tourajghaffari/tigerfid/protel-files/transceiver/trx-rev19/Feb102009 ECO.pdf

### Change Order Report For Project TRX-101R17.PrjPcb And TRX-101R17.PrjPcb

Action | Object | Change Document | Status

Remove Pins From Nets
Remove C54-1 from GND_SIGNAL | In | TestCase1.PcbDoc
Remove C55-1 from GND_SIGNAL | In | TestCase1.PcbDoc
Remove R5-2 from +5V | In | TestCase1.PcbDoc
Remove R28-2 from +5V | In | TestCase1.PcbDoc
Remove R32-1 from GND_SIGNAL | In | TestCase1.PcbDoc
Remove R44-2 from +5V | In | TestCase1.PcbDoc
Remove R45-2 from +5V | In | TestCase1.PcbDoc
Remove U10-1 from GND_SIGNAL | In | TestCase1.PcbDoc
Remove U10-4 from +5V | In | TestCase1.PcbDoc
Remove U10-8 from +5V | In | TestCase1.PcbDoc
Remove U11-2 from GND_SIGNAL | In | TestCase1.PcbDoc
Remove U11-5 from +5V | In | TestCase1.PcbDoc

Remove Nets
Remove NetR5_1 | From TestCase1.PcbDoc
Remove NetU3_4 | From TestCase1.PcbDoc
Remove NetU10_6 | From TestCase1.PcbDoc
Remove NetU11_4 | From TestCase1.PcbDoc

Remove Components
Remove C54 | From TestCase1.PcbDoc
Remove C55 | From TestCase1.PcbDoc
Remove R5 | From TestCase1.PcbDoc
Remove R28 | From TestCase1.PcbDoc
Remove R32 | From TestCase1.PcbDoc
Remove R44 | From TestCase1.PcbDoc
Remove R45 | From TestCase1.PcbDoc
Remove U10 | From TestCase1.PcbDoc
Remove U11 | From TestCase1.PcbDoc

Add Nets
Add | 916_RX_DATA | To TestCase1.PcbDoc

Add Component Classes
Add | PG03_Schematic Sheet1 | To TestCase1.PcbDoc

Add Rooms
Add | Room PG03_Schematic Sheet1 (Scope=I To TestCase1.PcbDoc
| nComponentClass('PG03_Schematic Sheet1')) TopLayer
Tuesday 10-Feb-10/2009 11:07:39 PM | Page 1 of 1
