tourajghaffari/tigerfid/protel-files/master-library/RFID GRAPHICS.jpg

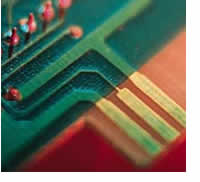
protel-files/master-library/RFID GRAPHICS.jpg
