tourajghaffari/tigerfid/protel-files/master-library/RFID Reader.jpg

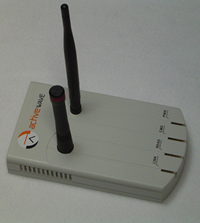
protel-files/master-library/RFID Reader.jpg
