tourajghaffari/tigerfid/software/smart-tracker/Source/Server/bin/Release/Distribute/Layout/Gray Manatee1 North, South, and West Elevation-Model.jpg

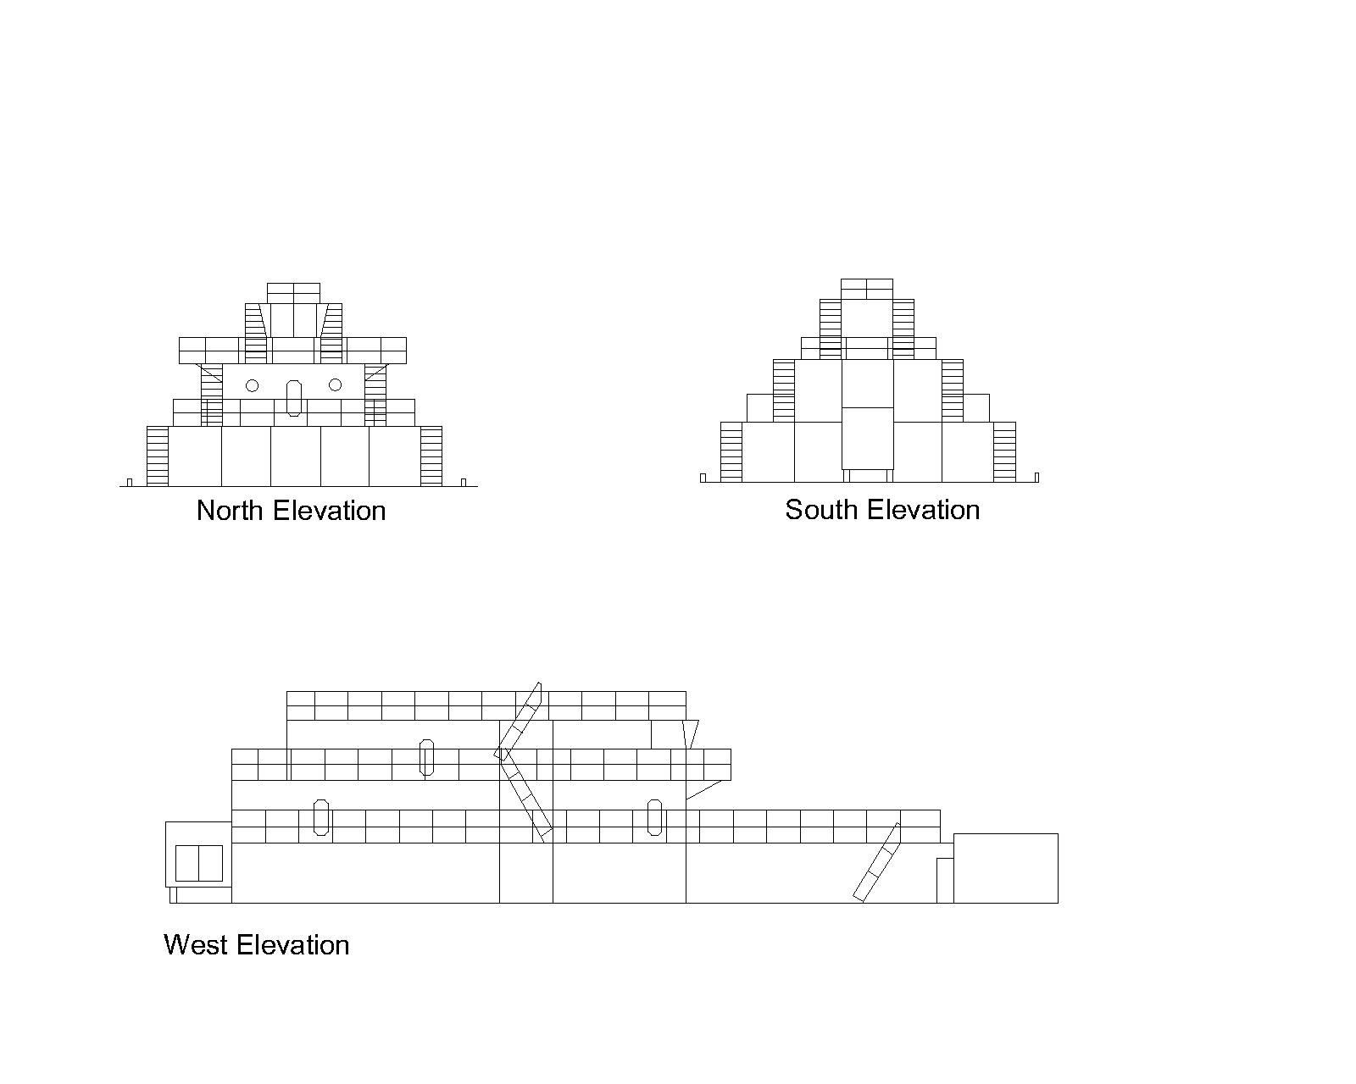
software/smart-tracker/Source/Server/bin/Release/Distribute/Layout/Gray Manatee1 North, South, and West Elevation-Model.jpg
