tourajghaffari/tigerfid/software/smart-tracker/Source/Server/bin/Release/Distribute/Layout/Gray Manatee east elevation-Model.jpg

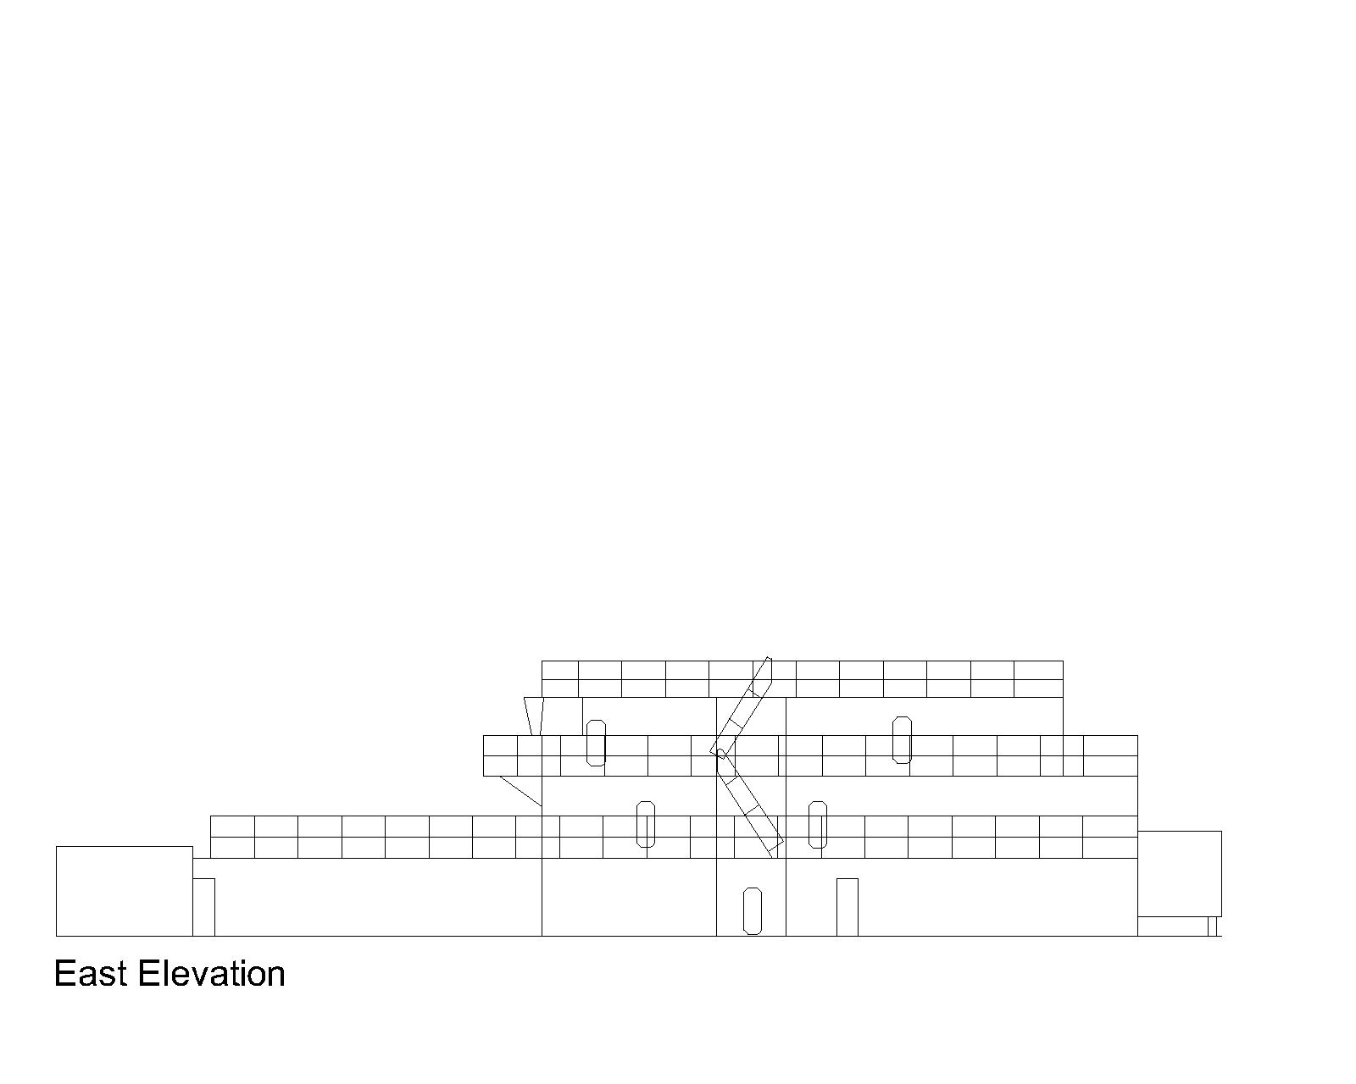
software/smart-tracker/Source/Server/bin/Release/Distribute/Layout/Gray Manatee east elevation-Model.jpg
