tourajghaffari/tigerfid/software/smart-tracker/Source/Server/bin/Release/Distribute/Layout/Gray Manatee ground floor and second-Model.jpg

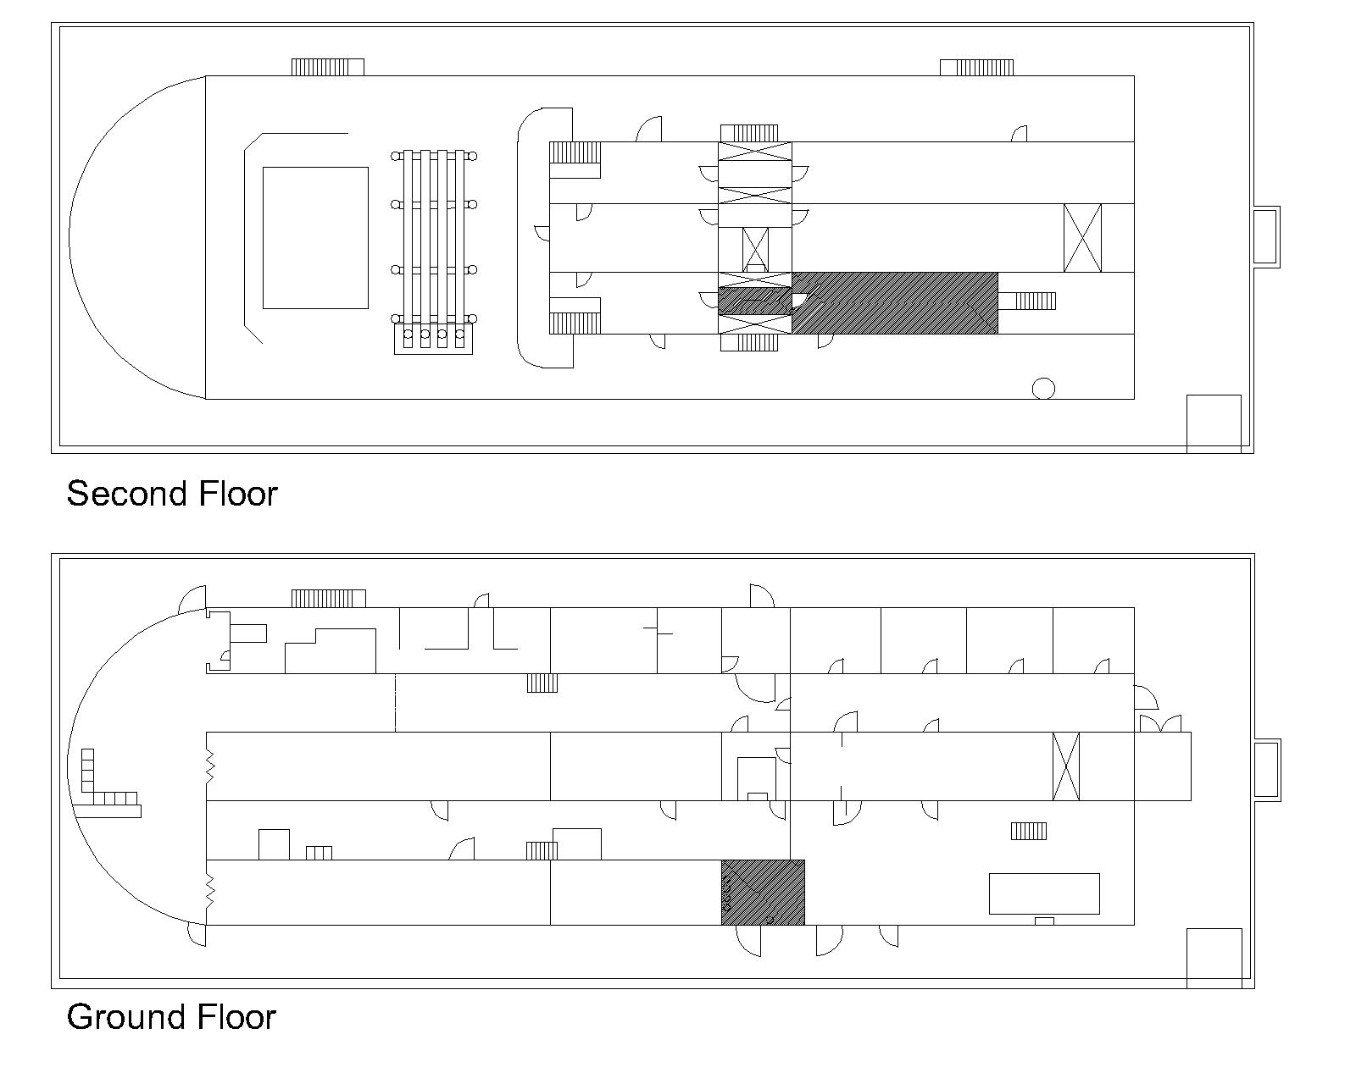
software/smart-tracker/Source/Server/bin/Release/Distribute/Layout/Gray Manatee ground floor and second-Model.jpg
