tourajghaffari/tigerfid/software/smart-tracker/Source/Server/bin/Release/Distribute/Layout/Gray Manatee third floor and roof-Model.jpg

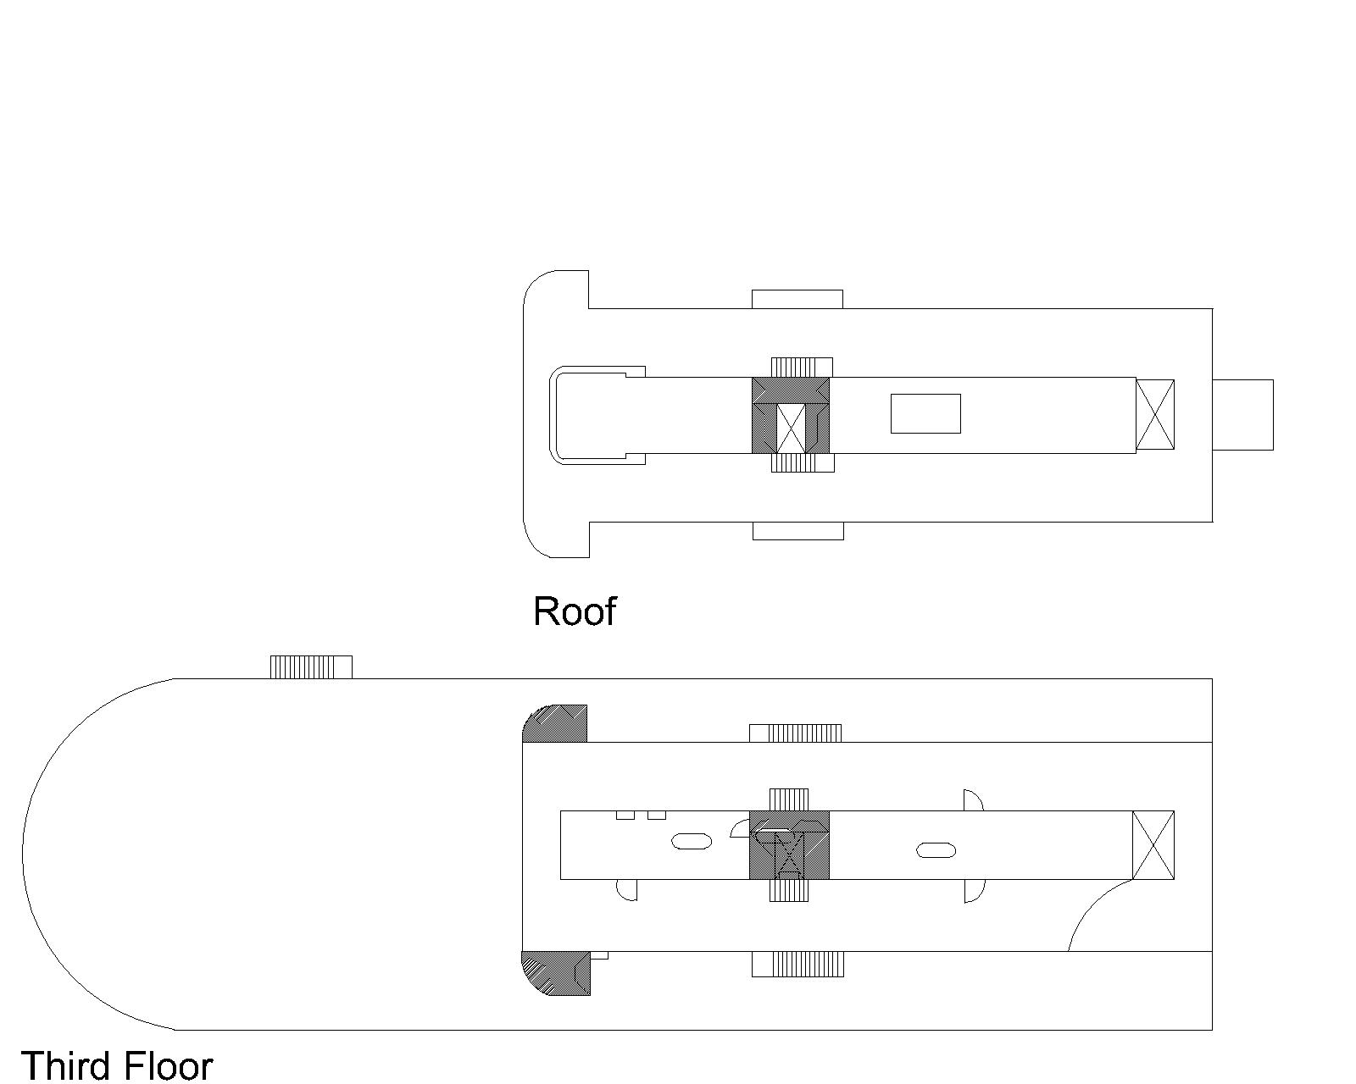
software/smart-tracker/Source/Server/bin/Release/Distribute/Layout/Gray Manatee third floor and roof-Model.jpg
