tourajghaffari/tigerfid/bom-files/bom-cost/TAG104 111705 REV 06A cost.xls

TAG-104
11/17/05 |  | LAST UPDATED |  |  |  |  |  |  |  |  | Mini Tag
 |  |  |  |  |  |  |  |  |  |  | REV 06
Item # | Part Stat | Option No. | Part Reference | Qty. | Unit Price | Extended Cost | Labor Cost | Total Price | Value | Part Size | Description | Manufacturer | Manufacturer P/N | Dist. | Distributor P/N
1 | BASIC |  | C6,C7 | 2 |  |  |  |  | 100 pF | 0603 | CAP 100PF 50V CERAMIC | Panasonic - ECG | ECJ-1VC1H101J | Digi-Key | PCC101ACVTR-ND
2 | BASIC |  | C12,C13 | 2 |  |  |  |  | 33pF +/- 1% | 0603 | CAP 33pF +/- 1% | MURATA | GRM1885C1H330FA01D | TTI/Mouser | GRM1885C1H330FA01D
 |  |  |  |  |  |  |  |  | or |  | CAP 33pF +/- 1% | Kemet | C0603C330F5GACTU | TTI/Mouser | C0603C330F5GACTU
3 | BASIC |  | C8,C9,C10,C11 | 4 |  |  |  |  | 1000 pF | 0603 | CAP 1000PF 50V CERAMIC NP0 | Panasonic - ECG | ECJ-1VC1H102J | Digi-Key | PCC2151TR-ND
4 | BASIC |  | C15,C17,C18,C24 | 4 |  |  |  |  | 0.1 uF | 0603 | CAP .10UF 16V CERAMIC X7R | Phycomp USA Inc (VA) | 06032R104K7B20D | Digi-Key | 311-1088-1-ND
 |  |  |  |  |  |  |  |  |  |  | CAP .10UF 16V CERAMIC X7R | AVX CORP / KYOCERA | 0603YC104KAT2A
 |  |  |  |  |  |  |  |  |  |  | CAP .10UF 16V CERAMIC X7R | TDK CORP | CC0603CX7R104K
 |  |  |  |  |  |  |  |  |  |  | CAP .10UF 16V CERAMIC X7R | MURATA | GRM39X7R104K016AD | Digi-Key | 490-1532-2-ND
 |  |  |  |  |  |  |  |  |  |  | CAP .10UF 16V CERAMIC X7R | NIC COMPONENTS | NMC0603X7R104K16TRM
 |  |  |  |  |  |  |  |  |  |  | CAP .10UF 16V CERAMIC X7R | NIC COMPONENTS | NMC0603X7R104K16TRP
5 | BASIC |  | C22,C23 | 0 |  |  |  |  | DNS
6 | BASIC |  | C20 | 1 |  |  |  |  | 4.7uF | A (EIA) 3216-18 | CAPACITOR TANT 4.7UF 16V 10% | Kemet | T491A475K016AS | Digi-Key | 399-1587-2-ND
7 | BASIC |  | C21 | 1 |  |  |  |  | 2.2pF +/- 0.1pF | 0603 | CAP 2.2pF +/- 0.1pF | MURATA | GRM1885C1H2R2CZ01D | Digi-Key | 490-1380-2-ND
8 | BASIC |  | C3,C25 | 2 |  |  |  |  | 1.8pF +/- 0.1pF | 0603 | CAP 1.8pF +/- 0.1pF | MURATA | GRM1885C1H1R8CZ01D | Digi-Key | 490-1378-2-ND
9 | BASIC |  | L3 | 1 |  |  |  |  | 0.18uH | 0603 | INDUCTOR MULTILAYER 0.18 UH | TDK Corporation | MLF1608DR18K | Digi-Key | 445-1006-1-ND
10 | BASIC |  | L6 | 1 |  |  |  |  | 0.33uH | 0603 | INDUCTOR MULTILAYER 0.33UH 1608 | TDK Corporation | MLF1608DR33K | Digi-Key | 445-1009-2-ND
11 | BASIC |  | L2 | 1 |  |  |  |  | 3.3nH | 0603 | INDUCTOR 3.3NH +/-0.2NH | TDK Corporation | TFL0816-3N3 | Digi-Key | 408-1031-1-ND
12 | BASIC |  | Q1,Q2 | 2 |  |  |  |  | NE85619 | Ultra Super Mini Mold | TRANS NPN 1GHZ SMD | NEC | NE85619TR-ND | Digi-Key | NE85619TR-ND
13 | BASIC |  | Q3 | 1 |  |  |  |  | 2N7002 | SOT-23 | IC TRANS N-CH 60V 7.5OHM | Fairchild | 2N7002NTR-ND | Digi-Key | 2N7002NTR-ND
 |  |  |  |  |  |  |  |  |  |  | IC TRANS N-CH 60V 7.5OHM | ON SEMI (MOTOROLA) | 2N7002LT1
 |  |  |  |  |  |  |  |  |  |  | IC TRANS N-CH 60V 7.5OHM | PHYCOMP/YAGEO/PHILIPS COMPONENTS | 2N7002
 |  |  |  |  |  |  |  |  |  |  | IC TRANS N-CH 60V 7.5OHM | SIEMENS (INFINEON) | 2N7002
 |  |  |  |  |  |  |  |  |  |  | IC TRANS N-CH 60V 7.5OHM | SILICONIX-VISHAY-TEMIC | 2N7002 T&R
14 | BASIC |  | R12,R13 | 2 |  |  |  |  | 10 | 0603 | Carbon Film Resistor 10 OHM 1/16W 5% | Panasonic - SCD | ERJ-3GEYJ100V | Digi-Key | P10GTR-ND
15 | BASIC |  | R6 | 1 |  |  |  |  | 22 ohm | 0603 | RES 22 OHM 1/10W 5% | Rohm | MCR03EZPJ220 | Digi-Key | RHM22GCT-ND
16 | BASIC |  | R7 | 1 |  |  |  |  | 6.8K | 0603 | Carbon Film Resistor 6.8K OHM 1/16W 5% | Panasonic - SCD | ERJ-3GEYJ682V | Digi-Key | 311-6.8KGCT-ND
17 | BASIC |  | R8,R19 | 2 |  |  |  |  | 4.7K | 0603 | Carbon Film Resistor 4.7K OHM 1/16W 5% | Panasonic - SCD | ERJ-3GEYJ472V | Digi-Key | P47KGTR-ND
18 | BASIC |  | R3,R5,R9,R10 | 4 |  |  |  |  | 39K | 0603 | RES 39K OHM 1/10W 5% | Panasonic - SCD | ERJ-3GEYJ393V | Digi-Key | P39KGTR-ND
 |  |  |  |  |  |  |  |  | or |  | RES 39K OHM 1/10W 5% | Yageo America | 9C06031A3902JLHFT | Digi-Key | 311-39KGCT-ND
19 | BASIC |  | R11 | 1 |  |  |  |  | 68 | 0603 | Carbon Film Resistor 68 OHM 1/16W 5% | Panasonic - SCD | ERJ-3GEYJ680V | Digi-Key | P68GTR-ND
20 | BASIC |  | R1,R2, R4 | 3 |  |  |  |  | 1M | 0603 | Carbon Film Resistor 1M OHM 1/16W 5% | Panasonic - SCD | ERJ-3GEYJ105V | Digi-Key | P1MGTR-ND
21 | BASIC |  | R14 | 1 |  |  |  |  | 470 | 0603 | Carbon Film Resistor 470 OHM 1/16W 5% | Panasonic - SCD | ERJ-3GEYJ471V | Digi-Key | P470GTR-ND
 |  |  |  |  |  |  |  |  |  |  | Carbon Film Resistor 470 OHM 1/16W 5% | BOURNS INC | CR0603-JW-471E
 |  |  |  |  |  |  |  |  |  |  | Carbon Film Resistor 470 OHM 1/16W 5% | KOA SPEER | RM73B1JT471J
 |  |  |  |  |  |  |  |  |  |  | Carbon Film Resistor 470 OHM 1/16W 5% | PANASONIC | ERJ-3GSYJ471V | Digi-Key | P470GTR-ND
 |  |  |  |  |  |  |  |  |  |  | Carbon Film Resistor 470 OHM 1/16W 5% | BOURNS INC | CR0603-JX-471-E
22 | BASIC |  | R18 | 1 |  |  |  |  | 2.7K | 0603 | RES 2.7K OHM 1/10W 5% | Rohm | MCR03EZPJ272 | Digi-Key | RHM2.7KGCT-ND
23 | BASIC |  | R17 | 1 |  |  |  |  | 1.8K | 0603 | RES 1.8K OHM 1/10W 5% | Rohm | MCR03EZPJ182 | Digi-Key | RHM1.8KGCT-ND
24 | BASIC |  | R16 | 1 |  |  |  |  | 470K | 0603 | Carbon Film Resistor 470K OHM 1/16W 5% | Panasonic - SCD | ERJ-3GEYJ474V | Digi-Key | P470KGTR-ND
25 | BASIC |  | R20 | 1 |  |  |  |  | 1.0K | 0603 | Carbon Film Resistor 1.0K OHM 1/16W 5% | Panasonic - SCD | ERJ-3GEYJ102V | Digi-Key | P1.0KGTR-ND
26 | BASIC |  | R15 | 1 |  |  |  |  | 330 | 0603 | Carbon Film Resistor 330 OHM 1/16W 5% | Panasonic - SCD | ERJ-3GEYJ331V | Digi-Key | P330GTR-ND
27 | BASIC |  | U1 | 1 | 0.99 |  |  |  | PIC16LF648A | 20SSOP | IC MCU FLASH 4KX14 EEPROM | Microchip | PIC16LF648A-I/SS | Digi-Key | PIC16LF648A-I/SS-ND
28 | BASIC |  | U2 | 1 |  |  |  |  | TC54 | SOT23A | IC VOLT DETECTOR 2.4 V | Microchip | TC54VC2402ECB713
29 | BASIC |  | U5 | 1 | 0.21 |  |  |  | TC1070UCT713 | SOT23A-5 | IC REG LDO ADJ 50MA | Microchip | TC1070VCT713
30 | BASIC |  | U6 | 1 |  |  |  |  | MIC862 | SOT23A-8 | 3MHz Dual Ultra Low Power Op Amp | Micrel | MIC862BM8TR
31 | BASIC |  | B1A | 1 | 0.26 |  |  |  | Battery Holder |  | Battery Retainer | Keystone | C-5510-ACT | Keystone | C-5510-ACT
32 | BASIC |  | B1B | 1 | 0.18 |  |  |  | Battery Contact |  | Battery Contact | Laird Technology | 0097-0488-02
33 | BASIC |  | PCB | 1 | 1 |  |  |  | PCB 104 |  | Mini Tag board | Active Sales
34 | OPT1 |  | Y1 | 1 |  |  |  |  | 916.5 Resonator | 3.8x3.8mm | 916.5 MHz Saw Resonator | RF Monolithics | RO2144D | Richardson | RO2144D
35 | OPT1 |  | C2 | 1 |  |  |  |  | 2 pF | 0603 | CAP 2.0PF 50V CERAMIC | Panasonic - ECG | ECJ-1VC1H020C | Digi-Key | PCC020CVCT-ND
36 | OPT1 |  | C19 | 1 |  |  |  |  | 4.7 pF | 0603 | CAP CERAMIC 4.7PF 50V C0G | Rohm | MCH185A4R7CK | Digi-Key | 511-1102-2-ND
37 | OPT2 |  | Y1 | 1 |  |  |  |  | 868.95 Resonator | 3.8x3.8mm | 868.95 MHz Saw Resonator | RF Monolithics | RO2156D | Richardson | RO2156D
38 | OPT2 |  | C2 | 1 |  |  |  |  | 3.3pF | 0603 | CAP CERAMIC 3.3PF 50V C0G | Rohm | MCH185A3R3CK | Digi-Key | 511-1098-1-ND
39 | OPT2 |  | C19 | 1 |  |  |  |  | 5.6pF | 0603 | CAP CERAMIC 5.6PF 50V C0G | Rohm | MCH185A5R6DK | Digi-Key | 511-1105-1-ND
40 | OPT3 |  | Y1 | 1 |  |  |  |  | 927.2 Resonator | 3.8x3.8mm | 927.2 MHz Saw Resonator | RF Monolithics
41 | OPT3 |  | C2 | 1 |  |  |  |  | 2 pF | 0603 | CAP 2.0PF 50V CERAMIC | Panasonic - ECG | ECJ-1VC1H020C | Digi-Key | PCC020CVCT-ND
42 | OPT3 |  | C19 | 1 |  |  |  |  | 4.7 pF | 0603 | CAP CERAMIC 4.7PF 50V C0G | Rohm | MCH185A4R7CK | Digi-Key | 511-1102-2-ND
43 | OPT D-0 | TAM-0-1 | U7 | 0 |  |  |  |  | No stuff
44 | OPT D-0 | TAM-0-3 | C4 | 0 |  |  |  |  | No stuff
45 | OPT D-0 | TAM-0-4 | C1 | 0 |  |  |  |  | No stuff
46 | OPT E-0 | MEM-0 | U4 | 0 |  |  |  |  | No Memory
47 | OPT E-1 | MEM-1 | U4 | 1 |  |  |  |  | 1K Bit | 8-SOIC
48 | OPT E-2 | MEM-2 | U4 | 1 |  |  |  |  | 2K Bits | 8-SOIC | 256 x 8 1.8V Serial EE | Microchip | 24AA02-I/SN
49 | OPT E-3 | MEM-3 | U4 | 1 |  |  |  |  | 4K Bits | 8-SOIC | 512 x 8 1.8V Serial EE | Microchip | 24AA04-I/SN
50 | OPT E-4 | MEM-4 | U4 | 1 |  |  |  |  | 8K Bits | 8-SOIC
51 | OPT E-5 | MEM-5 | U4 | 1 |  |  |  |  | 16K Bits | 8-SOIC
52 | OPT E-6 | MEM-6 | U4 | 1 |  |  |  |  | 32K Bits | 8-SOIC
53 | OPT E-7 | MEM-7 | U4 | 1 |  |  |  |  | 64K Bits | 8-SOIC
54 | OPT E-8 | MEM-8 | U4 | 1 |  |  |  |  | 128K Bits | 8-SOIC
55 | OPT E-9 | MEM-9 | U4 | 1 |  |  |  |  | 256K Bits | 8-SOIC
56 | OPT F-0 | LED-0 | N/A
57 | OPT F-1 | LED-1 | N/A
58 | OPT G-0 | BUZ-0 | N/A
59 | OPT G-1 | BUZ-1 | N/A
60 | OPT H-0 | TMP-0 | U3 | 0 |  |  |  |  | No IC
61 | OPT H-1 | TMP-1 | U3 | 1 |  |  |  |  | DS1631U | 8MSOP | Temperature Detector IC | Dallas Semiconductor | DS1631U/T&R | Maxim | 90-1631U-TRL
62 | OPT I-0 | BAT-0 | B1 | 0 |  |  |  |  | No Battery
63 | OPT I-1 | BAT-1 | B1 | 1 | 0.13 |  |  |  | Battery |  | BATTERY LITH. | Renata | CR2032FV
64 | OPT J-0 | COL-0 | Enclosure | 0 |  |  |  |  | No enclosure
65 | OPT J-1 | COL-1 | Enclosure | 1 |  |  |  |  | White w/AWI logo
66 | OPT J-2 | COL-2 | Enclosure | 1 |  |  |  |  | Black w/ AWI logo
67 | OPT J-3 | COL-3 | Enclosure | 1 |  |  |  |  | Custom (logo, etc.)
9/9/05 changes:
 | Moved R9 from OPT D to BASIC
11/17/05 changes:
 | Moved C2 and C19 from Basic section to OPT 1/2/3 sections and changed values for 868MHz as follows:
 |  | C19 from 4.7pF to 5.6pF
 |  | C2 from 2pF to 3.3pF
