tourajghaffari/tigerfid/bom-files/bom-cost/TRX-101-101207Rev15 cost.xls

TRX-141-Rev15
10/10/2007 |  |  |  |  |  |  |  | TRX Transceiver
Item # | Part Status | Qty. | AWI price | BF price | Extended cost | BF Labor | Total cost | Part Ref. | Value | Part Size | Description | Supplier | Supplier P/N | Manuf. | Manuf. P/N | Notes
1 | Basic | 1 | 0.011 | 0.005 | 0.006 | 0.080 | 0.086 | C20 | 0.5pF+/-0.1 | 0603 | CAP CER .5PF 50V C0G 0603 | Digi-Key | 490-1370-2-ND | Murata | GRM1885C1HR50CZ01D
2 | Basic | 1 | 0.011 | 0.005 | 0.006 | 0.080 | 0.086 | C33 | 2.0pF +/- 0.25pF | 0603 | CAP CER 2.0PF 50V C0G 0603 | Digi-Key | 490-1379-2-ND | Murata | GRM1885C1H2R0CZ01D
3 | Basic | 2 | 0.011 | 0.005 | 0.011 | 0.160 | 0.171 | C43,C45 | 3.0pF +/- 0.25pF | 0603 | CAP CER 3.0PF 50V C0G 0603 | Digi-Key | 490-1383-2-ND | Murata | GRM1885C1H3R0CZ01D
4 | Basic | 1 | 0.011 | 0.011 | 0.014 | 0.080 | 0.094 | C28 | 4.0pF +/- 0.25pF | 0603 | CAP CER 4.0PF 50V C0G 0603 | Digi-Key | 490-1387-2-ND | Murata | GRM1885C1H4R0CZ01D
5 | Basic | 3 | 0.011 | 0.005 | 0.017 | 0.240 | 0.257 | C3,C9,C31 | 5.0pF +/- 0.25pF | 0603 | CAP CER 5.0PF 50V C0G 0603 | Digi-Key | 490-1390-2-ND | Murata | GRM1885C1H5R0CZ01D
6 | Basic | 1 | 0.011 | 0.005 | 0.006 | 0.080 | 0.086 | C46 | 6.0pF +/- 0.25pF | 0603 | CAP CER 6.0PF 50V C0G 0603 | Digi-Key | 490-1393-2-ND | Murata | GRM1885C1H6R0DZ01D
7 | Basic | 1 | 0.011 | 0.011 | 0.014 | 0.080 | 0.094 | C60 | 6.2pF +/- 0.25pF | 0603 | CAP CER 6.2PF 50V C0G 0603 | Digi-Key | 490-1394-2-ND | Murata | GRM1885C1H6R2DZ01D
8 | Basic | 1 | 0.011 | 0.011 | 0.014 | 0.080 | 0.094 | C35 | 7.0pF +/- 0.50pF | 0603 | CAP CER 7.0PF 50V C0G 0603 | Digi-Key | 490-1397-2-ND | Murata | GRM1885C1H7R0DZ01D
9 | Basic | 1 | 0.011 | 0.003 | 0.004 | 0.080 | 0.084 | C30 | 10.0pF +/- 0.50pF | 0603 | CAP CER 10PF 50V 5% C0G 0603 | Digi-Key | 490-1403-2-ND | Murata | GRM1885C1H100JA01D
10 | Basic | 1 | 0.008 | 0.008 | 0.010 | 0.080 | 0.090 | C1 | 27pF | 0603 | CAP CER 27PF 50V C0G 5% 0603 | Digi-Key | 445-1274-2-ND | TDK Corp | C1608C0G1H270J
11 | Basic | 3 | 0.008 | 0.008 | 0.030 | 0.240 | 0.270 | C11,C19,C42 | 33pF | 0603 | CAP CER 33PF 50V C0G 5% 0603 | Digi-Key | 445-1275-2-ND | TDK Corp | C1608C0G1H330J
12 | Basic | 3 | 0.008 | 0.008 | 0.028 | 0.240 | 0.268 | C29.C37,C40 | 47pF | 0603 | CAP CER 47PF 50V C0G 5% 0603 | Digi-Key | 445-1277-2-ND | TDK Corp | C1608C0G1H470J
13 | Basic | 10 | 0.006 | 0.008 | 0.094 | 0.800 | 0.894 | C6,C21,C27,C32, C34,C36,C38,C39, C44,C47 | 100 pF | 0603 | CAP 100PF 50V CERAMIC | Digi-Key | 445-1281-2-ND | TDK Corp | C1608C0G1H101J
14 | Basic | 3 | 0.008 | 0.004 | 0.014 | 0.240 | 0.254 | C16,C41,C58 | 1000pF | 0603 | CAP 1000PF 50V CERAMIC NP0 | Digi-Key | 399-1083-2-ND | Kemet | C0603C102J5RACTU
15 | Basic | 14 | 0.004 | 0.005 | 0.080 | 1.120 | 1.200 | C2,C4,C5,C7,C8, C13,C14,C17,C18,C22,C26,C48,C50,C51 | 0.1 uF | 0603 | CAP .10UF 16V CERAMIC X7R | Digi-Key | 399-1100-2-ND | Kemet | C0603C104Z3VACTU
16 | Basic | 1 | 0.010 | 0.005 | 0.006 | 0.080 | 0.086 | C15 | .22uF | 0603 | CAP .22UF 16V CERAMIC Y5V 0603 | Digi-Key | 399-1102-2-ND | Kemet | C0603C224Z4VACTU
17 | Basic | 5 | 0.060 | 0.068 | 0.407 | 0.400 | 0.807 | C10,C12,C25,C52,C53 | 10uF TANT | A (EIA) 3216-18 | CAPACITOR TANT 10UF 6.3V 10% SMD | Digi-Key | 399-1551-1-ND | Kemet | T491A106K006AS
18 | Basic | 1 |  |  | 0.000 | 0.080 | 0.080 | TRX-RAW-REV15 | PCB |  |  |  |  | Active PCB | TRX-RAW-REV15
19 | Basic | 1 | 0.009 | 0.001 | 0.001 | 0.080 | 0.081 | R52 | 0 Ohm | 0603 | RES 0.0 OHM 1/20W 5% 0201 SMD | Digikey | RHM0.0AGTR-ND | Rohm | MCR006YZPJ000
20 | Basic | 1 | 0.001 | 0.001 | 0.001 | 0.080 | 0.081 | R16 | 10 | 0603 | Carbon Film Resistor 10 OHM 1/16W 5% | Digi-Key | RHM10GTR-ND | Rohm | MCR03EZPJ100
21 | Basic | 4 | 0.001 | 0.003 | 0.015 | 0.320 | 0.335 | R3,R20,R33,R43 | 22 | 0603 | RES 22 OHM 1/10W 5% 0603 SMD | Digi-Key | RHM22GTR-ND | Rohm | MCR03EZPJ220
22 | Basic | 1 | 0.001 | 0.001 | 0.001 | 0.080 | 0.081 | R1 | 56 | 0603 | RES 56 OHM 1/10W 5% 0603 SMD | Digi-Key | RHM56GTR-ND | Rohm | MCR03EZPJ560
23 | Basic | 2 | 0.001 | 0.001 | 0.003 | 0.160 | 0.163 | R30,R39 | 68 | 0603 | Carbon Film Resistor 68 OHM 1/16W 5% | Digi-Key | RHM68GTR-ND | Rohm | MCR03EZPJ680
24 | Basic | 1 | 0.001 | 0.001 | 0.001 | 0.080 | 0.081 | R29 | 180 | 0603 | RES 180 OHM 1/10W 5% 0603 SMD | Digikey | RHM180GTR-ND | Rohm | MCR03EZPJ181
25 | Basic | 1 | 0.001 | 0.001 | 0.001 | 0.080 | 0.081 | R2 | 330 | 0603 | RES 330 OHM 1/10W 5% 0603 SMD | Digikey | RHM330GTR-ND | Rohm | MCR03EZPJ331
26 | Basic | 2 | 0.001 | 0.001 | 0.003 | 0.160 | 0.163 | R4,R24 | 470 | 0603 | RES 470 OHM 1/10W 5% 0603 SMD | Digikey | RHM470GTR-ND | Rohm | MCR03EZPJ471
27 | Basic | 1 | 0.001 | 0.001 | 0.001 | 0.080 | 0.081 | R27 | 560 | 0603 | RES 560 OHM 1/10W 5% 0603 SMD | Digikey | RHM560GTR-ND | Rohm | MCR03EZPJ561
 | Basic | 1 | 0.001 | 0.001 | 0.001 | 0.080 | 0.081 | R7 | 820 | 0603 | RES 820 OHM 1/10W 5% 0603 SMD | Digikey | RHM1.1KGTR-ND | Rohm
28 | Basic | 5 | 0.001 | 0.001 | 0.007 | 0.400 | 0.407 | R8,R18,R26,R37, R48 | 1K | 0603 | RES 1.0K OHM 1/10W 5% 0603 SMD | Digikey | RHM1.0KGTR-ND | Rohm | MCR03EZPJ102
29 | Basic | 2 | 0.001 | 0.001 | 0.003 | 0.160 | 0.163 | R21,R46 | 2.2K | 0603 | RES 2.2K OHM 1/10W 5% 0603 SMD | Digi-Key | RHM2.2KGTR-ND | Rohm | MCR03EZPJ222
30 | Basic | 1 | 0.001 | 0.001 | 0.001 | 0.080 | 0.081 | R25 | 3.3K | 0603 | RES 3.3K OHM 1/10W 5% 0603 SMD | Digi-Key | RHM3.3KGTR-ND | Rohm | MCR03EZPJ332
31 | Basic | 7 | 0.001 | 0.001 | 0.009 | 0.560 | 0.569 | R14,R19,R22,R35,R40,R42,R51 | 4.7K | 0603 | RES 4.7K OHM 1/10W 5% 0603 SMD | Digi-Key | RHM4.7KGTR-ND | Rohm | MCR03EZPJ472
32 | Basic | 1 | 0.108 | 0.108 | 0.129 | 0.080 | 0.209 | R11 | 5K POT | 3mm | POT 5K OHM 3MM CARBON TRIM SMD | Digi-Key | P5E502CT-ND | Panasonic-ECG | EVN-5ESX50B53
33 | Basic | 3 | 0.001 | 0.001 | 0.004 | 0.240 | 0.244 | R13,R23,R34 | 6.8K | 0603 | RES 6.8K OHM 1/10W 5% 0603 SMD | Digi-Key | RHM6.8KGTR-ND | Rohm | MCR03EZPJ682
34 | Basic | 5 | 0.001 | 0.001 | 0.007 | 0.400 | 0.407 | R6,R12,R38,R41,R49 | 10K | 0603 | RES 10K OHM 1/10W 5% 0603 SMD | Digikey | RHM10KGTR-ND | Rohm | MCR03EZPJ103
35 | Basic | 1 | 0.001 | 0.001 | 0.001 | 0.080 | 0.081 | R47 | 15K | 0603 | RES 15K OHM 1/10W 5% 0603 SMD | Digikey | RHM15KGTR-ND | Rohm | MCR03EZPJ153
36 | Basic | 2 | 0.001 | 0.001 | 0.003 | 0.160 | 0.163 | R15,R36 | 39K | 0603 | RES 39K OHM 1/10W 5% 0603 SMD | Digikey | RHM39KGTR-ND | Rohm | MCR03EZPJ393
37 | Basic | 1 | 0.001 | 0.001 | 0.001 | 0.080 | 0.081 | R50 | 56K | 0603 | RES 56K OHM 1/10W 5% 0603 SMD | Digikey | RHM56KGTR-ND | Rohm | MCR03EZPJ563
38 | Basic | 2 | 0.001 | 0.001 | 0.003 | 0.160 | 0.163 | R10,R31 | 100K | 0603 | RES 100K OHM 1/10W 5% 0603 SMD | Digikey | RHM100KGTR-ND | Rohm | MCR03EZPJ104
39 | Basic | 1 | 0.001 | 0.001 | 0.001 | 0.080 | 0.081 | R9 | 150K | 0603 | RES 150K OHM 1/10W 5% 0603 SMD | Digikey | RHM150KGTR-ND | Rohm | MCR03EZPJ154
40 | Basic | 1 | 0.001 | 0.001 | 0.001 | 0.080 | 0.081 | R17 | 220K | 0603 | RES 220K OHM 1/10W 5% 0603 SMD | Digikey | RHM220KGTR-ND | Rohm | MCR03EZPJ224
41 | Basic | 1 | 0.001 | 0.001 | 0.001 | 0.080 | 0.081 | R53 | 270K | 0603 | RES 270K OHM 1/10W 5% 0603 SMD | Digi-Key | RHM270KGCT-ND | Rohm | MCR03EZPJ274
42 | Basic | 4 | 0.087 | 0.087 | 0.417 | 0.320 | 0.737 | FB1,FB2,FB3,FB4 | Ferrite Beads | 0603 | BEAD CORE 27 OHM 4A 0603 SMD | Digi-Key | P10436CT-ND | Panasonic-ECG | EXC-ML16A270U
43 | Basic | 2 | 0.034 | 0.040 | 0.096 | 0.160 | 0.256 | L1,L17 | 4.7nH | 0603 | INDUCTOR 4.7NH 5% FIXED SMD | Digi-Key | PCD1969TR-ND | Panasonic-ECG | ELJ-RE4N7JFA
44 | Basic | 2 | 0.034 | 0.034 | 0.081 | 0.160 | 0.241 | L9,L15 | 6.8nH | 0603 | INDUCTOR 6.8NH 5% 0603 SMD | Digi-Key | PCD1971TR-ND | Panasonic-ECG | ELJ-RE6N8JFA
45 | Basic | 1 | 0.034 | 0.034 | 0.041 | 0.080 | 0.121 | L2 | 18nH | 0603 | INDUCTOR 18NH 5% 0603 SMD | Digi-Key | PCD1976TR-ND | Panasonic-ECG | ELJ-RE18NJFA
46 | Basic | 1 | 0.034 | 0.034 | 0.041 | 0.080 | 0.121 | L12 | 22nH | 0603 | INDUCTOR 22NH 5% 0603 SMD | Digi-Key | PCD1977TR-ND | Panasonic-ECG | ELJ-RE22NJFA
47 | Basic |  |  |  | 0.000 | 0.000 | 0.000
48 | Basic | 1 | 0.034 | 0.034 | 0.041 | 0.080 | 0.121 | L10 | 47nH | 0603 | INDUCTOR 47NH 5% 0603 SMD | Digi-Key | PCD1981TR-ND | Panasonic-ECG | ELJ-RE47NJFA | TBD
49 | Basic | 2 | 0.034 | 0.034 | 0.081 | 0.160 | 0.241 | L8,L11 | 100nH | 0603 | INDUCTOR 100NH 5% 0603 SMD | Digi-Key | PCD1985TR-ND | Panasonic-ECG | ELJ-RER10JFA | TBD
50 | Basic | 1 | 0.034 | 0.034 | 0.041 | 0.080 | 0.121 | L7 | 330nH | 0805 | INDUCTOR MULTILAYER 0.33UH 2012 | Digi-Key | 445-1041-2-ND | TDK | MLF2012DR33K
51 | Basic | 1 | 0.102 | 0.119 | 0.143 | 0.080 | 0.223 | L14 | 0.18uH | 0603 | INDUCTOR MULTILAYER 0.18 UH | Digi-Key | 445-1006-1-ND | TDK Corporation | MLF1608DR18K | TBD
52 | Basic | 1 | 0.102 | 0.102 | 0.122 | 0.080 | 0.202 | L3 | 6.8uH | 0805 | INDUCTOR MULTILAYER 6.8UH 1608 | Digi-Key | 445-1023-2-ND | TDK | MLF1608E6R8K
53 | Basic | 1 | 0.519 | 0.119 | 0.143 | 0.080 | 0.223 | L4 | 2.2mH | 3.5mm x 3.5mm x 2.2mm | INDUCTOR FIXED 2.2mH TYPE D32FU | Digi-Key | #887FU-222M=P3-ND | Toko America | #887FU-222M=P3
54 | Basic | 2 | 0.045 | 0.009 | 0.021 | 0.160 | 0.181 | D1,D2 | SWITCHING DIODE 75V 350MW | SOT-23 | DIODE SWITCH 75V 350MW SOT-23 | Digi-Key | MMBD914DITR-ND | Diodes, Inc. | MMBD914-7
55 | Basic | 1 | 0.077 | 0.150 | 0.180 | 0.080 | 0.260 | D3 | Bar65-02V | SC79 | DIODE RF SGL 30V 100MA SC-79 |  | BAR 65-02V E6327-ND | Infineon | BAR 65-02V E6327
56 | Basic | 2 | 0.270 | 0.270 | 0.647 | 0.160 | 0.807 | Q1,Q6 | TRANS NPN 1GHZ | Ultra Super Mini Mold | TRANSISTOR NPN 1GHZ SMD | Digi-Key | NE85619-ATR-ND | NEC | NE85619-T1-A
57 | Basic | 2 | 0.045 | 0.045 | 0.108 | 0.160 | 0.268 | Q2,Q11 | TRANS GP PNP -40V -200MA | SOT-23 | TRANS GP PNP -40V -200MA SOT-23 | Digi-Key | FMMT3906TR-ND | Zetex, Inc. | FMMT3906TA
58 | Basic | 4 | 0.045 | 0.009 | 0.041 | 0.320 | 0.361 | Q3,Q7,Q8,Q10 | TRANS GP NPN 40V 200MA | SOT-23 | TRANS GP NPN 40V 200MA SOT-23 | Digi-Key | FMMT3904TR-ND | Zetex, Inc. | FMMT3904TA
59 | Basic | 2 | 0.126 | 0.126 | 0.301 | 0.160 | 0.461 | Q4,Q5 | HF TRANS | SOT23 | TRANSISTOR RF NPN 12V SOT-23 | Digi-Key | BFR 193 E6327-ND | Infineon | BFR 193 E6327
60 | Basic | 1 | 0.287 | 0.287 | 0.344 | 0.080 | 0.424 | U1 | AMPLIFIER | SOT343R | MMIC AMPLIFIER SOT-343R | Arrow | 568-2062-2-ND | NXP | BGA2001 T/R
61 | Basic | 1 | 2.688 | 2.130 | 2.551 | 0.080 | 2.631 | U2 | RF RECEIVER | SSOP20 | IC MIXER FM IF SYSTM RSSI 20SSOP | Arrow | 568-1105-2-ND | NXP | SA636DK-T
62 | Basic | 1 | 0.325 | 0.325 | 0.389 | 0.080 | 0.469 | U3 | COMPARATOR | SOT23-5 | IC DIFF COMPARATOR SOT-23-5 | Digi-Key | 296-10492-2-ND | TI | TLV1391CDBVR
63 |  |  | 0.325 |  | 0.000 | 0.000 | 0.000 |  | or | SOT23-5 | IC DIFF COMPARATOR SOT-23-5 | Arrow | TLV1391CDBVR | TI | TLV1391CDBVR
64 | Basic | 2 | 0.468 | 0.468 | 1.121 | 0.160 | 1.281 | U4,U8 | OPAMP | SOT23-5 | IC OPAMP R-R LOW V LP SOT23-5 | Digi-Key | LMV821M5TR-ND | National Semi. | LMV821M5
65 | Basic | 1 | 1.596 | 1.765 | 2.114 | 0.080 | 2.194 | U5 | DIGITAL POT | 8-µSOP | IC POT TRIMMER NV 10K 8-USOP | Digi-Key | DS1804U-010+T&R-ND | Dallas Semi. | DS1804U-010+T&R
66 | Basic | 1 |  | 0.940 | 1.126 | 0.080 | 1.206 | U6 | AT-113 | SO8 |  | FAI Elec. | 6219539 | MCM | AT-113TR
67 | Basic | 1 |  |  | 0.000 | 0.080 | 0.080 | U7 | MMIC Switch SPDT | SOT-26 | MMIC SWITCH SPDT 2.5GHZ SOT-26 | Digi-Key | UPG152TACT-ND | NEC | UPG152TA-E3
68 | Basic | 1 | 0.346 | 0.346 | 0.414 | 0.080 | 0.494 | U9 | 555 TIMER | 8-MSOP | IC TIMER 8-MSOP | Digi-Key | LM555CMMTR-ND | National Semi. | LM555CMM/NOPB
69 | Basic | 2 | 0.442 | 0.442 | 1.059 | 0.160 | 1.219 | Y1,Y2 | 10.7MHz | Filter | FILTER 10.7MHZ 330KHZ BANDWIDTH | Digi-Key | 490-1228-2-ND | Murata | SFECS10M7EA00-R0
70 | Basic | 1 | 0.736 | 0.736 | 0.881 | 0.080 | 0.961 | Y4 | 433.92MHz | Resonator |  | Avnet | R02101D-T/R or RO2101E-T/R | RF Monolithics | Ro2101D or RO2101E
71 | Basic | 1 | 0.755 | 0.755 | 0.904 | 0.080 | 0.984 | J2 | 10-PIN HEADER | .100 SINGL STR | CONN HEADER .100 SINGL STR 36POS | Digi-Key | S1011-36-ND | Sullins Elec. | PZC36SAAN | One of these parts will make 3+ headers
72 | Basic | 1 | 2.087 | 2.087 | 2.500 | 0.080 | 2.580 | PCB1 | PCB |  |  |  | TRX-141 Rev. 15 | Active PCB | TRX-141 Rev. 14
 | TOTAL |  |  |  | 16.906 | 11.600 | 28.506
73
74 | OPT1 | 1 | 0.680 | 0.680 | 0.814 | 0.080 | 0.894 | Y5 | 916.5MHz | Filter |  | Avnet | RF1181D-ENG | RF Monolithics | RF1181D
75 | OPT1 | 1 | 0.680 | 0.690 | 0.826 | 0.080 | 0.906 | Y6 | 916.5MHz | Resonator |  | Avnet | RO2144D-T/R | RF Monolithics | RO2144D
76 | OPT1 | 1 | 0.680 | 0.680 | 0.814 | 0.080 | 0.894 | Y3 | 905.8MHz | Resonator |  | Avnet |  | RF Monolithics
77 | OPT1 | 0 | 0.011 | 0.011 | 0.000 | 0.000 | 0.000 | C23 | 4.0pF +/- 0.25pF | 0603 | CAP CER 4.0PF 50V C0G 0603 | Digi-Key | 490-1387-2-ND | Murata | GRM1885C1H4R0CZ01D
78 | OPT1 | 1 | 0.011 | 0.004 | 0.005 | 0.080 | 0.085 | C59 | 15pF | 0603 | CAP CER 15PF 50V 5% C0G 0603 | Digi-Key | 490-1403-2-ND | Murata
79 | OPT1 | 1 | 0.040 | 0.040 | 0.048 | 0.080 | 0.128 | L16 | 3.3nH | 0603 | INDUCTOR 3.3NH 5% FIXED SMD | Digi-Key | PCD1969TR-ND | Panasonic-ECG |  | TBD
80 | TOTAL |  |  |  | 19.414 | 12.000 | 31.414
81 | OPT2 | 1 | 0.680 | 0.680 | 0.814 | 0.080 | 0.894 | Y5 | 868.95MHz | Filter |  | Avnet | RF1319D | RF Monolithics | RF1319D
82 | OPT2 | 1 | 0.630 | 0.630 | 0.754 | 0.080 | 0.834 | Y6 | 868.95MHz | Resonator |  | Avnet | RO2156D | RF Monolithics | RO2156D
83 | OPT2 | 1 | 0.680 | 0.680 | 0.814 | 0.080 | 0.894 | Y3 | 858.25MHz | Resonator |  | Avnet | RO2165D | RF Monolithics | RO2165D
84 | OPT2 | 1 | 0.011 | 0.011 | 0.014 | 0.080 | 0.094 | C23 | 4.0pF +/- 0.25pF | 0603 | CAP CER 4.0PF 50V C0G 0603 | Digi-Key | 490-1387-2-ND | Murata | GRM1885C1H4R0CZ01D
85 | OPT2 | 1 | 0.011 | 0.004 | 0.005 | 0.080 | 0.085 | C59 | 10pF | 0603 | CAP 100PF 50V CERAMIC | Digi-Key | 445-1281-2-ND | TDK Corp | C1608C0G1H101J
86 | OPT2 | 1 | 0.040 | 0.040 | 0.048 | 0.080 | 0.128 | L16 | 4.7nH | 0603 | INDUCTOR 3.9NH 5% 0603 SMD | Digi-Key | PCD1968TR-ND | Panasonic-ECG | ELJ-RE3N9JFA | TBD
87 | TOTAL |  |  |  | 19.355 | 12.080 | 31.435
88 | OPT3 | 1 | 0.680 | 0.680 | 0.680 | 0.080 | 0.760 | Y5 | 927.2MHz | Filter |  | Yoketan | SM3838F092721R2NJ | Yoketan | SM3838F092721R2NJ
89 | OPT3 | 1 | 0.680 | 0.680 | 0.680 | 0.080 | 0.760 | Y6 | 927.2MHz | Resonator
90 | OPT3 | 1 | 0.680 | 0.690 | 0.690 | 0.080 | 0.770 | Y3 | 916.5MHz | Resonator |  | Avnet | RO2144D-T/R | RF Monolithics | RO2144D
91 | OPT3 | 1 | 0.011 | 0.011 | 0.011 | 0.080 | 0.091 | C23 | 2.2 pf | 0603 | CAP CER 2.2PF 50V C0G 0603 | Digi-Key | 490-1380-2-ND | Murata | CAP CER 2.2PF 50V C0G 0603
92 | OPT3 | 1 | 0.011 | 0.004 | 0.004 | 0.080 | 0.084 | C59 | 100 pF | 0603 | CAP 100PF 50V CERAMIC | Digi-Key | 445-1281-2-ND | TDK Corp | C1608C0G1H101J
93 | OPT3 | 1 | 0.040 | 0.040 | 0.040 | 0.080 | 0.120 | L16 | 39nH | 0603 | INDUCTOR 39NH 5% 0603 SMD | Digi-Key | PCD1968TR-ND | Panasonic-ECG | ELJ-RE3N9JFA | TBD
 | TOTAL |  |  |  | 19.011 | 12.080 | 31.091
94 | OPT4-0 | 0 | 2.087 |  | 0.000 | 0.000 | 0.000 | J3,J4 | CONNECTOR ??? | PCB Mount | CONNECTOR RPSMA PCB MOUNT | Digi-Key | CONREVSMA001-ND | Linx Tech. | CONREVSMA001 | Install onto component side of PCB
95 | OPT4-1 | 2 | 2.087 | 2.087 | 4.175 | 0.160 | 4.335 | J3,J4 | CONNECTOR ??? | PCB Mount | CONNECTOR RPSMA PCB MOUNT | Digi-Key | CONREVSMA001-ND | Linx Tech. | CONREVSMA001 | Install onto component side of PCB
 | TOTAL |  |  |  | 21.081 | 11.760 | 32.841
96 | Basic | 0 |  |  | 0.000 | 0.000 |  | C54,C55,,C56,C57,R5,R28, R32,R44,R45,L6,U10,U11 | DMP
