tourajghaffari/tigerfid/bom-files/compact-flash/Compact Flash- Ver2 6 12042010.xls

CFCARD
11/24/2010
 |  |  | Compact Flash Ver. 2.6
Item # | Part Stat. | Qty. | Part Ref. | Value | Part Size | Description | Dist. | Distributor P/N | Manufacturer | Manufacturer P/N | Notes | Revision
1 | Basic | 1 | C20 | 0.5pF+/-0.1 | 0603 | CAP CER .5PF 50V C0G 0603 | Digi-Key | 490-1370-2-ND | Murata | GRM1885C1HR50CZ01D | BF | 2.0
2 | Basic | 2 | C33,C45 | 2.0pF +/- 0.25pF | 0603 | CAP CER 2.0PF 50V C0G 0603 | Digi-Key | 490-1379-2-ND | Murata | GRM1885C1H2R0CZ01D | BF | 2.6
3 | Basic | 1 | C43 | 3.0pF +/- 0.25pF | 0603 | CAP CER 3.0PF 50V C0G 0603 | Digi-Key | 490-1383-2-ND | Murata | GRM1885C1H3R0CZ01D | BF | 2.0
4 | Basic | 2 | C30,C56 | 4.0pF +/- 0.25pF | 0603 | CAP CER 4.0PF 50V C0G 0603 | Digi-Key | 490-1387-2-ND | Murata | GRM1885C1H4R0CZ01D | BF | 2.6
5 | Basic | 3 | C3,C9,C31 | 5.0pF +/- 0.25pF | 0603 | CAP CER 5.0PF 50V C0G 0603 | Digi-Key | 490-1390-2-ND | Murata | GRM1885C1H5R0CZ01D | BF | 2.0
6 | Basic | 1 | C28 | 6.0pF +/- 0.25pF | 0603 | CAP CER 6.0PF 50V C0G 0603 | Digi-Key | 490-1393-2-ND | Murata | GRM1885C1H6R0DZ01D | BF | 2.6
7 | Basic | 1 | C60 | 6.2pF +/- 0.25pF | 0603 | CAP CER 6.2PF 50V C0G 0603 | Digi-Key | 490-1394-2-ND | Murata | GRM1885C1H6R2DZ01D | BF | 2.0
8 | Basic | 1 | C35 | 7.0pF +/- 0.50pF | 0603 | CAP CER 7.0PF 50V C0G 0603 | Digi-Key | 490-1397-2-ND | Murata | GRM1885C1H7R0DZ01D | BF | 2.0
9 | Basic | 1 | C46 | 8.0pF +/- 0.05pF | 0603 | CAP CER 7.0PF 50V C0G 0603 | Digi-Key | 490-1399-2-ND | Murata | GRM1885C1H7R0DZ01D |  | 2.6
9 | Basic | 1 | C1 | 27pF | 0603 | CAP CER 27PF 50V C0G 5% 0603 | Digi-Key | 445-1274-2-ND | TDK Corp | C1608C0G1H270J | BF | 2.0
10 | Basic | 5 | C11,C19,C42,CL301,Cl302 | 33pF | 0603 | CAP CER 33PF 50V C0G 5% 0603 | Digi-Key | 445-1275-2-ND | TDK Corp | C1608C0G1H330J | BF | 2.0
11 | Basic | 10 | C29,C37,C40, C110-C116 | 47pF | 0603 | CAP CER 47PF 50V C0G 5% 0603 | Digi-Key | 445-1277-2-ND | TDK Corp | C1608C0G1H470J | BF | 2.0
12 | Basic | 11 | C6,C21,C27,C32, C34,C36,C38,C39,C44,C47,C121 | 100 pF | 0603 | CAP 100PF 50V CERAMIC | Digi-Key | 445-1281-2-ND | TDK Corp | C1608C0G1H101J | BF | 2.0
13 | Basic | 3 | C16,C41,C58 | 1000pF | 0603 | CAP 1000PF 50V CERAMIC NP0 | Digi-Key | 399-1083-2-ND | Kemet | C0603C102J5RACTU | BF | 2.0
14 | Basic | 23 | C2,C4,C5,C7,C8, C13,C14,C17,C18,C22,C26,C48,C50,C51,C101,C102, C107,C109,C301-C305 | 0.1 uF | 0603 | CAP .10UF 16V CERAMIC X7R | Digi-Key | 399-1100-2-ND | Kemet | C0603C104Z3VACTU | BF | 2.0
15 | Basic | 1 | C15 | .22uF | 0603 | CAP .22UF 16V CERAMIC Y5V 0603 | Digi-Key | 399-1102-2-ND | Kemet | C0603C224Z4VACTU | BF | 2.0
16 | Basic | 1 | C124 | 4.7uF | Cap A case | CAPACITOR TANT 4.7UF 16V 10% SMD | Digi-Key | 399-3697-2-ND | Kemet | T491A475K016AT | BF | 2.0
17 | Basic | 6 | C10,C12,C52,C53,C125,C25 | 10uF TANT | A (EIA) 3216-18 | CAPACITOR TANT 10UF 6.3V 10% SMD | Digi-Key | 399-1551-1-ND | Kemet | T491A106K006AS | BF | 2.0
18 | Basic | 1 | R52 | 0 Ohm | 0603 | RES 0.0 OHM 1/20W 5% 0201 SMD | Digikey | RHM0.0AGTR-ND | Rohm | MCR006YZPJ000 | BF | 2.0
19 | Basic | 3 | R16,R30,R122,R123 | 10 | 0603 | Carbon Film Resistor 10 OHM 1/16W 5% | Digi-Key | RHM10GTR-ND | Rohm | MCR03EZPJ100 | BF | 2.6
20 | Basic | 4 | R3,R20,R33,R43 | 22 | 0603 | RES 22 OHM 1/10W 5% | Digi-Key | RHM22GTR-ND | Rohm | MCR03EZPJ220 | BF | 2.0
21 | Basic | 1 | R1 | 56 | 0603 | RES 56 OHM 1/10W 5% 0603 SMD | Digi-Key | RHM56GTR-ND | Rohm | MCR03EZPJ560 | BF | 2.0
22 | Basic | 1 | R39 | 68 | 0603 | Carbon Film Resistor 68 OHM 1/16W 5% | Digi-Key | RHM68GTR-ND | Rohm | MCR03EZPJ680 | BF | 2.0
23 | Basic | 5 | R113-R117 | 100 | 0603 | RES 100 OHM 1/10W 5% 0603 SMD | Digi-Key | RHM100GTR-ND | Rohm | MCR03EZPJ101 | BF | 2.0
24 | Basic | 1 | R118 | 120 | 0603 | RES 120 OHM 1/10W 5% 0603 SMD | Digikey | RHM120GTR-ND | Rohm | MCR03EZPJ121 | BF | 2.0
25 | Basic | 1 | R126 | 150 | 0603 | RES 150 OHM 1/10W 5% 0603 SMD | Digikey | RHM150GTR-ND | Rohm | MCR03EZPJ151 | BF | 2.0
26 | Basic | 2 | R29,R119 | 180 | 0603 | RES 180 OHM 1/10W 5% 0603 SMD | Digikey | RHM180GTR-ND | Rohm | MCR03EZPJ181 | BF | 2.0
27 | Basic | 1 | R301 | 220 | 0603 | RES 220 OHM 1/10W 5% 0603 SMD | Digikey | RHM220GTR-ND | Rohm | MCR03EZPJ221 | BF | 2.4 | Change the quantity
28 | Basic | 2 | R2,R111 | 330 | 0603 | RES 330 OHM 1/10W 5% 0603 SMD | Digikey | RHM330GTR-ND | Rohm | MCR03EZPJ331 | BF | 2.0
29 | Basic | 1 | R4 | 470 | 0603 | RES 470 OHM 1/10W 5% 0603 SMD | Digikey | RHM470GTR-ND | Rohm | MCR03EZPJ471 | BF | 2.0
30 | Basic | 1 | R27 | 51 | 0603 | RES 51 OHM 1/10W 5% 0603 SMD | Digikey | RHM51GTR-ND | Rohm | MCR03EZPJ510 | BF | 2.6
31 | Basic | 5 | R8,R18,R26,R37, R48 | 1K | 0603 | RES 1.0K OHM 1/10W 5% 0603 SMD | Digikey | RHM1.0KGTR-ND | Rohm | MCR03EZPJ102 | BF | 2.0
32 | Basic | 2 | R21,R46 | 2.2K | 0603 | RES 2.2K OHM 1/10W 5% 0603 SMD | Digi-Key | RHM2.2KGTR-ND | Rohm | MCR03EZPJ222 | BF | 2.0
 | Basic | 1 | R24 | 2.7K | 0603 | RES 2.7K OHM 1/10W 5% 0603 SMD | Digi-Key | RHM2.7KGTR-ND | Rohm | MCR03EZPJ272 | BF | 2.6
33 | Basic | 1 | R25 | 3.3K | 0603 | RES 3.3K OHM 1/10W 5% 0603 SMD | Digi-Key | RHM3.3KGTR-ND | Rohm | MCR03EZPJ332 | BF | 2.0
34 | Basic | 5 | R13,R23,R34,R120R121 | 6.8K | 0603 | RES 6.8K OHM 1/10W 5% 0603 SMD | Digikey | RHM6.8KGTR-ND | Rohm | MCR03EZPJ682 | BF | 2.0
35 | Basic | 7 | R14,R19,R22,R35,R40,R42,R51 | 4.7K | 0603 | RES 4.7K OHM 1/10W 5% 0603 SMD | Digi-Key | RHM4.7KGTR-ND | Rohm | MCR03EZPJ472 | BF | 2.0
36 | Basic | 1 | R11 | 5K POT | 3mm Sq. SMD |  | Digi-Key | P5E502CT-ND | Panasonic | EVN-5ESX50B53 | BF | 2.0
37 | Basic | 16 | R6,R12,R38,R41,R49,R101-R110 ,R132 | 10K | 0603 | RES 10K OHM 1/10W 5% 0603 SMD | Digikey | RHM10KGTR-ND | Rohm | MCR03EZPJ103 | BF | 2.0
38 | Basic | 1 | R131 | 13.3K 1% | 0603 | RES 13.3K OHM 1/10W 1% 0603 SMD | Digi-Key | RHM13.3KHTR-ND | Rohm | MCR03EZPFX1332 | BF | 2.0
39 | Basic | 1 | R47 | 15K | 0603 | RES 15K OHM 1/10W 5% 0603 SMD | Digikey | RHM15KGTR-ND | Rohm | MCR03EZPJ153 | BF | 2.0
40 | Basic | 2 | R15,R36 | 39K | 0603 | RES 39K OHM 1/10W 5% 0603 SMD | Digikey | RHM39KGTR-ND | Rohm | MCR03EZPJ393 | BF | 2.0
41 | Basic | 1 | R130 | 40.2K | 0603 | RES 40.2K OHM 1/10W 1% 0603 SMD | Digi-Key | RHM40.2KHTR-ND | Rohm | MCR03EZPFX4022 | BF | 2.0
42 | Basic | 1 | R50 | 56K | 0603 | RES 56K OHM 1/10W 5% 0603 SMD | Digikey | RHM56KGTR-ND | Rohm | MCR03EZPJ563 | BF | 2.0
43 | Basic | 6 | R10,R31,R303-R306 | 100K | 0603 | RES 100K OHM 1/10W 5% 0603 SMD | Digikey | RHM100KGTR-ND | Rohm | MCR03EZPJ104 | BF | 2.0
44 | Basic | 1 | R9 | 150K | 0603 | RES 150K OHM 1/10W 5% 0603 SMD | Digikey | RHM150KGTR-ND | Rohm | MCR03EZPJ154 | BF | 2.0
45 | Basic | 1 | R17 | 220K | 0603 | RES 220K OHM 1/10W 5% 0603 SMD | Digikey | RHM220KGTR-ND | Rohm | MCR03EZPJ224 | BF | 2.0
46 | Basic | 1 | R53 | 270K | 0603 | RES 270K OHM 1/10W 5% 0603 SMD | Digi-Key | RHM270KGCT-ND | Rohm | MCR03EZPJ274 | BF | 2.0
47 | Basic | 1 | R302 | 1.0M | 0603 | RES 1.0M OHM 1/10W 5% 0603 SMD | Digi-Key | RHM1.0MGTR-ND | Rohm | MCR03EZPJ105 | BF | 2.0
48 | Basic | 6 | FB1-FB5,FB101 | Ferrite Beads | 0603 | BEAD CORE 27 OHM 4A 0603 SMD | Digi-Key | P10436CT-ND | Panasonic-ECG | EXC-ML16A270U | BF | 2.0
49 | Basic | 2 | L1,L17 | 4.7nH | 0603 | INDUCTOR 4.7NH 5% FIXED SMD | Digi-Key | PCD1969TR-ND | Panasonic-ECG | ELJ-RE4N7JFA | BF | 2.0
 | Basic | 3 | L9,L15,L19 | 6.8nH | 0603 | INDUCTOR 6.8NH 5% 0603 SMD | Digi-Key | PCD1971TR-ND | Panasonic-ECG | ELJ-RE6N8JFA | BF | 2.6 | L9 = 6.2 Nh is better
50 | Basic | 2 | L9,L15 | 6.8nH | 0603 | INDUCTOR 6.8NH 5% 0603 SMD | Digi-Key | PCD1971TR-ND | Panasonic-ECG | ELJ-RE6N8JFA | BF | 2.0
51 | Basic | 1 | L2 | 18nH | 0603 | INDUCTOR 18NH 5% 0603 SMD | Digi-Key | PCD1976TR-ND | Panasonic-ECG | ELJ-RE18NJFA | BF | 2.0
52 | Basic | 1 | L12 | 22nH | 0603 | INDUCTOR 22NH 5% 0603 SMD | Digi-Key | PCD1977TR-ND | Panasonic-ECG | ELJ-RE22NJFA | BF | 2.0
53 | Basic | 1 | L10 | 47nH | 0603 | INDUCTOR 47NH 5% 0603 SMD | Digi-Key | PCD1981TR-ND | Panasonic-ECG | ELJ-RE47NJFA | BF | 2.3
54 | Basic | 2 | L8,L11 | 100nH | 0603 | INDUCTOR 100NH 5% 0603 SMD | Digi-Key | PCD1985TR-ND | Panasonic-ECG | ELJ-RER10JFA | BF | 2.4
55 | Basic | 1 | L7 | 330nH | 0805 | INDUCTOR MULTILAYER 0.33UH 2012 | Digi-Key | 445-1041-2-ND | TDK | MLF2012DR33K | BF | 2.0
56 | Basic | 1 | L14 | 0.18uH | 0603 | INDUCTOR MULTILAYER 0.18 UH | Digi-Key | 445-1006-1-ND | TDK Corporation | MLF1608DR18K | BF | 2.0
57 | Basic | 1 | L3 | 6.8uH | 0805 | INDUCTOR MULTILAYER 6.8UH 1608 | Digi-Key | 445-1023-2-ND | TDK | MLF1608E6R8K | BF | 2.0
58 | Basic | 1 | L102 | 2.2uH |  |  | CoilCraft | DO1606T-222 | CoilCraft | DO1606T-222 | BF | 2.0
58 | Basic | 1 | L4 | 2.2mH | 3.5mm x 3.5mm x 2.2mm | INDUCTOR FIXED 2.2mH TYPE D32FU | Digi-Key | #887FU-222M=P3-ND | Toko America | #887FU-222M=P3 | BF | 2.0
59 | Basic | 2 | D1,D2 | SWITCHING DIODE 75V 350MW | SOT-23 | DIODE SWITCH 75V 350MW SOT-23 | Digi-Key | MMBD914DITR-ND | Diodes, Inc. | MMBD914-7 | BF | 2.3
60 | Basic | 1 | D3 | Bar65-02V | SC79 | DIODE RF SGL 30V 100MA SC-79 |  | BAR 65-02V E6327-ND | Infineon | BAR 65-02V E6327 | BF | 2.0
61 | Basic | 1 | D101 | RLED | LED-0603 |  | Digikey | P11511CT-ND | Panasonic-SSG | LNJ216C8ARA | BF | 2.0
62 | Basic | 1 | D102 | YLED | LED-0603 |  | Digikey | P11514CT-ND | Panasonic-SSG | LNJ416Q8YRA | BF | 2.0
63 | Basic | 1 | D103 | GLED | LED-0603 |  | Digikey | P11515CT-ND | Panasonic-SSG | LNJ316C8TRA | BF | 2.0
64 | Basic | 1 | D105 | MBR0520 | SOD123 |  | Digi-Key | MBR0520LCT-ND | Fairchild Semi | MBR0520L | BF | 2.0
65 | Basic | 2 | Q1,Q6 | TRANS NPN 1GHZ | Ultra Super Mini Mold | TRANSISTOR NPN 1GHZ SMD | Digi-Key | NE85619-ATR-ND | NEC | NE85619-T1-A | BF | 2.0
66 | Basic | 2 | Q2,Q11 | TRANS GP PNP -40V -200MA | SOT-23 | TRANS GP PNP -40V -200MA SOT-23 | Digi-Key | FMMT3906TR-ND | Zetex, Inc. | FMMT3906TA | BF | 2.0
67 | Basic | 6 | Q3,Q7,Q8,Q10, Q101,Q102 | TRANS GP NPN 40V 200MA | SOT-23 | TRANS GP NPN 40V 200MA SOT-23 | Digi-Key | FMMT3904TR-ND | Zetex, Inc. | FMMT3904TA | BF | 2.0
68 | Basic | 2 | Q4,Q5 | HF TRANS | SOT23 | TRANSISTOR RF NPN 12V SOT-23 | Digi-Key | BFR 193 E6327-ND | Infineon | BFR 193 E6327 | BF | 2.0
69 | Basic | 1 | U1 | AMPLIFIER | SOT343R | MMIC AMPLIFIER SOT-343R | Arrow | 568-2062-2-ND | NXP | BGA2001 T/R | BF | 2.0
70 | Basic | 1 | U2 | RF RECEIVER | SSOP20 | IC MIXER FM IF SYSTM RSSI 20SSOP | Arrow | 568-1105-2-ND | NXP | SA636DK-T | BF | 2.0
71 | Basic | 1 | U3 | COMPARATOR | SOT23-5 | IC DIFF COMPARATOR SOT-23-5 | Digi-Key | 296-10492-2-ND | TI | TLV1391CDBVR | BF | 2.0
72 |  |  |  | or | SOT23-5 | IC DIFF COMPARATOR SOT-23-5 | Arrow | TLV1391CDBVR | TI | TLV1391CDBVR | BF | 2.0
73 | Basic | 2 | U4,U8 | OPAMP | SOT23-5 | IC OPAMP R-R LOW V LP SOT23-5 | Digi-Key | LMV821M5TR-ND | National Semi. | LMV821M5 | BF | 2.0
74 | Basic | 1 | U5 | DIGITAL POT | 8-µSOP | IC POT TRIMMER NV 10K 8-USOP | Digi-Key | DS1804U-010+T&R-ND | Dallas Semi. | DS1804U-010+T&R | BF | 2.0
75 | Basic | 1 | U6 | AT-113 | SO8 |  | FAI Elec. | 6219539 | MCM | AT-113TR | BF | 2.0
76 | Basic | 1 | U7 | MMIC Switch SPDT | SOT-26 | MMIC SWITCH SPDT 2.5GHZ SOT-26 | Digi-Key | UPG152TACT-ND | NEC | UPG152TA-E3 | BF | 2.0
77 | Basic | 1 | U9 | 555 TIMER | 8-MSOP | IC TIMER 8-MSOP | Digi-Key | LM555CMMTR-ND | National Semi. | LM555CMM/NOPB | BF | 2.0
78 |  |  |  | or | 8-MSOP |  | Arrow | LMC555CM | National Semi. | LM555CMM | BF | 2.0
79 | Basic | 2 | U101,U103 | PIC16F870 | SSOP-28 | IC MCU FLASH 2KX14 EE 28SSOP | Digikey | PIC16F870-I/SS | Microchip | PIC16F870-I/SS | BF | 2.0
80 | Basic | 1 | U102 | PIC16F876A | SSOP-28 | IC MCU FLASH 8KX14 EE 28SSOP | Digikey | PIC16F876A-I/SS | Microchip | PIC16F876A-I/SS | BF | 2.0
81 | Basic | 1 | U106 | 16.0 MHz | CRY-SMD-5-7 | OSCILLATOR 16MHZ HCMOS SMD | Digi-key | CW304-ND | Connor-Winfield | HSM93-16.0000 | BF | 2.0
82 | Basic | 1 | U107 | LT1930 | SOT23-5A | IC DC/DC CONV STEP-UP SOT23-5 | Digikey | LT1930AES5#TRMPBFCT-ND | Linear Tech. | LT1930AES5#TRMPBF | BF | 2.0
83 | Basic | 1 | U301 | VPU16551 | CBGA64 |  |  |  | Elan Digital Systems, Ltd |  | AWI | 2.2 | Ron Mazza
84 | Basic | 2 | Y1,Y2 | 10.7MHz | Filter | FILTER 10.7MHZ 330KHZ BANDWIDTH | Digi-Key | 490-1228-2-ND | Murata | SFECS10M7EA00-R0 | BF | 2.0 | VP North America
85 | Basic | 1 | Y301 | 14.7456MHz | Crystals | CRYSTAL 14.7456 MHZ 18PF SMD | Digi-Key | 300-8094-1-ND | Citizen America Co | CS10 14.7456MABJ-UT | BF | 2.0 | Elan Digital Systems, Ltd.
86 | Basic | 1 | Y4 | 433.92MHz | Resonator |  | Avnet | R02101D-T/R or RO2101E-T/R | RF Monolithics | Ro2101D or RO2101E | AWI | 2.0 | 2033 Bruceala Court
87 | Basic | 2 | J3,J4 | MMCX MINI COAX |  |  |  |  | Nearson | NC-K01-2 | AWI | 2.2 | Cardiff by the Sea, CA 92007 USA
88 | Basic | 1 | J111 | 25 pin Edge Connector |  |  |  |  | Samtec | CFS-125-01-l-d | http://www.samtec.com/documents/webfiles/pdf/CFS.PDF | 2.0 | Tel: 760-633-1811
89 |  |  |  |  |  |  |  |  |  |  |  | 2.0 | Fax: 760-406-4068
90 | OPT1 | 1 | Y5 | 916.5MHz | Filter |  | Avnet | RF1181D-ENG | RF Monolithics | RF1181D | AWI | 2.0
91 | OPT1 | 1 | Y6 | 916.5MHz | Resonator |  | Avnet | RO2144D-T/R | RF Monolithics | RO2144D | AWI | 2.0
92 | OPT1 | 1 | Y3 | 905.8MHz | Resonator |  | Avnet | RO2216D-6 | RF Monolithics | RO2216D-6 | AWI | 2.1
93 | OPT1 | 0 | C23 | DMP |  |  |  |  |  |  |  | 2.0
94 | OPT1 | 1 | C59 | 15pF | 0603 | CAP CER 15PF 50V 5% C0G 0603 | Digi-Key | 490-1403-2-ND | Murata |  | BF | 2.0
95 | OPT1 | 1 | R7 | 1.1K | 0603 | RES 1.1K OHM 1/10W 5% 0603 SMD | Digi-Key | RHM1.1KGTR-ND | Rohm | MCR03EZPJ111 | BF | 2.0
96 | OPT1 | 1 | L16 | 3.3nH | 0603 | INDUCTOR 3.3NH +-.2NH FIXED SMD | Digi-Key | PCD1288TR-ND | Panasonic-ECG | ELJ-RE3N3ZF2 | BF | 2.6
 |  |  |  |  |  |  |  |  |  |  | BF | 2.0
97 | OPT2 | 1 | Y5 | 868.95MHz | Filter |  | Avnet | RF1319D | RF Monolithics | RF1319D | AWI | 2.0
98 | OPT2 | 1 | Y6 | 868.95MHz | Resonator |  | Avnet | RO2156D | RF Monolithics | RO2156D | AWI | 2.0
99 | OPT2 | 1 | Y3 | 858.25MHz | Resonator |  | Avnet | RO2165D | RF Monolithics | RO2165D | AWI | 2.0
100 | OPT2 | 1 | C23 | 4.0pF +/- 0.25pF | 0603 | CAP CER 4.0PF 50V C0G 0603 | Digi-Key | 490-1387-2-ND | Murata | GRM1885C1H4R0CZ01D | BF | 2.0
101 | OPT2 | 1 | C59 | 10pF | 0603 | CAP CER 10PF 50V C0G 0603 | Digi-Key | 445-1269-2-ND | TDK Corp | C1608C0G1H100D | BF | 2.3
102 | OPT2 | 1 | R7 | 560 | 0603 | RES 560 OHM 1/10W 5% 0603 SMD | Digikey | RHM560GTR-ND | Rohm | MCR03EZPJ561 | BF | 2.0
103 | OPT2 | 1 | L16 | 3.3nH | 0603 | INDUCTOR 3.3NH +-.2NH FIXED SMD | Digi-Key | PCD1288TR-ND | Panasonic-ECG | ELJ-RE3N3ZF2 | BF | 2.1
104 |  |  |  |  |  |  |  |  |  |  | BF | 2.0
105 | OPT3 | 1 | Y5 | 927.2MHz | Filter |  | Yoketan | SM3838F092721R2NJ | Yoketan | SM3838F092721R2NJ | BF | 2.0
106 | OPT3 | 1 | Y6 | 927.2 Resonator | 3.8x3.8mm | 927.2 MHz Saw Resonator |  |  | SUNNY ELECTRONICS | SR-00927 | BF | 2.1
107 | OPT3 | 1 | Y3 | 916.5MHz | Resonator |  | Avnet | RO2144D-T/R | RF Monolithics | RO2144D | AWI | 2.0
108 | OPT3 | 1 | R7 | 820 | 0603 | RES 820 OHM 1/10W 5% 0603 SMD | Digikey | RHM820GTR-ND | Rohm | MCR03EZPJ821 | BF | 2.0
109 | OPT3 | 1 | C23 | 2.2 pf | 0603 | CAP CER 2.2PF 50V C0G 0603 | Digi-Key | 490-1380-2-ND | Murata | CAP CER 2.2PF 50V C0G 0603 | BF | 2.0
110 | OPT3 | 1 | C59 | 100 pF | 0603 | CAP 100PF 50V CERAMIC | Digi-Key | 445-1281-2-ND | TDK Corp | C1608C0G1H101J | BF | 2.0
111 | OPT3 | 1 | L16 | 39nH | 0603 | INDUCTOR 39NH 5% 0603 SMD | Digi-Key | PCD1980TR-ND | Panasonic-ECG | ELJ-RE39NJFA | BF | 2.0
112 | Basic | 0 | C54,C55,C56,C57,C103-C106,C108,R5,R28,R32,R45,R44,R204,L6,L18,U10,U11,U104, J101,J102,J103,J105,J107.TP101-TP125 | DMP |  |  |  |  |  |  | BF | 2.2
114 | Basic | 2 |  | Amphenol SMA Reverse Polarity Connectors |  |  | Mouswer | 523-132220RP | Amphenol | 132220RP |  | 2.5
