tourajghaffari/tigerfid/bom-files/handheld/handheld Rev01-NAV-TV-10202012.xlsx

Sheet: Sheet1
SmallHandheldRev1
10/20/2012 |  |  | Small Handheld Rev 1
Item # | Part Status | Qty. | Part Ref. | Value | Part Size | 0.05 | Description | Supplier | Supplier P/N | Manuf. | Manuf. P/N | Notes | revision
1 | Basic | 1 | C9 | 0.5pF+/-0.1 | 0603 | 0.05 | CAP CER .5PF 50V C0G 0603 | Digi-Key | 490-1370-2-ND | Murata | GRM1885C1HR50CZ01D |  | 18.3
2 | Basic | 1 | C43 | 3.0pF +/- 0.25pF | 0603 | 0.05 | CAP CER 3.0PF 50V C0G 0603 | Digi-Key | 490-1383-2-ND | Murata | GRM1885C1H3R0CZ01D |  | 18.6
3 | Basic | 1 | C56 | 4.7pF +/- 0.25pF | 0603 | 0.05 | CAP CER 4.7PF 50V C0G 0603 | Digi-Key | 490-1389-2-ND | Murata | GRM1885C1H4R7CZ01D |  | 18.6
4 | Basic | 3 | C3,C20,C31 | 5.0pF +/- 0.25pF | 0603 | 0.15 | CAP CER 5.0PF 50V C0G 0603 | Digi-Key | 490-1390-2-ND | Murata | GRM1885C1H5R0CZ01D |  | 18.3
5 | Basic | 1 | C60 | 6.2pF +/- 0.25pF | 0603 | 0.05 | CAP CER 6.2PF 50V C0G 0603 | Digi-Key | 490-1394-2-ND | Murata | GRM1885C1H6R2DZ01D |  | 18.3
6 | Basic | 1 | C46 | 8.0pF +/- 0.05pF | 0603 | 0.05 | CAP CER 7.0PF 50V C0G 0603 | Digi-Key | 490-1399-2-ND | Murata | GRM1885C1H7R0DZ01D |  | 18.6
7 | Basic | 1 | C1 | 27pF | 0603 | 0.05 | CAP CER 27PF 50V C0G 5% 0603 | Digi-Key | 445-1274-2-ND | TDK Corp | C1608C0G1H270J |  | 18.3
8 | Basic | 2 | C11,C42 | 33pF | 0603 | 0.1 | CAP CER 33PF 50V C0G 5% 0603 | Digi-Key | 445-1275-2-ND | TDK Corp | C1608C0G1H330J |  | 18.3
9 | Basic | 1 | C19 | 22pF | 0603 | 0.05 | CAP CER 33PF 50V C0G 5% 0603 | Digi-Key | 445-1273-2-ND | TDK Corp | C1608C0G1H220J
10 | Basic | 3 | C29.C37,C40 | 47pF | 0603 | 0.15 | CAP CER 47PF 50V C0G 5% 0603 | Digi-Key | 445-1277-2-ND | TDK Corp | C1608C0G1H470J |  | 18.3
11 | Basic | 10 | C6,C21,C27,C32, C34,C36,C38,C39, C44,C47 | 100 pF | 0603 | 0.5 | CAP 100PF 50V CERAMIC | Digi-Key | 445-1281-2-ND | TDK Corp | C1608C0G1H101J |  | 18.3
12 | Basic | 3 | C16,C41,C58 | 1000pF | 0603 | 0.15 | CAP 1000PF 50V CERAMIC NP0 | Digi-Key | 399-1083-2-ND | Kemet | C0603C102J5RACTU |  | 18.3
13 | Basic | 15 | C2,C4,C5,C7,C8, C13,C14,C17,C18,C22,C26,C48,C50,C51,C54 | 0.1 uF | 0603 | 0.75 | CAP .10UF 16V CERAMIC X7R | Digi-Key | 399-1100-2-ND | Kemet | C0603C104Z3VACTU |  | 18.3
14 | Basic | 1 | C15 | .22uF | 0603 | 0.05 | CAP .22UF 16V CERAMIC Y5V 0603 | Digi-Key | 399-1102-2-ND | Kemet | C0603C224Z4VACTU |  | 18.3
15 | Basic | 5 | C10,C12,C25,C52,C53 | 10uF TANT | A (EIA) 3216-18 | 0.25 | CAPACITOR TANT 10UF 6.3V 10% SMD | Digi-Key | 399-1551-1-ND | Kemet | T491A106K006AS |  | 18.3
16 | Basic | 2 | R16,R30 | 10 | 0603 | 0.1 | Carbon Film Resistor 10 OHM 1/16W 5% | Digi-Key | RHM10GTR-ND | Rohm | MCR03EZPJ100 |  | 18.3
17 | Basic | 4 | R3,R20,R33,R43 | 22 | 0603 | 0.2 | RES 22 OHM 1/10W 5% 0603 SMD | Digi-Key | RHM22GTR-ND | Rohm | MCR03EZPJ220 |  | 18.3
18 | Basic | 1 | R56 | 51 | 0603 | 0.05 | RES 51 OHM 1/10W 5% 0603 SMD | Digi-Key | RHM51GTR-ND | Rohm | MCR03EZPJ500 |  | 18.6
19 | Basic | 1 | R1 | 56 | 0603 | 0.05 | RES 56 OHM 1/10W 5% 0603 SMD | Digi-Key | RHM56GTR-ND | Rohm | MCR03EZPJ560 |  | 18.3
20 | Basic | 1 | R39 | 68 | 0603 | 0.05 | Carbon Film Resistor 68 OHM 1/16W 5% | Digi-Key | RHM68GTR-ND | Rohm | MCR03EZPJ680 |  | 18.3
21 | Basic | 1 | R29 | 180 | 0603 | 0.05 | RES 180 OHM 1/10W 5% 0603 SMD | Digikey | RHM180GTR-ND | Rohm | MCR03EZPJ181 |  | 18.3
22 | Basic | 2 | R2,R32 | 330 | 0603 | 0.1 | RES 330 OHM 1/10W 5% 0603 SMD | Digikey | RHM330GTR-ND | Rohm | MCR03EZPJ331 |  | 18.3
23 | Basic | 1 | R27 | 560 | 0603 | 0.05 | RES560 OHM 1/10W 5% 0603 SMD | Digikey | RHM560GTR-ND | Rohm | MCR03EZPJ561
24 | Basic | 1 | R4 | 470 | 0603 | 0.05 | RES 470 OHM 1/10W 5% 0603 SMD | Digikey | RHM470GTR-ND | Rohm | MCR03EZPJ471 |  | 18.3
25 | Basic | 6 | R8,R18,R26,R37,R48,R55 | 1K | 0603 | 0.3 | RES 1.0K OHM 1/10W 5% 0603 SMD | Digikey | RHM1.0KGTR-ND | Rohm | MCR03EZPJ102 |  | 18.3
26 | Basic | 2 | R21,R46 | 2.2K | 0603 | 0.1 | RES 2.2K OHM 1/10W 5% 0603 SMD | Digi-Key | RHM2.2KGTR-ND | Rohm | MCR03EZPJ222 |  | 18.3
27 | Basic | 1 | R24 | 2.7K | 0603 | 0.05 | RES 2.7K OHM 1/10W 5% 0603 SMD | Digi-Key | RHM2.7KGTR-ND | Rohm | MCR03EZPJ272 |  | 18.6
28 | Basic | 2 | R5,R25 | 3.3K | 0603 | 0.1 | RES 3.3K OHM 1/10W 5% 0603 SMD | Digi-Key | RHM3.3KGTR-ND | Rohm | MCR03EZPJ332 |  | 18.3
29 | Basic | 7 | R14,R19,R22,R35,R40,R42,R51 | 4.7K | 0603 | 0.35 | RES 4.7K OHM 1/10W 5% 0603 SMD | Digi-Key | RHM4.7KGTR-ND | Rohm | MCR03EZPJ472 |  | 18.3
30 | Basic | 2 | R11,R52 | 5K POT | 3mm | 0.1 | POT 5K OHM 3MM CARBON TRIM SMD | Digi-Key | P5E502CT-ND | Panasonic-ECG | EVN-5ESX50B53 |  | 18.3
31 | Basic | 1 | R28 | 5.6K | 0603 | 0.05 | RES 5.6K OHM 1/10W 5% 0603 SMD | Digi-Key | RHM5.67KGTR-ND | Rohm | MCR03EZPJ562 |  | 18.3
32 | Basic | 3 | R13,R23,R34 | 6.8K | 0603 | 0.15 | RES 6.8K OHM 1/10W 5% 0603 SMD | Digi-Key | RHM6.8KGTR-ND | Rohm | MCR03EZPJ682 |  | 18.3
33 | Basic | 6 | R6,R12,R38,R41,R49,R53 | 10K | 0603 | 0.3 | RES 10K OHM 1/10W 5% 0603 SMD | Digikey | RHM10KGTR-ND | Rohm | MCR03EZPJ103 |  | 18.3
34 | Basic | 1 | R47 | 15K | 0603 | 0.05 | RES 15K OHM 1/10W 5% 0603 SMD | Digikey | RHM15KGTR-ND | Rohm | MCR03EZPJ153 |  | 18.3
35 | Basic | 2 | R15,R36 | 39K | 0603 | 0.1 | RES 39K OHM 1/10W 5% 0603 SMD | Digikey | RHM39KGTR-ND | Rohm | MCR03EZPJ393 |  | 18.3
36 | Basic | 1 | R50 | 56K | 0603 | 0.05 | RES 56K OHM 1/10W 5% 0603 SMD | Digikey | RHM56KGTR-ND | Rohm | MCR03EZPJ563 |  | 18.3
37 | Basic | 2 | R10,R31 | 100K | 0603 | 0.1 | RES 100K OHM 1/10W 5% 0603 SMD | Digikey | RHM100KGTR-ND | Rohm | MCR03EZPJ104 |  | 18.3
38 | Basic | 1 | R9 | 150K | 0603 | 0.05 | RES 150K OHM 1/10W 5% 0603 SMD | Digikey | RHM150KGTR-ND | Rohm | MCR03EZPJ154 |  | 18.3
39 | Basic | 1 | R17 | 220K | 0603 | 0.05 | RES 220K OHM 1/10W 5% 0603 SMD | Digikey | RHM220KGTR-ND | Rohm | MCR03EZPJ224 |  | 18.3
40 | Basic | 3 | FB1,FB2,FB3 | Ferrite Beads | 0603 | 0.15 | BEAD CORE 27 OHM 4A 0603 SMD | Digi-Key | P10436CT-ND | Panasonic-ECG | EXC-ML16A270U |  | 18.3
41 | Basic | 2 | L1,L17 | 4.7nH | 0603 | 0.1 | INDUCTOR 4.7NH 5% FIXED SMD | Digi-Key | PCD1969TR-ND | Panasonic-ECG | ELJ-RE4N7JFA |  | 18.3
42 | Basic | 1 | L19 | 5.6 nH | 0603 | 0.05 | INDUCTOR 5.68NH 5% 0603 SMD | Digi-Key | PCD1970TR-ND | Panasonic-ECG | ELJ-RE5N6JFA |  | 18.6
43 | Basic | 2 | L5, L15 | 6.8nH | 0603 | 0.1 | INDUCTOR 6.8NH 5% 0603 SMD | Digi-Key | PCD1971TR-ND | Panasonic-ECG | ELJ-RE6N8JFA |  | 18.3
44 | Basic | 1 | L2 | 8.2nH | 0603 | 0.05 | INDUCTOR MULTILAYER 8.2NH 0603 | Digi-Key | 445-1491-2-ND | TDK Corporation | MLG1608B8N2D |  | 18.3
45 | Basic | 0 | L13 | 18nH | 0603 | 0 | INDUCTOR 18NH 5% 0603 SMD | Digi-Key | PCD1976TR-ND | Panasonic-ECG | ELJ-RE18NJFA |  | 18.3
46 | Basic | 1 | L10 | 47nH | 0603 | 0.05 | INDUCTOR 47NH 5% 0603 SMD | Digi-Key | PCD1981TR-ND | Panasonic-ECG | ELJ-RE47NJFA |  | 18.3
47 | Basic | 2 | L8,L11 | 100nH | 0603 | 0.1 | INDUCTOR 100NH 5% 0603 SMD | Digi-Key | PCD1985TR-ND | Panasonic-ECG | ELJ-RER10JFA |  | 18.3
48 | Basic | 1 | L14 | 0.18uH | 0603 | 0.05 | INDUCTOR MULTILAYER 0.18 UH | Digi-Key | 445-1006-1-ND | TDK Corporation | MLF1608DR18K |  | 18.3
49 | Basic | 1 | L3 | 6.8uH | 0805 | 0.05 | INDUCTOR MULTILAYER 6.8UH 1608 | Digi-Key | 445-1023-2-ND | TDK | MLF1608E6R8K |  | 18.3
50 | Basic | 1 | L4 | 2.2mH | 3.5mm x 3.5mm x 2.2mm | 0.05 | INDUCTOR FIXED 2.2mH TYPE D32FU | Digi-Key | #887FU-222M=P3-ND | Toko America | #887FU-222M=P3 |  | 18.3
51 | Basic | 2 | D1,D2 | SWITCHING DIODE 75V 350MW | SOT-23 | 0.1 | DIODE SWITCH 75V 350MW SOT-23 | Digi-Key | MMBD914DITR-ND | Diodes, Inc. | MMBD914-7 |  | 18.3
52 | Basic | 1 | D3 | Bar65-02V | SC79 | 0.05 | DIODE RF SGL 30V 100MA SC-79 |  | BAR 65-02V E6327-ND | Infineon | BAR 65-02V E6327 |  | 18.3
53 | Basic | 1 | D4 | RLED | LED-0603 | 0.05 |  | Digikey | P11511CT-ND | Panasonic-SSG | LNJ216C8ARA | BF | 2.0
54 | Basic | 2 | Q1,Q6 | TRANS NPN 1GHZ | Ultra Super Mini Mold | 0.1 | TRANSISTOR NPN 1GHZ SMD | Digi-Key | NE85619-ATR-ND | NEC | NE85619-T1-A |  | 18.3
55 | Basic | 2 | Q2,Q11 | TRANS GP PNP -40V -200MA | SOT-23 | 0.1 | TRANS GP PNP -40V -200MA SOT-23 | Digi-Key | FMMT3906TR-ND | Zetex, Inc. | FMMT3906TA |  | 18.3
56 | Basic | 4 | Q3,Q7,Q8,Q10 | TRANS GP NPN 40V 200MA | SOT-23 | 0.2 | TRANS GP NPN 40V 200MA SOT-23 | Digi-Key | FMMT3904TR-ND | Zetex, Inc. | FMMT3904TA |  | 18.3
57 | Basic | 2 | Q4,Q5 | HF TRANS | SOT23 | 0.1 | TRANSISTOR RF NPN 12V SOT-23 | Digi-Key | BFR 193 E6327-ND | Infineon | BFR 193 E6327 |  | 18.3
58 | Basic | 1 | U1 | AMPLIFIER | SOT343R | 0.05 | MMIC AMPLIFIER SOT-343R | Arrow | 568-2062-2-ND | NXP | BGA2001 T/R |  | 18.3
59 | Basic | 1 | U2 | RF RECEIVER | SSOP20 | 0.05 | IC MIXER FM IF SYSTM RSSI 20SSOP | Arrow | 568-1105-2-ND | NXP | SA636DK-T |  | 18.3
60 | Basic | 1 | U3 | COMPARATOR | SOT23-5 | 0.05 | IC DIFF COMPARATOR SOT-23-5 | Digi-Key | 296-10492-2-ND | TI | TLV1391CDBVR |  | 18.3
61 |  |  |  | or | SOT23-5 | 0 | IC DIFF COMPARATOR SOT-23-5 | Arrow | TLV1391CDBVR | TI | TLV1391CDBVR |  | 18.3
62 | Basic | 2 | U4,U8 | OPAMP | SOT23-5 | 0.1 | IC OPAMP R-R LOW V LP SOT23-5 | Digi-Key | LMV821M5TR-ND | National Semi. | LMV821M5 |  | 18.3
63 | Basic | 1 | U5 | DIGITAL POT | 8-µSOP | 0.05 | IC POT TRIMMER NV 10K 8-USOP | Digi-Key | DS1804U-010+T&R-ND | Dallas Semi. | DS1804U-010+T&R |  | 18.3
64 | Basic | 1 | U6 | AT-113 | SO8 | 0.05 |  | FAI Elec. | 6219539 | MCM | AT-113TR |  | 18.3
65 | Basic | 1 | U7 | MMIC Switch SPDT | SOT-26 | 0.05 | MMIC SWITCH SPDT 2.5GHZ SOT-26 | Digi-Key | UPG152TACT-ND | NEC | UPG152TA-E3 |  | 18.3
66 | Basic | 1 | U9 | 555 TIMER | 8-MSOP | 0.05 | IC TIMER 8-MSOP | Digi-Key | LM555CMMTR-ND | National Semi. | LM555CMM/NOPB |  | 18.3
67 | Basic | 2 | Y1,Y2 | 10.7MHz | Filter | 0.1 | FILTER 10.7MHZ 330KHZ BANDWIDTH | Digi-Key | 490-1228-2-ND | Murata | SFECS10M7EA00-R0 |  | 18.3
68 | OPT11 | 1 | Y5 | 916.5MHz | Filter | 0.05 |  | Avnet | RF1181D-ENG | RF Monolithics | RF1181D |  | 18.3
69 | OPT11 | 1 | Y6 | 916.5MHz | Resonator | 0.05 |  | Avnet | RO2144D-T/R | RF Monolithics | RO2144D |  | 18.3
70 | OPT11 | 1 | Y3 | 905.8MHz | Resonator | 0.05 |  | Avnet | RO2216D-6 | RF Monolithics | RO2216D-6 |  | 18.3
71 | OPT11 | 1 | C23 | 4.0pF +/- 0.25pF | 0603 | 0.05 | CAP CER 4.0PF 50V C0G 0603 | Digi-Key | 490-1387-2-ND | Murata | GRM1885C1H4R0CZ01D |  | 18.3
72 | OPT11 | 1 | C59 | 15pF | 0603 | 0.05 | CAP CER 15PF 50V 5% C0G 0603 | Digi-Key | 490-1403-2-ND | Murata |  |  | 18.3
73 | OPT11 | 1 | L16 | 3.3nH | 0603 | 0.05 | INDUCTOR 3.3NH +-.2NH FIXED SMD | Digi-Key | PCD1288TR-ND | Panasonic-ECG | ELJ-RE3N3ZF2 |  | 18.3
74 |  |  |  |  |  | 0 |  |  |  |  |  |  | 18.3
75 | OPT21 | 1 | C33 | 3.0pF +/- 0.25pF | 0603 | 0.05 | CAP CER 3.0PF 50V C0G 0603 | Digi-Key | 490-1383-2-ND | Murata | GRM1885C1H3R0CZ01D
76 | OPT21 | 1 | C35 | 10.0pF +/- 0.50pF | 0603 | 0.05 | CAP CER 10PF 50V 5% C0G 0603 | Digi-Key | 490-1403-2-ND | Murata | GRM1885C1H100JA01D |  | 18.6
77 | OPT21 | 1 | Y4 | 433.92MHz | Resonator | 0.05 |  | Avnet | R02101D-T/R or RO2101E-T/R | RF Monolithics | Ro2101D or RO2101E |  | 18.3
78 | OPT22 | 1 | C33 | 2.0pF +/- 0.25pF | 0603 | 0.05 | CAP CER 2.0PF 50V C0G 0603 | Digi-Key | 490-1379-2-ND | Murata | GRM1885C1H2R0CZ01D |  | 18.6
79 | OPT22 | 1 | C35 | 18.0pF +/- 0.50pF | 0603 | 0.05 | CAP CER 18PF 50V 5% C0G 0603 | Digi-Key | 490-1409-2-ND | Murata | GRM1885C1H180JA01D |  | 18.6
80
81 | OPTD-11 | 1 | C45 | 3.0 pF | 0603 | 0.05 | CAP CER 3.0PF,+/-0.25PF, 50V C0G 0603 | Digi-Key | 490-1383-2-ND | Murata | GRM1885C1H3R0CZ01D |  | 7
82 | OPTD-11 | 1 | C30 | 10pF | 0603 | 0.05 | CAP CER 10PF 50V 5% C0G 0603 | Digi-Key | 490-1403-2-ND | Murata | GRM1885C1H100JA01D |  | 7
83 | OPTD-11 | 1 | C28 | 4.0pF +/- 0.25pF | 0603 | 0.05 | CAP CER 4.0PF 50V C0G 0603 | Digi-Key | 490-1387-2-ND | Murata | GRM1885C1H4R0CZ01D |  | 18.3
84 | OPTD-11 | 1 | L9 | 6.8nH | 0603 | 0.05 | INDUCTOR 6.8NH 5% 0603 SMD | Digi-Key | PCD1971TR-ND | Panasonic | ELJ-RE6N8JFA |  | 7
85 | OPTD-11 | 1 | L12 | 22nH | 0603 | 0.05 | INDUCTOR 22NH 5% 0603 SMD | Digi-Key | PCD1977TR-ND | Panasonic | ELJ-RE22NJFA |  | 7
86 | OPTD-11 | 1 | L7 | 330nH | 0603 | 0.05 | INDUCTOR MULTILAYER 0.33UH 1608 | Digi-Key | 445-1009-2-ND | TDK Corporation | MLF1608DR33K |  | 7
87 | OPTD-11 | 1 | Y4 | 433.92MHz | 3.8 X 3.8 MM | 0.05 | 40 dB, 0.5-2.0 GHz | RF Monolithics | RO2101D | RF Monolithics | RO2101D |  | 7
88 | Basic | 0 | C57,R7,R28,,R45,L6,U10 | DMP |  | 0 |  |  |  |  |  |  | 18.3
 |  |  |  |  |  | 8

Sheet: Sheet2
Handheld Reader Side
10/20/2012
 |  |  | Handheld Reader Side Ver 1.0
Item # | Part Stat. | Qty. | Part Ref. | Value | 0.05 | Part Size | Description | Dist. | Distributor P/N | Manufacturer | Manufacturer P/N | Notes | Revision
1 | Basic | 7 | C110,C111,C112,C113,C114,C115,C116 | 47pF | 0.35 | 0603 | CAP CER 47PF 50V C0G 5% 0603 | Digi-Key | 445-1277-2-ND | TDK Corp | C1608C0G1H470J | BF | 1.0
2 | Basic | 1 | C121 | 100 pF | 0.05 | 0603 | CAP 100PF 50V CERAMIC | Digi-Key | 445-1281-2-ND | TDK Corp | C1608C0G1H101J | BF | 1.0
3 | Basic | 9 | C101,C102,C107,C109,C301,C302,C303,C304,C305 | 0.1 uF | 0.45 | 0603 | CAP .10UF 16V CERAMIC X7R | Digi-Key | 399-1100-2-ND | Kemet | C0603C104Z3VACTU | BF | 1.0
4 | Basic | 1 | C124 | 4.7uF | 0.05 | Cap A case | CAPACITOR TANT 4.7UF 16V 10% SMD | Digi-Key | 399-3697-2-ND | Kemet | T491A475K016AT | BF | 2.0
5 | Basic | 1 | C125 | 10uF TANT | 0.05 | A (EIA) 3216-18 | CAPACITOR TANT 10UF 6.3V 10% SMD | Digi-Key | 399-1551-1-ND | Kemet | T491A106K006AS | BF | 1.0
6 | Basic | 1 | R112 | 0 | 0.05 | 0603 | RES 0.0 OHM 1/10W 0603 SMD | Digi-Key | RHM0.0GTR-ND | Rohm | MCR03EZPJ000 | BF | 1.0
7 | Basic | 2 | R122,R123 | 10 | 0.1 | 0603 | Carbon Film Resistor 10 OHM 1/16W 5% | Digi-Key | RHM10GTR-ND | Rohm | MCR03EZPJ100 | BF | 1.0
8 | Basic | 5 | R113,R114,R115,R116,R117 | 100 | 0.25 | 0603 | RES 100 OHM 1/10W 5% 0603 SMD | Digi-Key | RHM100GTR-ND | Rohm | MCR03EZPJ101 | BF | 1.0
9 | Basic | 1 | R118 | 120 | 0.05 | 0603 | RES 120 OHM 1/10W 5% 0603 SMD | Digikey | RHM120GTR-ND | Rohm | MCR03EZPJ121 | BF | 1.0
10 | Basic | 1 | R126 | 150 | 0.05 | 0603 | RES 150 OHM 1/10W 5% 0603 SMD | Digikey | RHM150GTR-ND | Rohm | MCR03EZPJ151 | BF | 1.0
11 | Basic | 1 | R119 | 180 | 0.05 | 0603 | RES 180 OHM 1/10W 5% 0603 SMD | Digikey | RHM180GTR-ND | Rohm | MCR03EZPJ181 | BF | 1.0
12 | Basic | 1 | R111 | 330 | 0.05 | 0603 | RES 330 OHM 1/10W 5% 0603 SMD | Digikey | RHM330GTR-ND | Rohm | MCR03EZPJ331 | BF | 1.0
13 | Basic | 2 | R120,R121 | 6.8K | 0.1 | 0603 | RES 6.8K OHM 1/10W 5% 0603 SMD | Digikey | RHM6.8KGTR-ND | Rohm | MCR03EZPJ682 | BF | 1.0
14 | Basic | 11 | R101,R102,R103,R104,R105,R106,R107,R108,R109,R110 ,R132 | 10K | 0.55 | 0603 | RES 10K OHM 1/10W 5% 0603 SMD | Digikey | RHM10KGTR-ND | Rohm | MCR03EZPJ103 | BF | 1.0
15 | Basic | 1 | R131 | 13.3K 1% | 0.05 | 0603 | RES 13.3K OHM 1/10W 1% 0603 SMD | Digi-Key | RHM13.3KHTR-ND | Rohm | MCR03EZPFX1332 | BF | 1.0
16 | Basic | 1 | R130 | 40.2K | 0.05 | 0603 | RES 40.2K OHM 1/10W 1% 0603 SMD | Digi-Key | RHM40.2KHTR-ND | Rohm | MCR03EZPFX4022 | BF | 1.0
17 | Basic | 6 | FB101,FB102,FB103,FB104,FB105,FB106 | Ferrite Beads | 0.3 | 0603 | BEAD CORE 27 OHM 4A 0603 SMD | Digi-Key | P10436CT-ND | Panasonic-ECG | EXC-ML16A270U | BF | 1.0
18 | Basic | 1 | L102 | 2.2uH | 0.05 |  |  | CoilCraft | DO1606T-222 | CoilCraft | DO1606T-222 | BF | 1.0
19 | Basic | 1 | D101 | RLED | 0.05 | LED-0603 |  | Digikey | P11511CT-ND | Panasonic-SSG | LNJ216C8ARA | BF | 1.0
20 | Basic | 1 | D102 | YLED | 0.05 | LED-0603 |  | Digikey | P11514CT-ND | Panasonic-SSG | LNJ416Q8YRA | BF | 1.0
21 | Basic | 1 | D103 | GLED | 0.05 | LED-0603 |  | Digikey | P11515CT-ND | Panasonic-SSG | LNJ316C8TRA | BF | 1.0
22 | Basic | 1 | D105 | MBR0520 | 0.05 | SOD123 |  | Digi-Key | MBR0520LCT-ND | Fairchild Semi | MBR0520L | BF | 1.0
23 | Basic | 2 | Q101,Q102 | 2N3904 | 0.1 | SOT-23 | TRANS NPN SW 200MA 40V SOT23 | Digikey | 568-1741-2-ND | Zetex, Inc. | PMBT3904 T/R | BF | 1.0
24 | Basic | 2 | U101,U103 | PIC16F870 | 0.1 | SSOP-28 | IC MCU FLASH 2KX14 EE 28SSOP | Digikey | PIC16F870-I/SS | Microchip | PIC16F870-I/SS | BF | 1.0
25 | Basic | 1 | U102 | PIC16F876A | 0.05 | SSOP-28 | IC MCU FLASH 8KX14 EE 28SSOP | Digikey | PIC16F876A-I/SS | Microchip | PIC16F876A-I/SS | BF | 1.0
26 | Basic | 1 | U106 | 16.0 MHz | 0.05 | CRY-SMD-5-7 | OSCILLATOR 16MHZ HCMOS SMD | Digi-key | CW304-ND | Connor-Winfield | HSM93-16.0000 | BF | 1.0
27 | Basic | 1 | U107 | LT1930 | 0.05 | SOT23-5A | IC DC/DC CONV STEP-UP SOT23-5 | Digikey | LT1930AES5#TRMPBFCT-ND | Linear Tech. | LT1930AES5#TRMPBF | BF | 1.0
28 | Basic | 2 | U108,U109 | And Gate | 0.1 | 6-TSSOP | IC GATE AND 2-INPUT UHS SC70-5 | Digikey | NC7SZ08P5XTR-ND | Fairchild Semiconductor (http://digikey.com/Suppliers/us/Fairchild-Semiconductor.page?lang=en) | NC7SZ08P5X |  | 1.0 | Fax: 760-406-4068
29 | Basic | 0 | J101,J102,J103,TP119,TP120,TP121 | DMP | 0 |  |  |  |  |  |  | BF | 1.0
 |  |  |  |  | 3.3
 | Basic | 2 |  | Amphenol SMA Reverse Polarity Connectors |  |  |  | Mouswer | 523-132220RP | Amphenol | 132220RP
