tourajghaffari/tigerfid/bom-files/tag/Tag-101 5-10-2011 REV 17.4.xls

TAG-101Rev17.3
05/10/2011 |  |  |  |  |  |  |  |  | Card Tag REV17.2Board
Item # | Part Stat. | Option # | Qty-Sur | Part Ref. | Value | Part Size | Description | Dist. | Distributor P/N | Manufacturer | Manufacturer P/N | Note | Revision
1 | BASIC |  | 1 | C3 | 2.0pF +/- 0.25pF | 0603 | CAP CER 2.0PF 50V C0G 0603 | Digi-Key | 490-1379-2-ND | Murata | GRM1885C1H2R0CZ01D |  | 17.0
2 | BASIC |  | 1 | C20 | 15pF | 0603 | CAP CER 15PF 50V 5% C0G 0603 | Digi-Key | 490-1407-2-ND | Murata | GRM1885C1H150JA01D |  | 17.0
3 | BASIC |  | 2 | C12,C13 | 33pF | 0603 | CAP CER 33PF 50V 5% C0G 0603 | Digi-Key | 490-1415-2-ND | Murata | GRM1885C1H330JA01D |  | 17.0
4 | BASIC |  | 2 | C6,C14 | 100 pF | 0603 | CAP 100PF 50V CERAMIC | Digi-Key | 445-1281-2-ND | TDK Corp | C1608C0G1H101J |  | 17.0
5 | BASIC |  | 1 | C7 | 220 pF | 0603 | CAP CER 220PF 50V C0G 5% 0603 | Digi-Key | 445-1285-2-ND | TDK Corp | C1608C0G1H221J |  | 17.7
6 | BASIC |  | 2 | C8,C9 | 1000 pF | 0603 | CAP 1000PF 50V CERAMIC NP0 | Digi-Key | 399-1083-2-ND | Kemet | C0603C102J5RACTU |  | 17.0
7 | BASIC |  | 1 | C17 | 10000 pF | 0603 | CAP 10000PF 50V CERAMIC NP0 | Digi-Key | 399-1091-2-ND | Kemet | C0603C103K5RACTU |  | 17.0
8 | BASIC |  | 4 | C11,C15,C18, C24 | 0.1 uF | 0603 | CAP .10UF 16V CERAMIC X7R | Digi-Key | 399-1100-2-ND | Kemet | C0603C104Z3VACTU |  | 17.0
9 | BASIC |  | 0 | C22,C23 | DNP | 0603 |  |  |  |  |  |  | 17.0
10 | BASIC |  | 2 | R12,R13 | 10 | 0603 | Carbon Film Resistor 10 OHM 1/16W 5% | Digi-Key | RHM10GTR-ND | Rohm | MCR03EZPJ100 |  | 17.0
11 | BASIC |  | 1 | R6 | 22 ohm | 0603 | RES 22 OHM 1/10W 5% | Digi-Key | RHM22GTR-ND | Rohm | MCR03EZPJ220 |  | 17.0
12 | BASIC |  | 1 | R11 | 68 | 0603 | Carbon Film Resistor 68 OHM 1/16W 5% | Digi-Key | RHM68GTR-ND | Rohm | MCR03EZPJ680 |  | 17.0
13 | BASIC |  | 1 | R14 | 470 | 0603 | RES 470 OHM 1/10W 1% 0603 SMD | Digi-Key | RHM470HTR-ND | Rohm | MCR03EZPFX4700 | Change to 1% | 17.0
14 | BASIC |  | 1 | R18 | 1.0K | 0603 | RES 1.00K OHM 1/10W 1% 0603 SMD | Digi-Key | RHM1.00KHTR-ND | Rohm | MCR03EZPFX1001 |  | 17.0
15 | BASIC |  | 1 | R17 | 1.3K | 0603 | RES 1.30K OHM 1/10W 1% 0603 SMD | Digi-Key | RHM1.30KHTR-ND | Rohm | MCR03EZPFX1301 |  | 17.0
16 | BASIC |  | 1 | R19 | 2.0K | 0603 | RES 2.00K OHM 1/10W 1% 0603 SMD | Digi-Key | RHM2.00KHTR-ND | Rohm | MCR03EZPFX2001 | Change to 1% | 17.0
17 | BASIC |  | 1 | R20 | 2.7K | 0603 | Carbon Film Resistor 2.7K OHM 1/16W 5% | Digi-Key | RHM2.7KGTR-ND | Rohm | MCR03EZPJ272 |  | 17.0
18 | BASIC |  | 1 | R16 | 3.0K | 0603 | RES 3.00K OHM 1/10W 1% 0603 SMD | Digi-Key | RHM3.00KHTR-ND | Rohm | MCR03EZPFX3001 | Change to 1% | 17.0
19 | BASIC |  | 2 | R1,R8 | 4.7K | 0603 | Carbon Film Resistor 4.7K OHM 1/16W 5% | Digi-Key | RHM4.7KGTR-ND | Rohm | MCR03EZPJ472 |  | 17.0
20 | BASIC |  | 1 | R7 | 6.8K | 0603 | Carbon Film Resistor 6.8K OHM 1/16W 5% | Digi-Key | RHM6.8KGTR-ND | Rohm | MCR03EZPJ682 |  | 17.0
21 | BASIC |  | 1 | R15 | 36.5K | 0603 | RES 36.5K OHM 1/10W 1% 0603 SMD | Digi-Key | RHM36.5KHTR-ND | Rohm | MCR03EZPFX3652 |  | 17.0
22 | BASIC |  | 4 | R3,R5,R9,R10 | 39K | 0603 | Carbon Film Resistor 39k OHM 1/16W 5% | Digi-Key | RHM39KGTR-ND | Rohm | MCR03EZPJ393 |  | 17.0
23 | BASIC |  | 1 | R4 | 56.2K | 0603 | RES 56.2K OHM 1/10W 1% 0603 SMD | Digi-Key | RHM56.2KHTR-ND | Rohm | MCR03EZPFX5622 |  | 17.0
24 | BASIC |  | 1 | R24 | 150k | 0603 | RES 150K OHM 1/10W 1% 0603 SMD | Digi-Key | RHM100KHTR-ND | Rohm | MCR03EZPFX1503 | Change to 1% | 17.1
25 | BASIC |  | 1 | R21 | 220k | 0603 | RES 220K OHM 1/10W 1% 0603 SMD | Digi-Key | RHM220KHTR-ND | Rohm | MCR03EZPFX2203 | Change to 1% | 17.0
26 | BASIC |  | 1 | R2 | 1M | 0603 | Carbon Film Resistor 1M OHM 1/16W 5% | Digi-Key | RHM1.0MGTR-ND | Rohm | MCR03EZPJ105 |  | 17.0
27 | BASIC |  | 1 | L2 | 8.2nH | 0603 | INDUCTOR MULTILAYER 8.2NH 0603 | Digi-Key | 445-1491-2-ND | TDK Corporation | MLG1608B8N2D |  | 17.1 | Some times is 6.8
28 | BASIC |  | 1 | L3 | 0.18uH | 0603 | INDUCTOR MULTILAYER 0.18 UH | Digi-Key | 445-1006-1-ND | TDK Corporation | MLF1608DR18K |  | 17.0
29 | BASIC |  | 1 | L6 | 100nH | 0603 | INDUCTOR 100NH 5% 0603 SMD | Digi-Key | PCD1985TR-ND | Panasonic-ECG | ELJ-RER10JFA |  | 18.4
30 | BASIC |  | 2 | Q1,Q2 | NE85619 | Ultra Super Mini Mold | TRANS NPN 1GHZ SMD | Digi-Key | NE85619-ATR-ND | NEC | NE85619-T1-A |  | 17.0
31 | BASIC |  | 1 | Q3 | 2N7002 | SOT-23 | IC TRANS N-CH 60V 7.5 OHM | Digi-Key | 2N7002NTR-ND | Fairchild | 2N7002NTR-ND |  | 17.0
 |  |  |  | ALT |  |  | IC TRANS N-CH 60V 7.5 OHM |  |  | ON Semi (Motorola) | 2N7002LT1 |  | 17.0
 |  |  |  | ALT |  |  | IC TRANS N-CH 60V 7.5 OHM |  |  | Phycomp/Yageo/Phillips | 2N7002 |  | 17.0
 |  |  |  | ALT |  |  | IC TRANS N-CH 60V 7.5 OHM |  |  | Siemens (Infineon) | 2N7002 |  | 17.0
 |  |  |  | ALT |  |  | IC TRANS N-CH 60V 7.5 OHM |  |  | Siliconix-Vishay-Temic | 2N7002 T&R |  | 17.0
32 | BASIC |  | 1 | U1 | PIC16F690 | 20SSOP | IC MCU FLASH 4KX14 EEPROM | Digi-Key | PIC16F690-I/SS-ND | Microchip | PIC16F690-I/SS |  | 17.0
33 | BASIC |  | 1 | U2 | MIC861 | SC-70-5 | IC OPAMP 400KHZ 2.7V ULT LP SC70 | Digi-Key | MIC861YC5TR-ND | Micrel | MIC861YC5TR |  | 17.0
34 | BASIC |  | 1 | U5 | TC1070VCT713 | SOT23A-5 | IC REG LDO ADJ 50MA |  |  | Microchip | TC1070VCT713 |  | 17.0
35 | BASIC |  | 1 | U6 | MAX9119EXK+ | SC70 | IC COMPARATOR BTR SC70-5 | Digi-Key | MAX9119EXK+T-ND | Maxim | MAX9119EXK+T |  | 17.0
36 | BASIC |  | 1 | B1A | Battery Holder |  | Battery Retainer | Keystone | C-5510-ACT | Keystone | C-5510-ACT |  | 17.0
37 | BASIC |  | 1 | B1B | Battery Contact |  | Battery Contact |  |  | Laird Technology | 0097-0488-02 |  | 17.0
38 | BASIC |  |  | PCB | PCB 105 |  | Jumbo Tag board |  |  | Active Sales |  |  | 17.0
39 | BASIC |  | 0 | J1,J2 | DNP | Mask it | NO SOLDER IN HOLES |  |  |  |  | NO SOLDER IN HOLES | 17.0
 |  |  |  |  |  |  |  |  |  |  |  |  | 17.0
40 | OPT1 |  | 1 | Y1 | 916.5 Resonator | 3.8x3.8mm | 916.5 MHz Saw Resonator | Richardson | RO2144D | RF Monolithics | RO2144D |  | 17.0
41 | OPT1 |  | 1 | C21 | 1.8pF +/- 0.25pF | 0603 | CAP CER 1.8PF 50V C0G 0603 | Digi-Key | 490-1378-2-ND | Murata | GRM1885C1H1R8CZ01D
42 | OPT1 |  | 1 | C2 | 2.7pF +/- 0.25pF | 0603 | CAP CER 2.7PF 50V C0G 0603 | Digi-Key | 490-1382-2-ND | Murata | GRM1885C1H2R7CZ01D |  | 17.1
43 | OPT1 |  | 1 | C19 | 5.6pF ±0.5pF | 0603 | CAP CER 5.6PF 50V C0G 0603 | Digi-Key | 490-1392-2-ND | Murata | GRM1885C1H5R6DZ01D |  | 17.3
44 | OPT1 |  | 1 | C10 | 1000 pF | 0603 | CAP 1000PF 50V CERAMIC NP0 | Digi-Key | 399-1083-2-ND | Kemet | C0603C102J5RACTU |  | 17.0
 |  |  |  |  |  |  |  |  |  |  |  |  | 17.0
45 | OPT2 |  | 1 | Y1 | 868.95 Resonator | 3.8x3.8mm | 868.95 MHz Saw Resonator | Richardson | RO2156D | RF Monolithics | RO2156D |  | 17.0
46 | OPT2 |  | 1 | C21 | 1.8pF +/- 0.25pF | 0603 | CAP CER 1.8PF 50V C0G 0603 | Digi-Key | 490-1378-2-ND | Murata | GRM1885C1H1R8CZ01D
47 | OPT2 |  | 1 | C2 | 2.2pF +/- 0.25pF | 0603 | CAP CER 2.2PF 50V C0G 0603 | Digi-Key | 490-1380-2-ND | Murata | GRM1885C1H2R2CZ01D |  | 17.3
48 | OPT2 |  | 1 | C19 | 5.6pF +/-0.5pF | 0603 | CAP CER 5.6PF 50V C0G 0603 | Digi-Key | 490-1392-2-ND | Murata | GRM1885C1H5R6DZ01D |  | 17.3
49 | OPT2 |  | 1 | C10 | 1000 pF | 0603 | CAP 1000PF 50V CERAMIC NP0 | Digi-Key | 399-1083-2-ND | Kemet | C0603C102J5RACTU |  | 17.0
50 | OPT3 |  | 1 | Y1 | 927.2 Resonator | 3.8x3.8mm | 927.2 MHz Saw Resonator |  |  | SUNNY ELECTRONICS | SR-00927 |  | 17.0
51 | OPT3 |  | 1 | C21 | 1.8pF +/- 0.25pF | 0603 | CAP CER 1.8PF 50V C0G 0603 | Digi-Key | 490-1378-2-ND | Murata | GRM1885C1H1R8CZ01D
52 | OPT3 |  | 1 | C2 | 2.7pF +/- 0.25pF | 0603 | CAP CER 2.7PF 50V C0G 0603 | Digi-Key | 490-1382-2-ND | Murata | GRM1885C1H2R7CZ01D |  | 17.0
53 | OPT3 |  | 1 | C19 | 4.7pF +/-0.25pF | 0603 | CAP CER 4.7PF 50V C0G 0603 | Digi-Key | 490-1389-2-ND | Murata | GRM1885C1H4R7CZ01D |  | 18.4
54 | OPT3 |  | 1 | C10 | 1000 pF | 0603 | CAP 1000PF 50V CERAMIC NP0 | Digi-Key | 399-1083-2-ND | Kemet | C0603C102J5RACTU |  | 17.0
 |  |  |  |  |  |  |  |  |  |  |  |  | 17.0
55 | OPT4 |  | 1 | Y1 | 867 Resonator | 3.8x3.8mm | 867 MHz Saw Resonator |  |  | SUNNY ELECTRONICS | SR-00867 |  | 17.3
56 | OPT4 |  | 1 | C21 | 6.2pF +/-0.5pF | 0603 | CAP CER 6.2PF 50V C0G 0603 | Digi-Key | 490-1394-2-ND | Murata | GRM1885C1H4R0CZ01D |  | 17.3
57 | OPT4 |  | 1 | C2 | 2.2pF +/- 0.25pF | 0603 | CAP CER 2.2PF 50V C0G 0603 | Digi-Key | 490-1380-2-ND | Murata | GRM1885C1H2R2CZ01D |  | 17.3
58 | OPT4 |  | 1 | C19 | 5.6pF +/-0.5pF | 0603 | CAP CER 5.6PF 50V C0G 0603 | Digi-Key | 490-1392-2-ND | Murata | GRM1885C1H5R6DZ01D |  | 17.3
 |  |  |  |  |  |  |  |  |  |  |  |  | 17.0
59 | OPT E-1 | MEM-1 | N/A | U4 | 1K Bit | 8-SOIC |  |  |  |  |  |  | 17.0
60 | OPT E-2 | MEM-2 | N/A | U4 | 2K Bits | 8-SOIC |  |  |  |  |  |  | 17.0
61 | OPT E-3 | MEM-3 | 1 | U4 | 4K Bits | 8-SOIC | 512 x 8 1.8V Serial EE |  |  | Microchip | 24AA04-I/SN |  | 17.0
62 | OPT E-4 | MEM-4 | N/A | U4 | 8K Bits | 8-SOIC |  |  |  |  |  |  | 17.0
63 | OPT E-5 | MEM-5 | N/A | U4 | 16K Bits | 8-SOIC |  |  |  |  |  |  | 17.0
64 | OPT E-6 | MEM-6 | N/A | U4 | 32K Bits | 8-SOIC |  |  |  |  |  |  | 17.0
65 | OPT E-7 | MEM-7 | N/A | U4 | 64K Bits | 8-SOIC |  |  |  |  |  |  | 17.0
66 | OPT E-8 | MEM-8 | N/A | U4 | 128K Bits | 8-SOIC |  |  |  |  |  |  | 17.0
67 | OPT E-9 | MEM-9 | 1 | U4 | 256K Bits | 8-SOIC | 32K x 8 1.8V serial EE |  |  | Microchip | 24AA256-I/SN |  | 17.0
 |  |  |  |  |  |  |  |  |  |  |  |  | 17.0
68 |  |  | 25 | C1,C4,C5,C16,C22,C23,C25,C26,C27 | DNP
 |  |  |  | R22,R23,R25,R26,R27 | DNP
 |  |  |  | Q4,U3,U4,U7 | DNP
 |  |  |  | D1,D2,D3,DS2 | DNP
 |  |  |  | SP1,SW1,SW2 | DNP
 |  |  |  | Y2 |  |  |  |  |  |  |  |  | 17.0
 |  |  |  |  |  |  |  |  |  |  |  |  | 17.0
69 | OPT K-0 | BAT-0-1 | 0 |  | DNP |  | B1 | No Battery |  |  |  |  | 17.0
 |  |  |  |  |  |  |  |  |  |  |  |  | 17.0
70 | OPT K-1 | BAT-1-2 | 1 |  |  |  | B1 | Battery |  | Renata | CR2032FV |  | 17.0
 |  |  |  |  |  |  |  |  |  |  |  |  | 17.0
71 | OPT L-0 | COL-0 | 0 | Enclosure | DNP |  |  |  |  |  |  |  | 17.0
 |  |  |  |  |  |  |  |  |  |  |  |  | 17.0
72 | OPT L-1 | COL-1 | 1 | Enclosure | White w/AWI logo |  |  |  |  |  |  |  | 17.0
 |  |  |  |  |  |  |  |  |  |  |  |  | 17.0
73 | OPT L-2 | COL-2 | 1 | Enclosure | Black w/ AWI logo |  |  |  |  |  |  |  | 17.0
 |  |  |  |  |  |  |  |  |  |  |  |  | 17.0
74 | OPT L-3 | COL-3 | 1 | Enclosure | Custom (logo, etc.) |  |  |  |  |  |  |  | 17.0
