tourajghaffari/tigerfid/bom-files/tag/Tag-102 10-16-2012 REV 21.0.xls

Sheet: Sheet1
TAG-102-Rev21
06/02/2012 |  |  |  |  |  |  | Compact Tag REV21.0 Board
Item # | Part Stat. | Option # | Qty-Sur | Part Ref. | Value | Part Size | Description | Dist. | Distributor P/N | Manufacturer | Manufacturer P/N | Note | Revision
1 | BASIC |  | 1 | C3 | 2.0pF +/- 0.25pF | 0603 | CAP CER 2.0PF 50V C0G 0603 | Digi-Key | 490-1379-2-ND | Murata | GRM1885C1H2R0CZ01D |  | 17.0
2 | BASIC |  | 1 | C20 | 15pF | 0603 | CAP CER 15PF 50V 5% C0G 0603 | Digi-Key | 490-1407-2-ND | Murata | GRM1885C1H150JA01D |  | 17.0
3 | BASIC |  | 2 | C12,C13 | 33pF | 0603 | CAP CER 33PF 50V 5% C0G 0603 | Digi-Key | 490-1415-2-ND | Murata | GRM1885C1H330JA01D |  | 17.0
4 | BASIC |  | 2 | C6,C14 | 100 pF | 0603 | CAP 100PF 50V CERAMIC | Digi-Key | 445-1281-2-ND | TDK Corp | C1608C0G1H101J |  | 17.0
5 | BASIC |  | 1 | C7 | 220 pF | 0603 | CAP CER 220PF 50V C0G 5% 0603 | Digi-Key | 445-1285-2-ND | TDK Corp | C1608C0G1H221J |  | 17.7
6 | BASIC |  | 2 | C8,C9 | 1000 pF | 0603 | CAP 1000PF 50V CERAMIC NP0 | Digi-Key | 399-1083-2-ND | Kemet | C0603C102J5RACTU |  | 17.0
7 | BASIC |  | 5 | C11,C15,C17,C18, C24 | 0.1 uF | 0603 | CAP .10UF 16V CERAMIC X7R | Digi-Key | 399-1100-2-ND | Kemet | C0603C104Z3VACTU |  | 17.0
8 | BASIC |  | 2 | R12,R13 | 10 | 0603 | Carbon Film Resistor 10 OHM 1/16W 5% | Digi-Key | RHM10GTR-ND | Rohm | MCR03EZPJ100 |  | 17.0
9 | BASIC |  | 1 | R6 | 22 ohm | 0603 | RES 22 OHM 1/10W 5% | Digi-Key | RHM22GTR-ND | Rohm | MCR03EZPJ220 |  | 17.0
10 | BASIC |  | 1 | R11 | 68 | 0603 | Carbon Film Resistor 68 OHM 1/16W 5% | Digi-Key | RHM68GTR-ND | Rohm | MCR03EZPJ680 |  | 17.0
11 | BASIC |  | 1 | R14 | 470 | 0603 | RES 470 OHM 1/10W 1% 0603 SMD | Digi-Key | RHM470HTR-ND | Rohm | MCR03EZPFX4700 | Change to 1% | 17.0
12 | BASIC |  | 1 | R18 | 1.0K | 0603 | RES 1.00K OHM 1/10W 1% 0603 SMD | Digi-Key | RHM1.00KHTR-ND | Rohm | MCR03EZPFX1001 |  | 17.0
13 | BASIC |  | 1 | R17 | 1.3K | 0603 | RES 1.30K OHM 1/10W 1% 0603 SMD | Digi-Key | RHM1.30KHTR-ND | Rohm | MCR03EZPFX1301 |  | 17.0
14 | BASIC |  | 1 | R19 | 2.0K | 0603 | RES 2.00K OHM 1/10W 1% 0603 SMD | Digi-Key | RHM2.00KHTR-ND | Rohm | MCR03EZPFX2001 | Change to 1% | 17.0
15 | BASIC |  | 1 | R20 | 2.7K | 0603 | Carbon Film Resistor 2.7K OHM 1/16W 5% | Digi-Key | RHM2.7KGTR-ND | Rohm | MCR03EZPJ272 |  | 17.0
16 | BASIC |  | 1 | R16 | 3.0K | 0603 | RES 3.00K OHM 1/10W 1% 0603 SMD | Digi-Key | RHM3.00KHTR-ND | Rohm | MCR03EZPFX3001 | Change to 1% | 17.0
16 | BASIC |  | 2 | R1,R8 | 4.7K | 0603 | Carbon Film Resistor 4.7K OHM 1/16W 5% | Digi-Key | RHM4.7KGTR-ND | Rohm | MCR03EZPJ472 |  | 17.0
17 | BASIC |  | 1 | R7 | 6.8K | 0603 | Carbon Film Resistor 6.8K OHM 1/16W 5% | Digi-Key | RHM6.8KGTR-ND | Rohm | MCR03EZPJ682 |  | 17.0
18 | BASIC |  | 1 | R15 | 36.5K | 0603 | RES 36.5K OHM 1/10W 1% 0603 SMD | Digi-Key | RHM36.5KHTR-ND | Rohm | MCR03EZPFX3652 |  | 17.0
19 | BASIC |  | 4 | R3,R5,R9,R10 | 39K | 0603 | Carbon Film Resistor 39k OHM 1/16W 5% | Digi-Key | RHM39KGTR-ND | Rohm | MCR03EZPJ393 |  | 17.0
20 | BASIC |  | 1 | R4 | 56.2K | 0603 | RES 56.2K OHM 1/10W 1% 0603 SMD | Digi-Key | RHM56.2KHTR-ND | Rohm | MCR03EZPFX5622 |  | 17.0
21 | BASIC |  | 1 | R24 | 150k | 0603 | RES 150K OHM 1/10W 1% 0603 SMD | RES 150K OHM 1/10W 1% 0603 SMD | Digi-Key | RHM150KHTR-ND | Rohm | MCR03EZPFX1503 | Change to 1% | 17.2
22 | BASIC |  | 1 | R21 | 220k | 0603 | RES 220K OHM 1/10W 1% 0603 SMD | Digi-Key | RHM220KHTR-ND | Rohm | MCR03EZPFX2203 | Change to 1% | 17.0
23 | BASIC |  | 1 | R2 | 1M | 0603 | Carbon Film Resistor 1M OHM 1/16W 5% | Digi-Key | RHM1.0MGTR-ND | Rohm | MCR03EZPJ105 |  | 17.0
24 | BASIC |  | 1 | L2 | 6.8nH | 0603 | INDUCTOR MULTILAYER 6.8NH 0603 | Digi-Key | 445-1490-2-ND | TDK Corporation | MLG1608B6N8D |  | 17.2
25 | BASIC |  | 1 | L4 | 12.0nH | 0603 | INDUCTOR 12NH 2% 0603 SMD | Digi-Key | PCD2003TR-ND | Panasonic | ELJ-RE12NGFA | New Parts compare to 105 | 17.0
26 | BASIC |  | 1 | L3 | 0.18uH | 0603 | INDUCTOR MULTILAYER 0.18 UH | Digi-Key | 445-1006-1-ND | TDK Corporation | MLF1608DR18K |  | 17.0
27 | BASIC |  | 1 | L6 | 100nH | 0603 | INDUCTOR 100NH 5% 0603 SMD | Digi-Key | PCD1985TR-ND | Panasonic-ECG | ELJ-RER10JFA |  | 17.7
28 | BASIC |  | 2 | Q1,Q2 | NE85619 | Ultra Super Mini Mold | TRANS NPN 1GHZ SMD | Digi-Key | NE85619-ATR-ND | NEC | NE85619-T1-A |  | 17.0
29 | BASIC |  | 1 | Q3 | 2N7002 | SOT-23 | IC TRANS N-CH 60V 7.5 OHM | Digi-Key | 2N7002NTR-ND | Fairchild | 2N7002NTR-ND |  | 17.0
 |  |  |  | ALT |  |  | IC TRANS N-CH 60V 7.5 OHM |  |  | ON Semi (Motorola) | 2N7002LT1 |  | 17.0
 |  |  |  | ALT |  |  | IC TRANS N-CH 60V 7.5 OHM |  |  | Phycomp/Yageo/Phillips | 2N7002 |  | 17.0
 |  |  |  | ALT |  |  | IC TRANS N-CH 60V 7.5 OHM |  |  | Siemens (Infineon) | 2N7002 |  | 17.0
 |  |  |  | ALT |  |  | IC TRANS N-CH 60V 7.5 OHM |  |  | Siliconix-Vishay-Temic | 2N7002 T&R |  | 17.0
30 | BASIC |  | 1 | U1 | PIC16F690 | 20SSOP | IC MCU FLASH 4KX14 EEPROM | Digi-Key | PIC16F690-I/SS-ND | Microchip | PIC16F690-I/SS |  | 17.0
31 | BASIC |  | 1 | U2 | MIC861 | SC-70-5 | IC OPAMP 400KHZ 2.7V ULT LP SC70 | Digi-Key | MIC861YC5TR-ND | Micrel | MIC861YC5TR |  | 17.0
32 | BASIC |  | 1 | U5 | TC1070VCT713 | SOT23A-5 | IC REG LDO ADJ 50MA |  |  | Microchip | TC1070VCT713 |  | 17.0
33 | BASIC |  | 1 | U6 | MAX9119EXK+ | SC70 | IC COMPARATOR BTR SC70-5 | Digi-Key | MAX9119EXK+T-ND | Maxim | MAX9119EXK+T |  | 17.0
34 | BASIC |  | 1 | B1A | Battery Holder |  | Battery Retainer | Keystone | C-5510-ACT | Keystone | C-5510-ACT |  | 17.0
35 | BASIC |  | 1 | B1B | Battery Contact |  | Battery Contact |  |  | Laird Technology | 0097-0488-02 |  | 17.0
35 | BASIC |  |  | PCB | PCB 102 |  | Compact Tag board |  |  | Active Sales |  |  | 17.0
36 | BASIC |  | 0 | J1,J2 | DNP | Mask it | NO SOLDER IN HOLES |  |  |  |  | NO SOLDER IN HOLES | 17.0
 |  |  |  |  |  |  |  |  |  |  |  |  | 17.0
37 | OPT1 |  | 1 | Y1 | 916.5 Resonator | 3.8x3.8mm | 916.5 MHz Saw Resonator | Richardson | RO2144D | RF Monolithics | RO2144D |  | 17.0
38 | OPT1 |  | 1 | C21 | 1.8pF +/- 0.25pF | 0603 | CAP CER 1.8PF 50V C0G 0603 | Digi-Key | 490-1378-2-ND | Murata | GRM1885C1H1R8CZ01D |  | 17.7
39 | OPT1 |  | 1 | C2 | 3.6pF +/- 0.25pF | 0603 | CAP CER 3.6PF 50V C0G 0603 | Digi-Key | 490-1385-2-ND | Murata | GRM1885C1H3R6CZ01D |  | 17.7
40 | OPT1 |  | 1 | C19 | 2.7pF +/-0.25pF | 0603 | CAP CER 2.7PF 50V C0G 0603 | Digi-Key | 490-1382-2-ND | Murata | GRM1885C1H2R7CZ01D |  | 17.7
41 | OPT1 |  | 1 | C10 | 1000 pF | 0603 | CAP 1000PF 50V CERAMIC NP0 | Digi-Key | 399-1083-2-ND | Kemet | C0603C102J5RACTU |  | 17.7
41 | OPT2 |  | 1 | Y1 | 868.95 Resonator | 3.8x3.8mm | 868.95 MHz Saw Resonator | Richardson | RO2156D | RF Monolithics | RO2156D |  | 17.0
41 | OPT2 |  | 1 | C21 | 1.8pF +/- 0.25pF | 0603 | CAP CER 1.8PF 50V C0G 0603 | Digi-Key | 490-1378-2-ND | Murata | GRM1885C1H1R8CZ01D |  | 17.2
42 | OPT2 |  | 1 | C2 | 4.0pF +/- 0.25pF | 0603 | CAP CER 4.0PF 50V C0G 0603 | Digi-Key | 490-1387-2-ND | Murata | GRM1885C1H4R0CZ01D |  | 17.4 | 4.7 | this is final subjecct to do more testing
43 | OPT2 |  | 1 | C19 | 3.0pF +/- 0.25pF | 0603 | CAP CER 3.0PF 50V C0G 0603 | Digi-Key | 490-1383-2-ND | Murata | GRM1885C1H3R0CZ01D |  | 17.4 | 2.7 | this is final subjecct to do more testing
44 | OPT2 |  | 1 | C10 | 1000 pF | 0603 | CAP 1000PF 50V CERAMIC NP0 | Digi-Key | 399-1083-2-ND | Kemet | C0603C102J5RACTU |  | 17.0
44 | OPT3 |  | 1 | Y1 | 927.2 Resonator | 3.8x3.8mm | 927.2 MHz Saw Resonator |  |  | SUNNY ELECTRONICS | SR-00927 |  | 17.0
45 | OPT3 |  | 1 | C21 | 1.8pF +/- 0.25pF | 0603 | CAP CER 1.8PF 50V C0G 0603 | Digi-Key | 490-1378-2-ND | Murata | GRM1885C1H1R8CZ01D |  | 17.2 | Made correction
46 | OPT3 |  | 1 | C2 | 3.0pF +/- 0.25pF | 0603 | CAP CER 3.0PF 50V C0G 0603 | Digi-Key | 490-1383-2-ND | Murata | GRM1885C1H3R0CZ01D |  | 17.3
47 | OPT3 |  | 1 | C19 | 2.4pF +/-0.25pF | 0603 | CAP CER 2.4PF 50V C0G 0603 | Digi-Key | 490-1381-2-ND | Murata | GRM1885C1H2R4CZ01D |  | 17.2
48 | OPT3 |  | 1 | C10 | 1000 pF | 0603 | CAP 1000PF 50V CERAMIC NP0 | Digi-Key | 399-1083-2-ND | Kemet | C0603C102J5RACTU |  | 17.0
48 | OPT4 |  | 1 | Y1 | 867 Resonator | 3.8x3.8mm | 867 MHz Saw Resonator |  |  | SUNNY ELECTRONICS | SR-00867 |  | 17.3
49 | OPT4 |  | 1 | C21 | 6.2pF +/-0.5pF | 0603 | CAP CER 6.2PF 50V C0G 0603 | Digi-Key | 490-1394-2-ND | Murata | GRM1885C1H4R0CZ01D
50 | OPT4 |  | 1 | C2 | 4.0pF +/- 0.25pF | 0603 | CAP CER 4.0PF 50V C0G 0603 | Digi-Key | 490-1387-2-ND | Murata | GRM1885C1H4R0CZ01D |  | 17.3
51 | OPT4 |  | 1 | C19 | 3.0pF +/- 0.25pF | 0603 | CAP CER 3.0PF 50V C0G 0603 | Digi-Key | 490-1383-2-ND | Murata | GRM1885C1H3R0CZ01D |  | 17.3
52 | OPT4 |  | 1 | C10 | 2700 pF | 0603 | CAP CER 2700PF 50V X7R 0603 | CAP CER 2700PF 50V X7R 0603 | Digi-Key | C0603C272J5RACTU-ND | Kemet | C0603C272J5RACTU |  | 17.0
52 | OPT D-0 | TAM-0-1 | 0 | U7 | DNP |  |  |  |  |  |  |  | 17.0
53 | OPT D-0 | TAM-0-2 | 0 | C4 | DNP |  |  |  |  |  |  |  | 17.0
54 | OPT D-0 | TAM-0-4 | 0 | C1 | DNP |  |  |  |  |  |  |  | 17.0
 |  |  |  |  |  |  |  |  |  |  |  |  | 17.0
55 | OPT D-1 | TAM-1-1 | 1 | U7 | TLE4913 | SOT-23W | Low Power Hall Effect Switch | Arrow | TLE4913 | Infineon | TLE4913 |  | 17.0
56 | OPT D-1 | TAM-1-2 | 1 | C4 | 3.0pF +/- 0.25pF | 0603 | CAP CER 3.0PF 50V C0G 0603 | Digi-Key | 490-1383-2-ND | Murata | GRM1885C1H3R0CZ01D |  | 17.0
57 | OPT D-1 | TAM-1-3 | 1 | C1 | 0.1uF | 0603 | CAP .1UF 16V CERAMIC Y5V 0603 | Digi-Key | PCC1788CT-ND | Panasonic - ECG | ECJ-1VF1C104Z |  | 17.0
 |  |  |  |  |  |  |  |  |  |  |  |  | 17.0
58 | OPT E-0 | MEM-0 | 0 | U4 | DNP |  |  |  |  |  |  |  | 17.0
 |  |  |  |  |  |  |  |  |  |  |  |  | 17.0
59 | OPT E-1 | MEM-1 | N/A | U4 | 1K Bit | 8-SOIC |  |  |  |  |  |  | 17.0
60 | OPT E-2 | MEM-2 | N/A | U4 | 2K Bits | 8-SOIC |  |  |  |  |  |  | 17.0
61 | OPT E-3 | MEM-3 | 1 | U4 | 4K Bits | 8-SOIC | 512 x 8 1.8V Serial EE |  |  | Microchip | 24AA04-I/SN |  | 17.0
62 | OPT E-4 | MEM-4 | N/A | U4 | 8K Bits | 8-SOIC |  |  |  |  |  |  | 17.0
63 | OPT E-5 | MEM-5 | N/A | U4 | 16K Bits | 8-SOIC |  |  |  |  |  |  | 17.0
64 | OPT E-6 | MEM-6 | N/A | U4 | 32K Bits | 8-SOIC |  |  |  |  |  |  | 17.0
65 | OPT E-7 | MEM-7 | N/A | U4 | 64K Bits | 8-SOIC |  |  |  |  |  |  | 17.0
66 | OPT E-8 | MEM-8 | N/A | U4 | 128K Bits | 8-SOIC |  |  |  |  |  |  | 17.0
67 | OPT E-9 | MEM-9 | 1 | U4 | 256K Bits | 8-SOIC | 32K x 8 1.8V serial EE |  |  | Microchip | 24AA256-I/SN |  | 17.0
 |  |  |  |  |  |  |  |  |  |  |  |  | 17.0
68 | OPT F-0 | LED-0-1 | 0 | D1 | DNP |  |  |  |  |  |  |  | 17.0
69 | OPT F-0 | LED-0-2 | 0 | R22 | DNP |  |  |  |  |  |  |  | 17.0
 |  |  |  |  |  |  |  |  |  |  |  |  | 17.0
70 | OPT F-1 | LED-1-1 | 1 | D1 | Red LED | 1206 | LED RED CLEAR 1206 SMD | Digi-Key | 404-1032-2-ND | Stanley Electric Sales | HKR1105W-TR |  | 17.0
71 | OPT F-1 | LED-1-2 | 1 | R22 | 200 | 0603 | RES 200 OHM 1/10W 5% | Digi-Key | RHM200GTR-ND | Rohm | MCR03EZPJ201 |  | 17.0
 |  |  |  |  |  |  |  |  |  |  |  |  | 17.0
72 | OPT G-0 | BUZ-0-1 | 0 | SP1 | DNP |  |  |  |  |  |  |  | 17.0
73 | OPT G-0 | BUZ-0-2 | 0 | Q4 | DNP |  |  |  |  |  |  |  | 17.0
74 | OPT G-0 | BUZ-0-3 | 0 | C5 | DNP |  |  |  |  |  |  |  | 17.0
 |  |  |  |  |  |  |  |  |  |  |  |  | 17.0
75 | OPT G-1 | BUZ-1-1 | 1 | SP1 | Buzzer | 10X10X5mm | MagneticTransducer, External Drive | Digi-Key | 668-1084-2-ND | Projects Unlimited | SMT-1028-S-R |  | 17.0
76 | OPT G-1 | BUZ-1-2 | 1 | Q4 | MMBT2222A-7-F | SOT-23 | TRANS NPN 40V 350MW SMD SOT23 | Digi-Key | MMBT2222A-FDITR-ND | Diodes Inc | MMBT2222A-7-F |  | 17.0
77 | OPT G-1 | BUZ-1-3 | 1 | C5 | DNP |  |  |  |  |  |  |  | 17.0
78 | OPT G-1 | BUZ-1-3 | 1 | L4 | SMD-RL-8700-4 | 0603 |  | Transformer | Renco | S00192 | Renco | RL-9933
79 | OPT H-0 | TMP-0 | 0 | U3 | DNP |  |  |  |  |  |  |  | 17.0
 |  |  |  |  |  |  |  |  |  |  |  |  | 17.0
80 | OPT H-1 | TMP-1 | 1 | U3 | DS1631U | 8MSOP | Temperature Detector IC | Maxim | 90-1631U-TRL | Dallas Semiconductor | DS1631U/T&R |  | 17.0
 |  |  |  |  |  |  |  |  |  |  |  |  | 17.0
81 | OPT J-0 | SW2-0-1 | 0 | SW2 | DNP |  |  |  |  |  |  |  | 17.0
82 | OPT J-0 | SW2-0-2 | 0 | R25 | DNP |  |  |  |  |  |  |  | 17.0
83 | OPT J-0 | SW2-0-3 | 0 | R26 | DNP |  |  |  |  |  |  |  | 17.0
84 | OPT J-0 | SW2-0-4 | 0 | C16 | DNP |  |  |  |  |  |  |  | 17.0
85 | OPT J-0 | SW2-01-5 | 0 | D2 | DNP |  |  |  |  |  |  |  | 17.0
86 | OPT J-0 | SW2-0-5 | 0 | D3 | DNP |  |  |  |  |  |  |  | 17.0
87 | OPT J-0 | SW2-0-6 | 0 | C25 | DNP |  |  |  |  |  |  |  | 17.0
88 | OPT J-0 | SW2-0-6 | 0 | C25 | DNP |  |  |  |  |  |  |  | 17.0
89 | OPT J-0 | SW2-0-6 | 0 | C25 | DNP |  |  |  |  |  |  |  | 17.0
 |  |  |  |  |  |  |  |  |  |  |  |  | 17.0
90 | OPT J-1 | SW2-1-1 | 1 | SW2 | SQ-SEN-200 | 3.25x3.6 | OMNIDIRECTIONAL TILT AND VIBRATION SENSOR |  |  | SignalQuest | SQ-SEN-200-CTR |  | 17.0
91 | OPT J-1 | SW2-1-2 | 1 | R25 | 39K | 0603 |  | Carbon Film Resistor 39k OHM 1/16W 5% | Digi-Key | RHM39KGTR-ND | Rohm | MCR03EZPJ393 | 17.0
92 | OPT J-1 | SW2-1-3 | 1 | R26 | 10M | 0603 | Carbon Film Resistor 10M OHM 1/16W 5% | Digi-Key | RHM10MGCT-ND | Rohm | MCR03EZPJ106 |  | 17.0
93 | OPT J-1 | SW2-1-4 | 1 | C16 | 0.01 uF | 0603 | CAP 10000PF 50V CERAMIC X7R 0603 | Digi-Key | 399-1091-2-ND | Kermit | C0603C103K5RACTU |  | 17.0
94 | OPT J-1 | SW2-1-5 | 1 | D2 | 1N4148 | SOD123 | DIODE SWITCH 75V 500MW MINIMELF | Digi-Key | LL4148DICT-ND | Diodes, Inc. | LL4148-13 |  | 17.0
95 | OPT J-1 | SW2-1-5 | 1 | D3 | 1N4148 | SOD123 | DIODE SWITCH 75V 500MW MINIMELF | Digi-Key | LL4148DICT-ND | Diodes, Inc. | LL4148-13 |  | 17.0
96 | OPT J-1 | SW2-1-6 | 1 | C25 | 27 pF | 0603 | CAP CER 27PF 50V 5% C0G 0603 | Digi-Key | 490-1413-2-ND | Marata | GRM1885C1H270JA01D | Very Sensitive | 17.0
97 | OPT J-2 | SW2-1-6 | 1 | C25 | 0.01 uF | 0603 | CAP 10000PF 50V CERAMIC X7R 0603 | Digi-Key | 399-1091-2-ND | Kermit | C0603C103K5RACTU | Mid Sensitive | 17.0
98 | OPT J-3 | SW2-1-6 | 1 | C25 | 0.22 uF | 0603 | CAP .22UF 25V CERAMIC Y5V 0603 | Digi-Key | 399-1103-2-ND | Kermit | C0603C224Z3VACTU | Less Sensitive | 17.0
 |  |  |  |  |  |  |  |  |  |  |  |  | 17.0
99 | OPT K-0 | BAT-0-1 | 0 |  | DNP |  | B1 | No Battery |  |  |  |  | 17.0
 |  |  |  |  |  |  |  |  |  |  |  |  | 17.0
100 | OPT K-1 | BAT-1-2 | 1 |  |  |  | B1 | Battery |  | Renata | CR2032FV |  | 17.0
 |  |  |  |  |  |  |  |  |  |  |  |  | 17.0
101 | OPT L-0 | COL-0 | 0 | Enclosure | DNP |  |  |  |  |  |  |  | 17.0
 |  |  |  |  |  |  |  |  |  |  |  |  | 17.0
102 | OPT L-1 | COL-1 | 1 | Enclosure | White w/AWI logo |  |  |  |  |  |  |  | 17.0
 |  |  |  |  |  |  |  |  |  |  |  |  | 17.0
103 | OPT L-2 | COL-2 | 1 | Enclosure | Black w/ AWI logo |  |  |  |  |  |  |  | 17.0
 |  |  |  |  |  |  |  |  |  |  |  |  | 17.0
104 | OPT L-3 | COL-3 | 1 | Enclosure | Custom (logo, etc.) |  |  |  |  |  |  |  | 17.0
105 | OPT M-1 |  | 2 | C26,C27 | 15pF | 0603 | CAP CER 15PF 50V 5% C0G 0603 | Digi-Key | 490-1407-2-ND | Murata | GRM1885C1H150JA01D |  | 17.0
106 | OPT M-1 |  | 1 | R23 | 300K | 0603 | RES 300K OHM 1/10W 5% 0603 SMD | Digi-Key | RHM300KGTR-ND | Rohm | MCR03EZPJ304 |  | 17.0
107 | OPT M-3 |  | 1 | Y2 | SCP8-32.768KHZ TR | 1.5X3.2 Ceramic Watch | CRYSTAL 32.768KHZ 12.5PF SMD |  |  | Suntsu Frequency Control, Inc. | SCP8-32.768KHZ TR |  | 17.0
 |  |  |  | ALT |  |  | CRYSTAL 32.768KHZ 12.5PF SMD | Digi-Key | 535-9542-2-ND | Abracon | ABS07-32.768KHZ-T |  | 17.0
108 | BASIC |  | 0 | C22,C23 | DNP | 0603 |  |  |  |  |  |  | 17.0

Sheet: Sheet2
TAG-102-Rev20
06/02/2012 |  |  |  |  |  |  | 0.05 | Compact Tag REV20.0 Board
 |  |  |  |  |  |  | 0.00
Item # | Part Stat. | Option # | Qty-Sur | Part Ref. | Value | Part Size | Cost | Description | Dist. | Distributor P/N | Manufacturer | Manufacturer P/N | Note | Revision
1 | BASIC |  | 1 | C3 | 2.0pF +/- 0.25pF | 0603 | 0.05 | CAP CER 2.0PF 50V C0G 0603 | Digi-Key | 490-1379-2-ND | Murata | GRM1885C1H2R0CZ01D |  | 17.0
2 | BASIC |  | 1 | C20 | 15pF | 0603 | 0.05 | CAP CER 15PF 50V 5% C0G 0603 | Digi-Key | 490-1407-2-ND | Murata | GRM1885C1H150JA01D |  | 17.0
3 | BASIC |  | 2 | C12,C13 | 33pF | 0603 | 0.10 | CAP CER 33PF 50V 5% C0G 0603 | Digi-Key | 490-1415-2-ND | Murata | GRM1885C1H330JA01D |  | 17.0
4 | BASIC |  | 2 | C6,C14 | 100 pF | 0603 | 0.10 | CAP 100PF 50V CERAMIC | Digi-Key | 445-1281-2-ND | TDK Corp | C1608C0G1H101J |  | 17.0
5 | BASIC |  | 1 | C7 | 220 pF | 0603 | 0.05 | CAP CER 220PF 50V C0G 5% 0603 | Digi-Key | 445-1285-2-ND | TDK Corp | C1608C0G1H221J |  | 17.7
6 | BASIC |  | 2 | C8,C9 | 1000 pF | 0603 | 0.10 | CAP 1000PF 50V CERAMIC NP0 | Digi-Key | 399-1083-2-ND | Kemet | C0603C102J5RACTU |  | 17.0
7 | BASIC |  | 5 | C11,C15,C17,C18, C24 | 0.1 uF | 0603 | 0.25 | CAP .10UF 16V CERAMIC X7R | Digi-Key | 399-1100-2-ND | Kemet | C0603C104Z3VACTU |  | 17.0
8 | BASIC |  | 2 | R12,R13 | 10 | 0603 | 0.10 | Carbon Film Resistor 10 OHM 1/16W 5% | Digi-Key | RHM10GTR-ND | Rohm | MCR03EZPJ100 |  | 17.0
9 | BASIC |  | 1 | R6 | 22 ohm | 0603 | 0.05 | RES 22 OHM 1/10W 5% | Digi-Key | RHM22GTR-ND | Rohm | MCR03EZPJ220 |  | 17.0
10 | BASIC |  | 1 | R11 | 68 | 0603 | 0.05 | Carbon Film Resistor 68 OHM 1/16W 5% | Digi-Key | RHM68GTR-ND | Rohm | MCR03EZPJ680 |  | 17.0
11 | BASIC |  | 1 | R14 | 470 | 0603 | 0.05 | RES 470 OHM 1/10W 1% 0603 SMD | Digi-Key | RHM470HTR-ND | Rohm | MCR03EZPFX4700 | Change to 1% | 17.0
12 | BASIC |  | 1 | R18 | 1.0K | 0603 | 0.05 | RES 1.00K OHM 1/10W 1% 0603 SMD | Digi-Key | RHM1.00KHTR-ND | Rohm | MCR03EZPFX1001 |  | 17.0
13 | BASIC |  | 1 | R17 | 1.3K | 0603 | 0.05 | RES 1.30K OHM 1/10W 1% 0603 SMD | Digi-Key | RHM1.30KHTR-ND | Rohm | MCR03EZPFX1301 |  | 17.0
14 | BASIC |  | 1 | R19 | 2.0K | 0603 | 0.05 | RES 2.00K OHM 1/10W 1% 0603 SMD | Digi-Key | RHM2.00KHTR-ND | Rohm | MCR03EZPFX2001 | Change to 1% | 17.0
15 | BASIC |  | 1 | R20 | 2.7K | 0603 | 0.05 | Carbon Film Resistor 2.7K OHM 1/16W 5% | Digi-Key | RHM2.7KGTR-ND | Rohm | MCR03EZPJ272 |  | 17.0
16 | BASIC |  | 1 | R16 | 3.0K | 0603 | 0.05 | RES 3.00K OHM 1/10W 1% 0603 SMD | Digi-Key | RHM3.00KHTR-ND | Rohm | MCR03EZPFX3001 | Change to 1% | 17.0
16 | BASIC |  | 2 | R1,R8 | 4.7K | 0603 | 0.10 | Carbon Film Resistor 4.7K OHM 1/16W 5% | Digi-Key | RHM4.7KGTR-ND | Rohm | MCR03EZPJ472 |  | 17.0
17 | BASIC |  | 1 | R7 | 6.8K | 0603 | 0.05 | Carbon Film Resistor 6.8K OHM 1/16W 5% | Digi-Key | RHM6.8KGTR-ND | Rohm | MCR03EZPJ682 |  | 17.0
18 | BASIC |  | 1 | R15 | 36.5K | 0603 | 0.05 | RES 36.5K OHM 1/10W 1% 0603 SMD | Digi-Key | RHM36.5KHTR-ND | Rohm | MCR03EZPFX3652 |  | 17.0
19 | BASIC |  | 4 | R3,R5,R9,R10 | 39K | 0603 | 0.20 | Carbon Film Resistor 39k OHM 1/16W 5% | Digi-Key | RHM39KGTR-ND | Rohm | MCR03EZPJ393 |  | 17.0
20 | BASIC |  | 1 | R4 | 56.2K | 0603 | 0.05 | RES 56.2K OHM 1/10W 1% 0603 SMD | Digi-Key | RHM56.2KHTR-ND | Rohm | MCR03EZPFX5622 |  | 17.0
21 | BASIC |  | 1 | R24 | 150k | 0603 | 0.05 | RES 150K OHM 1/10W 1% 0603 SMD | RES 150K OHM 1/10W 1% 0603 SMD | Digi-Key | RHM150KHTR-ND | Rohm | MCR03EZPFX1503 | Change to 1% | 17.2
22 | BASIC |  | 1 | R21 | 220k | 0603 | 0.05 | RES 220K OHM 1/10W 1% 0603 SMD | Digi-Key | RHM220KHTR-ND | Rohm | MCR03EZPFX2203 | Change to 1% | 17.0
23 | BASIC |  | 1 | R2 | 1M | 0603 | 0.05 | Carbon Film Resistor 1M OHM 1/16W 5% | Digi-Key | RHM1.0MGTR-ND | Rohm | MCR03EZPJ105 |  | 17.0
24 | BASIC |  | 1 | L2 | 6.8nH | 0603 | 0.05 | INDUCTOR MULTILAYER 6.8NH 0603 | Digi-Key | 445-1490-2-ND | TDK Corporation | MLG1608B6N8D |  | 17.2
25 | BASIC |  | 1 | L4 | 12.0nH | 0603 | 0.05 | INDUCTOR 12NH 2% 0603 SMD | Digi-Key | PCD2003TR-ND | Panasonic | ELJ-RE12NGFA | New Parts compare to 105 | 17.0
26 | BASIC |  | 1 | L3 | 0.18uH | 0603 | 0.05 | INDUCTOR MULTILAYER 0.18 UH | Digi-Key | 445-1006-1-ND | TDK Corporation | MLF1608DR18K |  | 17.0
27 | BASIC |  | 1 | L6 | 100nH | 0603 | 0.05 | INDUCTOR 100NH 5% 0603 SMD | Digi-Key | PCD1985TR-ND | Panasonic-ECG | ELJ-RER10JFA |  | 17.7
28 | BASIC |  | 2 | Q1,Q2 | NE85619 | Ultra Super Mini Mold | 0.10 | TRANS NPN 1GHZ SMD | Digi-Key | NE85619-ATR-ND | NEC | NE85619-T1-A |  | 17.0
29 | BASIC |  | 1 | Q3 | 2N7002 | SOT-23 | 0.05 | IC TRANS N-CH 60V 7.5 OHM | Digi-Key | 2N7002NTR-ND | Fairchild | 2N7002NTR-ND |  | 17.0
30 | BASIC |  | 1 | U1 | PIC16F690 | 20SSOP | 0.05 | IC MCU FLASH 4KX14 EEPROM | Digi-Key | PIC16F690-I/SS-ND | Microchip | PIC16F690-I/SS |  | 17.0
31 | BASIC |  | 1 | U2 | MIC861 | SC-70-5 | 0.05 | IC OPAMP 400KHZ 2.7V ULT LP SC70 | Digi-Key | MIC861YC5TR-ND | Micrel | MIC861YC5TR |  | 17.0
32 | BASIC |  | 1 | U5 | TC1070VCT713 | SOT23A-5 | 0.05 | IC REG LDO ADJ 50MA |  |  | Microchip | TC1070VCT713 |  | 17.0
33 | BASIC |  | 1 | U6 | MAX9119EXK+ | SC70 | 0.05 | IC COMPARATOR BTR SC70-5 | Digi-Key | MAX9119EXK+T-ND | Maxim | MAX9119EXK+T |  | 17.0
34 | BASIC |  | 1 | B1A | Battery Holder |  | 0.15 | Battery Retainer | Keystone | C-5510-ACT | Keystone | C-5510-ACT |  | 17.0
35 | BASIC |  | 1 | B1B | Battery Contact |  | 0.15 | Battery Contact |  |  | Laird Technology | 0097-0488-02 |  | 17.0
35 | BASIC |  |  | PCB | PCB 102 |  | 0.00 | Compact Tag board |  |  | Active Sales |  |  | 17.0
36 | BASIC |  | 0 | J1,J2 | DNP | Mask it | 0.00 | NO SOLDER IN HOLES |  |  |  |  | NO SOLDER IN HOLES | 17.0
 |  |  |  |  |  |  | 0.00 |  |  |  |  |  |  | 17.0
37 | OPT1 |  | 1 | Y1 | 916.5 Resonator | 3.8x3.8mm | 0.05 | 916.5 MHz Saw Resonator | Richardson | RO2144D | RF Monolithics | RO2144D |  | 17.0
38 | OPT1 |  | 1 | C21 | 1.8pF +/- 0.25pF | 0603 | 0.05 | CAP CER 1.8PF 50V C0G 0603 | Digi-Key | 490-1378-2-ND | Murata | GRM1885C1H1R8CZ01D |  | 17.7
39 | OPT1 |  | 1 | C2 | 3.6pF +/- 0.25pF | 0603 | 0.05 | CAP CER 3.6PF 50V C0G 0603 | Digi-Key | 490-1385-2-ND | Murata | GRM1885C1H3R6CZ01D |  | 17.7
40 | OPT1 |  | 1 | C19 | 2.7pF +/-0.25pF | 0603 | 0.05 | CAP CER 2.7PF 50V C0G 0603 | Digi-Key | 490-1382-2-ND | Murata | GRM1885C1H2R7CZ01D |  | 17.7
 |  |  |  |  |  |  |  |  |  |  |  |  |  |  | 17.0
41 | OPT D-1 | TAM-1-1 | 1 | U7 | TLE4913 | SOT-23W | 0.05 | Low Power Hall Effect Switch | Arrow | TLE4913 | Infineon | TLE4913 |  | 17.0
42 | OPT D-1 | TAM-1-2 | 1 | C4 | 3.0pF +/- 0.25pF | 0603 | 0.05 | CAP CER 3.0PF 50V C0G 0603 | Digi-Key | 490-1383-2-ND | Murata | GRM1885C1H3R0CZ01D |  | 17.0
43 | OPT D-1 | TAM-1-3 | 1 | C1 | 0.1uF | 0603 | 0.05 | CAP .1UF 16V CERAMIC Y5V 0603 | Digi-Key | PCC1788CT-ND | Panasonic - ECG | ECJ-1VF1C104Z |  | 17.0
44 | OPT J-1 | SW2-1-1 | 1 | SW2 | SQ-SEN-200 | 3.25x3.6 | 0.05 | OMNIDIRECTIONAL TILT AND VIBRATION SENSOR |  |  | SignalQuest | SQ-SEN-200-CTR |  | 17.0
45 | OPT J-1 | SW2-1-2 | 1 | R25 | 39K | 0603 | 0.05 |  | Carbon Film Resistor 39k OHM 1/16W 5% | Digi-Key | RHM39KGTR-ND | Rohm | MCR03EZPJ393 | 17.0
46 | OPT J-1 | SW2-1-3 | 1 | R26 | 10M | 0603 | 0.05 | Carbon Film Resistor 10M OHM 1/16W 5% | Digi-Key | RHM10MGCT-ND | Rohm | MCR03EZPJ106 |  | 17.0
47 | OPT J-1 | SW2-1-4 | 1 | C16 | 0.01 uF | 0603 | 0.05 | CAP 10000PF 50V CERAMIC X7R 0603 | Digi-Key | 399-1091-2-ND | Kermit | C0603C103K5RACTU |  | 17.0
48 | OPT J-1 | SW2-1-5 | 1 | D2 | 1N4148 | SOD123 | 0.05 | DIODE SWITCH 75V 500MW MINIMELF | Digi-Key | LL4148DICT-ND | Diodes, Inc. | LL4148-13 |  | 17.0
49 | OPT J-1 | SW2-1-5 | 1 | D3 | 1N4148 | SOD123 | 0.05 | DIODE SWITCH 75V 500MW MINIMELF | Digi-Key | LL4148DICT-ND | Diodes, Inc. | LL4148-13 |  | 17.0
50 | OPT J-1 | SW2-1-6 | 1 | C25 | 27 pF | 0603 | 0.05 | CAP CER 27PF 50V 5% C0G 0603 | Digi-Key | 490-1413-2-ND | Marata | GRM1885C1H270JA01D | Very Sensitive | 17.0
51 | OPT J-2 | SW2-1-6 | 1 | C25 | 0.01 uF | 0603 | 0.05 | CAP 10000PF 50V CERAMIC X7R 0603 | Digi-Key | 399-1091-2-ND | Kermit | C0603C103K5RACTU | Mid Sensitive | 17.0
52 | OPT J-3 | SW2-1-6 | 1 | C25 | 0.22 uF | 0603 | 0.05 | CAP .22UF 25V CERAMIC Y5V 0603 | Digi-Key | 399-1103-2-ND | Kermit | C0603C224Z3VACTU | Less Sensitive | 17.0
