tourajghaffari/tigerfid/bom-files/tag/Tag-103 05-10-2011 REV 20-1.xls

Sheet: Sheet1
TAG-103-Rev20-1
11/12/2010 |  |  |  |  |  |  |  | Mini Tag REV18.0 Board
Item # | Part Stat. | Option # | Qty-Sur | Part Ref. | Value | Part Size |  | Description | Dist. | Distributor P/N | Manufacturer | Manufacturer P/N | Note | Revision
1 | BASIC |  | 1 | C3 | 2.0pF +/- 0.25pF | 0603 |  | CAP CER 2.0PF 50V C0G 0603 | Digi-Key | 490-1379-2-ND | Murata | GRM1885C1H2R0CZ01D |  | 16.0
2 | BASIC |  | 1 | C20 | 15pF | 0603 |  | CAP CER 15PF 50V 5% C0G 0603 | Digi-Key | 490-1407-2-ND | Murata | GRM1885C1H150JA01D |  | 16.0
3 | BASIC |  | 2 | C12,C13 | 33pF | 0603 |  | CAP CER 33PF 50V 5% C0G 0603 | Digi-Key | 490-1415-2-ND | Murata | GRM1885C1H330JA01D |  | 16.0
4 | BASIC |  | 2 | C6,C14 | 100 pF | 0603 |  | CAP 100PF 50V CERAMIC | Digi-Key | 445-1281-2-ND | TDK Corp | C1608C0G1H101J |  | 16.0
5 | BASIC |  | 1 | C7 | 220 pF | 0603 | CAP CER 220PF 50V C0G 5% 0603 | Digi-Key | 445-1285-2-ND | TDK Corp | C1608C0G1H221J |  | 17.7
5 | BASIC |  | 1 | C9 | 1000 pF | 0603 |  | CAP 1000PF 50V CERAMIC NP0 | Digi-Key | 399-1083-2-ND | Kemet | C0603C102J5RACTU |  | 16.0
6 | BASIC |  | 1 | C17 | 10000 pF | 0603 |  | CAP 10000PF 50V CERAMIC NP0 | Digi-Key | 399-1091-2-ND | Kemet | C0603C103K5RACTU |  | 17.0
7 | BASIC |  | 4 | C11,C15,C18, C24 | 0.1 uF | 0603 |  | CAP .10UF 16V CERAMIC X7R | Digi-Key | 399-1100-2-ND | Kemet | C0603C104Z3VACTU |  | 16.0
8 | BASIC |  | 0 | C22,C23 | DNP | 0603 |  |  |  |  |  |  |  | 16.0
9 | BASIC |  | 2 | R12,R13 | 10 | 0603 |  | Carbon Film Resistor 10 OHM 1/16W 5% | Digi-Key | RHM10GTR-ND | Rohm | MCR03EZPJ100 |  | 16.0
10 | BASIC |  | 1 | R6 | 22 ohm | 0603 |  | RES 22 OHM 1/10W 5% | Digi-Key | RHM22GTR-ND | Rohm | MCR03EZPJ220 |  | 16.0
11 | BASIC |  | 1 | R11 | 68 | 0603 |  | Carbon Film Resistor 68 OHM 1/16W 5% | Digi-Key | RHM68GTR-ND | Rohm | MCR03EZPJ680 |  | 16.0
12 | BASIC |  | 1 | R14 | 470 | 0603 |  | RES 470 OHM 1/10W 1% 0603 SMD | Digi-Key | RHM470HTR-ND | Rohm | MCR03EZPFX4700 | Change to 1% | 16.0
13 | BASIC |  | 1 | R18 | 1.0K | 0603 |  | RES 1.00K OHM 1/10W 1% 0603 SMD | Digi-Key | RHM1.00KHTR-ND | Rohm | MCR03EZPFX1001 |  | 16.0
14 | BASIC |  | 1 | R17 | 1.3K | 0603 |  | RES 1.30K OHM 1/10W 1% 0603 SMD | Digi-Key | RHM1.30KHTR-ND | Rohm | MCR03EZPFX1301 |  | 16.2
15 | BASIC |  | 1 | R19 | 2.0K | 0603 |  | RES 2.00K OHM 1/10W 1% 0603 SMD | Digi-Key | RHM2.00KHTR-ND | Rohm | MCR03EZPFX2001 | Change to 1% | 16.0
16 | BASIC |  | 1 | R20 | 2.7K | 0603 |  | Carbon Film Resistor 2.7K OHM 1/16W 5% | Digi-Key | RHM2.7KGTR-ND | Rohm | MCR03EZPJ272 |  | 16.0
17 | BASIC |  | 1 | R16 | 3.0K | 0603 |  | RES 3.00K OHM 1/10W 1% 0603 SMD | Digi-Key | RHM3.00KHTR-ND | Rohm | MCR03EZPFX3001 | Change to 1% | 16.0
17 | BASIC |  | 1 | R8 | 4.7K | 0603 |  | Carbon Film Resistor 4.7K OHM 1/16W 5% | Digi-Key | RHM4.7KGTR-ND | Rohm | MCR03EZPJ472 |  | 16.0
18 | BASIC |  | 1 | R7 | 6.8K | 0603 |  | Carbon Film Resistor 6.8K OHM 1/16W 5% | Digi-Key | RHM6.8KGTR-ND | Rohm | MCR03EZPJ682 |  | 16.0
19 | BASIC |  | 1 | R15 | 36.5K | 0603 |  | RES 36.5K OHM 1/10W 1% 0603 SMD | Digi-Key | RHM36.5KHTR-ND | Rohm | MCR03EZPFX3652 |  | 16.0
20 | BASIC |  | 6 | R1,R3,R4,R5,R9,R10 | 39K | 0603 |  | Carbon Film Resistor 39k OHM 1/16W 5% | Digi-Key | RHM39KGTR-ND | Rohm | MCR03EZPJ393 |  | 16.0
21 | BASIC |  | 1 | R24 | 150k | 0603 |  | RES 150K OHM 1/10W 1% 0603 SMD | Digi-Key | RHM150KHTR-ND | Rohm | MCR03EZPFX1503 | Change to 1% | 18.2
22 | BASIC |  | 1 | R21 | 220k | 0603 |  | RES 220K OHM 1/10W 1% 0603 SMD | Digi-Key | RHM220KHTR-ND | Rohm | MCR03EZPFX2203 | Change to 1% | 16.0
23 | BASIC |  | 1 | R2 | 1M | 0603 |  | Carbon Film Resistor 1M OHM 1/16W 5% | Digi-Key | RHM1.0MGTR-ND | Rohm | MCR03EZPJ105 |  | 16.0
24 | BASIC |  | 1 | L3 | 0.18uH | 0603 |  | INDUCTOR MULTILAYER 0.18 UH | Digi-Key | 445-1006-1-ND | TDK Corporation | MLF1608DR18K |  | 16.0
25 | BASIC |  | 1 | L6 | 100nH | 0603 |  | INDUCTOR 100NH 5% 0603 SMD | Digi-Key | PCD1985TR-ND | Panasonic-ECG | ELJ-RER10JFA |  | 18.5
26 | BASIC |  | 2 | Q1,Q2 | NE85619 | Ultra Super Mini Mold |  | TRANS NPN 1GHZ SMD | Digi-Key | NE85619-ATR-ND | NEC | NE85619-T1-A |  | 16.0
27 | BASIC |  | 1 | Q3 | 2N7002 | SOT-23 |  | IC TRANS N-CH 60V 7.5 OHM | Digi-Key | 2N7002NTR-ND | Fairchild | 2N7002NTR-ND |  | 16.0
 |  |  |  | ALT |  |  |  | IC TRANS N-CH 60V 7.5 OHM |  |  | ON Semi (Motorola) | 2N7002LT1 |  | 16.0
 |  |  |  | ALT |  |  |  | IC TRANS N-CH 60V 7.5 OHM |  |  | Phycomp/Yageo/Phillips | 2N7002 |  | 16.0
 |  |  |  | ALT |  |  |  | IC TRANS N-CH 60V 7.5 OHM |  |  | Siemens (Infineon) | 2N7002 |  | 16.0
 |  |  |  | ALT |  |  |  | IC TRANS N-CH 60V 7.5 OHM |  |  | Siliconix-Vishay-Temic | 2N7002 T&R |  | 16.0
28 | BASIC |  | 1 | U1 | PIC16F690 | 20SSOP |  | IC MCU FLASH 4KX14 EEPROM | Digi-Key | PIC16F690-I/SS-ND | Microchip | PIC16F690-I/SS |  | 16.0
29 | BASIC |  | 1 | U2 | MIC861 | SC-70-5 |  | IC OPAMP 400KHZ 2.7V ULT LP SC70 | Digi-Key | MIC861YC5TR-ND | Micrel | MIC861YC5TR |  | 16.0
30 | BASIC |  | 1 | U5 | TC1070VCT713 | SOT23A-5 |  | IC REG LDO ADJ 50MA |  |  | Microchip | TC1070VCT713 |  | 16.0
31 | BASIC |  | 1 | U6 | MAX9119EXK+ | SC70 |  | IC COMPARATOR BTR SC70-5 | Digi-Key | MAX9119EXK+T-ND | Maxim | MAX9119EXK+T |  | 16.0
32 | BASIC |  | 1 | B1A | Battery Holder |  |  | Battery Retainer | Keystone | C-5510-ACT | Keystone | C-5510-ACT |  | 16.0
33 | BASIC |  | 1 | B1B | Battery Contact |  |  | Battery Contact |  |  | Laird Technology | 0097-0488-02 |  | 16.0
33 | BASIC |  |  | PCB | PCB 102 |  |  | Compact Tag board |  |  | Active Sales |  |  | 16.0
34 | BASIC |  | 0 | J1 | DNP | Mask it |  | NO SOLDER IN HOLES |  |  |  |  | NO SOLDER IN HOLES | 16.0
35 | BASIC |  | 0 | E1,E2 | DNP | Mask it |  | NO SOLDER IN HOLES |  |  |  |  | NO SOLDER IN HOLES
36 | BASIC |  | 4 | J2,J3,J4,J5 | Mounting Pins |  |  | Mounting Pins | Digi-Key | ED8184-ND | Mil-Max | 0906-4-15-20-75-14-11-0
 |  |  |  |  |  |  |  |  |  |  |  |  |  | 16.0
37 | OPT0-0 |  | 0 | Y2 | SCP8-32.768KHZ TR | 1.5X3.2 Ceramic Watch |  | CRYSTAL 32.768KHZ 12.5PF SMD |  |  | Suntsu Frequency Control, Inc. | SCP8-32.768KHZ TR |  | 16.0
 |  |  |  | ALT |  |  |  | CRYSTAL 32.768KHZ 12.5PF SMD | Digi-Key | 535-9542-2-ND | Abracon | ABS07-32.768KHZ-T |  | 16.0
38 | OPT0-0 |  | 0 | C26,C27 | 15pF | 0603 |  | CAP CER 15PF 50V 5% C0G 0603 | Digi-Key | 490-1407-2-ND | Murata | GRM1885C1H150JA01D |  | 16.0
39 | OPT0-1 |  | 1 | Y2 | SCP8-32.768KHZ TR | 1.5X3.2 Ceramic Watch |  | CRYSTAL 32.768KHZ 12.5PF SMD |  |  | Suntsu Frequency Control, Inc. | SCP8-32.768KHZ TR |  | 16.0
 |  |  |  | ALT |  |  |  | CRYSTAL 32.768KHZ 12.5PF SMD | Digi-Key | 535-9542-2-ND | Abracon | ABS07-32.768KHZ-T |  | 16.0
40 | OPT0-1 |  | 2 | C26,C27 | 15pF | 0603 |  | CAP CER 15PF 50V 5% C0G 0603 | Digi-Key | 490-1407-2-ND | Murata | GRM1885C1H150JA01D |  | 16.0
41 | BASIC |  | 1 | R23 | 300K | 0603 |  | RES 300K OHM 1/10W 5% 0603 SMD | Digi-Key | RHM300KGTR-ND | Rohm | MCR03EZPJ304 |  | 16.0
41 | OPT1 |  | 1 | Y1 | 916.5 Resonator | 3.8x3.8mm |  | 916.5 MHz Saw Resonator | Richardson | RO2144D | RF Monolithics | RO2144D |  | 16.0
42 | OPT1 |  | 1 | C2 | 1.5pF +/- 0.25pF | 0603 |  | CAP CER 1.5PF 50V C0G 0603 | Digi-Key | 490-1376-2-ND | Murata | GRM1885C1H1R5CZ01D |  | 18.3
43 | OPT1 |  | 1 | C21 | 1.8pF +/- 0.25pF | 0603 |  | CAP CER 1.8PF 50V C0G 0603 | Digi-Key | 490-1378-2-ND | Murata | GRM1885C1H1R8CZ01D |  | 16.0
42 | OPT1 |  | 1 | C19 | 4.7pF +/- 0.25pF | 0603 |  | CAP CER 4.7PF 50V C0G 0603 | Digi-Key | 490-1389-2-ND | Murata | GRM1885C1H4R7CZ01D |  | 18.3
43 | OPT1 |  | 2 | C8,C10 | 1000 pF | 0603 |  | CAP 1000PF 50V CERAMIC NP0 | Digi-Key | 399-1083-2-ND | Kemet | C0603C102J5RACTU |  | 16.0
44 | OPT1 |  | 1 | L1,L2 | 5.6nH | 0603 |  | INDUCTOR 5.6NH +/-0.2NH 0603 | Digi-Key | 408-1034-2-ND | TDK Corporation | TFL0816-5N6 |  | 18.3
45 | OPT2 |  | 1 | Y1 | 868.95 Resonator | 3.8x3.8mm |  | 868.95 MHz Saw Resonator | Richardson | RO2156D | RF Monolithics | RO2156D |  | 16.0
46 | OPT2 |  | 1 | C21 | 1.8pF +/- 0.25pF | 0603 |  | CAP CER 1.8PF 50V C0G 0603 | Digi-Key | 490-1378-2-ND | Murata | GRM1885C1H1R8CZ01D |  | 16.0
47 | OPT2 |  | 1 | C2 | 2.4pF +/- 0.25pF | 0603 |  | CAP CER 2.4PF 50V C0G 0603 | Digi-Key | 490-1381-2-ND | Murata | GRM1885C1H2R4CZ01D |  | 18.5
48 | OPT2 |  | 1 | C19 | 4.7pF +/- 0.25pF | 0603 |  | CAP CER 4.7PF 50V C0G 0603 | Digi-Key | 490-1389-2-ND | Murata | GRM1885C1H4R7CZ01D |  | 18.3
49 | OPT2 |  | 1 | C8 | 10.0pF +/- 0.5pF | 0603 |  | CAP CER 10PF 50V 5% C0G 0603 | Digi-Key | 490-1403-2-ND | Murata | GRM1885C1H100JA01D |  | 18.4
50 | OPT2 |  | 2 | C10 | 1000 pF | 0603 |  | CAP 1000PF 50V CERAMIC NP0 | Digi-Key | 399-1083-2-ND | Kemet | C0603C102J5RACTU |  | 16.0
51 | OPT2 |  | 2 | L1,L2 | 5.6nH | 0603 |  | INDUCTOR 5.6NH +/-0.2NH 0603 | Digi-Key | 408-1034-2-ND | TDK Corporation | TFL0816-5N6 |  | 18.3
52 | OPT3 |  | 1 | Y1 | 927.2 Resonator | 3.8x3.8mm |  | 927.2 MHz Saw Resonator |  |  | SUNNY ELECTRONICS | SR-00927 |  | 16.0
53 | OPT3 |  | 1 | C21 | 1.8pF +/- 0.25pF | 0603 |  | CAP CER 1.8PF 50V C0G 0603 | Digi-Key | 490-1378-2-ND | Murata | GRM1885C1H1R8CZ01D |  | 16.0
54 | OPT3 |  | 1 | C2 | 2.7pF +/-0.25pF | 0603 |  | CAP CER 2.7PF 50V C0G 0603 | Digi-Key | 490-1382-2-ND | Murata | GRM1885C1H2R7CZ01D |  | 16.1
55 | OPT3 |  | 1 | C19 | 3.0pF +/- 2.5pF | 0603 |  | CAP CER 3.0PF 50V C0G 0603 | Digi-Key | 490-1383-2-ND | Murata | GRM1885C1H3R0CZ01D |  | $16.00
56 | OPT3 |  | 2 | C8,C10 | 1000 pF | 0603 |  | CAP 1000PF 50V CERAMIC NP0 | Digi-Key | 399-1083-2-ND | Kemet | C0603C102J5RACTU |  | 16.0
57 | OPT3 |  | 1 | L2 | 4.7nH | 0603 |  | INDUCTOR 4.7NH +/-0.2NH 0603 | Digi-Key | 408-1033-2-ND | TDK Corporation | TFL0816-4N7 |  | 16.3
58 | OPT3 |  | 1 | L1 | 5.6nH | 0603 |  | INDUCTOR 5.6NH +/-0.2NH 0603 | Digi-Key | 408-1034-2-ND | TDK Corporation | TFL0816-5N6 |  | 18.3
59 | OPT4 |  | 1 | Y1 | 867 Resonator | 3.8x3.8mm | 867 MHz Saw Resonator |  |  | SUNNY ELECTRONICS | SR-00867 |  |  | 16.0
60 | OPT4 |  | 1 | C2 | 2.4pF +/- 0.25pF | 0603 |  | CAP CER 2.4PF 50V C0G 0603 | Digi-Key | 490-1381-2-ND | Murata | GRM1885C1H2R4CZ01D |  | 18.5
61 | OPT4 |  | 1 | C19 | 4.7pF +/- 0.25pF | 0603 |  | CAP CER 4.7PF 50V C0G 0603 | Digi-Key | 490-1389-2-ND | Murata | GRM1885C1H4R7CZ01D |  | 18.3
62 | OPT4 |  | 1 | C21 | 1.8pF +/- 0.25pF | 0603 |  | CAP CER 1.8PF 50V C0G 0603 | Digi-Key | 490-1378-2-ND | Murata | GRM1885C1H1R8CZ01D |  | 16.0
63 | OPT4 |  | 1 | C8 | 10.0pF +/- 0.5pF | 0603 |  | CAP CER 10PF 50V 5% C0G 0603 | Digi-Key | 490-1403-2-ND | Murata | GRM1885C1H100JA01D |  | 18.4
64 | OPT4 |  | 2 | C10 | 2700 pF | 0603 | CAP CER 2700PF 50V X7R 0603 | CAP CER 2700PF 50V X7R 0603 | Digi-Key | C0603C272J5RACTU-ND | Kemet | C0603C272J5RACTU |  | 16.0
65 | OPT4 |  | 1 | L2 | 5.6nH | 0603 |  | INDUCTOR 5.6NH +/-0.2NH 0603 | Digi-Key | 408-1034-2-ND | TDK Corporation | TFL0816-5N6 |  | 18.3
66 | OPT4 |  | 1 | L1 | 15nH | 0603 |  | INDUCTOR 15NH +/-2% 0603 | Digi-Key | 408-1039-2-ND | TDK Corporation | TFL0816-15N |  | 18.3
67 | OPT D-0 | TAM-0-1 | 0 | U7 | DNP |  |  |  |  |  |  |  |  | 16.0
68 | OPT D-0 | TAM-0-2 | 0 | C4 | DNP |  |  |  |  |  |  |  |  | 16.0
69 | OPT D-0 | TAM-0-4 | 0 | C1 | DNP |  |  |  |  |  |  |  |  | 16.0
 |  |  |  |  |  |  |  |  |  |  |  |  |  | 16.0
70 | OPT D-1 | TAM-1-1 | 1 | U7 | TLE4913 | SOT-23W |  | Low Power Hall Effect Switch | Arrow | TLE4913 | Infineon | TLE4913 |  | 16.0
71 | OPT D-1 | TAM-1-2 | 1 | C4 | 3.0pF +/- 0.25pF | 0603 |  | CAP CER 3.0PF 50V C0G 0603 | Digi-Key | 490-1383-2-ND | Murata | GRM1885C1H3R0CZ01D |  | 16.4
72 | OPT D-1 | TAM-1-3 | 1 | C1 | 0.1uF | 0603 |  | CAP .1UF 16V CERAMIC Y5V 0603 | Digi-Key | PCC1788CT-ND | Panasonic - ECG | ECJ-1VF1C104Z |  | 16.0
 |  |  |  |  |  |  |  |  |  |  |  |  |  | 16.0
73 | OPT E-0 | MEM-0 | 0 | U4 | DNP |  |  |  |  |  |  |  |  | 16.0
 |  |  |  |  |  |  |  |  |  |  |  |  |  | 16.0
74 | OPT E-1 | MEM-1 | N/A | U4 | 1K Bit | 8-SOIC |  |  |  |  |  |  |  | 16.0
75 | OPT E-2 | MEM-2 | N/A | U4 | 2K Bits | 8-SOIC |  |  |  |  |  |  |  | 16.0
76 | OPT E-3 | MEM-3 | 1 | U4 | 4K Bits | 8-SOIC |  | 512 x 8 1.8V Serial EE |  |  | Microchip | 24AA04-I/SN |  | 16.0
77 | OPT E-4 | MEM-4 | N/A | U4 | 8K Bits | 8-SOIC |  |  |  |  |  |  |  | 16.0
78 | OPT E-5 | MEM-5 | N/A | U4 | 16K Bits | 8-SOIC |  |  |  |  |  |  |  | 16.0
79 | OPT E-6 | MEM-6 | N/A | U4 | 32K Bits | 8-SOIC |  |  |  |  |  |  |  | 16.0
80 | OPT E-7 | MEM-7 | N/A | U4 | 64K Bits | 8-SOIC |  |  |  |  |  |  |  | 16.0
81 | OPT E-8 | MEM-8 | N/A | U4 | 128K Bits | 8-SOIC |  |  |  |  |  |  |  | 16.0
82 | OPT E-9 | MEM-9 | 1 | U4 | 256K Bits | 8-SOIC |  | 32K x 8 1.8V serial EE |  |  | Microchip | 24AA256-I/SN |  | 16.0
 |  |  |  |  |  |  |  |  |  |  |  |  |  | 16.0
83 | OPT F-0 | LED-0-1 | 0 | D1 | DNP |  |  |  |  |  |  |  |  | 16.0
84 | OPT F-0 | LED-0-2 | 0 | R22 | DNP |  |  |  |  |  |  |  |  | 16.0
 |  |  |  |  |  |  |  |  |  |  |  |  |  | 16.0
85 | OPT G-0 | BUZ-0-1 | 0 | SP1 | DNP |  |  |  |  |  |  |  |  | 16.0
86 | OPT G-0 | BUZ-0-2 | 0 | Q4 | DNP |  |  |  |  |  |  |  |  | 16.0
87 | OPT G-0 | BUZ-0-3 | 0 | C5 | DNP |  |  |  |  |  |  |  |  | 16.0
 |  |  |  |  |  |  |  |  |  |  |  |  |  | 16.0
88 | OPT H-0 | TMP-0 | 0 | U3 | DNP |  |  |  |  |  |  |  |  | 16.0
 |  |  |  |  |  |  |  |  |  |  |  |  |  | 16.0
89 | OPT H-1 | TMP-1 | 1 | U3 | DS1631U | 8MSOP |  | Temperature Detector IC | Maxim | 90-1631U-TRL | Dallas Semiconductor | DS1631U/T&R |  | 16.0
90 | OPT I-0 | SW1-0-1 | 0 | SW1 | DNP |  |  |  |  |  |  |  |  | 17.0
 | OPT I-0 | SW1-0-2 | 0 | R26 | DNP |  |  |  |  |  |  |  |  | 17.0
91 | OPT I-1 | SW1-1-1 | 1 | SW1 | Switch | 8.51 mm |  | SWITCH TACT 6MM BK 160GF 8.51MM | Digi-Key | 450-1644-ND | Tyco Electronics (http://digikey.com/Suppliers/us/Tyco-Electronics-Alcoswitch.page?lang=EN) | FSM18JH |  | 17.0
 | OPT I-1 | SW1-1-1 | 1 | R26 | 39K | 0603 |  | Carbon Film Resistor 39k OHM 1/16W 5% | Digi-Key | RHM39KGTR-ND | Rohm | MCR03EZPJ393 |  | 17.0
90 | OPT J-0 | SW2-0-1 | 0 | SW2 | NA |  |  |  |  |  |  |  |  | 17.0
 |  |  |  |  |  |  |  |  |  |  |  |  |  | 17.0
91 | OPT K-0 | BAT-0-1 | 0 |  | DNP |  |  | B1 | No Battery |  |  |  |  | 17.0
 |  |  |  |  |  |  |  |  |  |  |  |  |  | 17.0
92 | OPT K-1 | BAT-1-2 | 1 |  |  |  |  | B1 | Battery |  | Renata | CR2032FV |  | 17.0
 |  |  |  |  |  |  |  |  |  |  |  |  |  | 17.0
93 | OPT L-0 | COL-0 | 0 | Enclosure | DNP |  |  |  |  |  |  |  |  | 17.0
 |  |  |  |  |  |  |  |  |  |  |  |  |  | 17.0
94 | OPT L-1 | COL-1 | 1 | Enclosure | White w/AWI logo |  |  |  |  |  |  |  |  | 17.0
 |  |  |  |  |  |  |  |  |  |  |  |  |  | 17.0
95 | OPT L-2 | COL-2 | 1 | Enclosure | Black w/ AWI logo |  |  |  |  |  |  |  |  | 17.0
 |  |  |  |  |  |  |  |  |  |  |  |  |  | 17.0
96 | OPT L-3 | COL-3 | 1 | Enclosure | Custom (logo, etc.) |  |  |  |  |  |  |  |  | 17.0
97 | OPT M-0 |  | 0 | Y2 | SCP8-32.768KHZ TR | 1.5X3.2 Ceramic Watch |  | CRYSTAL 32.768KHZ 12.5PF SMD |  |  | Suntsu Frequency Control, Inc. | SCP8-32.768KHZ TR |  | 16.0
 | OPT M-0 |  |  | ALT |  |  |  | CRYSTAL 32.768KHZ 12.5PF SMD | Digi-Key | 535-9542-2-ND | Abracon | ABS07-32.768KHZ-T |  | 16.0
98 | OPT M-0 |  | 0 | C26,C27 | 15pF | 0603 |  | CAP CER 15PF 50V 5% C0G 0603 | Digi-Key | 490-1407-2-ND | Murata | GRM1885C1H150JA01D |  | 16.0
99 | OPT M-0 |  | 1 | R23 | 300K | 0603 |  | RES 300K OHM 1/10W 5% 0603 SMD | Digi-Key | RHM300KGTR-ND | Rohm | MCR03EZPJ304 |  | 16.0
100 | OPT M-1 |  | 1 | Y2 | SCP8-32.768KHZ TR | 1.5X3.2 Ceramic Watch |  | CRYSTAL 32.768KHZ 12.5PF SMD |  |  | Suntsu Frequency Control, Inc. | SCP8-32.768KHZ TR |  | 16.0
 | OPT M-1 |  |  | ALT |  |  |  | CRYSTAL 32.768KHZ 12.5PF SMD | Digi-Key | 535-9542-2-ND | Abracon | ABS07-32.768KHZ-T |  | 16.0
101 | OPT M-1 |  | 2 | C26,C27 | 15pF | 0603 |  | CAP CER 15PF 50V 5% C0G 0603 | Digi-Key | 490-1407-2-ND | Murata | GRM1885C1H150JA01D |  | 16.0
102 | OPT M-1 |  | 1 | R23 | 300K | 0603 |  | RES 300K OHM 1/10W 5% 0603 SMD | Digi-Key | RHM300KGTR-ND | Rohm | MCR03EZPJ304 |  | 16.0

Sheet: Sheet2
TAG-103-Rev18.3 |  |  |  |  | TAG-102 REV 18.3 |  |  | 916 Version
11/12/2010 |  |  |  |  |  |  |  | Mini Tag REV18.0 Board | 0.06
Item # | Part Stat. | Option # | Qty-Sur | Part Ref. | Value | Part Size |  | Description | Dist. | Distributor P/N
1 | BASIC |  | 1 | C21 | 1.8pF +/- 0.25pF | 0603 | 0.06 | CAP CER 1.8PF 50V C0G 0603 | Digi-Key | 490-1378-2-ND
2 | BASIC |  | 1 | C3 | 2.0pF +/- 0.25pF | 0603 | 0.06 | CAP CER 2.0PF 50V C0G 0603 | Digi-Key | 490-1379-2-ND
3 | BASIC |  | 1 | C20 | 15pF | 0603 | 0.06 | CAP CER 15PF 50V 5% C0G 0603 | Digi-Key | 490-1407-2-ND
4 | BASIC |  | 2 | C12,C13 | 33pF | 0603 | 0.12 | CAP CER 33PF 50V 5% C0G 0603 | Digi-Key | 490-1415-2-ND
5 | BASIC |  | 3 | C6,C7,C14 | 100 pF | 0603 | 0.18 | CAP 100PF 50V CERAMIC | Digi-Key | 445-1281-2-ND
6 | BASIC |  | 2 | C9,C10 | 1000 pF | 0603 | 0.12 | CAP 1000PF 50V CERAMIC NP0 | Digi-Key | 399-1083-2-ND
7 | BASIC |  | 1 | C17 | 10000 pF | 0603 | 0.06 | CAP 10000PF 50V CERAMIC NP0 | Digi-Key | 399-1091-2-ND
8 | BASIC |  | 4 | C11,C15,C18, C24 | 0.1 uF | 0603 | 0.24 | CAP .10UF 16V CERAMIC X7R | Digi-Key | 399-1100-2-ND
9 | BASIC |  | 0 | C22,C23 | DNP | 0603 | 0.00
10 | BASIC |  | 2 | R12,R13 | 10 | 0603 | 0.12 | Carbon Film Resistor 10 OHM 1/16W 5% | Digi-Key | RHM10GTR-ND
11 | BASIC |  | 1 | R6 | 22 ohm | 0603 | 0.06 | RES 22 OHM 1/10W 5% | Digi-Key | RHM22GTR-ND
12 | BASIC |  | 1 | R11 | 68 | 0603 | 0.06 | Carbon Film Resistor 68 OHM 1/16W 5% | Digi-Key | RHM68GTR-ND
13 | BASIC |  | 1 | R14 | 470 | 0603 | 0.06 | RES 470 OHM 1/10W 1% 0603 SMD | Digi-Key | RHM470HTR-ND
14 | BASIC |  | 1 | R18 | 1.0K | 0603 | 0.06 | RES 1.00K OHM 1/10W 1% 0603 SMD | Digi-Key | RHM1.00KHTR-ND
15 | BASIC |  | 1 | R17 | 1.3K | 0603 | 0.06 | RES 1.30K OHM 1/10W 1% 0603 SMD | Digi-Key | RHM1.30KHTR-ND
16 | BASIC |  | 1 | R19 | 2.0K | 0603 | 0.06 | RES 2.00K OHM 1/10W 1% 0603 SMD | Digi-Key | RHM2.00KHTR-ND
17 | BASIC |  | 1 | R20 | 2.7K | 0603 | 0.06 | Carbon Film Resistor 2.7K OHM 1/16W 5% | Digi-Key | RHM2.7KGTR-ND
18 | BASIC |  | 1 | R16 | 3.0K | 0603 | 0.06 | RES 3.00K OHM 1/10W 1% 0603 SMD | Digi-Key | RHM3.00KHTR-ND
18 | BASIC |  | 1 | R8 | 4.7K | 0603 | 0.06 | Carbon Film Resistor 4.7K OHM 1/16W 5% | Digi-Key | RHM4.7KGTR-ND
19 | BASIC |  | 1 | R7 | 6.8K | 0603 | 0.06 | Carbon Film Resistor 6.8K OHM 1/16W 5% | Digi-Key | RHM6.8KGTR-ND
20 | BASIC |  | 1 | R15 | 36.5K | 0603 | 0.06 | RES 36.5K OHM 1/10W 1% 0603 SMD | Digi-Key | RHM36.5KHTR-ND
21 | BASIC |  | 6 | R1,R3,R4,R5,R9,R10 | 39K | 0603 | 0.36 | Carbon Film Resistor 39k OHM 1/16W 5% | Digi-Key | RHM39KGTR-ND
22 | BASIC |  | 1 | R24 | 150k | 0603 | 0.06 | RES 150K OHM 1/10W 1% 0603 SMD | Digi-Key | RHM150KHTR-ND
23 | BASIC |  | 1 | R21 | 220k | 0603 | 0.06 | RES 220K OHM 1/10W 1% 0603 SMD | Digi-Key | RHM220KHTR-ND
24 | BASIC |  | 1 | R2 | 1M | 0603 | 0.06 | Carbon Film Resistor 1M OHM 1/16W 5% | Digi-Key | RHM1.0MGTR-ND
25 | BASIC |  | 1 | L3 | 0.18uH | 0603 | 0.06 | INDUCTOR MULTILAYER 0.18 UH | Digi-Key | 445-1006-1-ND
26 | BASIC |  | 1 | L6 | 0.33uH | 0603 | 0.06 | INDUCTOR MULTILAYER 0.33UH 1608 | Digi-Key | 445-1009-2-ND
27 | BASIC |  | 2 | Q1,Q2 | NE85619 | Ultra Super Mini Mold | 0.12 | TRANS NPN 1GHZ SMD | Digi-Key | NE85619-ATR-ND
28 | BASIC |  | 1 | Q3 | 2N7002 | SOT-23 | 0.06 | IC TRANS N-CH 60V 7.5 OHM | Digi-Key | 2N7002NTR-ND
29 | BASIC |  | 1 | U1 | PIC16F690 | 20SSOP | 0.06 | IC MCU FLASH 4KX14 EEPROM | Digi-Key | PIC16F690-I/SS-ND
30 | BASIC |  | 1 | U2 | MIC861 | SC-70-5 | 0.06 | IC OPAMP 400KHZ 2.7V ULT LP SC70 | Digi-Key | MIC861YC5TR-ND
31 | BASIC |  | 1 | U5 | TC1070VCT713 | SOT23A-5 | 0.06 | IC REG LDO ADJ 50MA
32 | BASIC |  | 1 | U6 | MAX9119EXK+ | SC70 | 0.06 | IC COMPARATOR BTR SC70-5 | Digi-Key | MAX9119EXK+T-ND
33 | BASIC |  | 1 | B1A | Battery Holder |  | 0.06 | Battery Retainer | Keystone | C-5510-ACT
34 | BASIC |  | 0 | B1B | Battery Contact |  | 0.00 | Battery Contact
#REF! | BASIC |  | 3 | J2,J3,J4 | Mounting Pins |  | 0.18 | Mounting Pins | Digi-Key | ED8184-ND
#REF! | OPT1 |  | 1 | Y1 | 916.5 Resonator | 3.8x3.8mm | 0.06 | 916.5 MHz Saw Resonator | Richardson | RO2144D
#REF! | OPT1 |  | 1 | C2 | 1.5pF +/- 0.25pF | 0603 | 0.06 | CAP CER 1.5PF 50V C0G 0603 | Digi-Key | 490-1376-2-ND
#REF! | OPT1 |  | 1 | C19 | 4.7pF +/- 0.25pF | 0603 | 0.06 | CAP CER 4.7PF 50V C0G 0603 | Digi-Key | 490-1389-2-ND
#REF! | OPT1 |  | 1 | C8 | 1000 pF | 0603 | 0.06 | CAP 1000PF 50V CERAMIC NP0 | Digi-Key | 399-1083-2-ND
#REF! | OPT1 |  | 1 | L2 | 5.6nH | 0603 | 0.06 | INDUCTOR 5.6NH +/-0.2NH 0603 | Digi-Key | 408-1034-2-ND
#REF! | OPT1 |  | 1 | L1 | 5.6nH | 0603 | 0.06 | INDUCTOR 5.6NH +/-0.2NH 0603 | Digi-Key | 408-1034-2-ND
 |  |  |  |  |  |  | 0.00
#REF! | OPT D-1 | TAM-1-2 | 1 | C4 | 3.0pF +/- 0.25pF | 0603 | 0.06 | CAP CER 3.0PF 50V C0G 0603 | Digi-Key | 490-1383-2-ND
#REF! | OPT D-1 | TAM-1-3 | 1 | C1 | 0.1uF | 0603 | 0.06 | CAP .1UF 16V CERAMIC Y5V 0603 | Digi-Key | PCC1788CT-ND
 |  |  |  |  |  |  | 3.48

Sheet: Sheet3
TAG-103-Rev18.4 |  |  |  |  | TAG-102 REV 18.4 |  |  | 868 version
11/12/2010 |  |  |  |  |  |  |  | Mini Tag REV18.0 Board | 0.06
Item # | Part Stat. | Option # | Qty-Sur | Part Ref. | Value | Part Size |  | Description | Dist. | Distributor P/N
1 | BASIC |  | 1 | C21 | 1.8pF +/- 0.25pF | 0603 | 0.06 | CAP CER 1.8PF 50V C0G 0603 | Digi-Key | 490-1378-2-ND
2 | BASIC |  | 1 | C3 | 2.0pF +/- 0.25pF | 0603 | 0.06 | CAP CER 2.0PF 50V C0G 0603 | Digi-Key | 490-1379-2-ND
3 | BASIC |  | 1 | C20 | 15pF | 0603 | 0.06 | CAP CER 15PF 50V 5% C0G 0603 | Digi-Key | 490-1407-2-ND
4 | BASIC |  | 2 | C12,C13 | 33pF | 0603 | 0.12 | CAP CER 33PF 50V 5% C0G 0603 | Digi-Key | 490-1415-2-ND
5 | BASIC |  | 3 | C6,C7,C14 | 100 pF | 0603 | 0.18 | CAP 100PF 50V CERAMIC | Digi-Key | 445-1281-2-ND
6 | BASIC |  | 2 | C9,C10 | 1000 pF | 0603 | 0.12 | CAP 1000PF 50V CERAMIC NP0 | Digi-Key | 399-1083-2-ND
7 | BASIC |  | 1 | C17 | 10000 pF | 0603 | 0.06 | CAP 10000PF 50V CERAMIC NP0 | Digi-Key | 399-1091-2-ND
8 | BASIC |  | 4 | C11,C15,C18, C24 | 0.1 uF | 0603 | 0.24 | CAP .10UF 16V CERAMIC X7R | Digi-Key | 399-1100-2-ND
9 | BASIC |  | 0 | C22,C23 | DNP | 0603 | 0.00
10 | BASIC |  | 2 | R12,R13 | 10 | 0603 | 0.12 | Carbon Film Resistor 10 OHM 1/16W 5% | Digi-Key | RHM10GTR-ND
11 | BASIC |  | 1 | R6 | 22 ohm | 0603 | 0.06 | RES 22 OHM 1/10W 5% | Digi-Key | RHM22GTR-ND
12 | BASIC |  | 1 | R11 | 68 | 0603 | 0.06 | Carbon Film Resistor 68 OHM 1/16W 5% | Digi-Key | RHM68GTR-ND
13 | BASIC |  | 1 | R14 | 470 | 0603 | 0.06 | RES 470 OHM 1/10W 1% 0603 SMD | Digi-Key | RHM470HTR-ND
14 | BASIC |  | 1 | R18 | 1.0K | 0603 | 0.06 | RES 1.00K OHM 1/10W 1% 0603 SMD | Digi-Key | RHM1.00KHTR-ND
15 | BASIC |  | 1 | R17 | 1.3K | 0603 | 0.06 | RES 1.30K OHM 1/10W 1% 0603 SMD | Digi-Key | RHM1.30KHTR-ND
16 | BASIC |  | 1 | R19 | 2.0K | 0603 | 0.06 | RES 2.00K OHM 1/10W 1% 0603 SMD | Digi-Key | RHM2.00KHTR-ND
17 | BASIC |  | 1 | R20 | 2.7K | 0603 | 0.06 | Carbon Film Resistor 2.7K OHM 1/16W 5% | Digi-Key | RHM2.7KGTR-ND
18 | BASIC |  | 1 | R16 | 3.0K | 0603 | 0.06 | RES 3.00K OHM 1/10W 1% 0603 SMD | Digi-Key | RHM3.00KHTR-ND
18 | BASIC |  | 1 | R8 | 4.7K | 0603 | 0.06 | Carbon Film Resistor 4.7K OHM 1/16W 5% | Digi-Key | RHM4.7KGTR-ND
19 | BASIC |  | 1 | R7 | 6.8K | 0603 | 0.06 | Carbon Film Resistor 6.8K OHM 1/16W 5% | Digi-Key | RHM6.8KGTR-ND
20 | BASIC |  | 1 | R15 | 36.5K | 0603 | 0.06 | RES 36.5K OHM 1/10W 1% 0603 SMD | Digi-Key | RHM36.5KHTR-ND
21 | BASIC |  | 6 | R1,R3,R4,R5,R9,R10 | 39K | 0603 | 0.36 | Carbon Film Resistor 39k OHM 1/16W 5% | Digi-Key | RHM39KGTR-ND
22 | BASIC |  | 1 | R24 | 150k | 0603 | 0.06 | RES 150K OHM 1/10W 1% 0603 SMD | Digi-Key | RHM150KHTR-ND
23 | BASIC |  | 1 | R21 | 220k | 0603 | 0.06 | RES 220K OHM 1/10W 1% 0603 SMD | Digi-Key | RHM220KHTR-ND
24 | BASIC |  | 1 | R2 | 1M | 0603 | 0.06 | Carbon Film Resistor 1M OHM 1/16W 5% | Digi-Key | RHM1.0MGTR-ND
25 | BASIC |  | 1 | L3 | 0.18uH | 0603 | 0.06 | INDUCTOR MULTILAYER 0.18 UH | Digi-Key | 445-1006-1-ND
26 | BASIC |  | 1 | L6 | 100nH | 0603 |  | INDUCTOR 100NH 5% 0603 SMD | Digi-Key | PCD1985TR-ND | Panasonic-ECG | ELJ-RER10JFA
27 | BASIC |  | 2 | Q1,Q2 | NE85619 | Ultra Super Mini Mold | 0.12 | TRANS NPN 1GHZ SMD | Digi-Key | NE85619-ATR-ND
28 | BASIC |  | 1 | Q3 | 2N7002 | SOT-23 | 0.06 | IC TRANS N-CH 60V 7.5 OHM | Digi-Key | 2N7002NTR-ND
29 | BASIC |  | 1 | U1 | PIC16F690 | 20SSOP | 0.06 | IC MCU FLASH 4KX14 EEPROM | Digi-Key | PIC16F690-I/SS-ND
30 | BASIC |  | 1 | U2 | MIC861 | SC-70-5 | 0.06 | IC OPAMP 400KHZ 2.7V ULT LP SC70 | Digi-Key | MIC861YC5TR-ND
31 | BASIC |  | 1 | U5 | TC1070VCT713 | SOT23A-5 | 0.06 | IC REG LDO ADJ 50MA
32 | BASIC |  | 1 | U6 | MAX9119EXK+ | SC70 | 0.06 | IC COMPARATOR BTR SC70-5 | Digi-Key | MAX9119EXK+T-ND
33 | BASIC |  | 1 | B1A | Battery Holder |  | 0.06 | Battery Retainer | Keystone | C-5510-ACT
34 | BASIC |  | 1 | B1B | Battery Contact |  | 0.06 | Battery Contact
#REF! | BASIC |  | 3 | J2,J3,J4 | Mounting Pins |  | 0.18 | Mounting Pins | Digi-Key | ED8184-ND
 |  |  |  |  |  |  | 0.00
#REF! | OPT2 |  | 1 | Y1 | 868.95 Resonator | 3.8x3.8mm | 0.06 | 868.95 MHz Saw Resonator | Richardson | RO2156D
#REF! | OPT2 |  | 1 | C2 | 2.4pF +/- 0.25pF | 0603 |  | CAP CER 2.4PF 50V C0G 0603 | Digi-Key | 490-1381-2-ND | Murata | GRM1885C1H2R4CZ01D | 18.5
#REF! | OPT2 |  | 1 | C19 | 4.7pF +/- 0.25pF | 0603 | 0.06 | CAP CER 4.7PF 50V C0G 0603 | Digi-Key | 490-1389-2-ND
#REF! | OPT2 |  | 1 | C8 | 10.0pF +/- 0.5pF | 0603 | 0.06 | CAP CER 10PF 50V 5% C0G 0603 | Digi-Key | 490-1403-2-ND
#REF! | OPT2 |  | 1 | L2 | 5.6nH | 0603 | 0.06 | INDUCTOR 5.6NH +/-0.2NH 0603 | Digi-Key | 408-1034-2-ND
#REF! | OPT2 |  | 1 | L1 | 15nH | 0603 | 0.06 | INDUCTOR 15NH +/-2% 0603 | Digi-Key | 408-1039-2-ND
#REF! | OPT D-1 | TAM-1-2 | 1 | C4 | 3.0pF +/- 0.25pF | 0603 | 0.06 | CAP CER 3.0PF 50V C0G 0603 | Digi-Key | 490-1383-2-ND
#REF! | OPT D-1 | TAM-1-3 | 1 | C1 | 0.1uF | 0603 | 0.06 | CAP .1UF 16V CERAMIC Y5V 0603 | Digi-Key | PCC1788CT-ND
 |  |  |  |  |  |  | 3.42
