tourajghaffari/tigerfid/bom-files/tag/Tag-201-Brazil-05-14-2013.xlsx

TAG-201 Rev4 |  |  |  |  |  |  | Build 60,000
05/14/2013 |  |  |  |  |  | 0.04 | Seal Tag REV4.0 Board
 |  |  |  |  |  |  |  |  |  |  |  |  |  |  | 60000
Item # | Part Stat. | Qty-Sur | Part Ref. | Value | Part Size | assemble cost | Description | Dist. | Distributor P/N | Manufacturer | Manufacturer P/N | Unit Price Active Wave | Total Cost Active Wave | Assemble cost Serdia | Total cost for 60,000
1 | BASIC | 1 | C5 | 30pF | 0201 | $0.04 | CAP CER 30PF 25V 5% NP0 0201 | Digi-Key | 490-1254-2-ND | Murata | GRM0335C1E300JD01D | 0.003 | 0.0030 |  | $180.000
2 | BASIC | 1 | C6 | 68pF | 0201 | $0.04 | CAP CER 68PF 25V 5% NP0 0201 | Digi-Key | 490-3157-2-ND | Murata | GRM0335C1E680JD01D | 0.003 | 0.0030 |  | $180.000
3 | BASIC | 2 | C7,C8 | 7.5pF | 0201 | $0.08 | CAP CER 7.5PF 25V NP0 0201 | Digi-Key | 490-3138-2-ND | Murata | GRM0335C1E7R5DD01D | 0.003 | 0.0060 |  | $360.000
3 | BASIC | 3 | C1,C3,C4 | 10000 pF | 0201 | $0.12 | CAP CER 10000PF 16V 10% X7R 0201 | Digi-Key | 311-1404-2-ND | Yageo | CC0201KRX7R7BB103 | 0.003 | 0.0090 |  | $540.000
4 | BASIC | 1 | C2 | 0.1 uF | 0201 | $0.04 | CAP CER 0.1UF 6.3V Y5V 0201 | Digi-Key | 311-1413-2-ND | Kemet | CC0201ZRY5V5BB104 | 0.003 | 0.0030 |  | $180.000
5 | BASIC | 2 | R5,R6 | 3.9K | 0201 | $0.08 | RES 3.9K OHM 1/20W 5% 0201 SMD | Digi-Key | RHM3.9KAGTR-ND | Rohm | MCR006YZPJ392 | 0.0012 | 0.0024 |  | $144.000
6 | BASIC | 1 | R3 | 10k | 0201 | $0.04 | RES 10K OHM 1/20W 5% 0201 SMD | Digi-Key | RHM10KCCTR-ND | Rohm | MCR006YRTJ103 | 0.003 | 0.0030 |  | $180.000
7 | BASIC | 2 | L1,L2 | Ferrite Bead | 0201 | $0.08 | BEAD CORE 27 OHM 4A 0603 SMD | Digikey | P10436TR-ND | Panasonic-ECG | EXC-ML16A270U | 0.058 | 0.1160 |  | $6960.000
8 | BASIC | 1 | U1 | STM8L151F3U6 | 20-UFQFN | $0.04 | MCU 8BIT 8KB FLASH 20-UFQFPN | Digikey | 497-11495-2-ND | STMicroelectronics (http://digikey.com/Suppliers/us/STMicroelectronics.page?lang=EN) | STM8L151F3U6 | 0.8 | 0.8000 |  | $48000.000
9 | BASIC | 1 | U2 | M24LR16E | M24LR16E | $0.04 |  | Digikey |  | ST-Micro | M24LR16E | 0.52 | 0.5200 |  | $31200.000
10 | BASIC | 1 | Y1 | 32.768 |  | $0.04 | 32.768 K Crystal |  |  | Jauch | Q 0,032768-JTX310-12,5-20-LF | 0.32 | 0.3200 |  | $19200.000
11 | BASIC | 1 | BT1 | Battery Holder |  | $0.04 | HOLDER COIN CELL W/GOLD SMD | Digikey | BLP2032SM-GTr | MPD (Memory Protection Devices) (http://digikey.com/Suppliers/us/Memory-Protection-Devices.page?lang=EN) | BLP2032SM-GTR-ND | 0.35 | 0.3500 |  | $21000.000
12 | BASIC | 2 | J1,J2 | Mounting Pins |  | $0.08 | Mounting Pins | Digi-Key | ED90457TR-ND | Mill-Max | 0910-4-57-20-75-14-11-0 | 0.3 | 0.6000 |  | $36000.000
13 | BASIC | 1 |  | Board |  |  | Board |  |  |  |  | 0.16 | 0.1600 |  | $9600.000
14 | BASIC | 1 | Band | Mechanical |  |  | Band |  |  |  |  | 1.1 | 1.1000 |  | $66000.000
15 | BASIC | 2 | screw(2) | Mechanical |  |  | Miniature Triangular-Shank Screw for Plastic Zinc-Pltd STL, Torx, M1.4 Size, 6mm L, .45mm Pitch |  | 99397A114 (http://www.mcmaster.com/) | MCMaster | 99397A114 (http://www.mcmaster.com/) | 0.015 | 0.0300 |  | $1800.000
16 | BASIC | 1 | Rivet | Mechanical | Aluminum |  | Rivet |  |  |  |  | 0.05 | 0.0500 |  | $3000.000
17 | BASIC | 1 | Washer | Mechanical | Stainless steel |  | Washer ID 1/8" OD 5/16" Thickness 0.06"~0.08" |  |  |  |  | 0.02 | 0.0100 |  | $600.000
18 | BASIC | 1 | Housing | Housing |  |  | Housing |  |  |  |  | 0.45 | 0.4500 |  | $27000.000
19 | BASIC | 1 | Battery |  |  |  | Battery |  |  |  |  | 0.15 | 0.1500 |  | $9000.000
20 | BASIC | 1 | UHF Tag |  |  |  | UHF Tag |  |  |  |  | 0.15 | 0.1500 |  | $9000.000
21 | BASIC | 1 | USA Shipment |  |  |  | USA Shipment |  |  |  |  | 0.06 | 0.0600 |  | $3600.000
22 | BASIC | 1 | Assemble Board |  |  | $0.76 | Assemble Board |  |  |  |  | 0 | 0.0000 |  | $0.000
23 | BASIC | 1 | Testing |  |  |  | Testing |  |  |  |  |  |  |  | $0.000
24 | BASIC | 1 | Brazil Shipment |  |  |  | Brazil Shipment |  |  |  |  |  |  |  | $0.000
25 | BASIC | 1 | Taxes |  |  |  | Taxes |  |  |  |  |  |  |  | $0.000
 |  |  |  |  |  |  |  |  |  |  |  |  | 4.8954 |  | $293724.000
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
