tourajghaffari/tigerfid/bom-files/tag/Tag201-Rev-4- 03-20-2013- Serdia.xlsx

Sheet: Sheet1
TAG-201 Rev4 |  |  |  |  |  |  |  | Build 50,000
07/10/2012 |  |  |  |  |  |  |  | Seal Tag REV4.0 Board |  | 8
Item # | Part Stat. | Option # | Qty-Sur | Part Ref. | Value | Part Size | Unit Cost | Description | Dist. | Distributor P/N | Manufacturer | Manufacturer P/N | Note | Revision
1 | BASIC |  | 1 | C5 | 30pF | 0603 | 0.003 | CAP CER 30PF 50V 5% C0G 0603 | Digi-Key | 490-1414-2-ND | Murata | GRM1885C1H300JA01D |  | 4.0
2 | BASIC |  | 1 | C6 | 68pF | 0603 | 0.003 | CAP CER 68PF 50V 5% C0G 0603 | Digi-Key | 490-1423-2-ND | Murata | GRM1885C1H680JA01D |  | 4.0
3 | BASIC |  | 2 | C7,C8 | 7.5pF | 0603 | 0..03 | CAP CER 6.2PF 50V NP0 0603 | Digi-Key | 490-1398-2-ND (http://www.digikey.com/scripts/DKSearch/dksus.dll?Detail&itemSeq=121781314&uq=634874415337133725) | Murata | GRM1885C1H7R5DZ01D |  | 4.0
3 | BASIC |  | 3 | C1,C3,C4 | 10000 pF | 0603 | 0.002 | CAP 10000PF 50V CERAMIC NP0 | Digi-Key | 399-1091-2-ND | Kemet | C0603C103K5RACTU |  | 4.0
4 | BASIC |  | 1 | C2 | 0.1 uF | 0603 | 0.002 | CAP .10UF 16V CERAMIC X7R | Digi-Key | 399-1100-2-ND | Kemet | C0603C104Z3VACTU |  | 4.0
5 | BASIC |  | 2 | R5,R6 | 3.9K | 0603 | 0.0012 | RES 3.90K OHM 1/10W 1% 0603 SMD | Digi-Key | RHM3.90KHTR-ND | Rohm | MCR03EZPFX3901 |  | 4.0
6 | BASIC |  | 1 | R3 | 10k | 0603 | 0.0012 | RES 10.0K OHM 1/10W 1% 0603 SMD | Digi-Key | HM10.0KHTR-ND | Rohm | MCR03EZPFX1002 |  | 4.0
7 | BASIC |  | 2 | L1,L2 | Ferrite Bead | 0603 | 0.058 | BEAD CORE 27 OHM 4A 0603 SMD | Digikey | P10436TR-ND | Panasonic-ECG | EXC-ML16A270U |  | 4.0
8 | BASIC |  | 1 | U1 | STM8L151F3U6 | 20-UFQFN | 0.53 | MCU 8BIT 8KB FLASH 20-UFQFPN | Digikey | 497-11495-2-ND | STMicroelectronics (http://digikey.com/Suppliers/us/STMicroelectronics.page?lang=EN) | STM8L151F3U6 |  | 4.0
9 | BASIC |  | 1 | U2 |  | M24LR16E | 0.39 |  | Digikey |  | ST-Micro | M24LR16E |  | 4.0
10 | BASIC |  | 1 | Y1 | 32.768 |  | 0.25 | 32.768 K Crystal |  |  | Jauch | Q 0,032768-JTX310-12,5-20-LF |  | 4.0
11 | BASIC |  | 1 | BT1 | Battery Holder |  | 0.35 | HOLDER COIN CELL W/GOLD SMD | Digikey | BLP2032SM-GTr | MPD (Memory Protection Devices) (http://digikey.com/Suppliers/us/Memory-Protection-Devices.page?lang=EN) | BLP2032SM-GTR-ND |  | 4.0
12 | BASIC |  | 2 | J1,J2 | Mounting Pins |  | 0.20 | Mounting Pins | Digi-Key | ED90457TR-ND | Mill-Max | 0910-4-57-20-75-14-11-0 |  | 4.0
13 | BASIC |  | 1 |  | Board
14 | BASIC |  | 1 | Band | Mechanical |  | 1.2 |  |  |  |  |  |  | 4.0
15 | BASIC |  | 1 | screw(2) | Mechanical |  | 0.01288 | Miniature Triangular-Shank Screw for Plastic Zinc-Pltd STL, Torx, M1.4 Size, 6mm L, .45mm Pitch |  | 99397A114 (http://www.mcmaster.com/) | MCMaster | 99397A114 (http://www.mcmaster.com/) |  | 4.0
16 | BASIC |  | 1 | Rivet | Mechanical | Aluminum | 0.02 |  |  |  |  |  |  | 4.0
17 | BASIC |  | 1 | Washer | Mechanical | Stainless steel | 0.02 | Washer ID 1/8" OD 5/16" Thickness 0.06"~0.08" |  |  |  |  |  | 4.0
18 | BASIC |  | 1 | Assemble Board |  |  | 0.77
19 | BASIC |  | 1 | Testing |  |  | 0.5 |  |  |  |  |  |  |  | testing | testing | testing | testing | testing | testing | testing | testing | testing | testing | testing | testing | testing | testing | testing | testing | testing | testing | testing | testing | testing
 | Please give me your price for the items that I have price for you in column H
 | Aluminum rivets and mandrels are corrosion resistant and nonmagnetic.
 | Aluminum rivets with steel mandrels meet MIL-R-24243/1E wherever a dash number is shown. They are corrosion resistant and nonmagnetic.
 | Countersunk—Aluminum
 | Material | Lg. | Head | Head | Shear | Tensile | Pkg. |  | Pkg.
 | Thickness Range |  | Dia. (A) | Ht. (B) | Strength, lbs. | Strength, lbs. | Qty.
 | 1/8" Dia.—For Hole Size: 0.129"-0.133" (Drill Size #30)
 | 0.092"-0.125" | 0.275" | 0.233" | 0.031" | 120 | 150

Sheet: Sheet2
1 | GRM1885C1H300JA01D | CAP CER 30PF 50V 5% C0G 0603 | 1 | 0,003 | 0.003 | GRM1885C1H300JA01D
2 | GRM1885C1H680JA01D | CAP CER 68PF 50V 5% C0G 0603 | 1 | 0,003 | 0.003 | GRM1885C1H680JA01D
3 | GRM1885C1H7R5DZ01D | CAP CER 6.2PF 50V NP0 0603 | 2 | 0,006 | 0.003 | GRM1885C1H7R5DZ01D
4 | C0603C103K5RACTU | CAP 10000PF 50V CERAMIC NP0 | 3 | 0,009 | 0.002 | C0603C103K5RACTU
5 | C0603C104Z3VACTU | CAP .10UF 16V CERAMIC X7R | 1 | 0,003 | 0.002 | C0603C104Z3VACTU
6 | MCR03EZPFX3901 | RES 3.90K OHM 1/10W 1% 0603 SMD | 2 | 0,001 | 0.0012 | MCR03EZPFX3901
7 | MCR03EZPFX1002 | RES 10.0K OHM 1/10W 1% 0603 SMD | 1 | 0,023 | 0.0012 | MCR03EZPFX1002
8 | EXC-ML16A270U | BEAD CORE 27 OHM 4A 0603 SMD | 2 | 0,060 | 0.058 | EXC-ML16A270U
9 | STM8L151F3U6 | MCU 8BIT 8KB FLASH 20-UFQFPN | 1 | - | 0.53 | STM8L151F3U6
10 | M24LR16E | CI | 1 | 0,932 | 0.39 | M24LR16E
11 | Q 0,032768-JTX310-12,5-20-LF | 32.768 K Crystal | 1 | 0,300 | 0.25 | Q 0,032768-JTX310-12,5-20-LF
12 | BLP2032SM-GTR-ND | HOLDER COIN CELL W/GOLD SMD | 1 | 0,642 | 0.35 | BLP2032SM-GTR-ND
13 | 0910-4-57-20-75-14-11-0 | PINOS DE MONTAGEM | 2 | 1173 | 0.20 | 0910-4-57-20-75-14-11-0
14 | 99397A114 | PARAFUSO M1,4 L 6mm | 1 | 0,015
15 |  | ARRUELA ID 1/8 washer | 1 | 0,015 | 1.2
16 |  | ETIQUETA 2D | 1 | 0,010 | 0.01288 | 99397A114 (http://www.mcmaster.com/)
17 |  | MATERIAL DE SOLDAGEM | 1 | 0,025 | 0.02
18 |  | MATERIAL DE RECICLAGEM | 1 | 0,015 | 0.02
19 |  | PCI | 1 | 1155 | 0.77
20 |  | BAND MECHANICAL | 1 | - | 0.5
 | TOTAL |  |  | 4390
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
