tourajghaffari/tigerfid/bom-files/tag/Tag201-Rev-4- 4025-2012- Brazil.xlsx

Sheet: Sheet1
TAG-201 Rev4 |  |  |  |  |  |  |  | Build 1200
01/12/2012 |  |  |  |  |  |  | 0.04 | Seal Tag REV3.0 Board
Item # | Part Stat. | Option # | Qty-Sur | Part Ref. | Value | Part Size | cost | Description | Dist. | Distributor P/N |  | Manufacturer | Manufacturer P/N |  | Note | Revision
1 | BASIC |  | 1 | C5 | 30pF | 0603 | $0.04 | CAP CER 30PF 50V 5% C0G 0603 | Digi-Key | 490-1414-2-ND |  | Murata | GRM1885C1H300JA01D |  |  | 4.0
2 | BASIC |  | 1 | C6 | 68pF | 0603 | $0.04 | CAP CER 68PF 50V 5% C0G 0603 | Digi-Key | 490-1423-2-ND |  | Murata | GRM1885C1H680JA01D |  |  | 4.0
3 | BASIC |  | 2 | C7,C8 | 6.2pF | 0603 | $0.08 | CAP CER 6.2PF 50V NP0 0603 | Digi-Key | 490-1394-2-ND |  | Murata | GRM1885C1H6R2DZ01D |  |  | 4.0
3 | BASIC |  | 3 | C1,C3,C4 | 10000 pF | 0603 | $0.12 | CAP 10000PF 50V CERAMIC NP0 | Digi-Key | 399-1091-2-ND |  | Kemet | C0603C103K5RACTU |  |  | 4.0
4 | BASIC |  | 1 | C2 | 0.1 uF | 0603 | $0.04 | CAP .10UF 16V CERAMIC X7R | Digi-Key | 399-1100-2-ND |  | Kemet | C0603C104Z3VACTU |  |  | 4.0
5 | BASIC |  | 2 | R5,R6 | 3.9K | 0603 | $0.08 | RES 3.90K OHM 1/10W 1% 0603 SMD | Digi-Key | RHM3.90KHTR-ND |  | Rohm | MCR03EZPFX3901 |  |  | 4.0
6 | BASIC |  | 1 | R3 | 10k | 0603 | $0.04 | RES 10.0K OHM 1/10W 1% 0603 SMD | Digi-Key | HM10.0KHTR-ND |  | Rohm | MCR03EZPFX1002 |  |  | 4.0
7 | BASIC |  | 2 | L1,L2 | Ferrite Bead | 0603 | $0.08 | BEAD CORE 27 OHM 4A 0603 SMD | Digikey | P10436TR-ND |  | Panasonic-ECG | EXC-ML16A270U |  |  | 4.0
 |  |  |  |  |  | 0.603 | $0.01 | FERRITE CHIP 30 OHM 5A 0603 |  | 445-1562-2-ND |  | TDK Corporation | MPZ1608S300A
8 | BASIC |  | 1 | U1 | STM8L151F3U6 | 20-UFQFN | $0.04 | MCU 8BIT 8KB FLASH 20-UFQFPN | Digikey | 497-11495-2-ND |  | STMicroelectronics (http://digikey.com/Suppliers/us/STMicroelectronics.page?lang=EN) | STM8L151F3U6 |  |  | 4.0
9 | BASIC |  | 1 | U2 |  |  | $0.04 |  | Digikey |  |  | ST-Micro | M24LR16E |  |  | 4.0
10 | BASIC |  | 1 | Y1 | 32.768 |  | $0.04 | 32.768 K Crystal |  |  |  | Jauch | Q 0,032768-JTX310-12,5-20-LF |  |  | 4.0
11 | BASIC |  | 1 | BT1 | Battery Holder |  | $0.04 | HOLDER COIN CELL W/GOLD SMD | Digikey | BLP2032SM-GTr |  | MPD (Memory Protection Devices) (http://digikey.com/Suppliers/us/Memory-Protection-Devices.page?lang=EN) | BLP2032SM-GTR-ND |  |  | 4.0
12 | BASIC |  | 2 | J1,J2 | Mounting Pins |  | $0.08 | Mounting Pins | Digi-Key | ED90457TR-ND |  | Mill-Max | 0910-4-57-20-75-14-11-0 |  |  | 4.0
 |  |  | 2 |  | Screw |  |  | Miniature Triangular-Shank Screw for Plastic Zinc-Pltd STL, Torx, M1.4 Size, 6mm L, .45mm Pitch |  | 99397A114 (http://www.mcmaster.com/) |  | MCMaster | 99397A114 (http://www.mcmaster.com/)
#REF! | BASIC |  | 2 |  | Insert | 2 |  | 0-80 Insert Diameter: 0.1040 In. Hole Diameter: 0.0940 In. Drill Size: 3/32 | MSC Industrial Supply | 93442010 |  | E-Z Lok | 240-000-BR |  |  | 4.0
#REF! | BASIC |  | 1 |  | Eyelet | GS 4-3 (S-14) |  | S-14 Brass Eyelet | SISKA Inc | S-14 |  |  | GS 4-3 (S-14) |  |  | 4.0
#REF! | BASIC |  | 1 |  | washer | 820-W-BRASS |  | 820 Brass Washer | SISKA Inc | 820-W-BRASS |  |  |  |  |  | 4.0
 |  |  | 19 |  |  |  | 0.77
 |  |  |  |  |  |  | ED90457TR-ND | 0910-4-57-20-75-14-11-0 | jcasilli@mill-max.com
 |  |  |  |  | Board Assembly |  |  |  |  | 0.95 |  | 1.0925 | 11016 | 10465.2 | 12034.98
 |  |  |  |  | Bill of material |  |  |  |  | 1.37 |  | 1.5755 | 11016 | 15091.92 | 17355.708 | ordered
 |  |  |  |  | pin (2) |  | 0.27 |  |  | 0.54 |  | 0.621 | 23100 | 12474 | 14345.1 | not yet
 |  |  |  |  | Battery Holder |  |  |  |  | 0.27 |  | 0.3105 | 12000 | 3240 | 3726 | orderd
 |  |  |  |  | Board |  |  |  |  | 0.14 |  | 0.161 | 11016 | 1542.24 | 1773.576 | orderd
 |  |  |  |  | housing |  |  |  |  | 0.375 |  | 0.43125 | 12000 | 4500 | 5175 | orderd
 |  |  |  |  | Battey |  |  |  |  | 0.13 |  | 0.1495 | 10000 | 1300 | 1495
 |  |  |  |  | screw(2) |  | 0.0072 |  |  | 0.0144 |  | 0.01656 | 23000 | 331.2 | 380.88 | not yet
 |  |  |  |  | conductive washer |  |  |  |  | 0.22 |  | 0.253 | 12000 | 2640 | 3036 | not yet
 |  |  |  |  | Rivet |  |  |  |  | 0.00392 |  | 0.004508 | 12000 | 47.04 | 54.096 | not yet
 |  |  |  |  | Washer |  | 0.00196 |  |  | 0.00392 |  | 0.004508 | 12000 | 47.04 | 54.096 | not yet
 |  |  |  |  | Band |  |  |  |  | 1 |  | 1.15 | 11016 | 11016 | 12668.4 | not yet
 |  |  |  |  | testing |  |  |  |  | 0.75 |  | 0.8625 | 11016 | 8262 | 9501.3
 |  |  |  |  | Board |  |  |  |  | 0.15 |  | 0.1725
 |  |  |  |  | total |  |  |  |  | 5.91724 |  | 6.804826 | 0.887586 | 70956.64 | 81600.136
 |  |  |  |  |  | 0-42 * 3/16
 |  |  |  |  |  | 0-42 * 1/4
 |  | screw for housing without insert from CAMCAR 1-800-648-0462 www.Acument.com |  |  |  |  |  |  |  |  |  |  |  |  | 81600.136
 |  | 3BT-P8235-00
 |  | 3BT-P8236-00 |  | No | material |  | unit cost | total Number | Total Cost.
 |  |  |  | 1 | Bill of material |  | 1.5755 | 11016 | 17355.708
 |  |  |  | 2 | pin (2) |  | 0.621 | 23100 | 14345.1
 |  |  |  | 3 | Battery Holder |  | 0.3105 | 12000 | 3726
 |  |  |  | 4 | Board |  | 0.161 | 11016 | 1773.576
 |  |  |  | 5 | housing |  | 0.43125 | 12000 | 5175
 |  |  |  | 6 | screw(2) |  | 0.01656 | 23000 | 380.88 |  |  | 45900.456
 |  |  |  | 7 | conductive washer |  | 0.253 | 12000 | 3036
 |  |  |  | 8 | Rivet |  | 0.004508 | 12000 | 54.096
 |  |  |  | 9 | Washer |  | 0.004508 | 12000 | 54.096
 |  |  |  |  | Total Cost |  | 3.377826 |  | 45900.456
 |  |  |  | Board Assembly |  |  |  |  | 0.95 | 1.0925 |  | 11016 | 10465.2 | 12034.98
 |  |  |  | Bill of material |  |  |  |  | 1.37 | 1.5755 | 0 | 11016 | 15091.92 | 17355.708
 |  |  |  | pin (2) |  | 0.27 |  |  | 0.54 | 0.621 | 0.621 | 23100 | 12474 | 14345.1
 |  |  |  | Battery Holder |  |  |  |  | 0.27 | 0.3105 | 0.3105 | 12000 | 3240 | 3726
 |  |  |  | Board |  |  |  |  | 0.14 | 0.161 | 0.161 | 11016 | 1542.24 | 1773.576
 |  |  |  | housing |  |  |  |  | 0.375 | 0.43125 | 0.43125 | 12000 | 4500 | 5175
 |  |  |  | Battey |  |  |  |  | 0.13 | 0.1495 | 0.1495 | 10000 | 1300 | 1495
 |  |  |  | screw(2) |  | 0.0072 |  | 0.0112 | 0.0112 | 0.01288 | 0.01288 | 22000 | 246.4 | 283.36 |  | 0.01288
 |  |  |  | conductive washer |  |  |  |  | 0.22 | 0.253 | 0 | 12000 | 2640 | 3036
 |  |  |  | Rivet |  |  |  |  | 0.00392 | 0.004508 | 0.004508 | 12000 | 47.04 | 54.096
 |  |  |  | Washer |  | 0.00196 |  | 0.0045 | 0.0045 | 0.005175 | 0.005175 | 11000 | 49.5 | 56.925 |  | 0.005175
 |  |  |  | Band |  |  |  |  | 1 | 1.15 | 1.15 | 11016 | 11016 | 12668.4
 |  |  |  | testing |  |  |  |  | 0.75 | 0.8625 | 0 | 11016 | 8262 | 9501.3
 |  |  |  | STM8L151F3U6 |  |  |  |  | 0.57 | 0.6555 | 0.6555
 |  |  |  | M24LR16E |  |  |  |  | 0.35 | 0.4025 | 0.4025
 |  |  |  | 32.768 |  |  |  |  | 0.3 | 0.345 | 0.345
 |  |  |  | total |  |  |  |  | 4.12462 | 4.743313 | 3.627813 | 0.618693 | 32843.18 | 37769.657
 |  |  | No |  |  | unit cost | total Number | Total Cost.
 |  |  | 1 |  |  | 1.0925 | 11016 | 12034.98
 |  |  | 2 |  |  | 1.5755 | 11016 | 17355.708
 |  |  | 3 | material |  | 0.621 | 23100 | 14345.1
 |  |  | 4 | Board Assembly |  | 0.3105 | 12000 | 3726
 |  |  | 5 | Bill of material |  | 0.161 | 11016 | 1773.576
 |  |  | 6 | pin (2) |  | 0.43125 | 12000 | 5175
 |  |  | 7 | Battery Holder |  | 0.1495 | 10000 | 1495
 |  |  | 8 | Board |  | 0.01656 | 23000 | 380.88
 |  |  | 9 | housing |  | 0.253 | 12000 | 3036
 |  |  | 10 | Battey |  | 0.004508 | 12000 | 54.096
 |  |  | 11 | screw(2) |  | 0.004508 | 12000 | 54.096
 |  |  | 12 | conductive washer |  | 1.15 | 11016 | 12668.4
 |  |  | 13 | Rivet |  | 0.05 | 11016 | 550.8
 |  |  |  | Washer |  | 0.022
 |  |  |  | Band |  | 6.632326 |  | 72649.636
 |  |  |  | testing
 |  |  |  | total

Sheet: Sheet2
No | material | unit cost | total Number | Total Cost.
1 | Bill of material | 1.5755 | 11016 | $17355.71
2 | pin (2) | 0.621 | 23100 | $14345.10 | part for tester | 1148.11
3 | Battery Holder | 0.3105 | 12000 | $3726.00
4 | Board | 0.161 | 11016 | $1773.58
5 | housing | 0.43125 | 12000 | $5175.00
6 | screw(2) | 0.01288 | 22000 | $283.36
7 | conductive washer | 0.253 | 12000 | $3036.00
8 | Rivet | 0.004508 | 12000 | $54.10
9 | Washer | 0.005175 | 11000 | $56.92
10 | tester design | 2500 | 1 | $2500.00
11 | Programming setup | 2500 | 1 | $2500.00
 | Total Cost | 3.374813 |  | $50805.76

Sheet: Sheet3
No | material | unit cost | total Number | Total Cost. | No | material | unit cost | total Number | Total Cost.
1 | Board Assembly | 1.0925 | 11016 | 12034.98 | 1 | Board Assembly | 0 | 11016 | 0
2 | Bill of material | 1.5755 | 11016 | 17355.708 | 2 | Bill of material | 1.5755 | 11016 | 17355.708
3 | pin (2) | 0.621 | 23100 | 14345.1 | 3 | pin (2) | 0.621 | 23100 | 14345.1
4 | Battery Holder | 0.3105 | 12000 | 3726 | 4 | Battery Holder | 0.3105 | 12000 | 3726
5 | Board | 0.161 | 11016 | 1773.576 | 5 | Board | 0.161 | 11016 | 1773.576
6 | housing | 0.43125 | 12000 | 5175 | 6 | housing | 0.43125 | 12000 | 5175
7 | Battey | 0.1495 | 10000 | 1495 | 7 | Battey | 0.1495 | 10000 | 1495
8 | screw(2) | 0.01288 | 22000 | 283.36 | 8 | screw(2) | 0.01288 | 22000 | 283.36
9 | conductive washer | 0.253 | 12000 | 3036 | 9 | conductive washer | 0.253 | 12000 | 3036
10 | Rivet | 0.02 | 11000 | 220 | 10 | Rivet | 0.02 | 11000 | 220
11 | Washer | 0.005175 | 11000 | 56.925 | 11 | Washer | 0.005175 | 11000 | 56.925
12 | Band | 1.15 | 11016 | 12668.4 | 12 | Band | 1.15 | 11016 | 12668.4
 |  |  |  |  | 13 | screw(2) | 0.01288
 |  |  |  |  | 14 | conductive washer | 0
 |  |  |  |  | 15 | Rivet | 0.02
 |  |  |  |  | 16 | Washer | 0.005
13 | testing and finish product. | 0.8625 | 11016 | 9501.3 | 17 | testing and finish product. | 0 | 11016 | 0
 | total | 6.632326 |  | 81671.349 |  | total | 4.727685 |  | 60135.069
14 | tester design | 2500 | 1 | $2500.00
15 | Programming setup | 2500 | 1 | $2500.00
 | Total Cost | 5000 |  | $5000.00
 | Total Cost |  |  | $86671.35

Sheet: Sheet4
 | 2 |  | Screw |  | Miniature Triangular-Shank Screw for Plastic Zinc-Pltd STL, Torx, M1.4 Size, 6mm L, .45mm Pitch |  | 99397A114 (http://www.mcmaster.com/) | MCMaster | 99397A114 (http://www.mcmaster.com/)
 | 2 |  | Insert | 2 | 0-80 Insert Diameter: 0.1040 In. Hole Diameter: 0.0940 In. Drill Size: 3/32 | MSC Industrial Supply | 93442010 | E-Z Lok | 240-000-BR
 | 1 |  | Eyelet | GS 4-3 (S-14) | S-14 Brass Eyelet | SISKA Inc | S-14 |  | GS 4-3 (S-14)
 | 1 |  | washer | 820-W-BRASS | 820 Brass Washer | SISKA Inc | 820-W-BRASS
Item # | Part Stat. | Option # | Qty-Sur | Part Ref. | Value | Part Size | cost | Description | Dist. | Distributor P/N | Manufacturer | Manufacturer P/N | Note | Revision
