tourajghaffari/tigerfid/bom-files/field-generator/sensor-fgen/FGN 01-09-2012 REV8.1.xlsx

Sheet: Sheet1
FGN ASM-Sen-8.1
1/9/2012
Field Generator Rev 8.1
Item # |  | Part Status | Qty. | Part Ref. | Value | Part Size | Description | Dist. | Distributor P/N | Manufacturer | Manufacturer P/N | Notes | Revision
1 |  | Basic | 1 | C31 | 100pF | 0603 | CAP 100PF 50V CERAMIC | Digi-Key | 445-1281-2-ND | TDK Corp | C1608C0G1H101J |  | 8
2 |  | Basic | 6 | C2,C13, C21, C27, C28, C29, C30 | 0.1 uF | 0603 | CAP .10UF 25V CERAMIC Y5V 0603 | Digi-Key | 399-1100-2-ND | Kemet | C0603C104Z3VACTU |  | 8
3 |  | Basic | 1 | C22 | 1 uF | 0805 | CAP CER 1UF 50V Y5V 0805 | Digi-Key | 490-3903-2-ND | Murata | GRM21BF51H105ZA12L |  | 8
4 |  | Basic | 2 | C11, C16 | 2.2uF 16V | CT3216 | CAPACITOR TANT 2.2UF 16V 10%, CASE A, SMD | Digi-Key | 399-3691-2-ND | Kemet | T491A225K016AT |  | 8
5 |  | Basic | 1 | C17 | 10 uF 35V | 0603 | CAP CER 10UF 10V 20% X5R 0603 | Digi-Key | 445-6853-1-ND | TDK Corporation (http://digikey.com/Suppliers/us/TDK.page?lang=EN) | C1608X5R1A106M |  | 8 | change the layout
6 |  | Basic | 2 | R6,R29 | 330 | 0603 | RES 220 OHM 1/10W 5% 0603 SMD | Digi-Key | RHM220GTR-ND | Rohm | MCR03EZPJ221 |  | 8
7 |  | Basic | 3 | R8, R10, R14 | 2.2K | 0603 | RES 2.2K OHM 1/10W 5% 0603 SMD | Digi-Key | RHM2.2KGTR-ND | Rohm | MCR03EZPJ222 |  | 8
8 |  | Basic | 2 | R15,R21,R23 | 10K | 0603 | RES 10K OHM 1/10W 5% 0603 SMD | Digikey | RHM10KGTR-ND | Rohm | MCR03EZPJ103 |  | 8
9 |  | Basic | 1 | R16 | 52.3K | 0603 | RES 52.3K OHM 1/10W 1% 0603 SMD | Digikey | RHM52.3KHTR-ND | Rohm | MCR03EZPFX5232 |  | 8
10 |  | Basic | 2 | FB2, FB3 | Ferrite Bead | 0603 | BEAD CORE 27 OHM 4A 0603 SMD | Digi-Key | P10436CT-ND | Panasonic-ECG | EXC-ML16A270U |  | 8
11 |  | Basic | 1 | L8 | 100nH | 0603 | INDUCTOR 100NH 5% 0603 SMD | Digi-Key | PCD1985TR-ND | Panasonic-ECG | ELJ-RER10JFA |  | 8
12 |  | Basic | 1 | L6 | 10 uH | 3.00mm x 3.00mm | INDUCTOR 10UH 20% SMD | Digi-Key | 587-1635-2-ND | Taiyo Yuden (http://digikey.com/Suppliers/us/Taiyo-Yuden.page?lang=EN) | NR3010T100M |  | 8
13 |  | Basic | 1 | D5 | Red LED | LED-T1 3mm | LED, RADIAL | Ptec | PL01CDR24 | Ptec | PL01CDR24 |  | 8
14 |  |  |  |  |  | LED-T1 3mm | LED RED DIFFUSED 3MM ROUND | Digi-Key | P563-ND | Panasonic | LN28RPX |  | 8
15 |  | Basic | 1 | D4 | TRANSORB | DO-214AA (SMB) | SIDACTOR BI 25V 150A DO-214AA | Digi-Key | P0300SALRPTR-ND | Teccor Electronics Inc. (Sidactor) (http://www.digikey.com/scripts/Redirect/Redirect.dll?R=9&V=53) | P0300SALRP |  | 8
16 |  | Basic | 1 | D2 | Green LED | LED-T1 3mm | LED, RADIAL | Ptec | PL01-CDG-13 | Ptec | PL01-CDG-13 |  | 8
17 |  |  |  |  |  | LED-T1 3mm | LED GREEN DIFFUSED 3MM ROUND | Digikey | P564-ND | Panasonic | LN38GPX |  | 8
17 |  | Basic | 1 | D6 | 1N4148 | SOD123 | DIODE SWITCH 75V 500MW MINIMELF | Digi-Key | LL4148DICT-ND | Diodes, Inc. | LL4148-13 |  | 8
 |  | Basic | 2 | D1 | SCHOTTKY Diod | SOD-323, SC-76 | SCHOTTKY RECT 40V 0.5A SOD323 | Digi-Key | PMEG4005AEA T/R-ND | NXP-Semiconductors | PMEG4005AEA T/R |  | 8
18 |  | Basic | 1 | D12 | S1AB | DO-214AA (SMB) | DIODE FAST REC 50V 1A SMB | Digi-Key | RS1AB-FDITR-ND | Diodes, Inc. | RS1AB-13-F |  | 8
19 |  | Basic | 1 | Q1 | 2N3906 | SOT-23 | TRANS GP PNP -40V -200MA SOT-23 | Digi-Key | FMMT3906TR-ND | Zetex, Inc. | FMMT3906TA |  | 8
20 |  | Basic | 1 | Q3 | 2N3904 | SOT-23 | TRANS GP NPN 40V 200MA SOT-23 | Digi-Key | FMMT3904TR-ND | Zetex, Inc. | FMMT3904TA |  | 8
21 |  | Basic | 1 | U1 |  | SMU_DFN8 | IC REG STP DWN 500MA 8-DFN | Digi-key | LT3502AIDC#TRMPBFCT-ND | Linear Technology (http://digikey.com/Suppliers/us/Linear-Technology.page?lang=EN) | LT3502AIDC#TRMPBF |  | 8
22 |  | Basic | 1 | U5 | PIC16F690 | 20SSOP | IC MCU FLASH 4KX14 EEPROM | Digi-Key | PIC16F690-I/SS-ND | Microchip | PIC16F690-I/SS |  | 8
23 |  | Basic | 1 | U6 | MAX202 | SO-16 | IC TRANSCEIVER RS232 5V 16-SOIC | Arrow | MAX202CSE | Maxim | MAX202CSE |  | 8
24 |  | Basic | 1 | J2 | Pwr Connector | 2.1mm | CONN POWER JACK 2.1X5.5MM SMD | Digi-Key | CP-002APJTR-ND | CUI, Inc. | PJ-002A-SMT-1 |  | 8
25 |  | Basic | 0 | J3,J6 | DNP |  | 1x5 Header |  |  |  |  | Mask the HOLES | 8
26 |  | Basic | 1 | J4 | RJ11 | 6-6 modular | CONN MODULE 6-6 UNSHIELD SLEEVE | Digi-Key | CCM9002-ND | Corcom/Tyco | RJ11-6L-S | Please mask J6 holes | 8
27 |  | Basic | 1 | PCB |  |  |  |  |  | Active PCB | FGN-RAW-REV5 |  | 8
28 |  | Basic | 2 | Screw |  |  | SHEET MTL SCREW NO. 4 X 1/2"L, FLAT HD PHIL, ZINC PLTD STEEL |  |  | McMaster | 90048A110 |  | 8
29 |  | Basic | 1 | J9 | CONN HEADER RT ANG 2POS | 3.5mm | MC1,5/2-G-3,5 | Sager | 52285 | Phoenix Contact | 1844210 |  | 8
30 |  | Basic | 1 | J9A | Screw Type Plug 2POS | 3.5mm | MC1,5/2-ST-3,5 | Sager | 52229 | Phoenix Contact | 1840366 |  | 8
31 |  | Basic | 1 | F1 | 0451.200MRL | Surface Mount (0.240 X 0.106) | FUSE .200A 125V FAST NANO2 SMD | Digi-Key | 0451.200MRL-ND | Littelfuse Inc | 0451.200MRL |  | 8
32 | OPTD-0 | 433 MHZ | 0 | C3,C5,C6,C7,C8,C9,C10,C12,C14,C15,C18,C19,C20,C37,R1,R2,R3,R4,R5,R7,R9,R11,R17,R18,R19,R20,R22,L1,L2,L3,L4,L9,L10,L11,Q2,Q4,Q5,Q6,U2,Y2,J5,J8 | DNP |  |  |  |  |  |  |  | 8
33 | OPTD-1 | 433 MHz | 1 | C8 | 2.0 pF | 0603 | CAP CER 2.0PF, +/-0.25PF 50V C0G 0603 | Digi-Key | 490-1379-2-ND | Murata | GRM1885C1H2R0CZ01D |  | 8
34 | OPTD-1 | 433 MHz | 1 | C19,C10 | 5.0 pF | 0603 | CAP CER 5.0PF, +/-0.25PF, 50V C0G 0603 | Digi-Key | 490-1390-2-ND | Murata | GRM1885C1H5R0CZ01D |  | 8
35 | OPTD-1 | 433 MHz | 4 | C9 | 47pF | 0603 | CAP CER 47PF 50V C0G 5% 0603 | Digi-Key | 445-1277-2-ND | TDK Corp | C1608C0G1H470J |  | 8
36 | OPTD-1 | 433 MHz | 5 | C3, C5, C6, C7,C18 | 100pF | 0603 | CAP 100PF, 5%, 50V, COG, CERAMIC | Digi-Key | 445-1281-2-ND | TDK Corp | C1608C0G1H101J |  | 8
37 | OPTD-1 | 433 MHz | 3 | C20,C26,C32 | 0.1uF | 0603 | CAP .10UF 25V -20%, +80% CERAMIC Y5V 0603 | Digi-Key | 399-1100-2-ND | Kemet | C0603C104Z3VACTU |  | 8
38 | OPTD-1 | 433 MHz | 1 | C12 | 4.7uF 16V | CT3216 | CAPACITOR TANT 4.7UF 16V 10%, CASE A, SMD | Digi-Key | 399-3697-2-ND | Kemet | T491A475K016AT |  | 8
39 | OPTD-1 | 433 MHz | 1 | R17 | 10 | 0603 | RES 10 OHM 1/10W 5% 0603 SMD | Digi-Key | RHM10GTR-ND | Rohm | MCR03EZPJ100 |  | 8
40 | OPTD-1 | 433 MHz | 1 | R7 | 22 | 0603 | RES 22 OHM 1/10W 5% | Digi-Key | RHM22GTR-ND | Rohm | MCR03EZPJ220 |  | 8
41 | OPTD-1 | 433 MHz | 2 | R20,R22 | 180 | 0603 | RES 180 OHM 1/10W 5% 0603 SMD | Digikey | RHM180GTR-ND | Rohm | MCR03EZPJ181 |  | 8
42 | OPTD-1 | 433 MHz | 2 | R11,R24 | 1K | 0603 | RES 1.0K OHM 1/10W 5% 0603 SMD | Digikey | RHM1.0KGTR-ND | Rohm | MCR03EZPJ102 |  | 8
43 | OPTD-1 | 433 MHz | 1 | R4 | 2.2K | 0603 | RES 2.2K OHM 1/10W 5% 0603 SMD | Digi-Key | RHM2.2KGTR-ND | Rohm | MCR03EZPJ222 |  | 8
44 | OPTD-1 | 433 MHz | 1 | R19 | 2.7K | 0603 | RES 2.7K OHM 1/10W 5% 0603 SMD | Digi-Key | RHM2.7KGTR-ND | Rohm | MCR03EZPJ272 |  | 8
45 | OPTD-1 | 433 MHz | 2 | R18,R25 | 3.3K | 0603 | RES 3.3K OHM 1/10W 5% 0603 SMD | Digi-Key | RHM3.3KGTR-ND | Rohm | MCR03EZPJ332 |  | 8
46 |  | 433 MHz | 1 | R26 | 5.6k | 0603 | RES 5.6K OHM 1/10W 5% 0603 SMD | Digi-Key | RHM5.6KGTR-ND | Rohm | MCR03EZPJ562 |  | 8
47 | OPTD-1 | 433 MHz | 2 | R1, R2 | 4.7K | 0603 | RES 4.7K OHM 1/10W 5% 0603 SMD | Digi-Key | RHM4.7KGTR-ND | Rohm | MCR03EZPJ472 |  | 8
48 | OPTD-1 | 433 MHz | 1 | R5 | 6.8K | 0603 | RES 6.8K OHM 1/10W 5% 0603 SMD | Digikey | RHM6.8KGTR-ND | Rohm | MCR03EZPJ682 |  | 8
49 | OPTD-1 | 433 MHz | 1 | R3 | 8.2k | 0603 | RES 8.2K OHM 1/10W 5% 0603 SMD | Digi-Key | RHM4.7KGTR-ND | Rohm | MCR03EZPJ822 |  | 8
50 | OPTD-1 | 433 MHz | 1 | R9 | 10K POT | 9mm Squared | POT 10K OHM SQ CERMET SIDE | Digi-Key | CT94EZ103-ND | copal-electronics | CT94EZ103 |  | 8
51 | OPTD-1 | 433 MHz | 1 | L1 | 6.8nH | 0603 | INDUCTOR 6.8NH 5% 0603 SMD | Digi-Key | PCD1971TR-ND | Panasonic | ELJ-RE6N8JFA |  | 8
52 | OPTD-1 | 433 MHz | 1 | L9 | 47nH | 0603 | INDUCTOR 47NH 5% 0603 SMD | Digi-Key | PCD1981TR-ND | Panasonic-ECG | ELJ-RE47NJFA |  | 8
53 | OPTD-1 | 433 MHz | 2 | L2,L3 | 100nH | 0603 | INDUCTOR 100NH 5% 0603 SMD | Digi-Key | PCD1985TR-ND | Panasonic-ECG | ELJ-RER10JFA |  | 8
54 | OPTD-1 | 433 MHz | 1 | Q4 | 2N3906 | SOT-23 | TRANS GP PNP -40V -200MA SOT-23 | Digi-Key | FMMT3906TR-ND | Zetex, Inc. | FMMT3906TA |  | 8
55 | OPTD-1 | 433 MHz | 2 | Q2,Q6 | BFR193 | SOT23 | TRANSISTOR RF NPN 12V SOT-23 | Digi-Key | BFR 193 E6327-ND | Infineon | BFR 193 E6327 |  | 8
56 | OPTD-1 | 433 MHz | 1 | Q5 | 2N3904 | SOT-23 | TRANS GP NPN 40V 200MA SOT-23 | Digi-Key | FMMT3904TR-ND | Zetex, Inc. | FMMT3904TA |  | 8
57 | OPTD-1 | 433 MHz | 1 | U2 | AT-113 | SO8 | 3 Volt Voltage Variable Absorptive Attenuator | Future | 6219539 | MCM | AT-113TR |  | 8
58 | OPTD-1 | 433 MHz | 2 | Shunt (J5,J8) | 2 Position |  | SHUNT, ECON, PHBR 5AU, BLACK | Digi-Key | A26228-ND | AMP/Tyco | 382811-8 |  | 8
59 | OPTD-1 | 433 MHz | 1 | J5 | 1X3 Header |  | CONN HEADER .100 SINGL STR 36POS | Digi-Key | S1011E-36-ND | Sullins Elec. | PBC36SAAN | One of these Sullins parts makes 12 3-pin headers | 8
60 | OPTD-1 | 433 MHz | 1 | J8 | 1X2 Header |  | CONN HEADER .100 SINGL STR 36POS | Digi-Key | S1011E-36-ND | Sullins Elec. | PBC36SAAN | One of these Sullins parts makes 18 2-pin headers | 8
61 |  |  |  |  |  |  |  |  |  |  |  |  | 8
62 | OPTD-11 | 433 MHz | 1 | C37 | 3.0 pF | 0603 | CAP CER 3.0PF,+/-0.25PF, 50V C0G 0603 | Digi-Key | 490-1383-2-ND | Murata | GRM1885C1H3R0CZ01D |  | 8
63 | OPTD-11 | 433 MHz | 1 | C15 | 10pF | 0603 | CAP CER 10PF 50V 5% C0G 0603 | Digi-Key | 490-1403-2-ND | Murata | GRM1885C1H100JA01D |  | 8
64 | OPTD-11 | 433 MHz | 1 | C10 | 5.0 pF | 0603 | CAP CER 5.0PF, +/-0.25PF, 50V C0G 0603 | Digi-Key | 490-1390-2-ND | Murata | GRM1885C1H5R0CZ01D |  | 8
65 | OPTD-1 | 433 MHz | 1 | C14 | 7.0pF | 0603 | CAP CER 7.0PF, +/-0.5PF 50V C0G 0603 | Digi-Key | 490-1397-2-ND | Murata | GRM1885C1H7R0DZ01D |  | 8
65 | OPTD-11 | 433 MHz | 1 | L11 | 6.8nH | 0603 | INDUCTOR 6.8NH 5% 0603 SMD | Digi-Key | PCD1971TR-ND | Panasonic | ELJ-RE6N8JFA |  | 8
66 | OPTD-11 | 433 MHz | 1 | L4 | 22nH | 0603 | INDUCTOR 22NH 5% 0603 SMD | Digi-Key | PCD1977TR-ND | Panasonic | ELJ-RE22NJFA |  | 8
67 | OPTD-11 | 433 MHz | 1 | L10 | 330nH | 0603 | INDUCTOR MULTILAYER 0.33UH 1608 | Digi-Key | 445-1009-2-ND | TDK Corporation | MLF1608DR33K |  | 8
68 | OPTD-11 | 433 MHz | 1 | Y2 | 433.92MHz | 3.8 X 3.8 MM | 40 dB, 0.5-2.0 GHz | RF Monolithics | RO2101D | RF Monolithics | RO2101D |  | 8
69 |  |  |  |  |  |  |  |  |  |  |  |  | 8
70 | OPTD12 | 335 MHz |  | C37 | 2.2 PF | 0603 | CAP CER 2.2PF 50V C0G 0603 | Digi-Key | 490-1380-2-ND | Murata | GRM1885C1H2R2CZ01D |  | 8
71 | OPTD12 | 335 MHz | 1 | C15 | 5 pF | 0603 | CAP CER 5.0PF 50V C0G 0603 | Digi-Key | 490-1390-2-ND | Murata | GRM1885C1H5R0CZ01D |  | 8
72 | OPTD12 | 335 MHz | 1 | C14 | 18.0pF +/- 0.50pF | 0603 | CAP CER 18PF 50V 5% C0G 0603 | Digi-Key | 490-1409-2-ND | Murata | GRM1885C1H180JA01D |  | 8
72 | OPTD12 | 335 MHz |  | C10 | 100 pF | 0603 | CAP CER 100PF 50V 5% C0G 0603 | Digi-Key | 490-1427-2-ND | Murata | GRM1885C1H101JA01D |  | 8
73 | OPTD12 | 335 MHz | 1 | L4 | 15 nH | 0603 | INDUCTOR 15NH 5% 0603 SMD | Digi-Key | PCD1975TR-ND | Panasonic | ELJ-RE15NJFA |  | 8
74 | OPTD12 | 335 MHz | 1 | L11 | 22 nH | 0603 | INDUCTOR 22NH 5% 0603 SMD | Digi-Key | PCD1977TR-ND | Panasonic | ELJ-RE22NJFA |  | 8
75 | OPTD12 | 335 MHz | 1 | L10 | 220 nH | 0603 | INDUCTOR MULTILAYER 0.33UH 1608 | Digi-Key | 445-1007-2-ND | TDK Corporation | MLF1608DR22K |  | 8
76 | OPTD12 | 335 MHz | 1 | Y2 | 335 Mhz | 3.8 X 3.8 MM | Saw Resonator SMD (3.8x3.8mm) | Sunny USA | SR-00335 | Sunny USA | SR-00335 |  | 8
77 |  |  |  |  |  |  |  |  |  |  |  |  | 8
78 | OPTD-1 | OPTM-2 | 1 | Enclouser | Box-ENC-102-2110100 |  | Box 12cm x 6.9cm x 2.5cm, Black Color, ActiveWave Logo,Hole in Top Left Position Option, Hole in Top Right, Hole on Left Side,No Two Ultrasonic holes on the Top Right, No hole on the Right Side |  |  | Advanced Data Access Inc/ ActiveWave Inc | Box-ENC-102-2110100 |  | 8
79 | OPTD-1 | OPTM-3 | 1 | Enclouser | Box-ENC-102-3110100 |  | Box 12cm x 6.9cm x 2.5cm, Silver Color, ActiveWave Logo,Hole in Top Left Position Option, Hole in Top Right, Hole on Left Side,No Two Ultrasonic holes on the Top Right, No hole on the Right Side |  |  | Advanced Data Access Inc/ ActiveWave Inc | Box-ENC-102-3110100 |  | 8
80 | OPTD-1 | OPTM-4 | 1 | Enclouser | Box-ENC-102-4110100 |  | Box 12cm x 6.9cm x 2.5cm, Beige Color, ActiveWave Logo,Hole in Top Left Position Option, Hole in Top Right, Hole on Left Side,No Two Ultrasonic holes on the Top Right, No hole on the Right Side |  |  | Advanced Data Access Inc/ ActiveWave Inc | Box-ENC-102-4110100 |  | 8
81 | OPTD-1 | OPTM-5 | 1 | Enclouser | Box-ENC-102-5110100 |  | Box 12cm x 6.9cm x 2.5cm, Custom Color, ActiveWave Logo,Hole in Top Left Position Option, Hole in Top Right, Hole on Left Side,No Two Ultrasonic holes on the Top Right, No hole on the Right Side |  |  | Advanced Data Access Inc/ ActiveWave Inc | Box-ENC-102-5110100 |  | 8
82 |  |  |  |  |  |  |  |  |  |  |  |  | 8
83 | OPTE-0 | 433-EXT-ANT | 0 | J7 | DNP |  |  |  |  |  |  |  | 8
84 | OPTE-1 | 433-EXT-ANT | 1 | J7 | PCB Mount | SMA Reverse | CONNECTOR RPSMA PCB MOUNT | Digi-Key | CONREVSMA001-ND | Linx Tech. | CONREVSMA001 |  | 8
85 | OPTE-1 | 433-EXT-ANT | 1 | J7-Antenna | 50 OHM ANT | SMA Reverse | ANTENNA 433MHZ 1/4 WAVE WHIP | Digi-Key | ANT-433-CW-HD-ND | Linx Tech. | ANT-433-CW-HD | OPTION J-3 OR OPTION K-3? | 8
86 |  |  |  |  |  |  |  |  |  |  |  |  | 8
87 | OPTF-0 | INT Sensor | 0 | C54,C55,C56,C57,C58,C59,C60,C61,C62,R13,R47,R51,R53,R54,R55,R57,R58,L16,L17,Q7,U3,SEN1,SEN2,P1,P2,J1 | DNP |  |  |  |  |  |  |  | 8
88 | OPTF-1 | INT Sensor | 1 | C55 | 47pF | 0603 | CAP CER 47PF 50V C0G 5% 0603 | Digi-Key | 445-1277-2-ND | TDK Corp | C1608C0G1H470J |  | 8
89 | OPTF-1 | INT Sensor | 1 | C58 | 0.01uF | 0603 | CAP CERM .01UF 10% 50V X7R 0603 | Digi-Key | 478-1227-2-ND | AVX Corporation (http://www.digikey.com/scripts/Redirect/Redirect.dll?R=9&V=478) | 06035C103KAT2A |  | 8
90 | OPTF-1 | INT Sensor | 3 | C56,C57,C62 | 0.1uF | 0603 | CAP .10UF, -20/+80%, 25V ,CERAMIC Y5V 0603 | Digi-Key | 399-1100-2-ND | Kemet | C0603C104Z3VACTU |  | 8
91 | OPTF-1 | INT Sensor | 1 | C54 | 1 uF | 0603 | CAP CER 1.0UF 25V X7R 10% 0603 | Digi-Key | 445-5956-2-ND | Kemet | C1608X7R1E105K |  | 8
92 | OPTF-1 | INT Sensor | 2 | C1,C61 | 1 uF 50V | 0805 | CAP CER 1UF, -20/+80%, 50V Y5V 0805 | Digi-Key | 490-3903-2-ND | Murata | GRM21BF51H105ZA12L |  | 8
93 | OPTF-1 | INT Sensor | 1 | C59 | 10 uF 35V | 6032-28 (EIA) | CAP TANTALUM 10UF 35V 20%, CASE C, SMD | Digi-Key | 495-2285-2-ND | Kemet | B45196H6106M309 |  | 8
94 | OPTF-1 | INT Sensor | 1 | R31 | 0 | 0603 | RES 0.0 OHM 1/10W 0603 SMD | Digikey | RHM0.0GTR-ND | Rohm | MCR03EZPJ000 |  | 8
95 | OPTF-1 | INT Sensor | 5 | R13,R54,R55,R57,R58 | 1K | 0603 | RES 1.0K OHM 1/10W 5% 0603 SMD | Digikey | RHM1.0KGTR-ND | Rohm | MCR03EZPJ102 |  | 8
96 | OPTF-1 | INT Sensor | 1 | R47 | 4.7K | 0603 | RES 4.7K OHM 1/10W 5% 0603 SMD | Digi-Key | RHM4.7KGTR-ND | Rohm | MCR03EZPJ472 |  | 8
97 | OPTF-1 | INT Sensor | 4 | R30 | 10K | 0603 | RES 10K OHM 1/10W 5% 0603 SMD | Digikey | RHM10KGTR-ND | Rohm | MCR03EZPJ103 |  | 8
98 | OPTF-1 | INT Sensor | 1 | RV2 | 10K POT | 9mm Squared | POT 10K OHM SQ CERMET SIDE | Digi-Key | CT94EZ103-ND | copal-electronics | CT94EZ103 |  | 8
97 | OPTF-1 | INT Sensor | 1 | R51 | 100K | 0603 | RES 100K OHM 1/10W 5% 0603 SMD | Digi-Key | RHM100KGCT-ND | Rohm | MCR03EZPJ104 |  | 8
98 | OPTF-1 | INT Sensor | 2 | L16,L17 | Ferrite Bead | 0603 | BEAD CORE 27 OHM 4A 0603 SMD | Digi-Key | P10436CT-ND | Panasonic-ECG | EXC-ML16A270U |  | 8
99 | OPTF-1 | INT Sensor | 1 | Q7 | FMMT491ATC | SOT-23 | TRANSISTOR NPN MED PWR SOT23 | Digi-Key | FMMT491ATC-ND | Zetex Inc | FMMT491ATC |  | 8
100 | OPTF-1 | INT Sensor | 1 | U4 | CY8C27243 | SSOP20 | IC MCU 16K FLSH 256B SRAM 20SSOP | Digi-Key | 428-1594-ND | Cypress SemiconductorCorp | CY8C27243-24PVXI |  | 8
101 | OPTF-1 | INT Sensor | 1 | SENS1 | 40T-16P | ULTRASONIC SENSOR | Ceramic Transponder 40T-16P |  |  | CERAMIC TRANSDUCER DESIGN CO., LTD | 40T-16P |  | 8
102 | OPTF-1 | INT Sensor | 1 | SENS2 | 40R-16P | ULTRASONIC SENSOR | Ceramic Transponder 40R-16P |  |  | CERAMIC TRANSDUCER DESIGN CO., LTD | 40R-16P |  | 8
103 | OPTF-1 | INT Sensor | 0 | P1 | DNP |  |  |  |  |  |  | Mask the HOLES, S/B DNP | 8
104 | OPTF-1 | INT Sensor | 0 | P2 | DNP |  |  |  |  |  |  | Mask the HOLES, S/B DNP | 8
105 | OPTF-1 | OPTM-2 | 1 | Enclouser | Box-ENC-102-2110111 |  | Box 12cm x 6.9cm x 2.5cm, Black Color, ActiveWave Logo,Hole in Top Left Position Option, No Hole in Top Right, Hole on Left Side, Two Ultrasonic holes on the Top Right, Hole on the Right Side |  |  | Advanced Data Access Inc/ ActiveWave Inc | Box-ENC-102-2110111 |  | 8
106 | OPTF-1 | OPTM-3 | 1 | Enclouser | Box-ENC-102-3110111 |  | Box 12cm x 6.9cm x 2.5cm, Silver Color, ActiveWave Logo,Hole in Top Left Position Option, No Hole in Top Right, Hole on Left Side, Two Ultrasonic holes on the Top Right, Hole on the Right Side |  |  | Advanced Data Access Inc/ ActiveWave Inc | Box-ENC-102-3110111 |  | 8
107 | OPTF-1 | OPTM-4 | 1 | Enclouser | Box-ENC-102-4110111 |  | Box 12cm x 6.9cm x 2.5cm, Beige Color, ActiveWave Logo,Hole in Top Left Position Option, No Hole in Top Right, Hole on Left Side, Two Ultrasonic holes on the Top Right, Hole on the Right Side |  |  | Advanced Data Access Inc/ ActiveWave Inc | Box-ENC-102-4110111 |  | 8
108 | OPTF-1 | OPTM-5 | 1 | Enclouser | Box-ENC-102-5110111 |  | Box 12cm x 6.9cm x 2.5cm, Custom Color, ActiveWave Logo,Hole in Top Left Position Option, No Hole in Top Right, Hole on Left Side, Two Ultrasonic holes on the Top Right, Hole on the Right Side |  |  | Advanced Data Access Inc/ ActiveWave Inc | Box-ENC-102-5110111 |  | 8
109 | OPTG-0 | Sensor PWR | 2 | L18,D14 (change it to Resistor for these two) | 0 | 1206 | Res 0.0 OHM 1/4 W 5% 1206 SMD | Digi-Key | RHM0.0ERTR-ND | Rohm | MCR18EZPJ000 | Subsitute induct and Diod with Resistor | 8
110 | OPTG-0 | Sensor PWR | 0 | C63,C64,R60,R61,R62,RV3,U7 | DNP |  |  |  |  |  |  |  | 8
111 | OPTG-1 | Sensor PWR | 1 | C63 | 10pF | 0603 | CAP CER 10PF 50V 5% C0G 0603 | Digi-Key | 490-1403-2-ND | Murata | GRM1885C1H100JA01D |  | 8
112 | OPTG-1 | Sensor PWR | 1 | C64 | 1 uF 50V | 0805 | CAP CER 1UF 50V Y5V 0805 | Digi-Key | 490-3903-2-ND | Murata | GRM21BF51H105ZA12L |  | 8
113 | OPTG-1 | Sensor PWR | 1 | R62 | 12K | 0603 | RES 12K OHM 1/10W 5% 0603 SMD | Digi-Key | RHM12KGTR-ND | Rohm | MCR03EZPJ123 |  | 8
114 | OPTG-1 | Sensor PWR | 1 | R61 | 100K | 0603 | RES 100K OHM 1/10W 5% 0603 SMD | Digi-Key | RHM100KGCT-ND | Rohm | MCR03EZPJ104 |  | 8
115 | OPTG-1 | Sensor PWR | 0 | R60 | DNP |  |  |  |  |  |  |  | 8
#REF! | OPTG-1 | Sensor PWR | 1 | RV3 | 100K Pot | 9mm Squared | POT 100K OHM SQ CERMET SIDE | Digi-Key | CT94EZ104-ND | copal-electronics | CT94EZ104 |  | 8
#REF! | OPTG-1 | Sensor PWR | 1 | L18 | 3.3 uH | 1210 | INDUCTOR FERRITE CORE 3.3UH SMD | Digikey | DN42143JCT-ND |  | 1210R-332J |  | 8
#REF! | OPTG-1 | Sensor PWR | 1 | D14 | MBR0540 | SOD-123 | DIODE SCHOTTKY 40V 0.5A SOD123 | Digikey | MBR0540T1OSTR-ND | On Semiconductor | MBR0540T1 |  | 8
#REF! | OPTG-1 | Sensor PWR | 1 | U7 | LT1930 | SOT-23-5 | LT1930ES5#TRMCT-ND | Digikey | LT1930ES5#TRMCT-ND | Linear Technology | LT1930ES5#TRM |  | 8
#REF! |  |  |  |  |  |  |  |  |  |  |  |  | 8
#REF! | OPTD-1 | 433 MHz | 1 | J1 | 1X2 Header |  | CONN HEADER .100 SINGL STR 36POS | Digi-Key | S1011E-36-ND | Sullins Elec. | PBC36SAAN | One of these Sullins parts makes 18 2-pin headers | 8
#REF! |  | Basic | 0 | P2,P3 | DNP |  | 1x5 Header |  |  |  |  | Mask the HOLES | 8
#REF! |  | Basic | 0 | P1 | DNP |  | 1x8 Header |  |  |  |  | Mask the HOLES | 8
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
