tourajghaffari/tigerfid/protel-files/reader/pcmcia-reader/pcmcia-card-with-level-shifter/rev4/2 SMA Connectors installed in Compact Flash Plastic.jpg

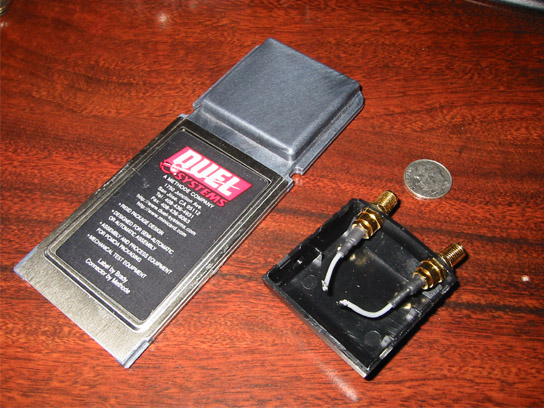
protel-files/reader/pcmcia-reader/pcmcia-card-with-level-shifter/rev4/2 SMA Connectors installed in Compact Flash Plastic.jpg
