tourajghaffari/tigerfid/protel-files/tags/tag-test-fixture/ENG_CD_222420_F[1].pdf

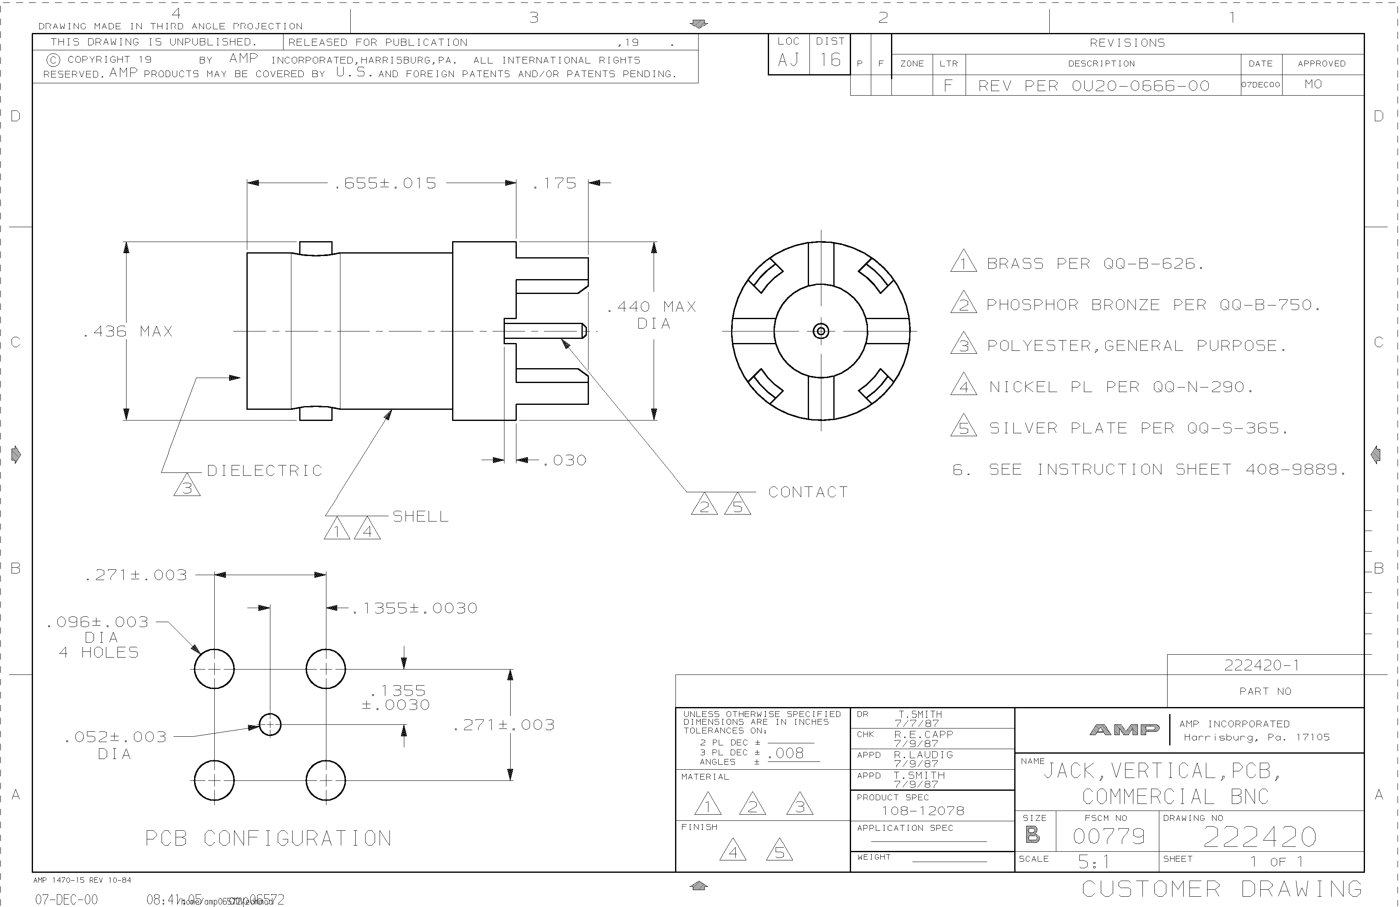
[picture p18: page 1]
