tourajghaffari/tigerfid/protel-files/tags/tag-test-fixture/5126A460.pdf

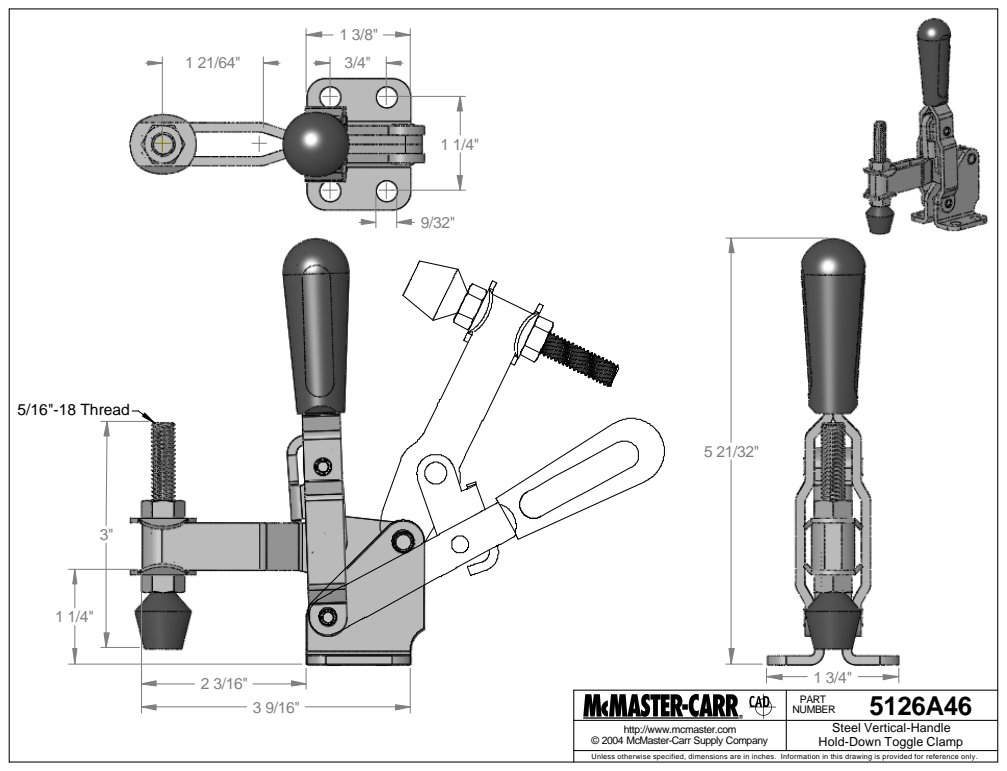
[picture p21: page 1]
5/16"-18 Thread

5126A46 PART NUMBER

http://www.mcmaster.com © 2004 McMaster-Carr Supply Company | Steel Vertical-Handle Hold-Down Toggle Clamp

Unless otherwise specified, dimensions are in inches. Information in this drawing is provided for reference only.
