tourajghaffari/tigerfid/protel-files/tags/tag-test-fixture/Tag Test Fixture.pdf

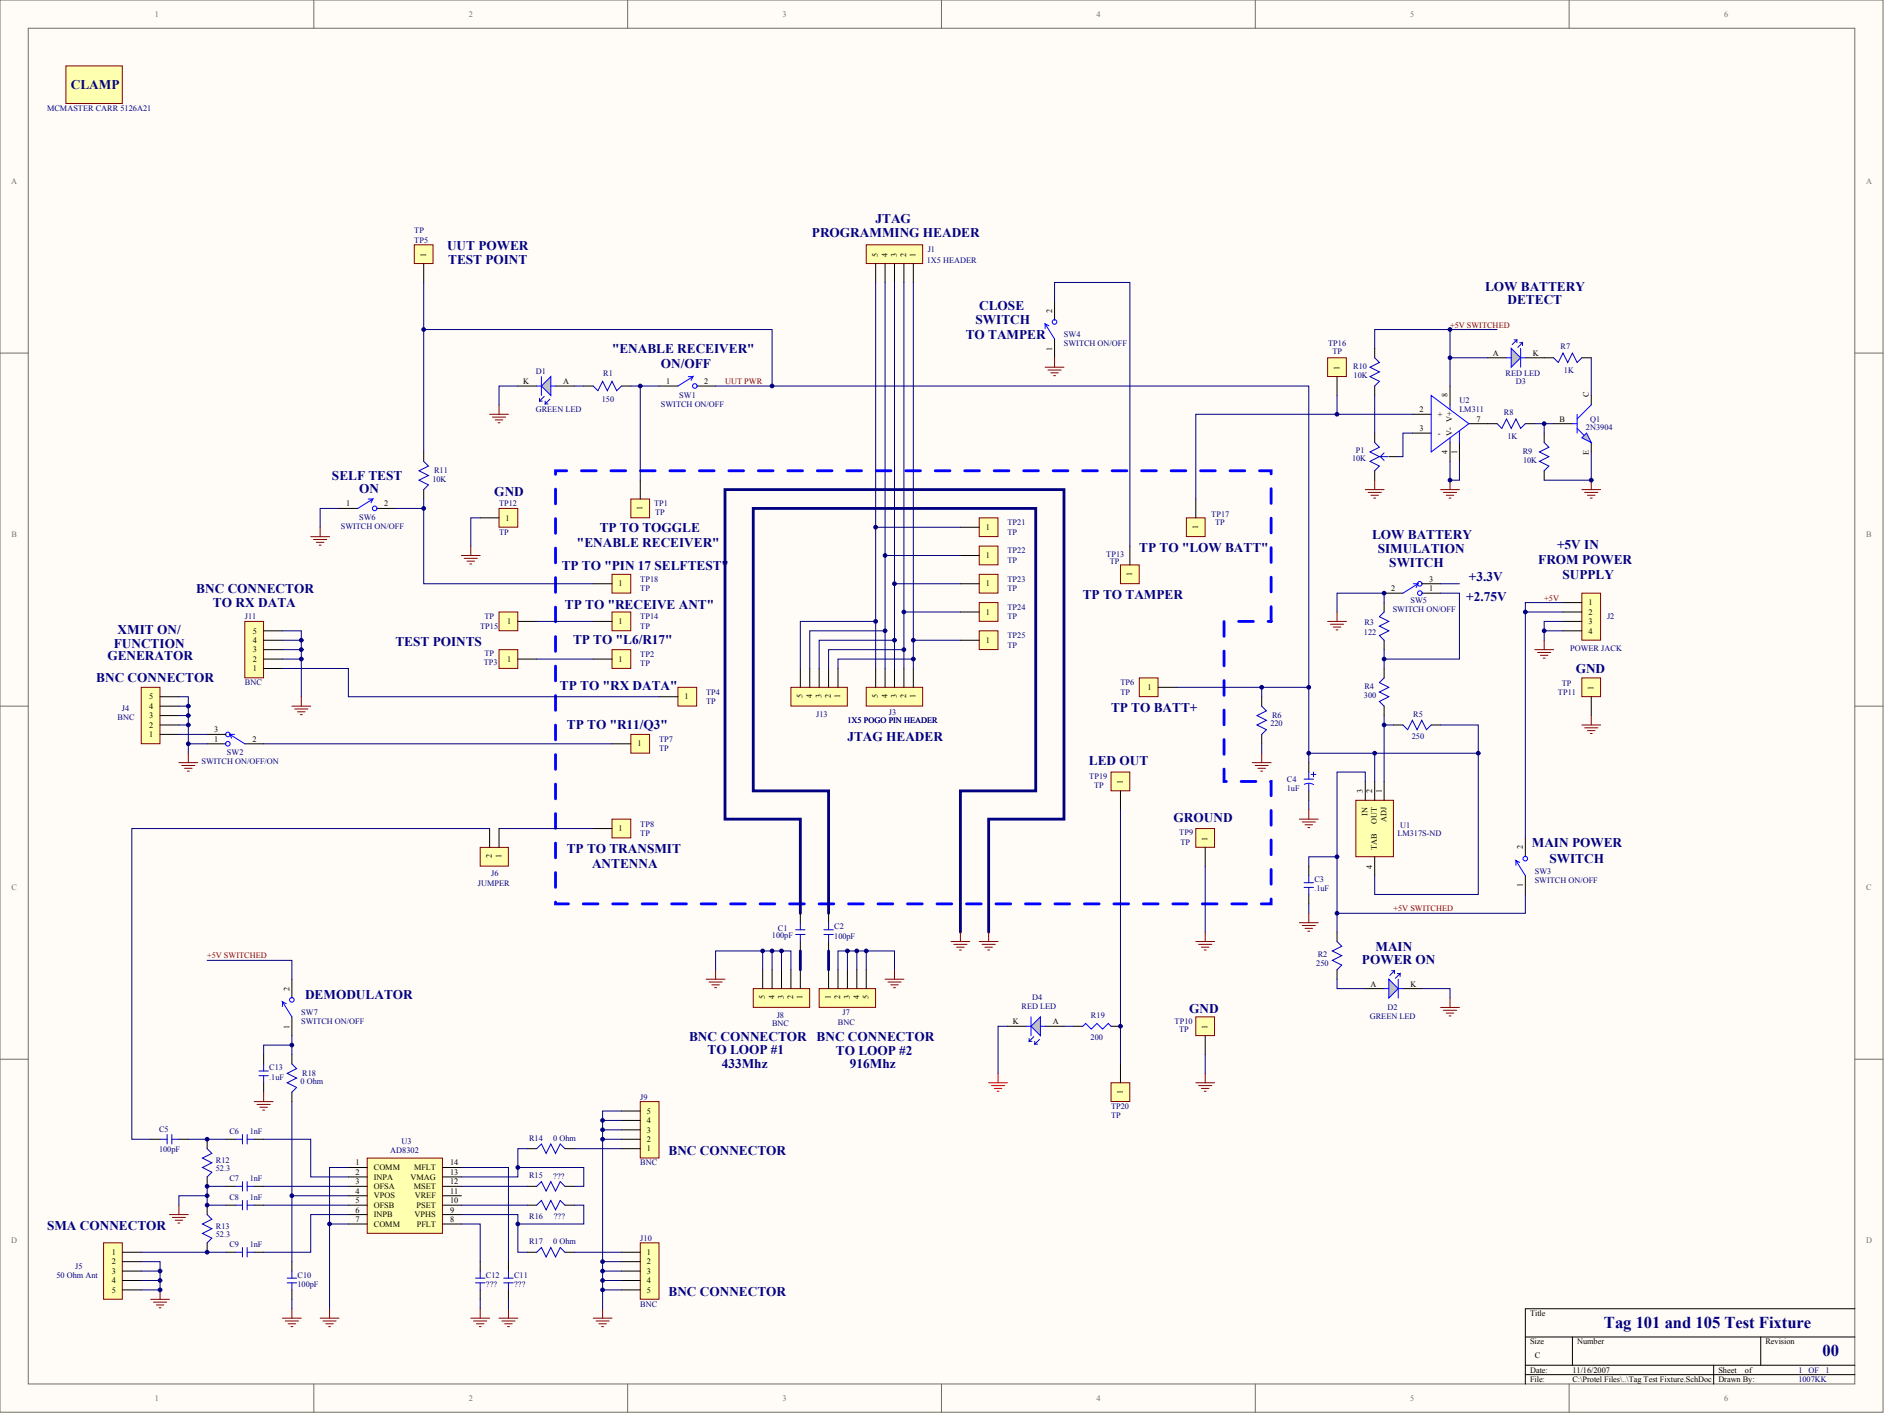
[picture p22: page 1]

TP TO "LOW BATT"

TP TO "PIN 17 SELFTEST"

TP TO "RECEIVE ANT"

3 | | 8 VPHS 9 PSET 10 VREF 11 MSET 12 VMAG 13 MFLT 14

5 | P0U3010 P0U3010 P0U3010 P0U309 P0U309 P0U309

Tag 101 and 105 Test Fixture
