tourajghaffari/tigerfid/protel-files/reader/pcmcia-reader/pdfs/Elan Chip Interface Schematic.pdf

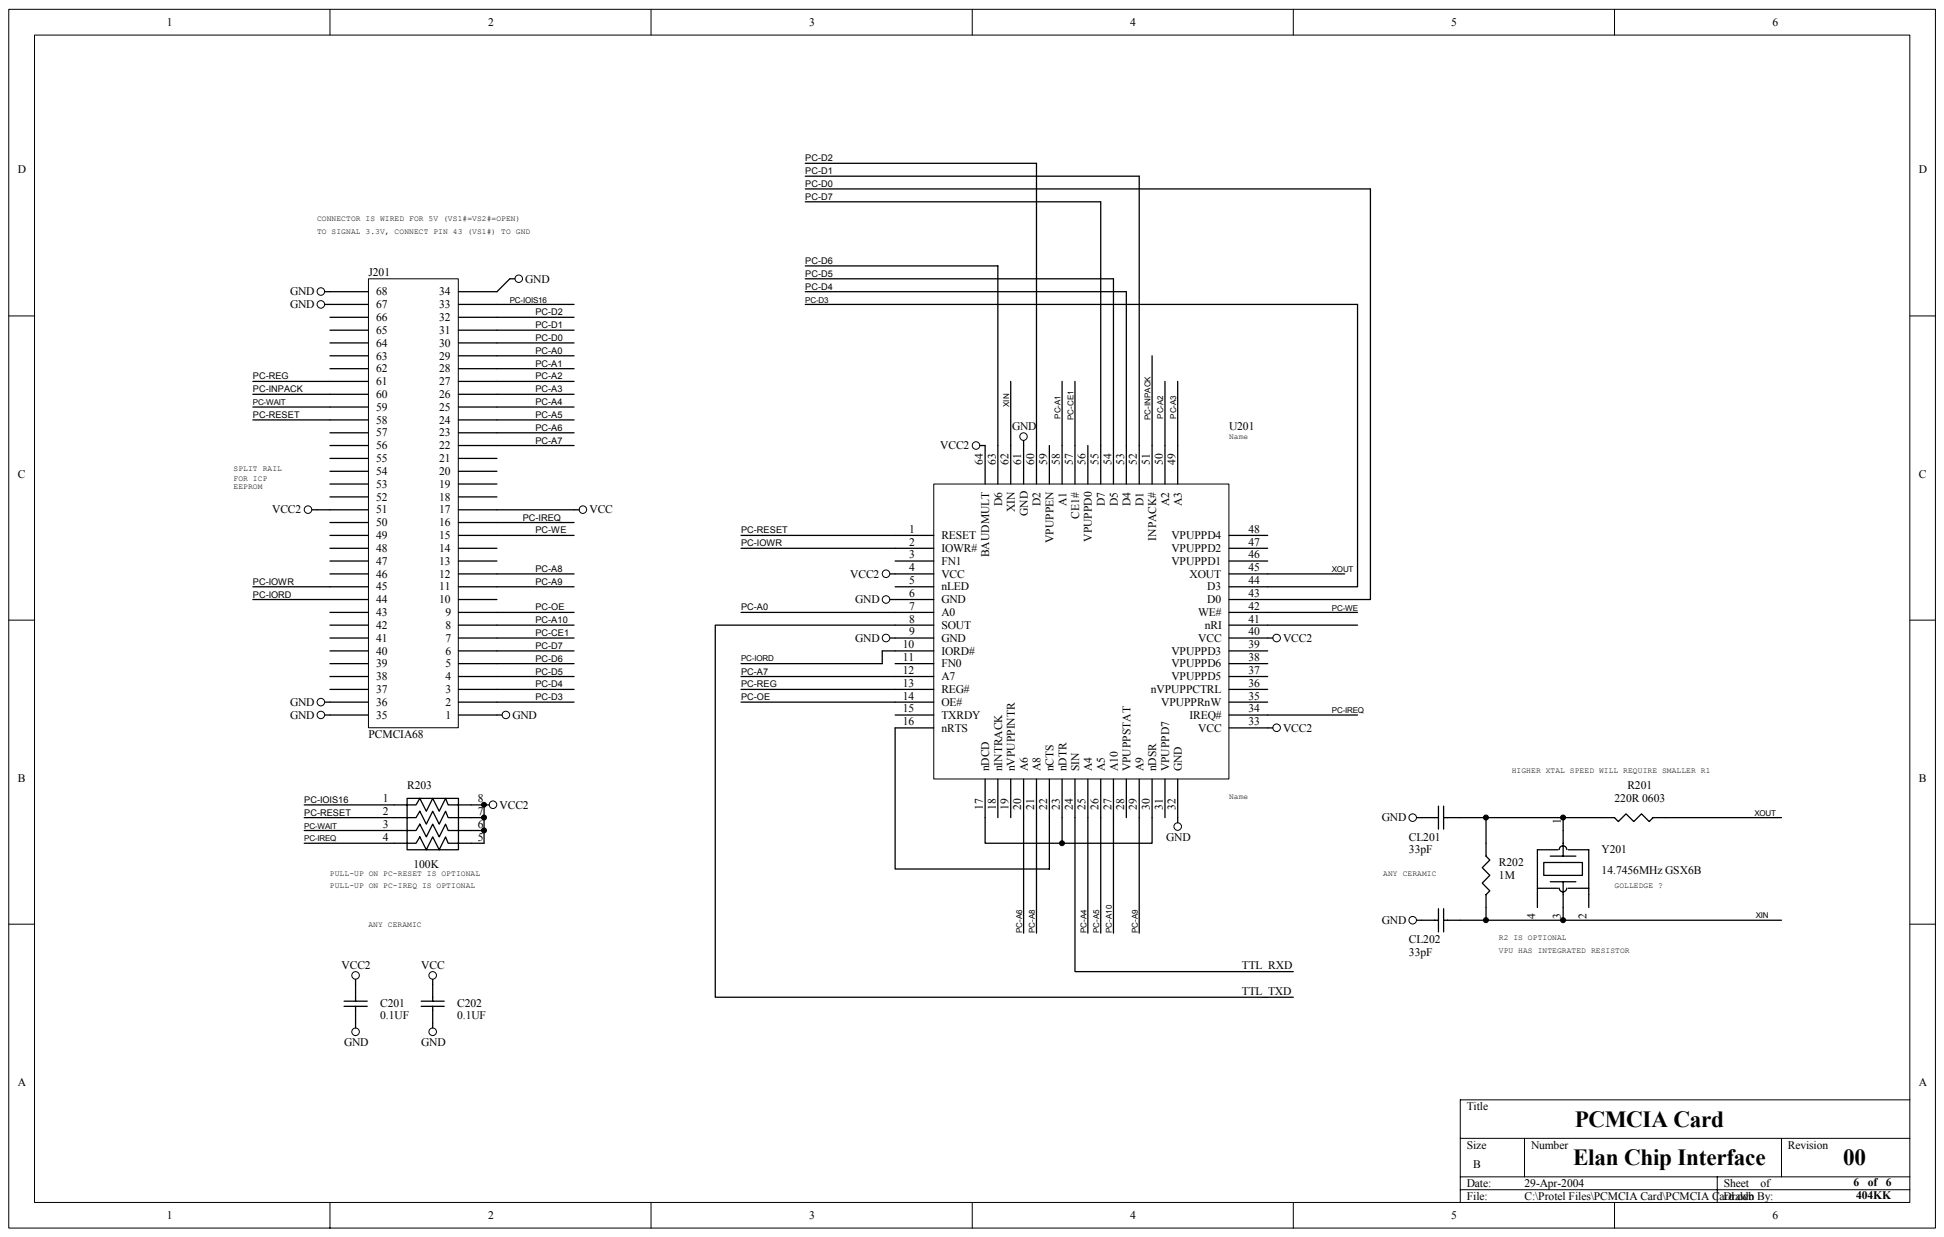
[picture p23: page 1]

CONNECTOR IS WIRED FOR 5V (VS1#=VS2#=OPEN)
TO SIGNAL 3.3V, CONNECT PIN 43 (VS1#) TO GND

A3 49 A2 50 INPACK# 51 D1 52 D4 53 D5 54 D7 55 VPUPPD0 56 CE1# 57 A1 58 VPUPPEN 59 D2 60 GND 61 XIN 62 D6 63 BAUDMULT 64

HIGHER XTAL SPEED WILL REQUIRE SMALLER R1

PULL-UP ON PC-RESET IS OPTIONAL
PULL-UP ON PC-IREQ IS OPTIONAL

R2 IS OPTIONAL
VPU HAS INTEGRATED RESISTOR

Size B | Number Elan Chip Interface | Revision 00

Date: 29-Apr-2004 | Sheet of 6 of 6
File: C:\Protel Files\PCMCIA Card\PCMCIA Card.ddb Drawn By: | 404KK
