tourajghaffari/tigerfid/protel-files/tags/medium-tag/102-rev21/schematic-2.pdf

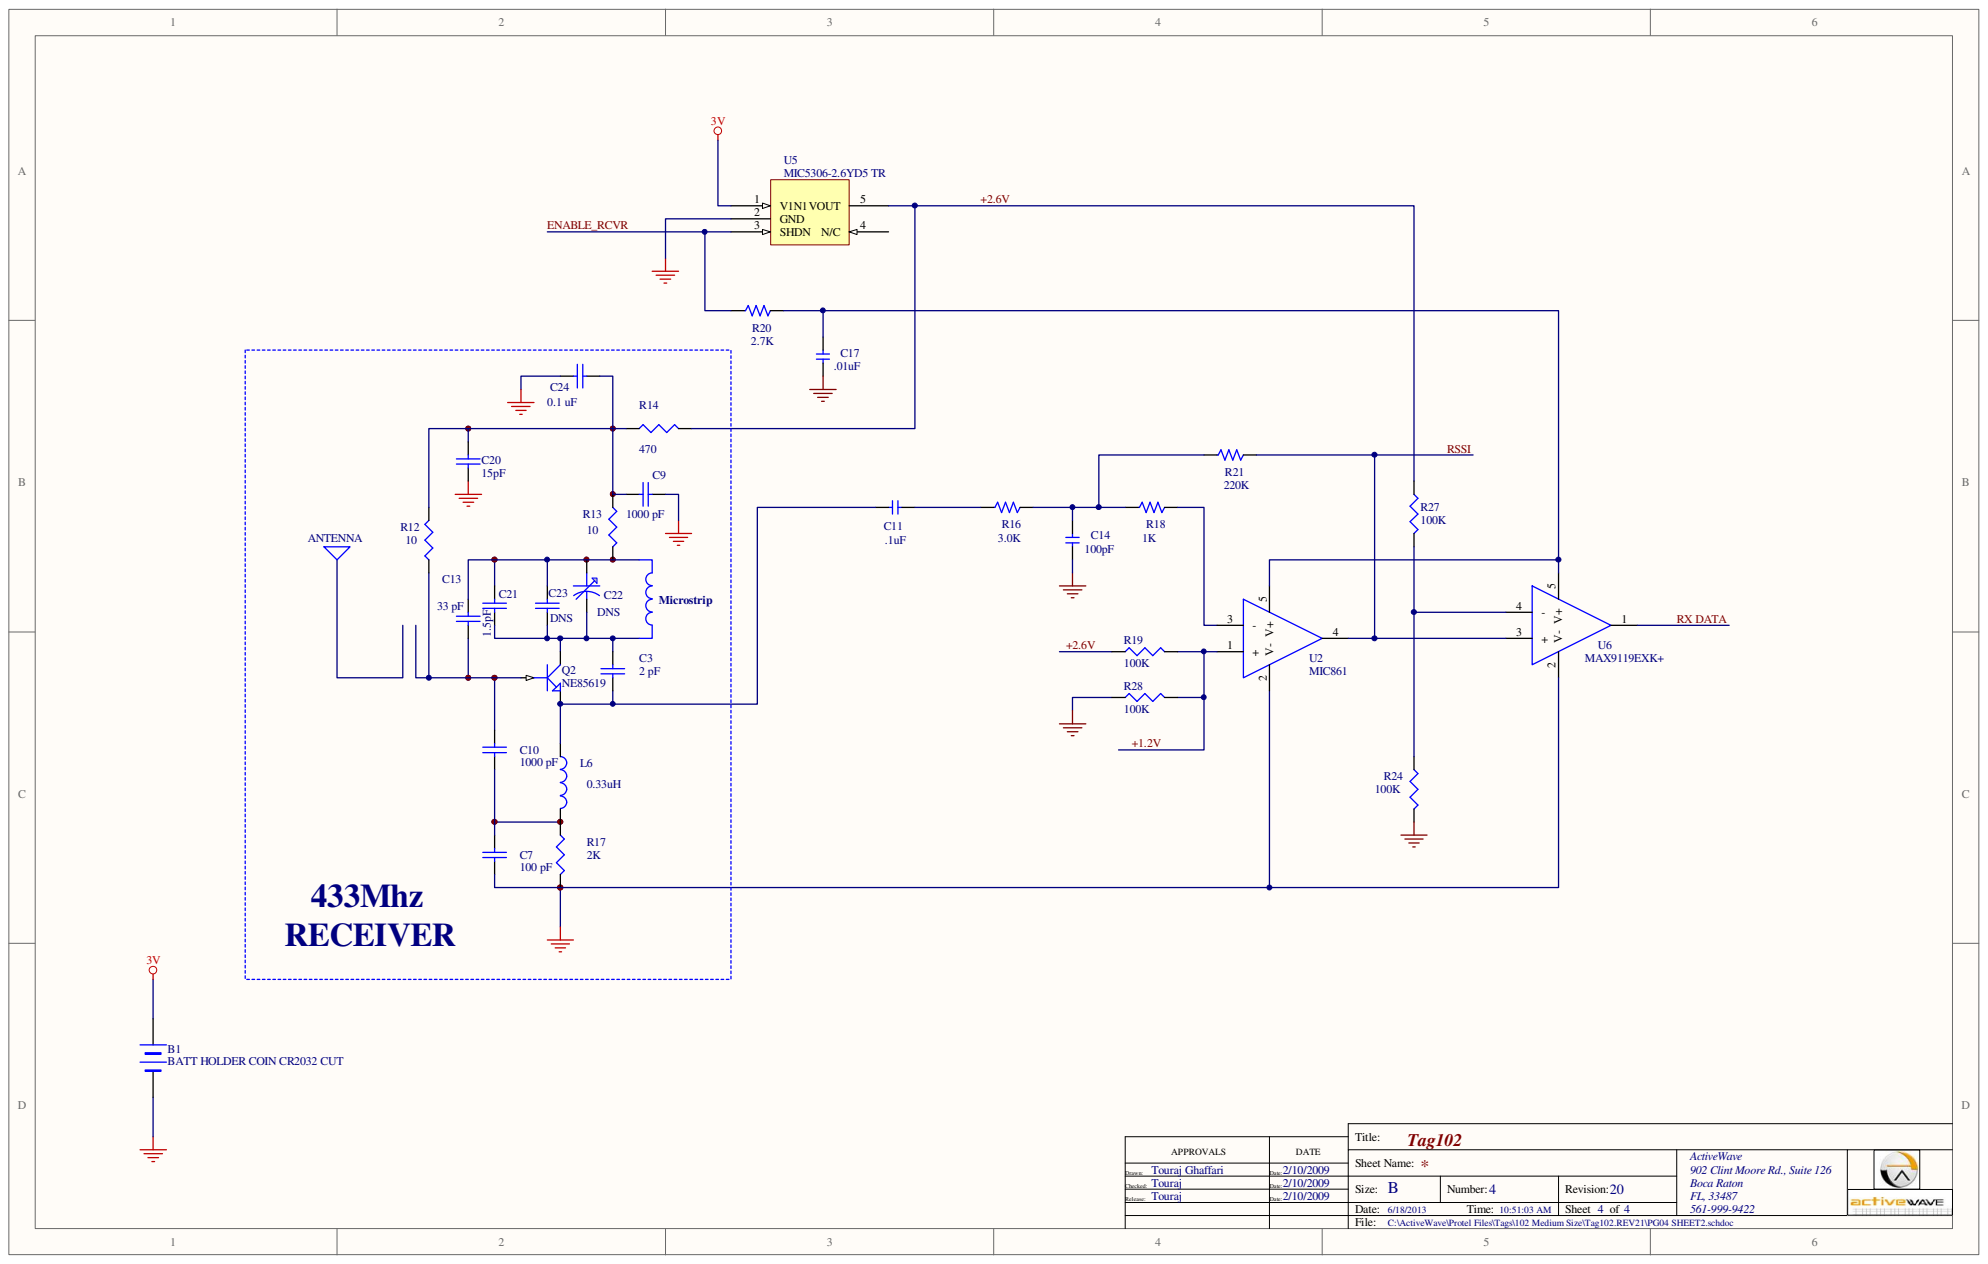
[picture p24: page 1]

BATT HOLDER COIN CR2032 CUT

ActiveWave
902 Clint Moore Rd., Suite 126
Boca Raton

C:\ActiveWave\Protel Files\Tags\102 Medium Size\Tag102.REV21\PG04 SHEET2.schdoc
