tourajghaffari/tigerfid/protel-files/reader/pcmcia-reader/pcmcia-card-with-level-shifter/pdfs/Schematic Page2.pdf

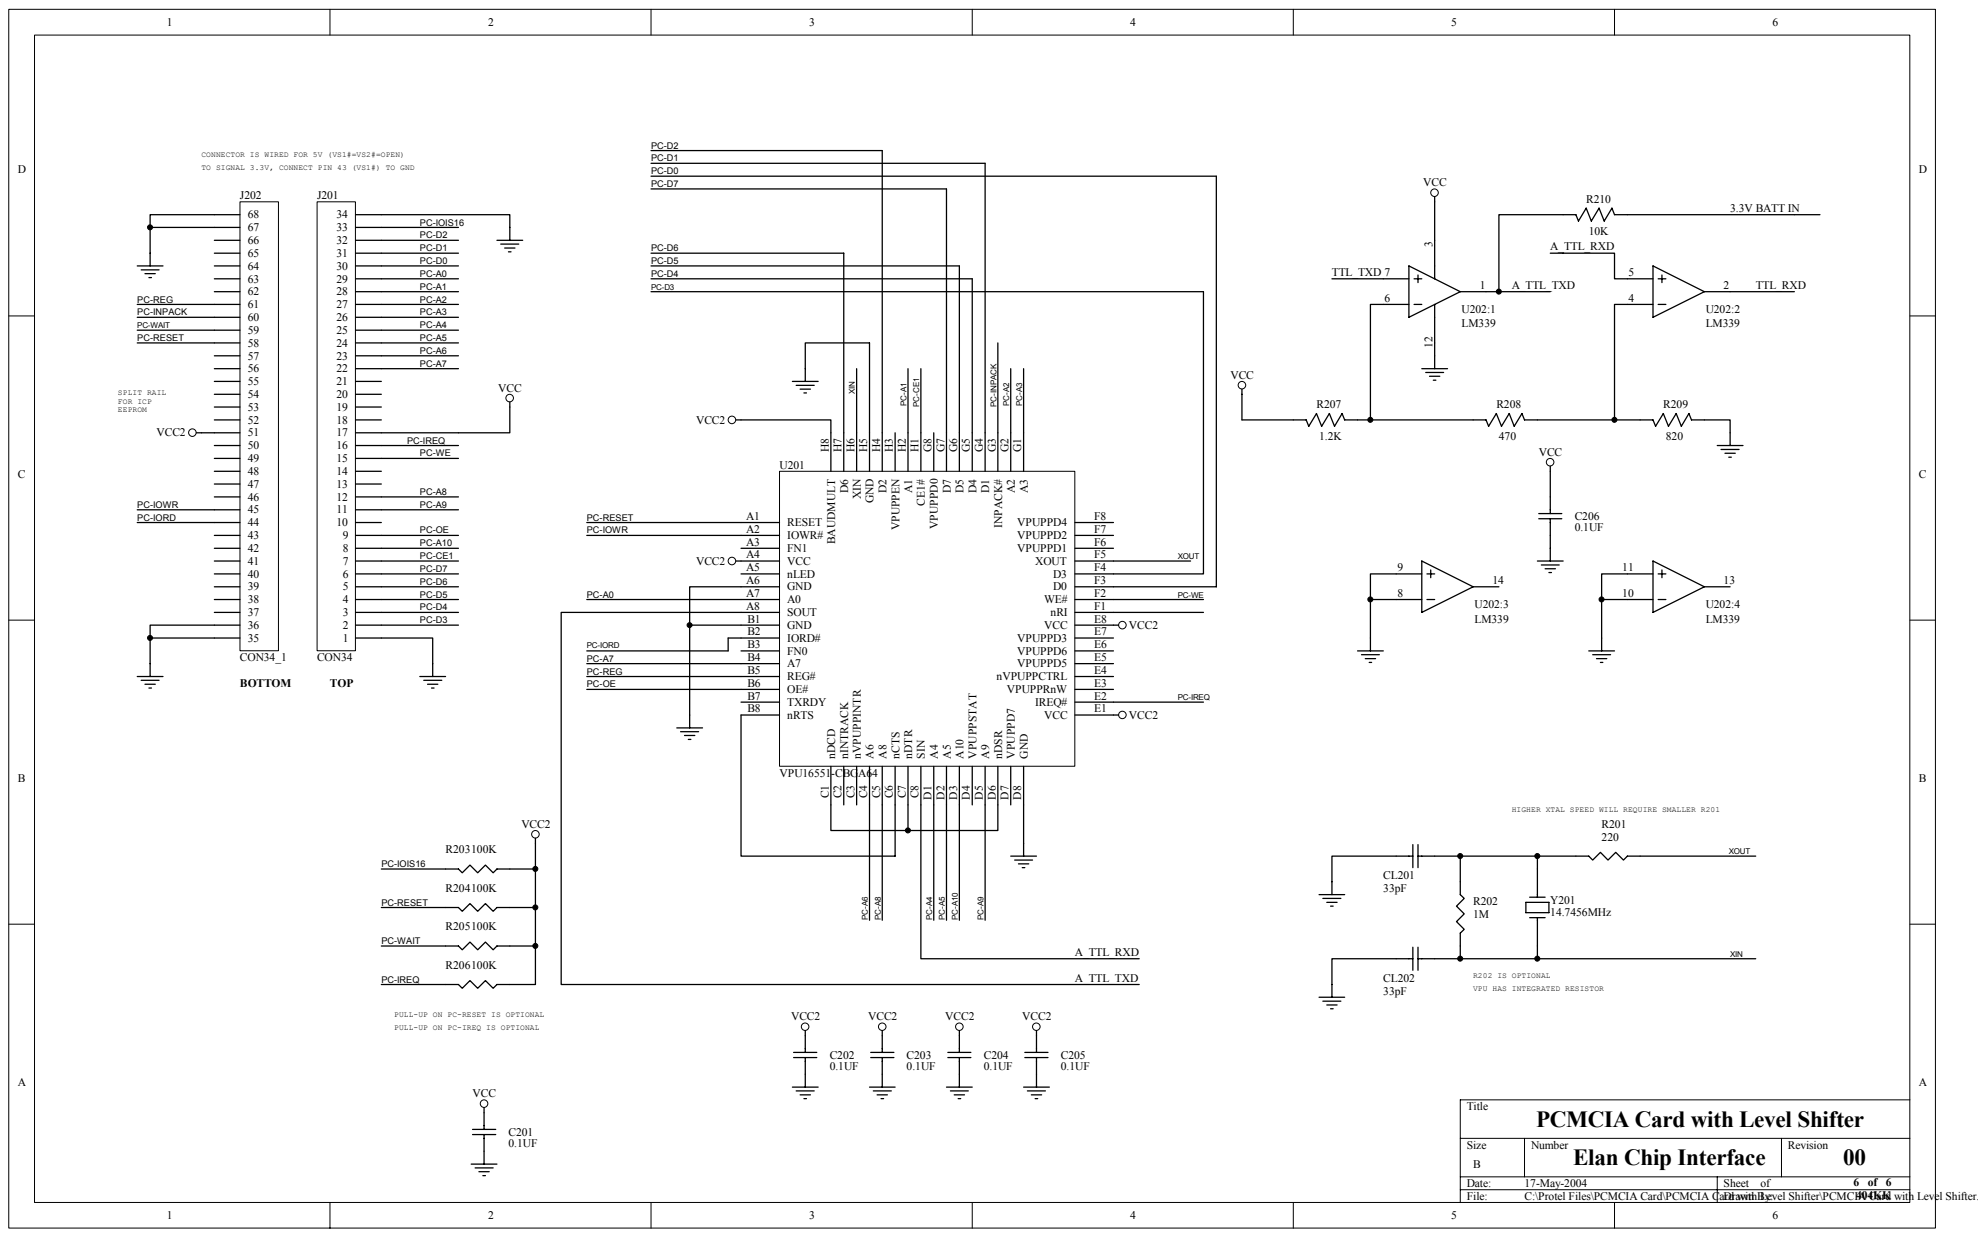
[picture p25: page 1]
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

A3 G1 A2 G2 INPACK# G3 D1 G4 D4 G5 D5 G6 D7 G7 VPUPPD0 G8 CE1# H1 A1 H2 VPUPPEN H3 D2 H4 GND H5 XIN H6 D6 H7 BAUDMULT H8 U201

HIGHER XTAL SPEED WILL REQUIRE SMALLER R201

R202 IS OPTIONAL
VPU HAS INTEGRATED RESISTOR

PULL-UP ON PC-RESET IS OPTIONAL
PULL-UP ON PC-IREQ IS OPTIONAL

Title
PCMCIA Card with Level Shifter

Size B | Number Elan Chip Interface | Revision 00

Date: 17-May-2004 | Sheet of 6 of 6
