tourajghaffari/tigerfid/protel-files/tags/credit-card-tag-tag-with-battery-holder/rev21/schematic/Schematic Prints.pdf

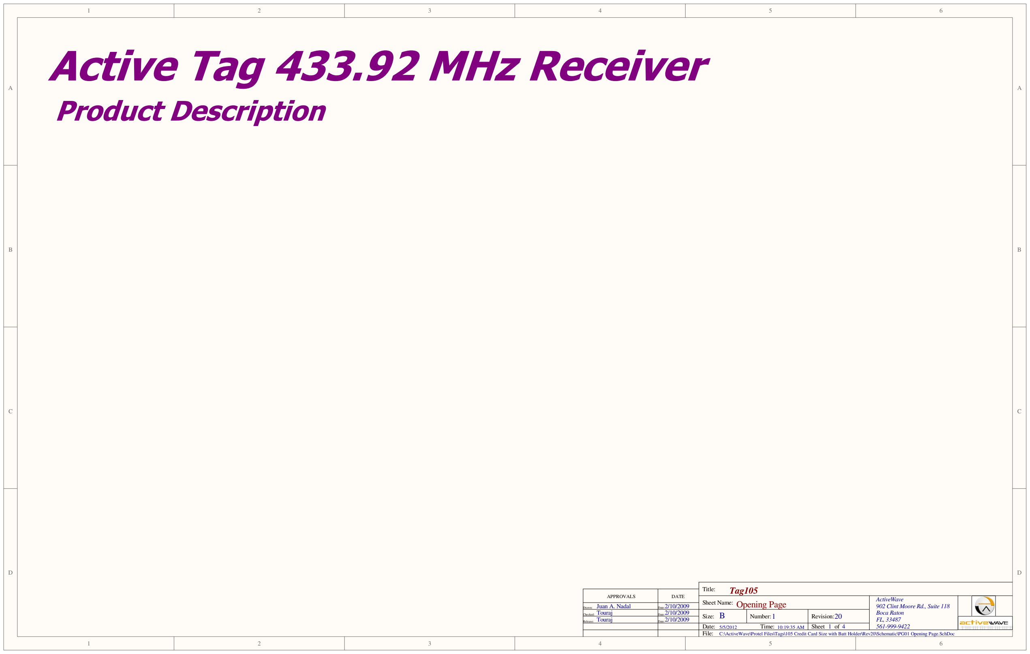
[picture p26: figure]
ActiveWave; 902 Clint Moore Rd., Suite 118 Boca Raton FL, 33487 4 561-999-9422; Tag105; Title:; Size:; Number:; Date: File:; Revision:; Time:; Sheet; APPROVALS; DATE; Drawn:; Checked:; Release:; Juan A. Nadal Touraj Touraj; Date:; Opening Page Sheet Name: 2/10/2009; Active Tag 433.92 MHz Receiver; Product Description

C:\ActiveWave\Protel Files\Tags\105 Credit Card Size with Batt Holder\Rev20\Schematic\PG01 Opening Page.SchDoc

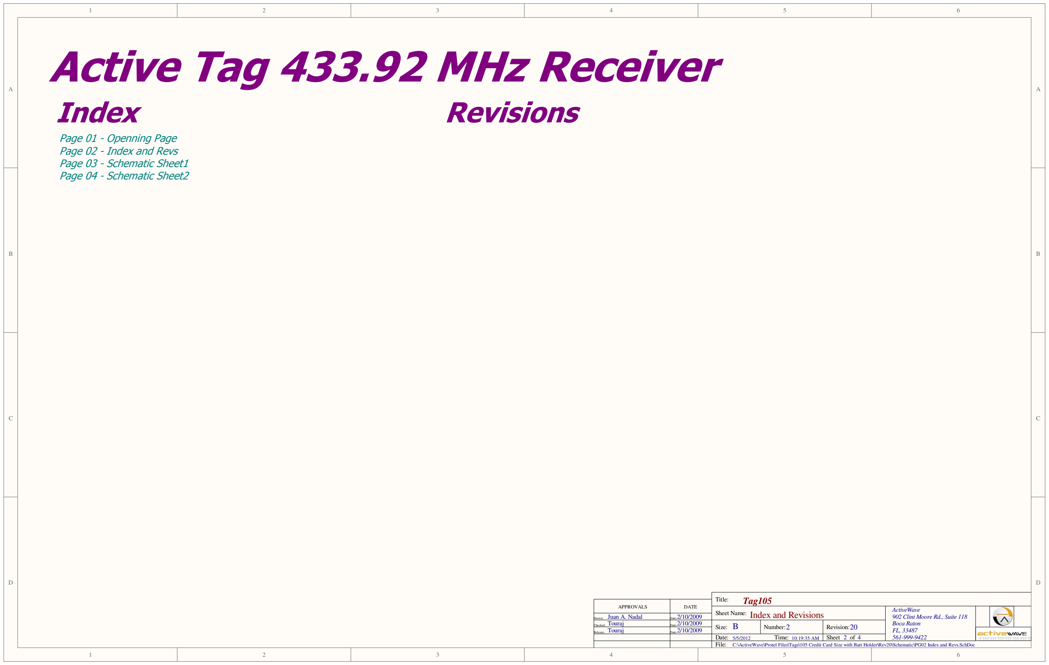
[picture p27: figure]
ActiveWave; 902 Clint Moore Rd., Suite 118 Boca Raton FL, 33487 4 561-999-9422; Tag105; Title:; Size:; Number:; Date: File:; Revision:; Time:; Sheet; APPROVALS; DATE; Drawn:; Checked:; Release:; Juan A. Nadal Touraj Touraj; Date:; Active Tag 433.92 MHz Receiver; Index; Revisions; Page 01 - Openning Page Page 02 - Index and Revs Page 03 - Schematic Sheet1 Page 04 - Schematic Sheet2

C:\ActiveWave\Protel Files\Tags\105 Credit Card Size with Batt Holder\Rev20\Schematic\PG02 Index and Revs.SchDoc

Index and Revisions Sheet Name: 2/10/2009

# TRANSMITTER

# 916Mhz

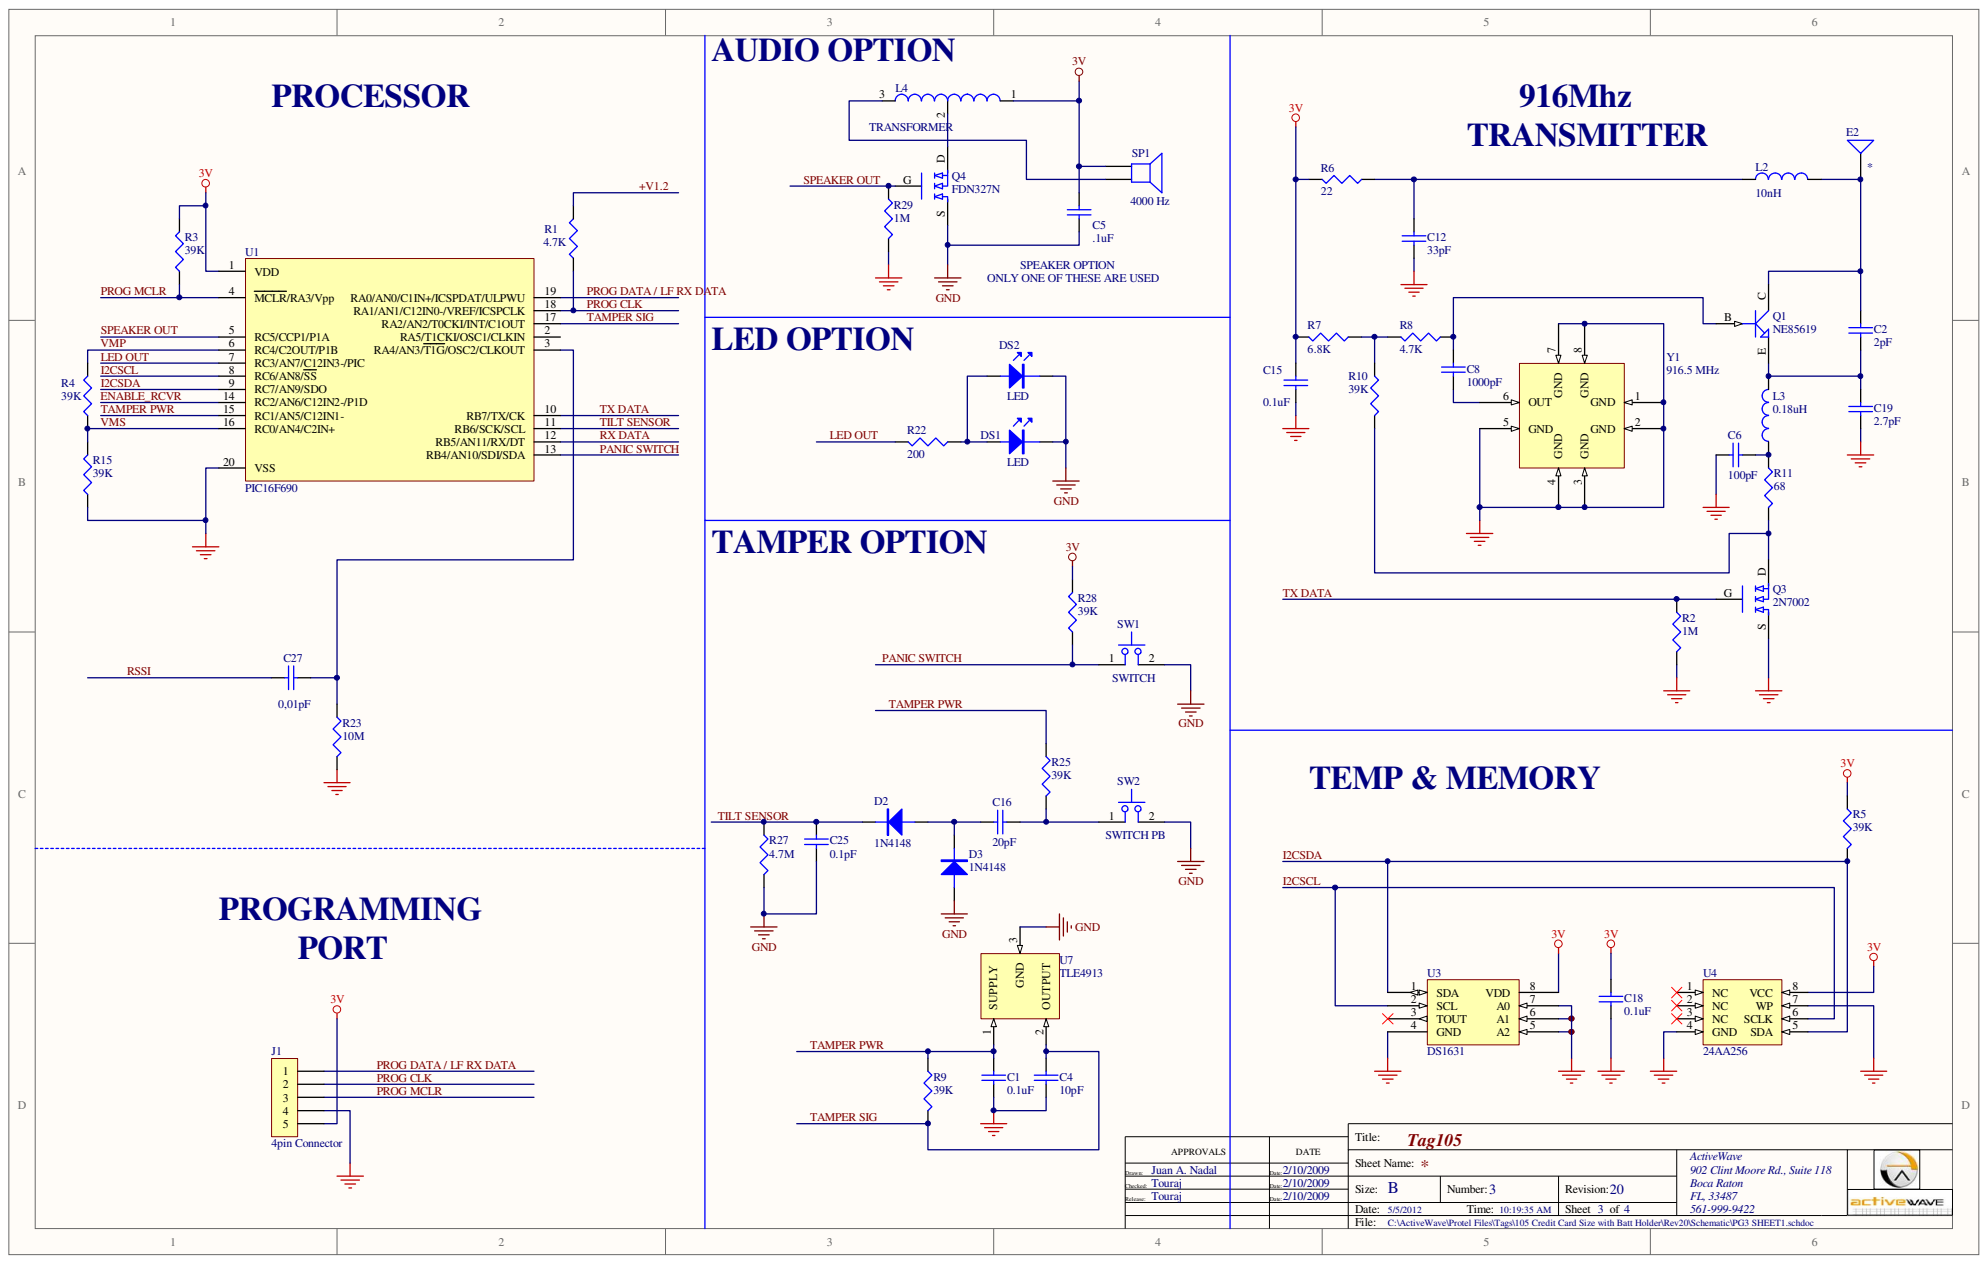
[picture p28: page 3]

PROG DATA / LF RX DATA
PROG CLK
TAMPER SIG

ONLY ONE OF THESE ARE USED

PROG MCLR

ActiveWave
902 Clint Moore Rd., Suite 118
Boca Raton

Juan A. Nadal Drawn: | Date:
Touraj Checked: | 2/10/2009 Date: Size: B | Number: 3 20 | Revision:

Touraj Release: | 2/10/2009 Date:

C:\ActiveWave\Protel Files\Tags\105 Credit Card Size with Batt Holder\Rev20\Schematic\PG3 SHEET1.schdoc

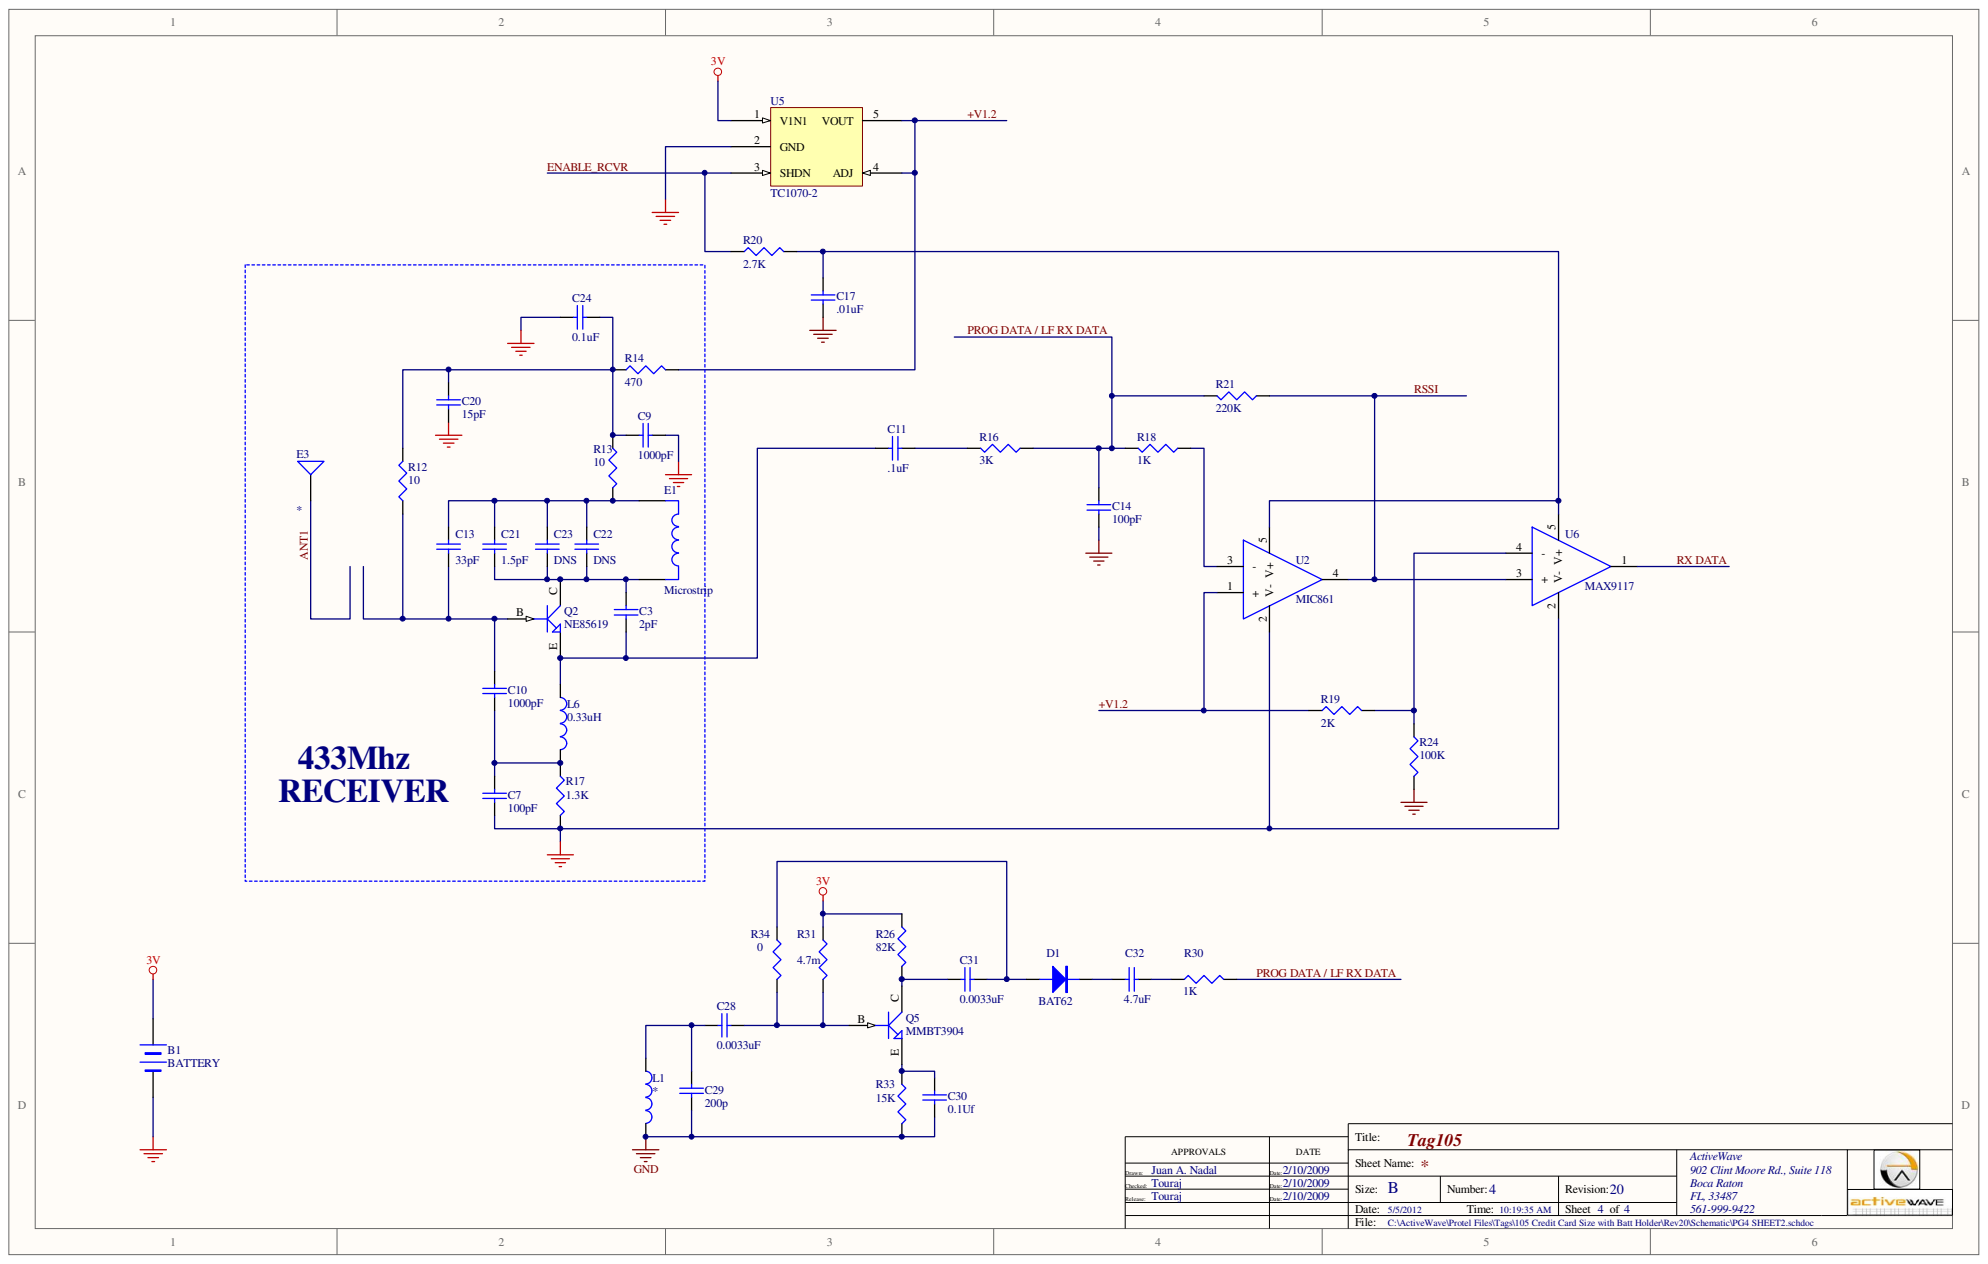
[picture p29: page 4]

PROG DATA / LF RX DATA

ActiveWave
902 Clint Moore Rd., Suite 118
Boca Raton

C:\ActiveWave\Protel Files\Tags\105 Credit Card Size with Batt Holder\Rev20\Schematic\PG4 SHEET2.schdoc
