tourajghaffari/tigerfid/protel-files/reader/pcmcia-reader/pcmcia-card-with-level-shifter/latest/pdfs/Elan Chip Interface Schematic.pdf

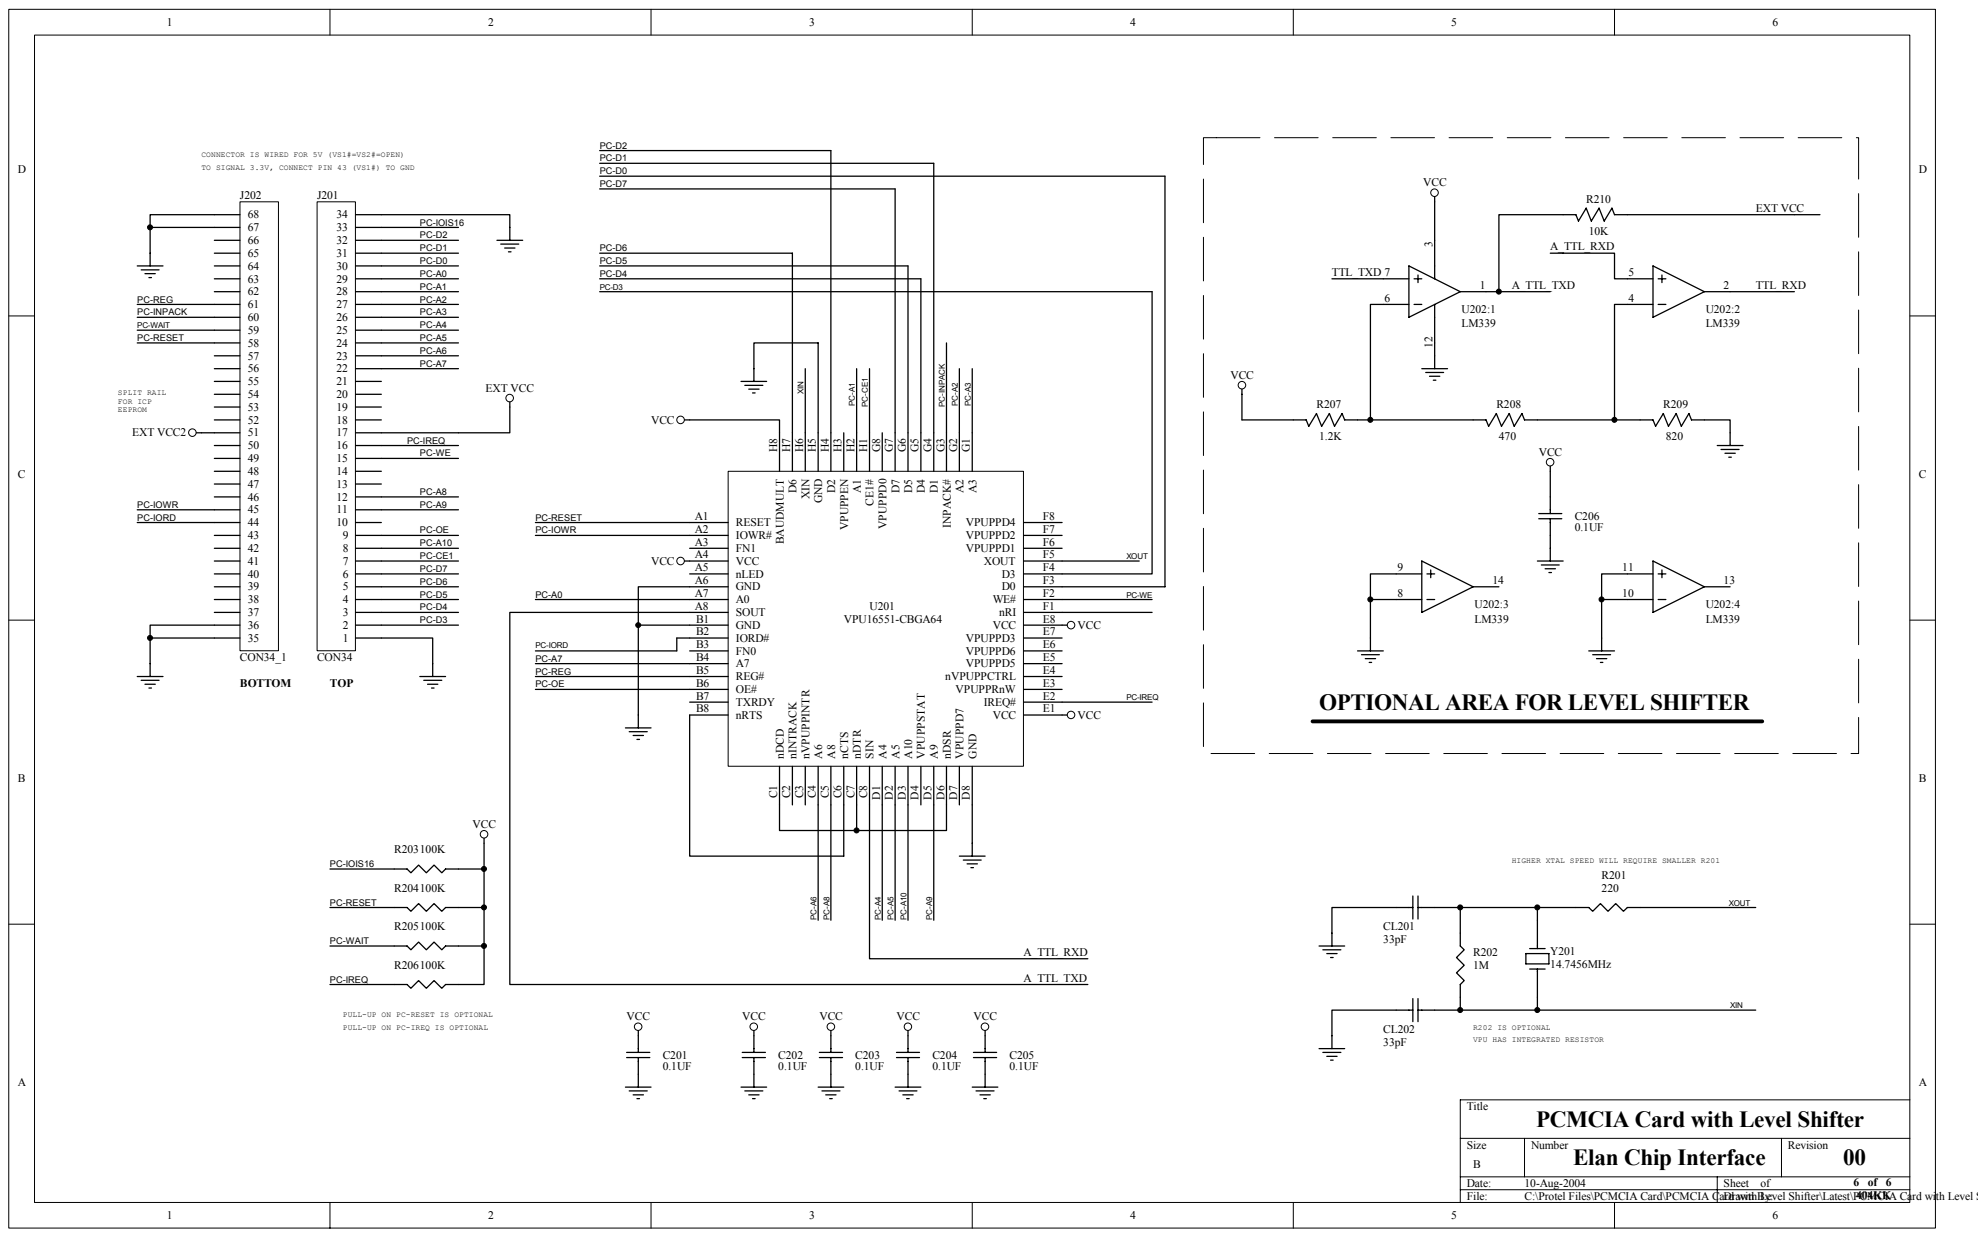
[picture p30: page 1]
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

OPTIONAL AREA FOR LEVEL SHIFTER

HIGHER XTAL SPEED WILL REQUIRE SMALLER R201

PULL-UP ON PC-RESET IS OPTIONAL
PULL-UP ON PC-IREQ IS OPTIONAL

R202 IS OPTIONAL
VPU HAS INTEGRATED RESISTOR

Title
PCMCIA Card with Level Shifter

Size B | Number Elan Chip Interface | Revision 00

Date: 10-Aug-2004 | Sheet of 6 of 6
