tourajghaffari/tigerfid/protel-files/transceiver/trx-rev19/reviews/TRX-101R17_Review1.pdf

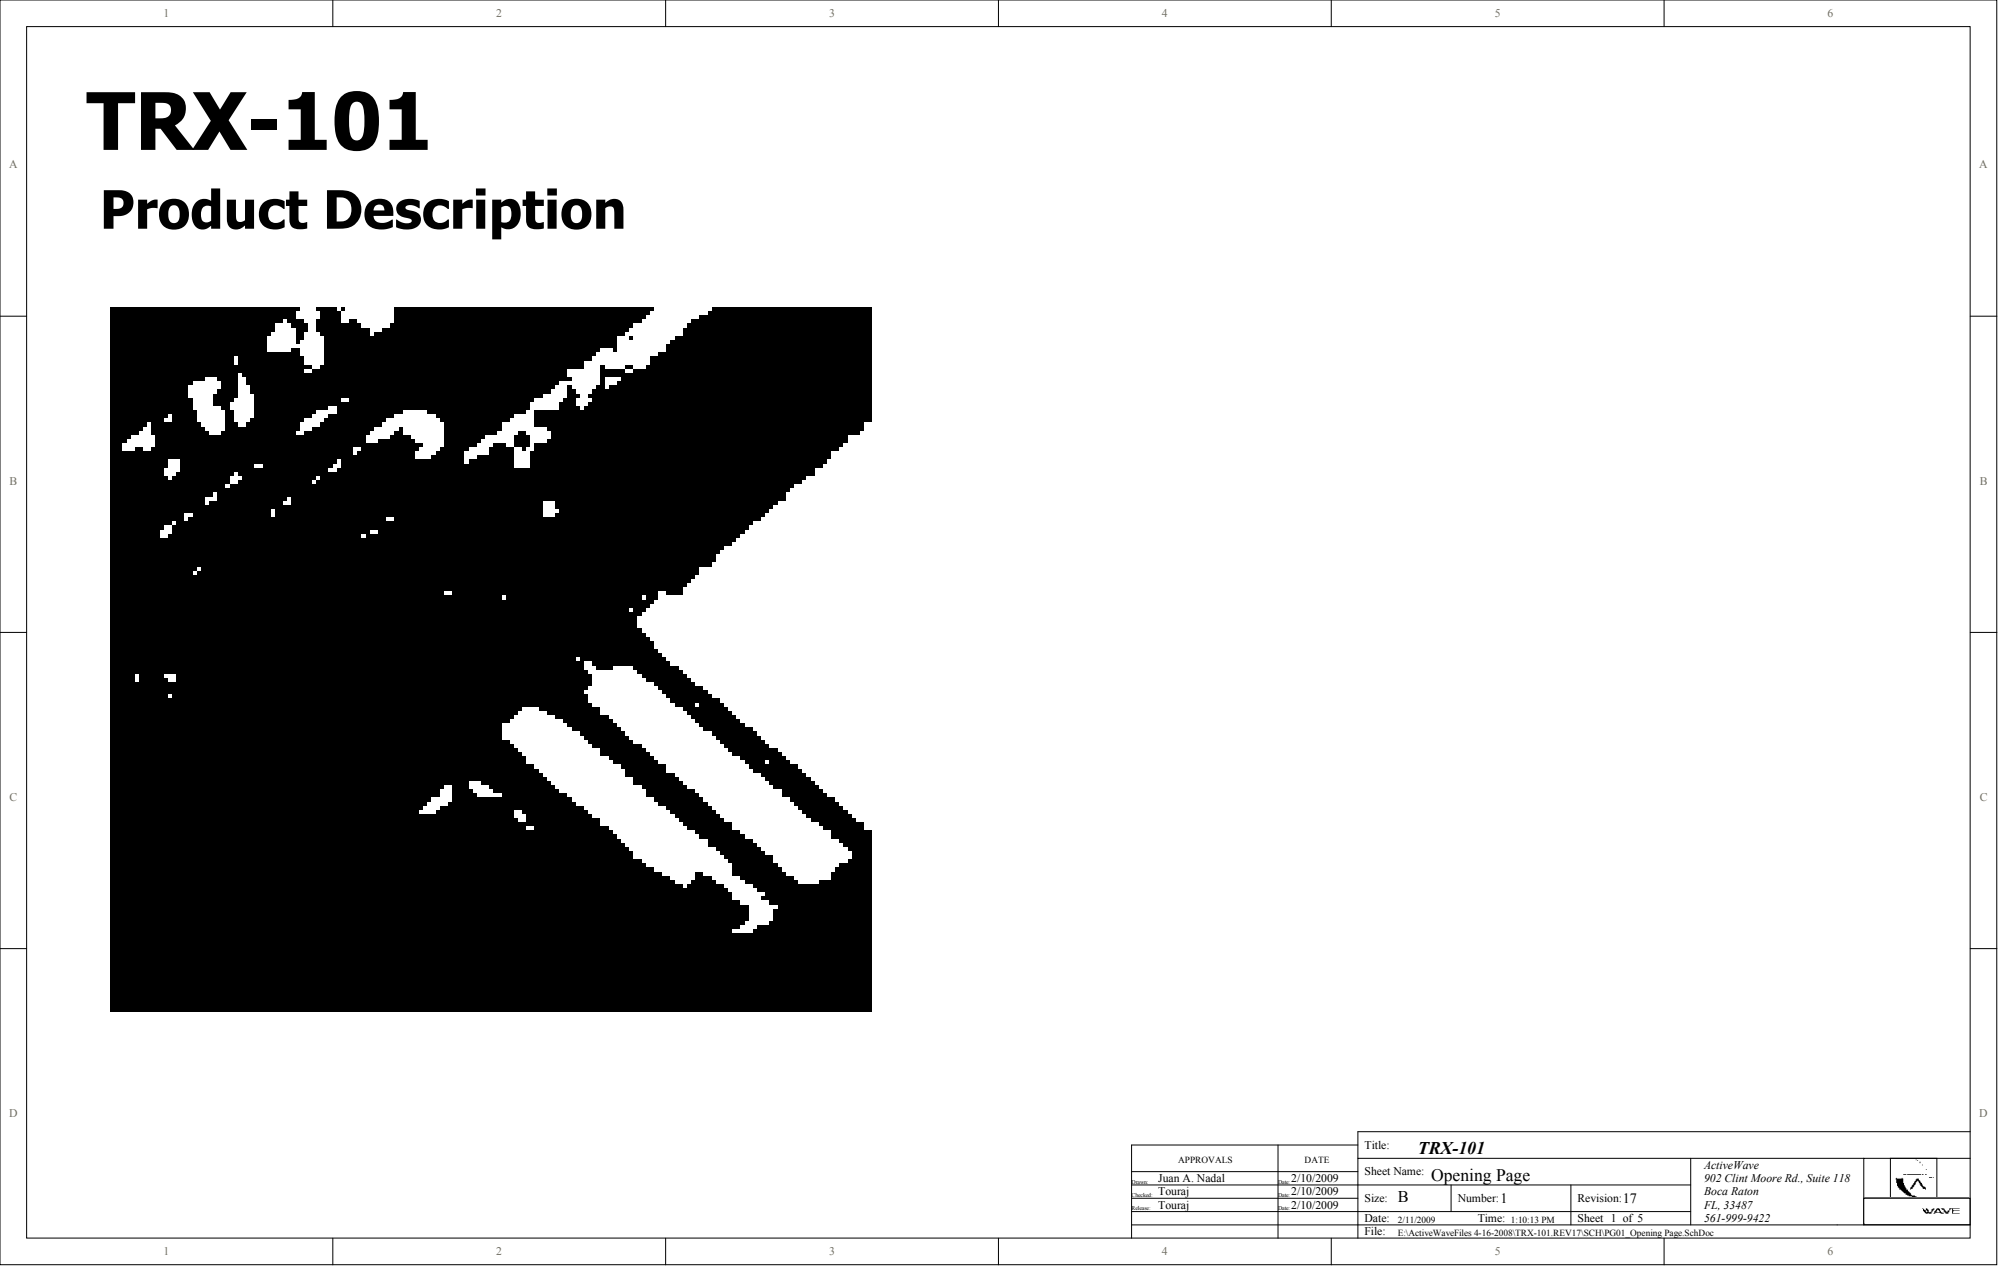
[picture p36: page 1]
Product Description

APPROVALS | DATE

Opening Page Sheet Name: 2/10/2009 | ActiveWave 902 Clint Moore Rd., Suite 118 Boca Raton FL, 33487 561-999-9422

Juan A. Nadal Drawn: | Date:
Touraj Checked: | 2/10/2009 Date: | B Size: | Number: 1 | Revision: 17

Touraj Release: | 2/10/2009 Date:

Date: Time: 2/11/2009 1:10:13 PM | | Sheet 1 of 5
File: E:\ActiveWaveFiles 4-16-2008\TRX-101.REV17\SCH\PG01_Opening Page.SchDoc

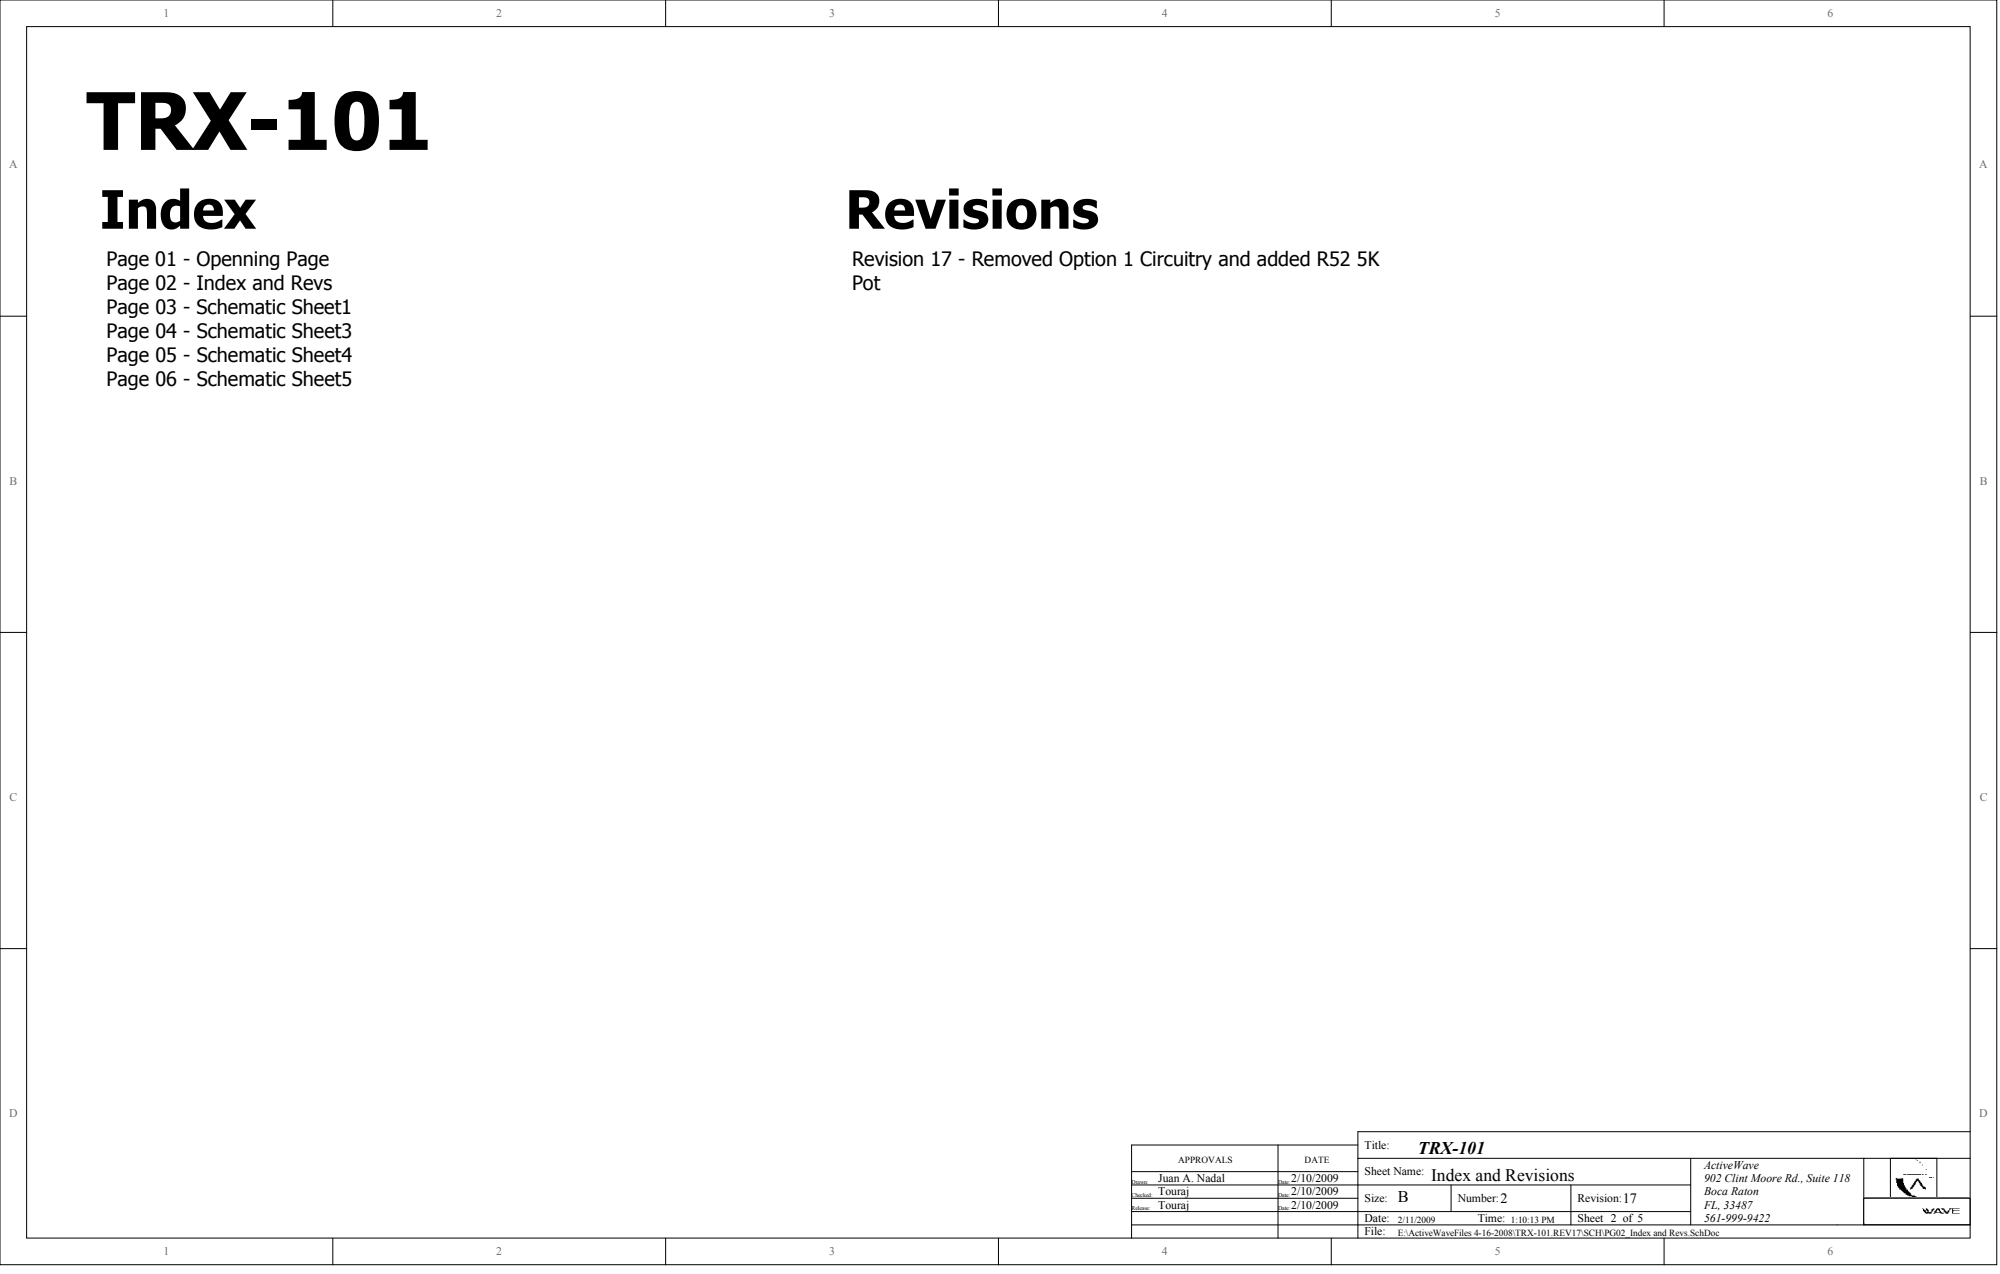
[picture p37: page 2]

Page 01 - Openning Page
Page 02 - Index and Revs
Page 03 - Schematic Sheet1
Page 04 - Schematic Sheet3
Page 05 - Schematic Sheet4
Page 06 - Schematic Sheet5

Revision 17 - Removed Option 1 Circuitry and added R52 5K
Pot

APPROVALS | DATE

Index and Revisions Sheet Name: 2/10/2009 | ActiveWave 902 Clint Moore Rd., Suite 118 Boca Raton FL, 33487 561-999-9422

Juan A. Nadal Drawn: | Date:
Touraj Checked: | 2/10/2009 Date: | B Size: | Number: 2 | Revision: 17

Touraj Release: | 2/10/2009 Date:

Date: Time: 2/11/2009 1:10:13 PM | | Sheet 2 of 5
File: E:\ActiveWaveFiles 4-16-2008\TRX-101.REV17\SCH\PG02_Index and Revs.SchDoc

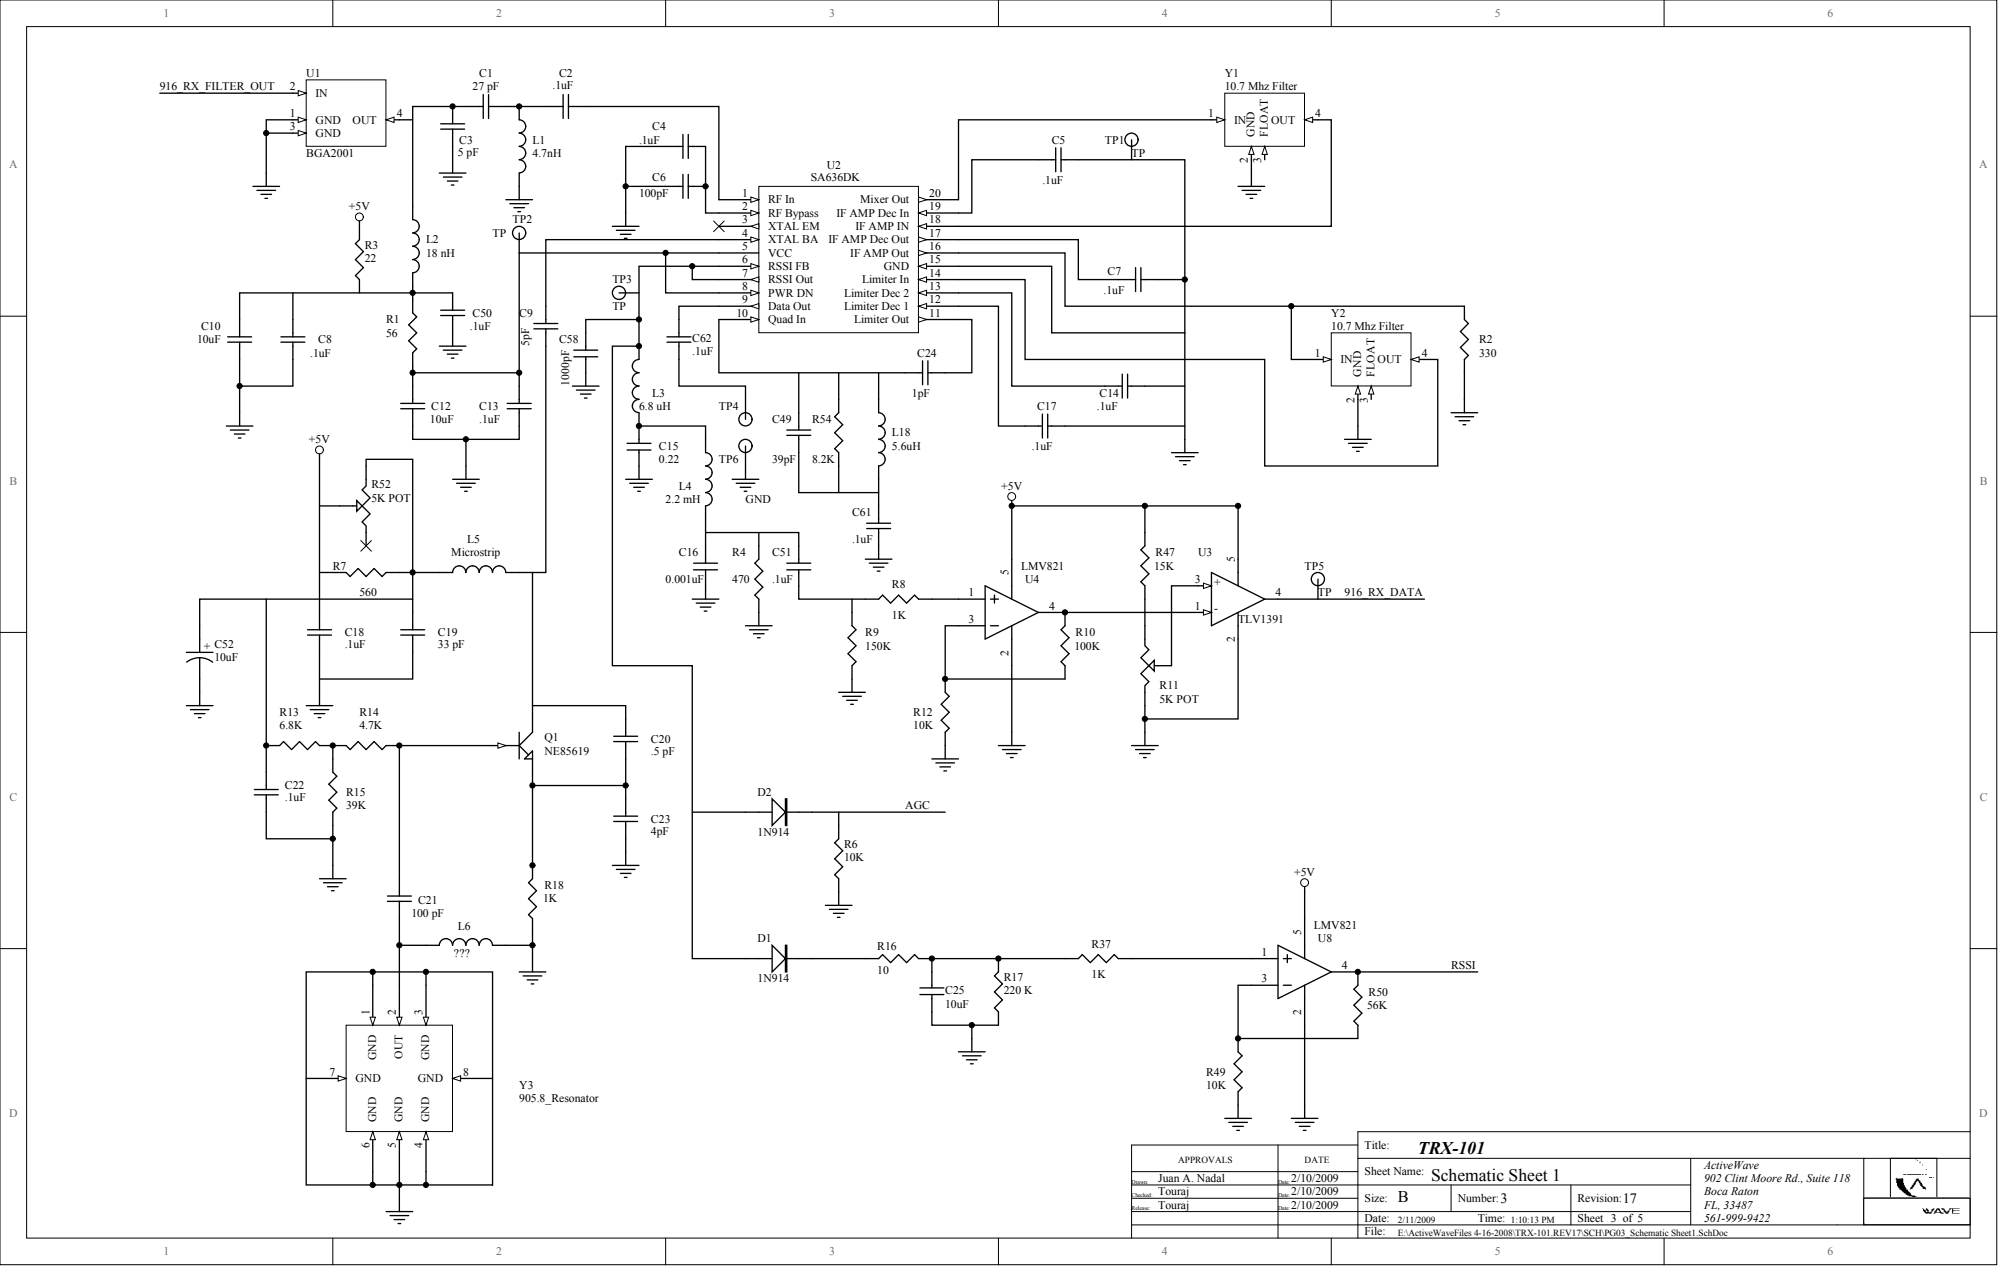
[picture p38: page 3]

6 | P0U2015 P0U2015 | 14 GND 15

31
P0U303 P0U303

APPROVAL S | DAT E

Schematic Sheet 1 Sheet Name: 2/10/2009 | ActiveWave 902 Clint Moore Rd., Suite 118 Boca Raton FL, 33487 561-999-9422

Juan A. Nadal D r awn : | D ate :
Touraj Ch e c k e d : | 2/10/2009 D ate : | B Size: | Number: 3 | Revision: 17

Touraj Rele ase : | 2/10/2009 D ate :

Date: File: Time: 2/11/2009 1:10:13 PM | | Sheet 3 of 5

E:\Activ e Wav e Fil es 4-16-2008\TRX-101.REV17\SCH\PG03_Schematic She et1.SchDo c

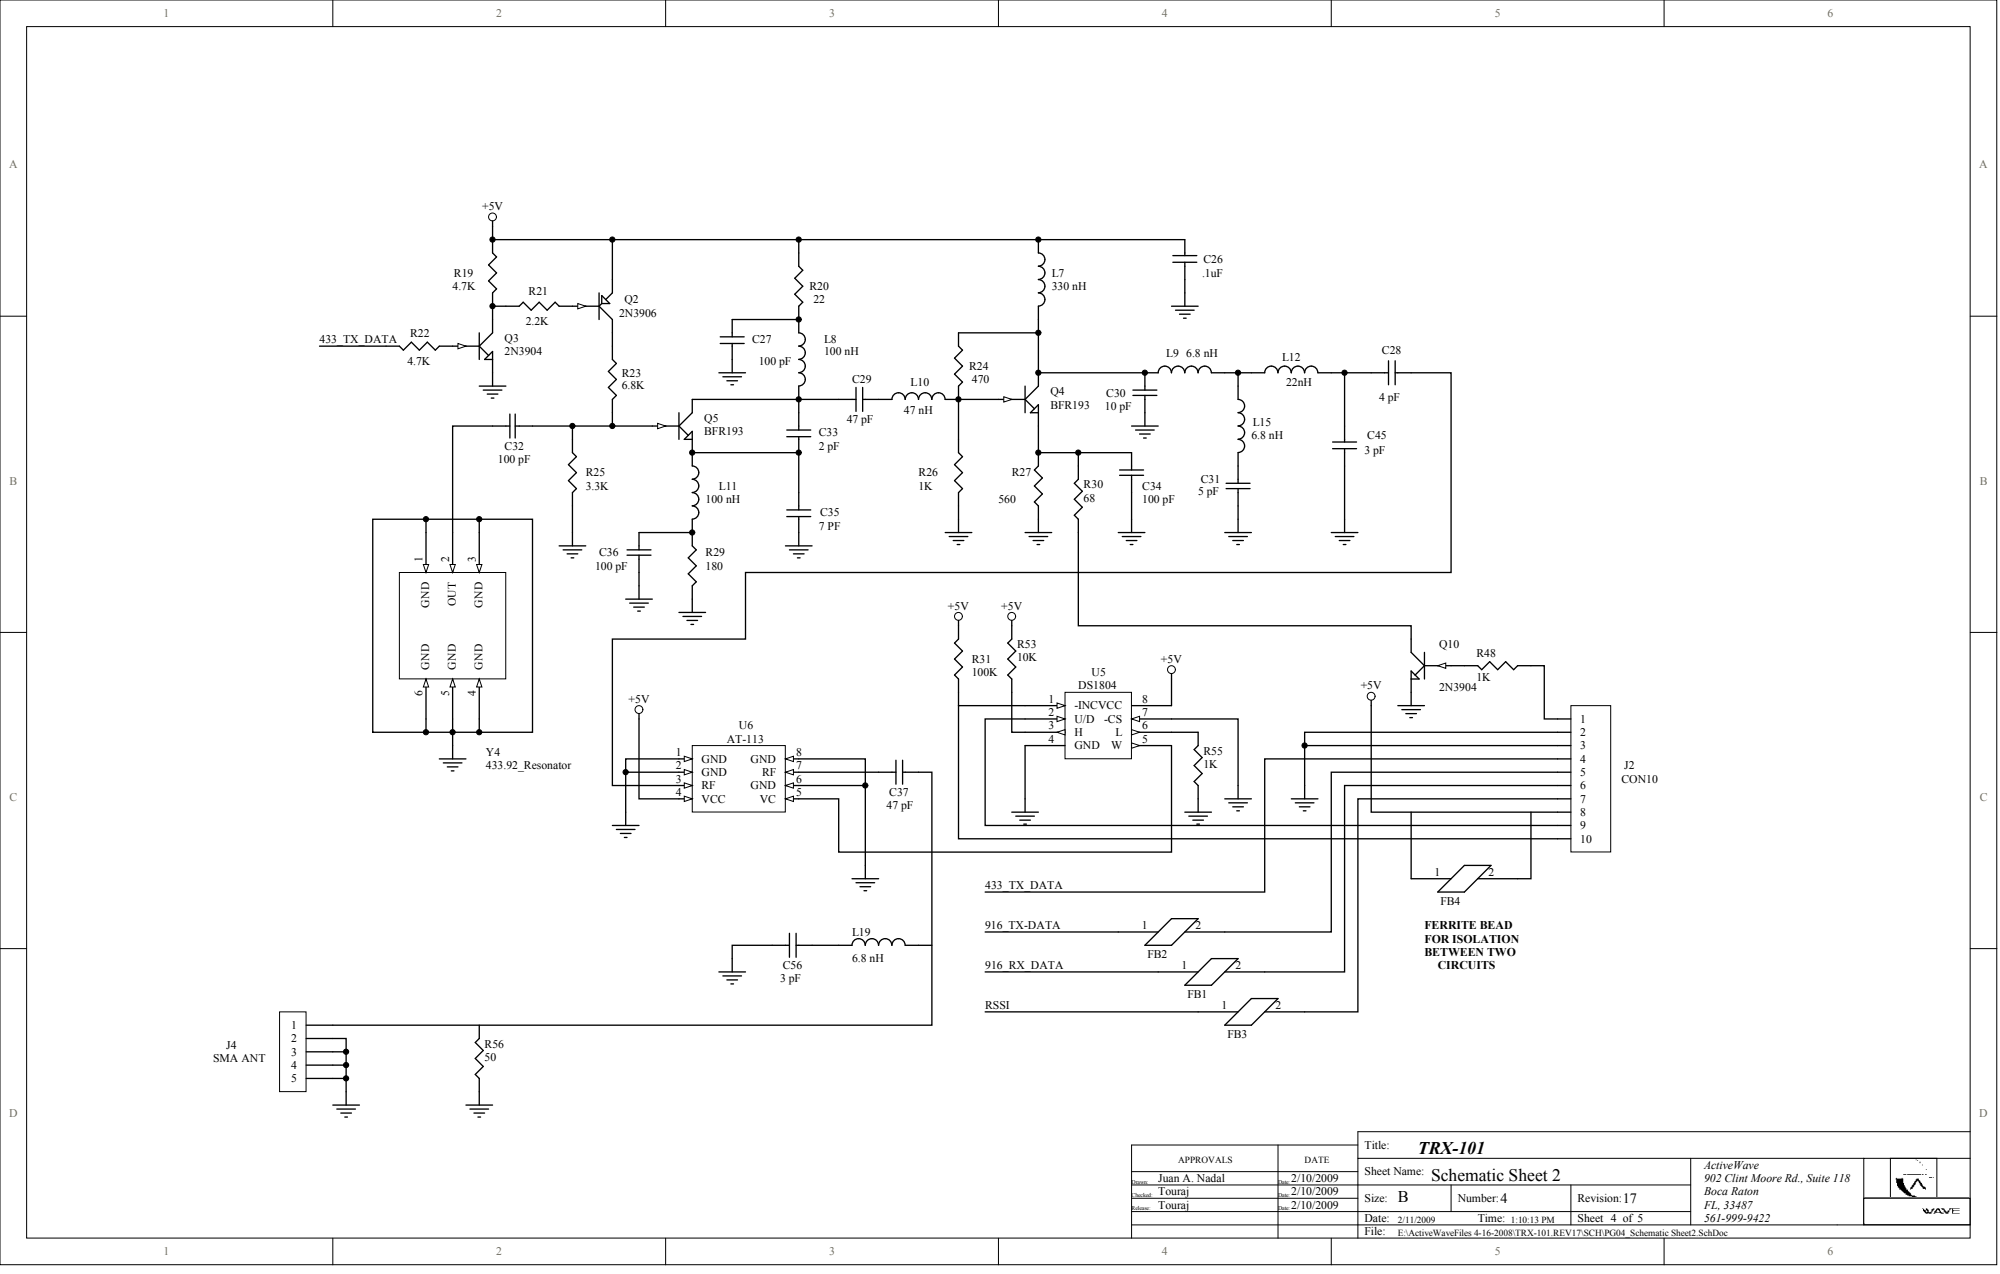
[picture p39: page 4]

APPROVAL S | DAT E

Schematic Sheet 2 Sheet Name: 2/10/2009 | ActiveWave 902 Clint Moore Rd., Suite 118 Boca Raton FL, 33487 561-999-9422

Juan A. Nadal D r awn : | D ate :
Touraj Ch e c k e d : | 2/10/2009 D ate : | B Size: | Number: 4 | Revision: 17

Touraj Rele ase : | 2/10/2009 D ate :

Date: File: Time: 2/11/2009 1:10:13 PM | | Sheet 4 of 5

E:\Activ e Wav e Fil es 4-16-2008\TRX-101.REV17\SCH\PG04_Schematic She et2.SchDo c

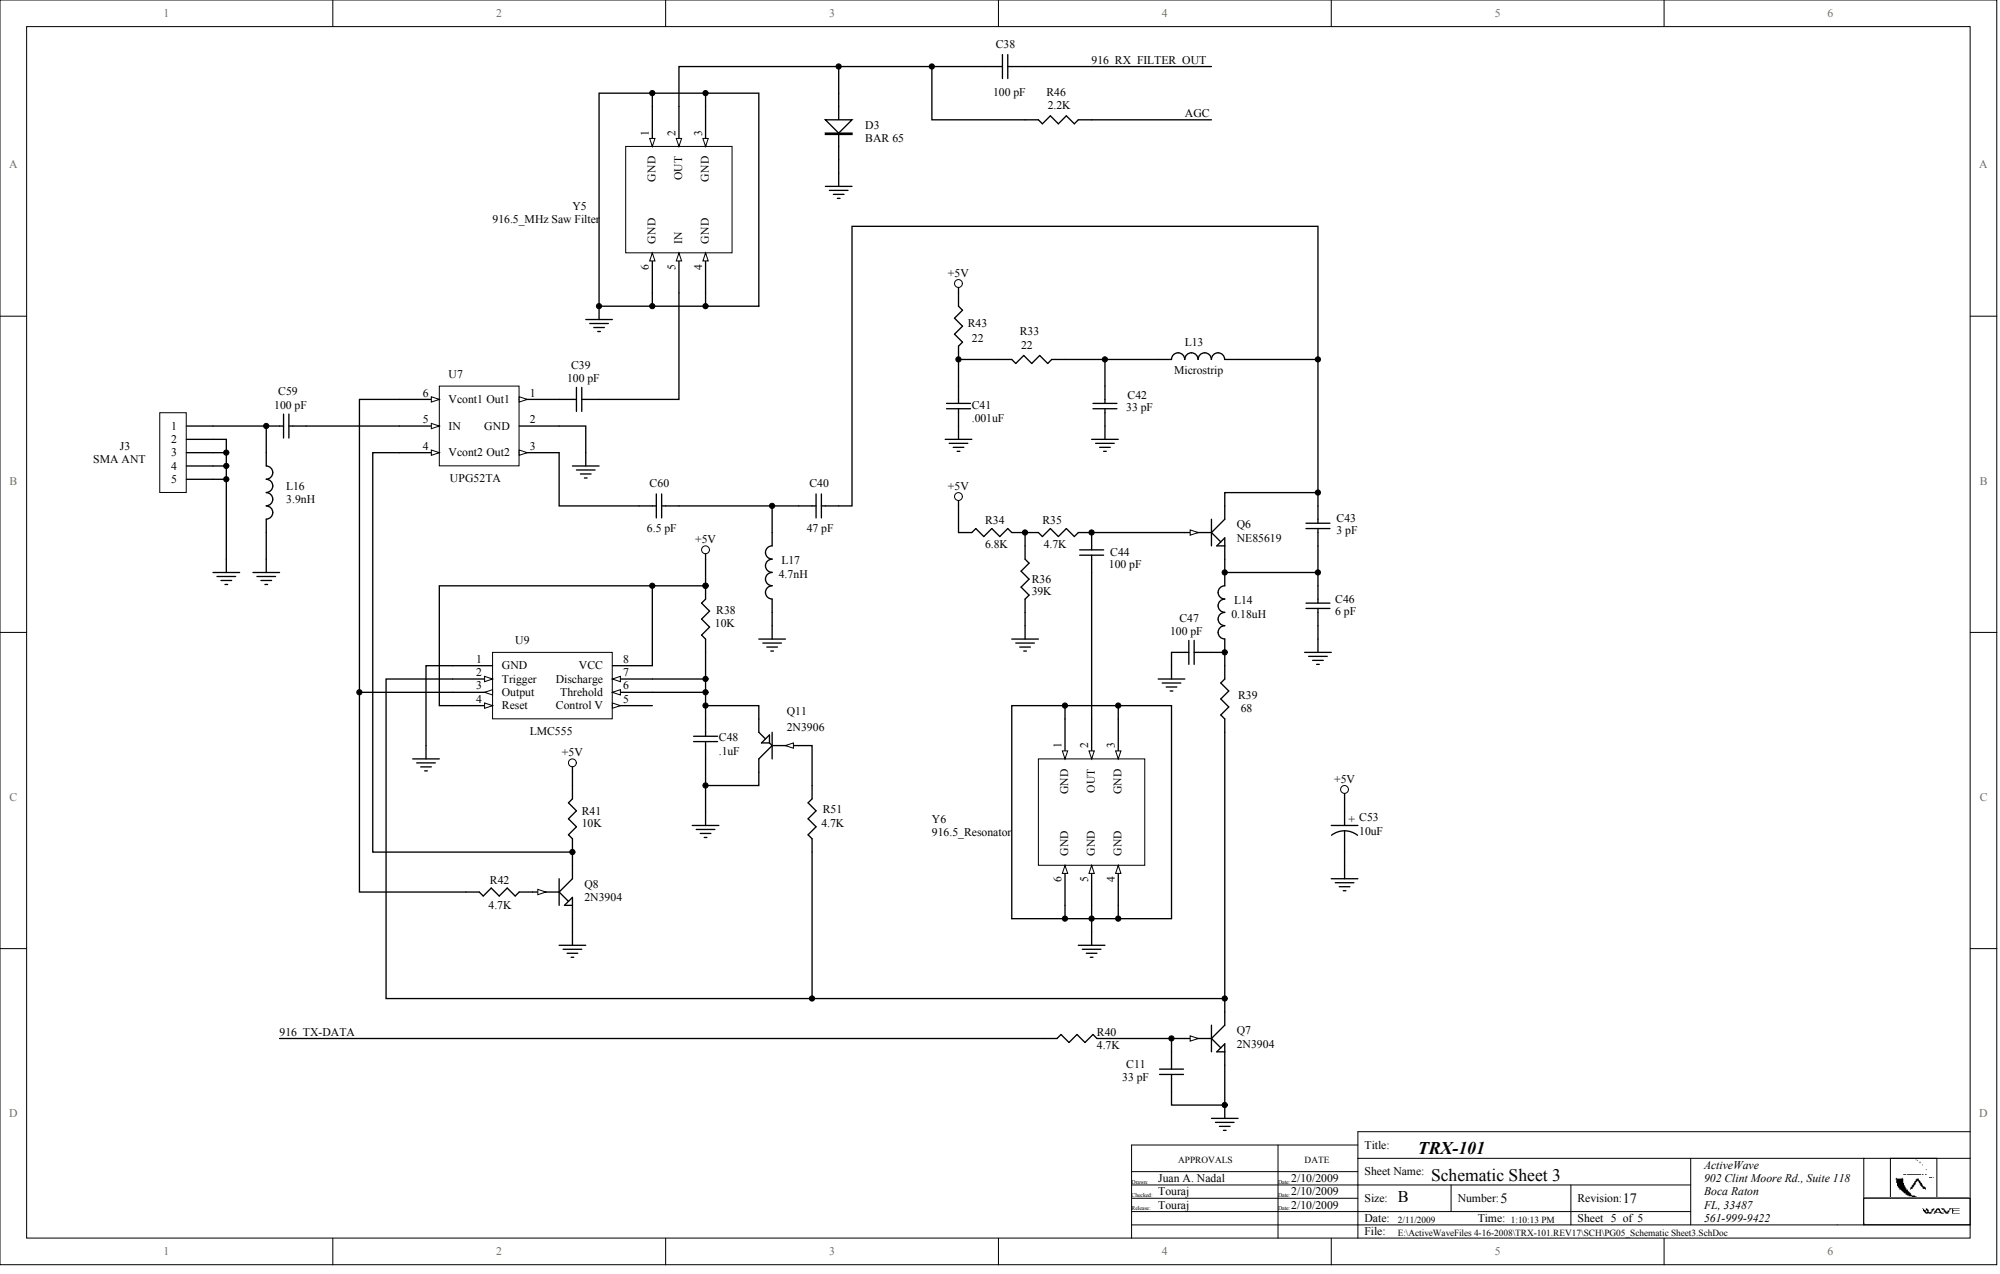
[picture p40: page 5]

2 | | | 5 Threhold 6 Discharge 7 VCC 8

3 P0U903 P0U903 P0U903 P0U903 P0U904 P0U904 P0U904 P0U904 | Output Reset | P0U906 P0U906 P0U906 P0U906 P0U905 P0U905 P0U905 P0U905

APPROVAL S | DAT E

Schematic Sheet 3 Sheet Name: 2/10/2009 | ActiveWave 902 Clint Moore Rd., Suite 118 Boca Raton FL, 33487 561-999-9422

Juan A. Nadal D r awn : | D ate :
Touraj Ch e c k e d : | 2/10/2009 D ate : | B Size: | Number: 5 | Revision: 17

Touraj Rele ase : | 2/10/2009 D ate :

Date: File: Time: 2/11/2009 1:10:13 PM | | Sheet 5 of 5

E:\Activ e Wav e Fil es 4-16-2008\TRX-101.REV17\SCH\PG05_Schematic She et3.SchDo c
