tourajghaffari/tigerfid/protel-files/field-generators/fgen-calibration-tool/Top Copper.pdf

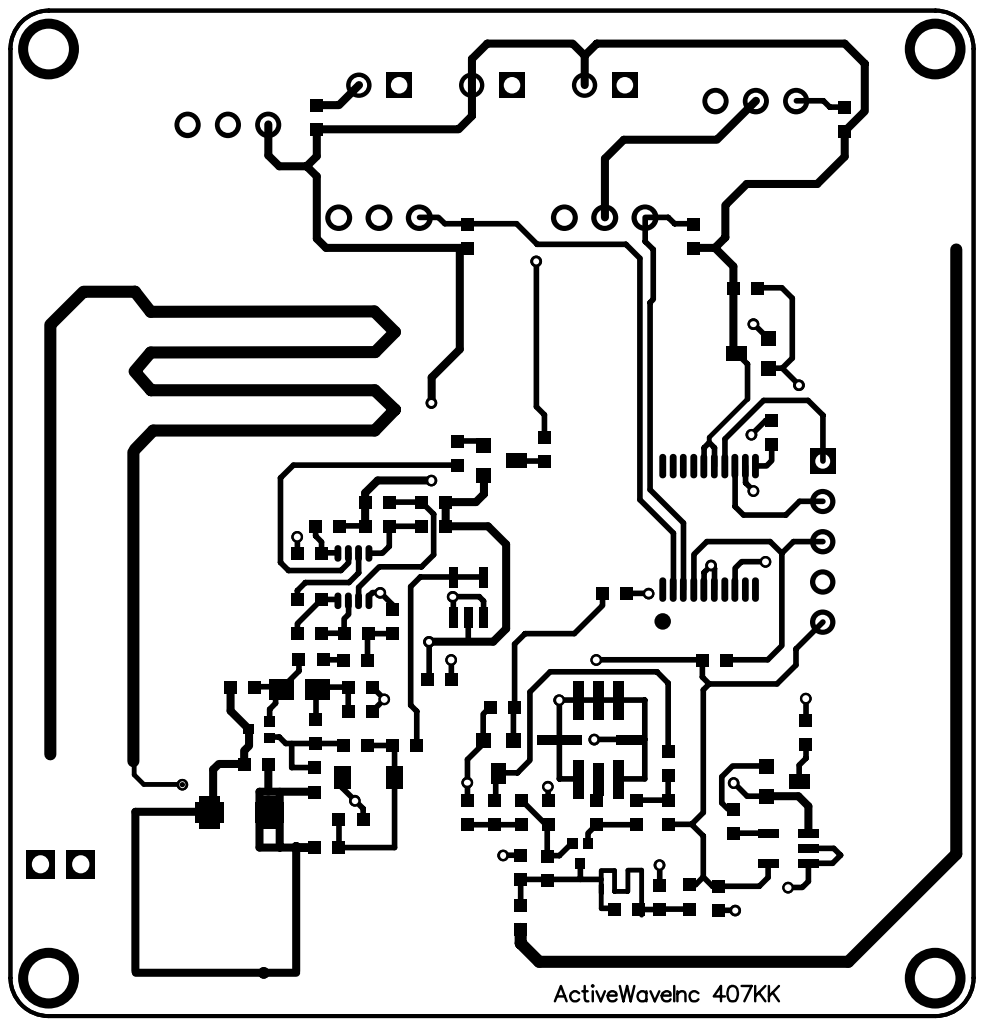
[picture p51: page 1]
