tourajghaffari/tigerfid/protel-files/field-generators/fgen-calibration-tool/Top Silk Screen.pdf

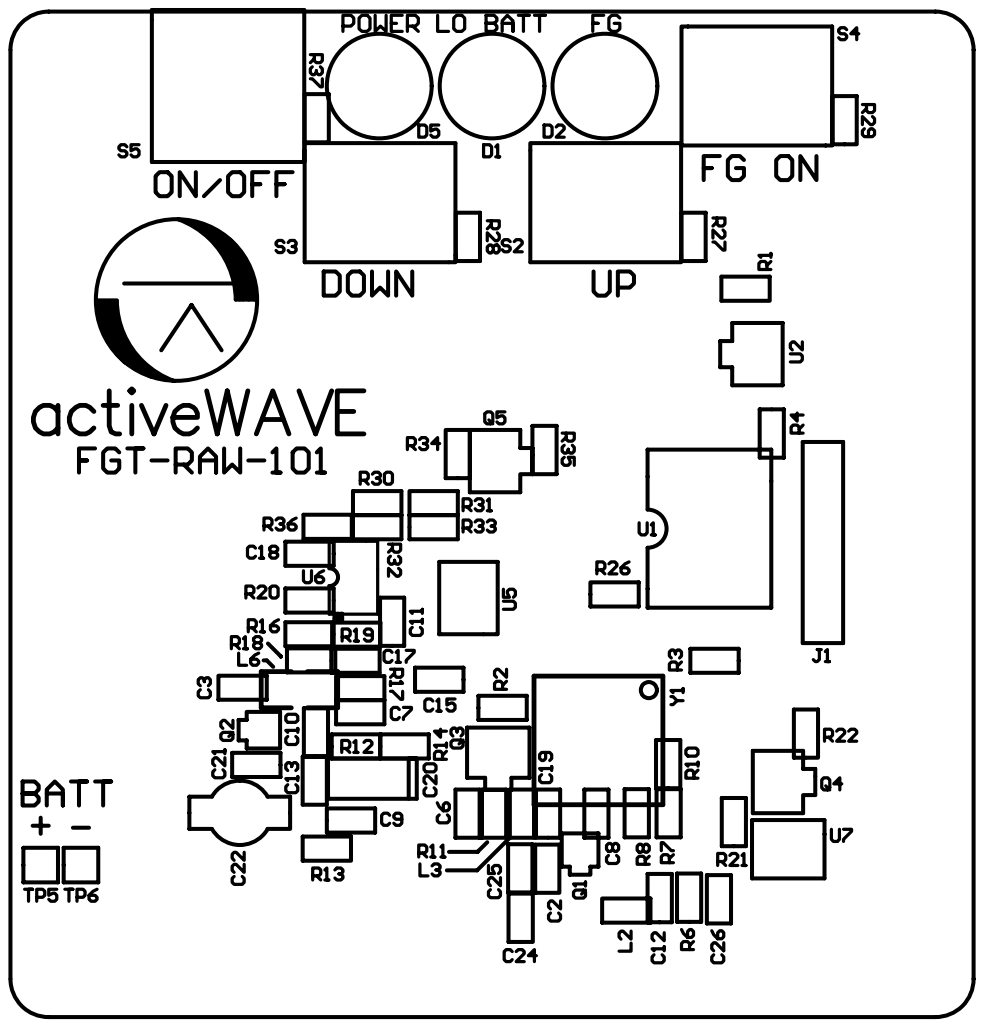
[picture p52: page 1]
