tourajghaffari/tigerfid/protel-files/reader/pcmcia-reader/pdfs/Digital and PS Schematic.pdf

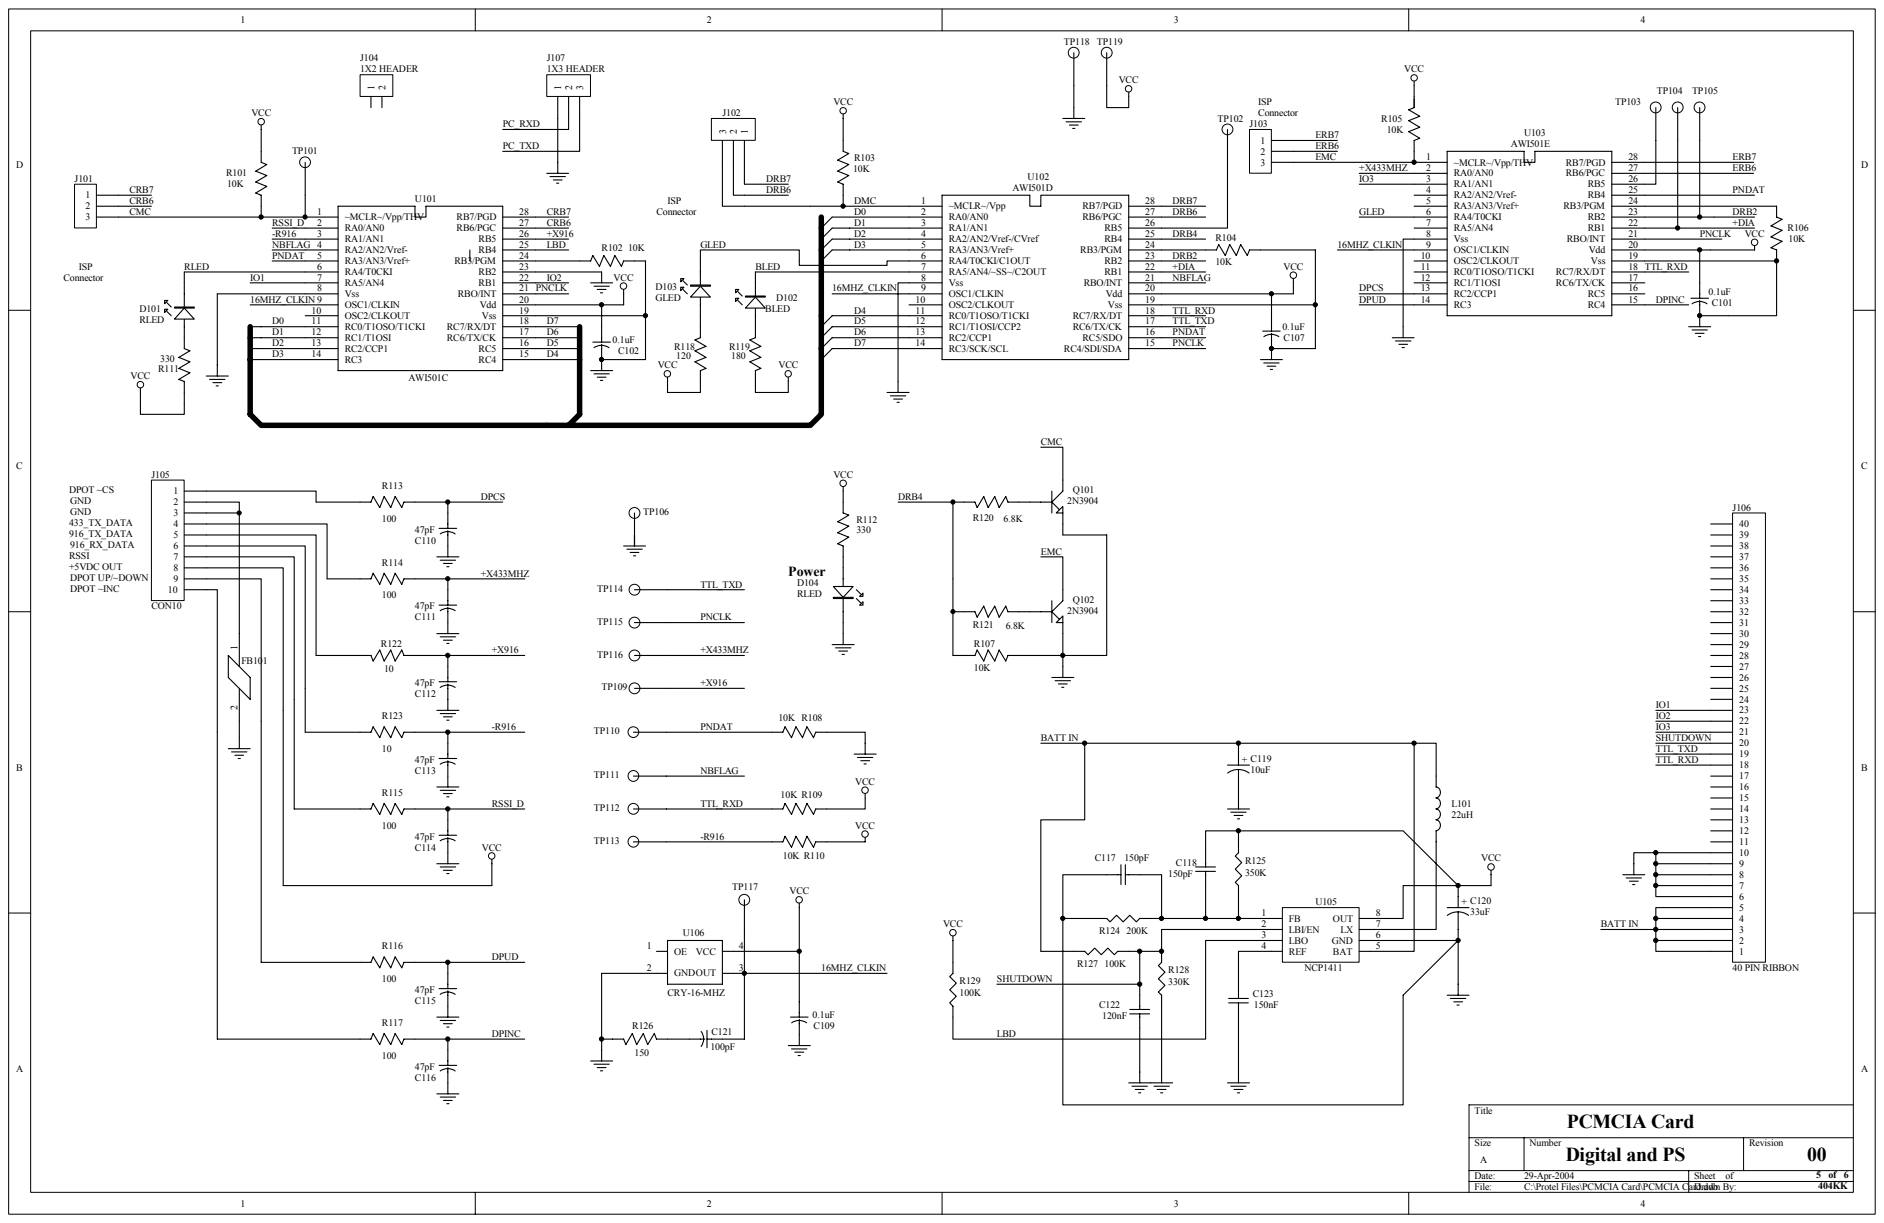
[picture p53: page 1]

Size A | Number Digital and PS | Revision 00

Date: 29-Apr-2004 | Sheet of 5 of 6
File: C:\Protel Files\PCMCIA Card\PCMCIA Card.ddb Drawn By: | 404KK
