tourajghaffari/tigerfid/protel-files/reader/reader-rs232-new-case/rev6/Schematic Prints.pdf

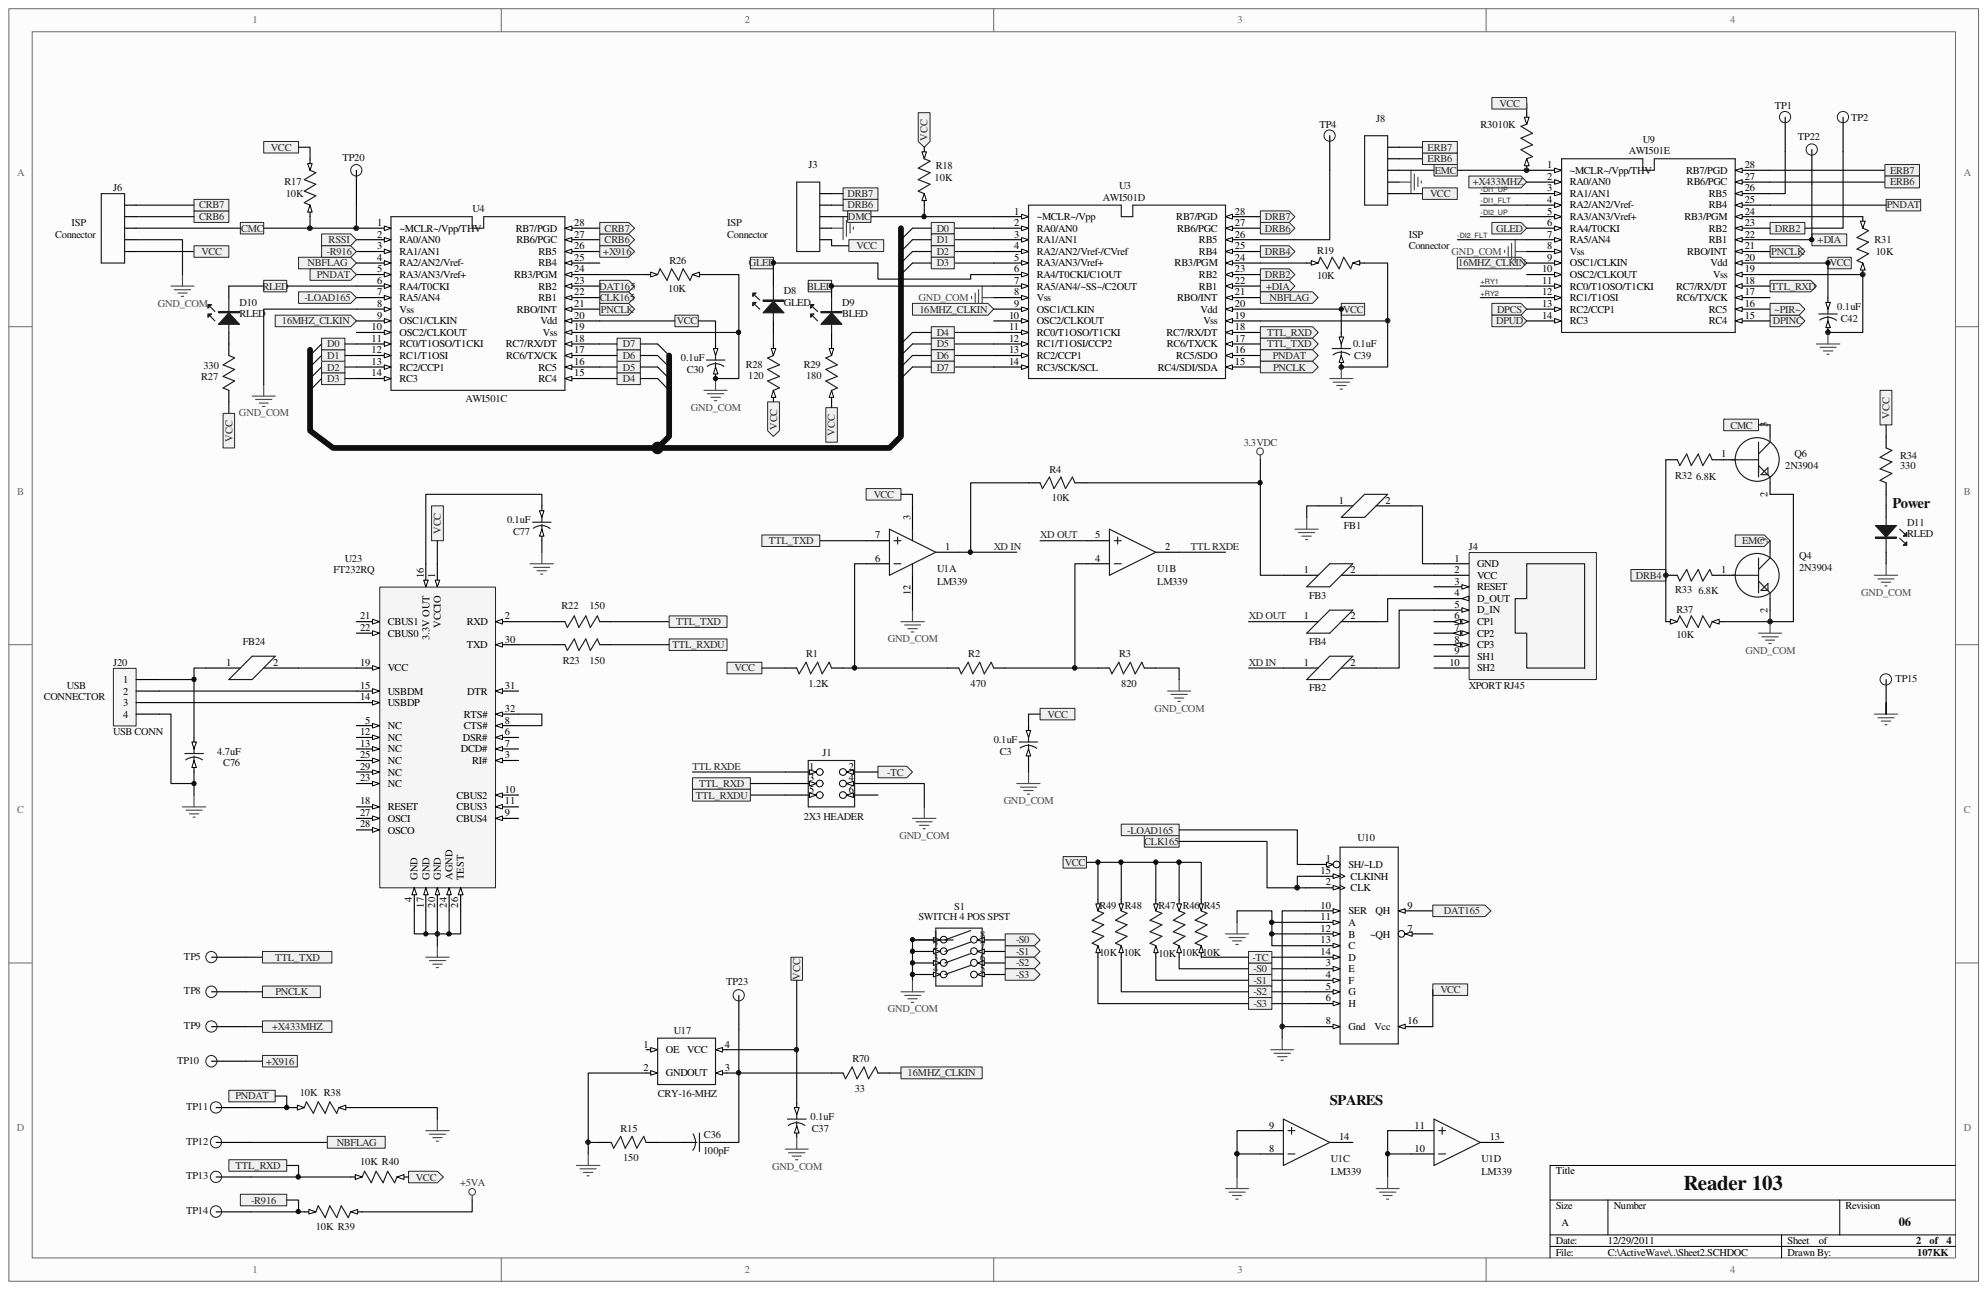
[picture p54: page 1]
