tourajghaffari/tigerfid/protel-files/reader/compact-flash-reader/rev2-new/Schematic Prints.pdf

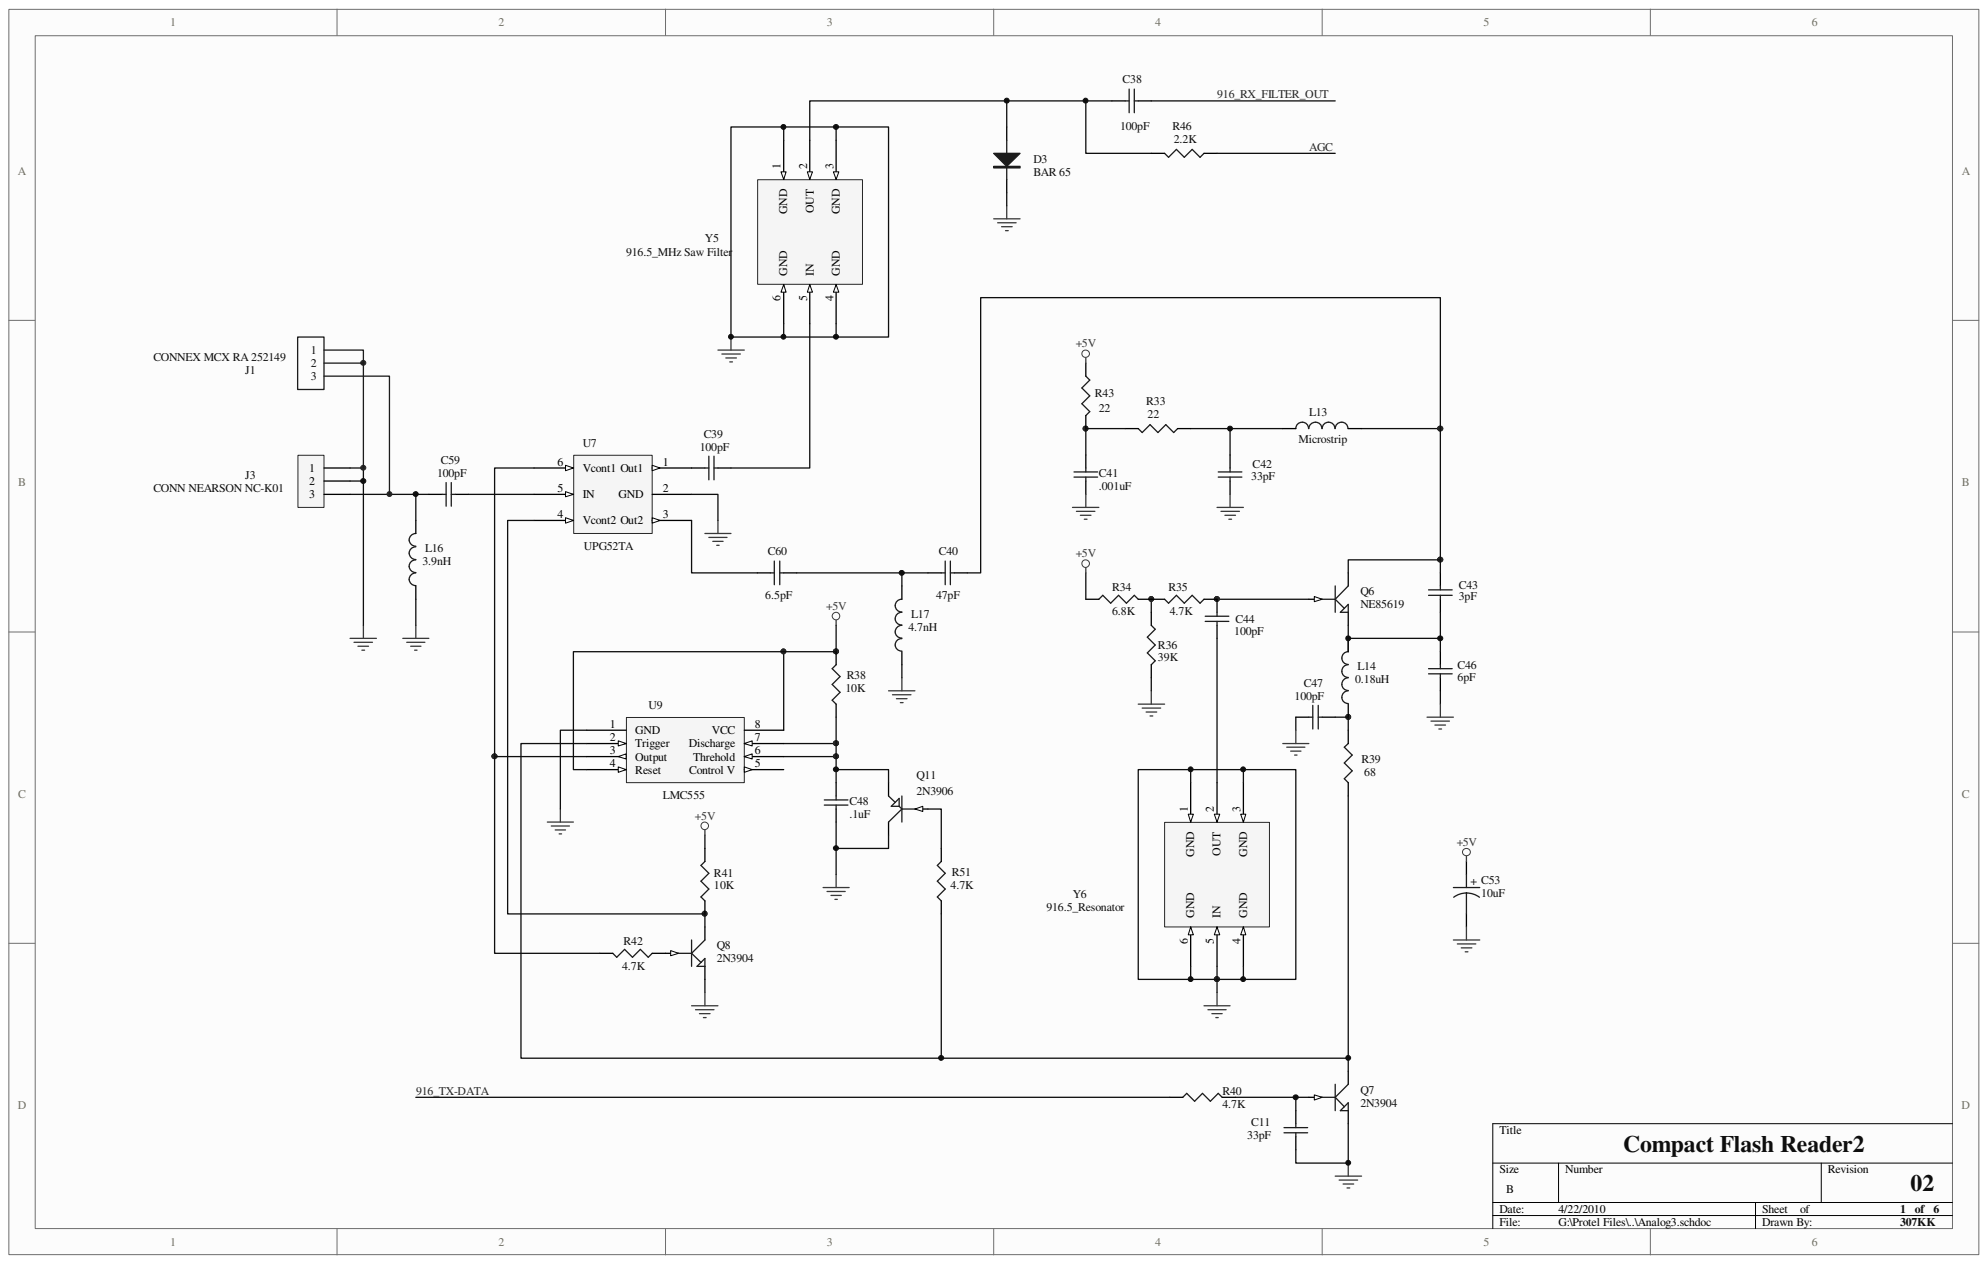
[picture p55: page 1]
