tourajghaffari/tigerfid/protel-files/tags/medium-tag/102-rev21/schematic-1.pdf

# TRANSMITTER

# 916Mhz

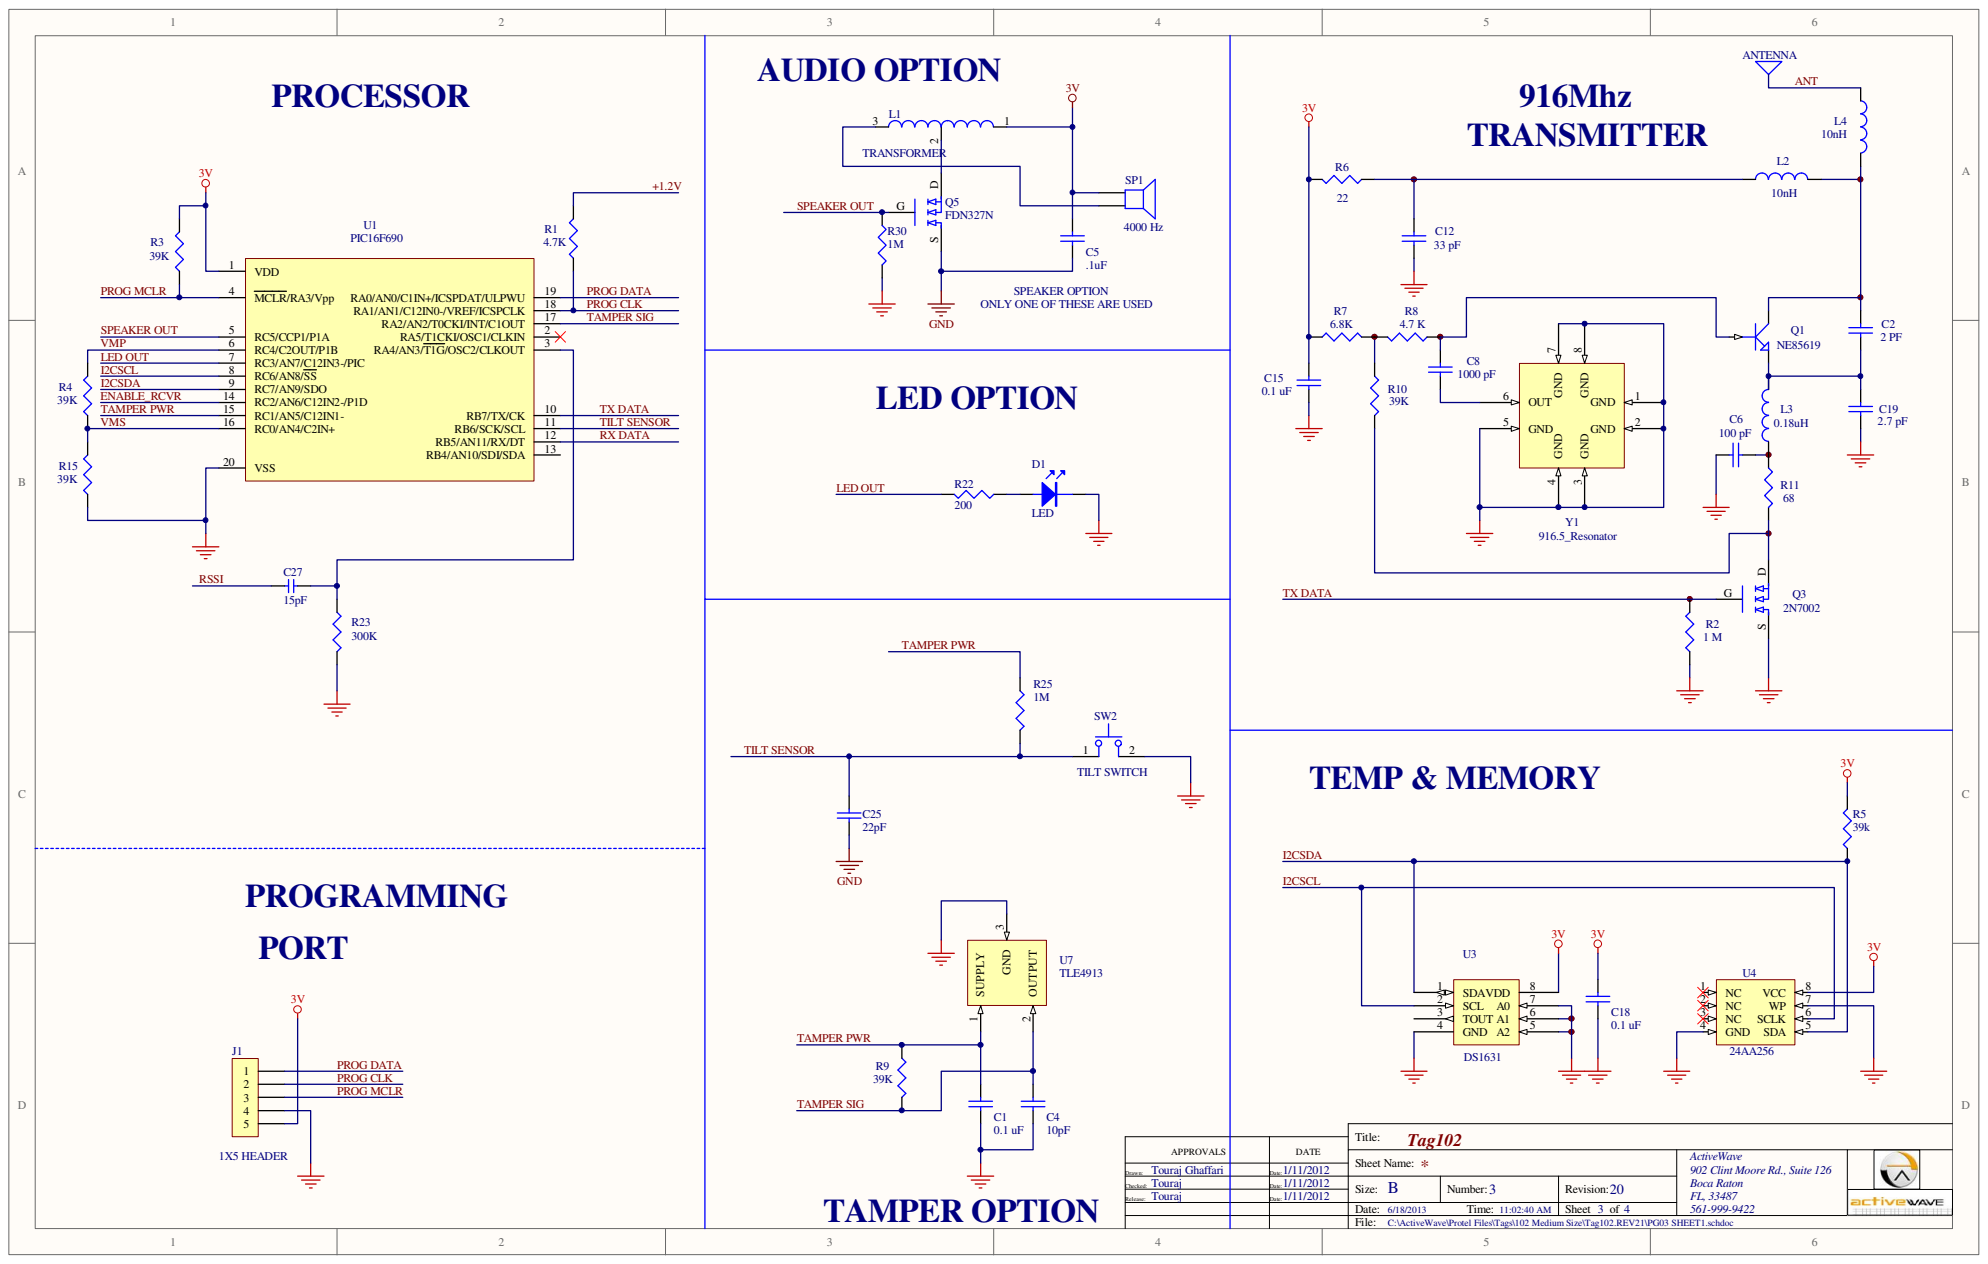
[picture p56: page 1]

ONLY ONE OF THESE ARE USED

ActiveWave
902 Clint Moore Rd., Suite 126
Boca Raton

Touraj Ghaffari Drawn: | Date:
Touraj Checked: | 1/11/2012 Date: Size: B | Number: 3 20 | Revision:

Touraj Release: | 1/11/2012 Date:

C:\ActiveWave\Protel Files\Tags\102 Medium Size\Tag102.REV21\PG03 SHEET1.schdoc
