tourajghaffari/tigerfid/protel-files/reader/pcmcia-reader/pcmcia-card-with-level-shifter/pdfs/Schematic Page1.pdf

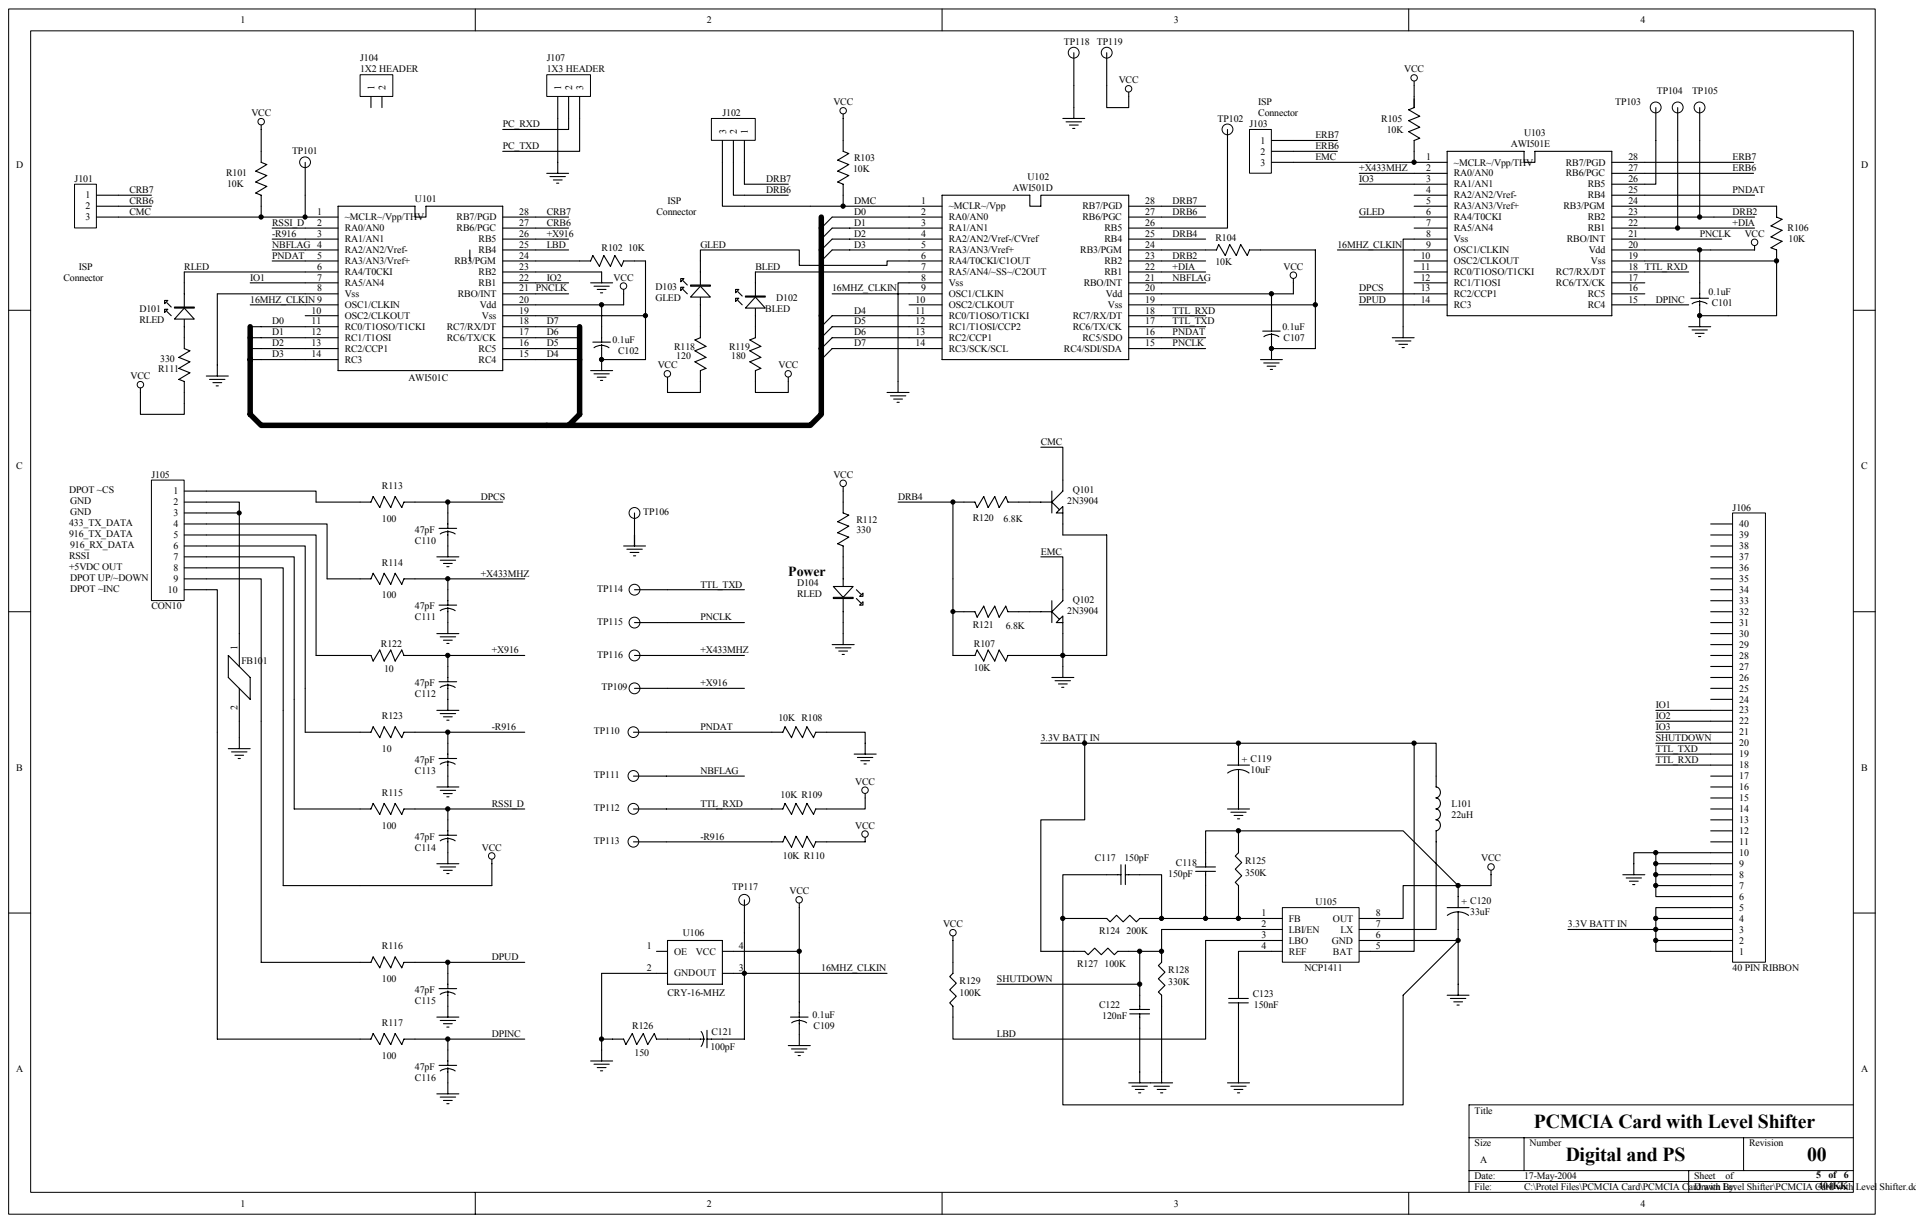
[picture p57: page 1]

Title
PCMCIA Card with Level Shifter

Size A | Number Digital and PS | Revision 00

Date: 17-May-2004 | Sheet of 5 of 6
