tourajghaffari/tigerfid/sealtag/protel-files/seal-tag/2012-04-09-rev4/project-outputs-for-201-rev4/Drill Drawing_Guides.pdf

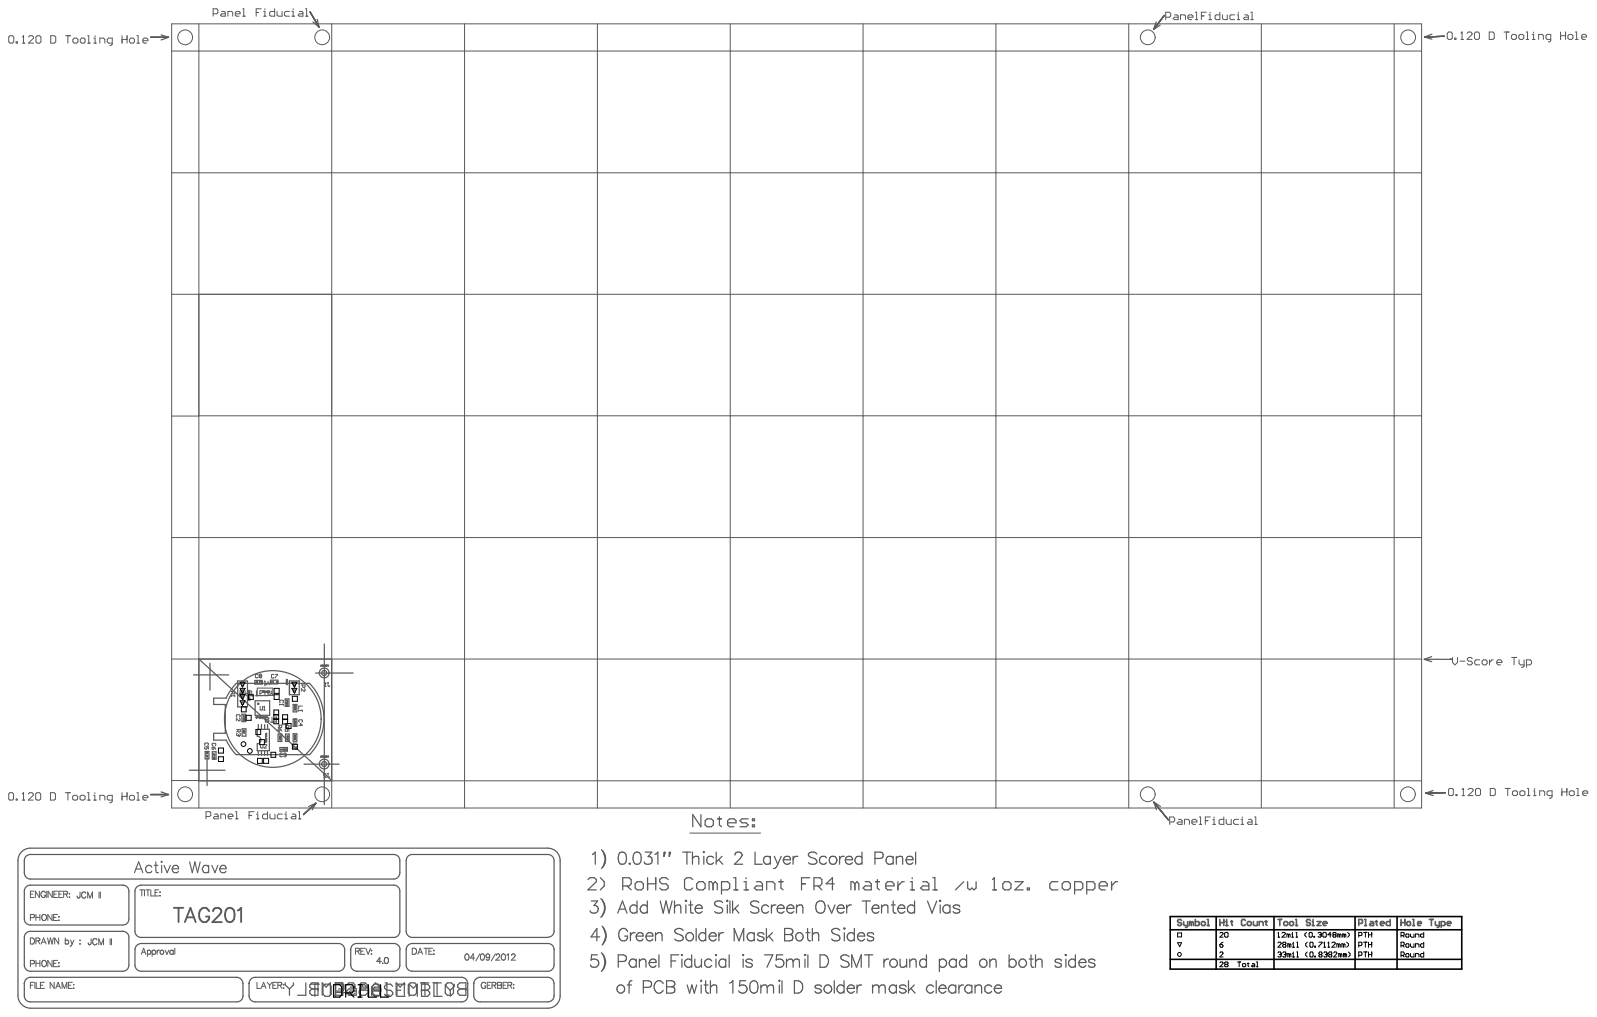
[picture p58: page 1]

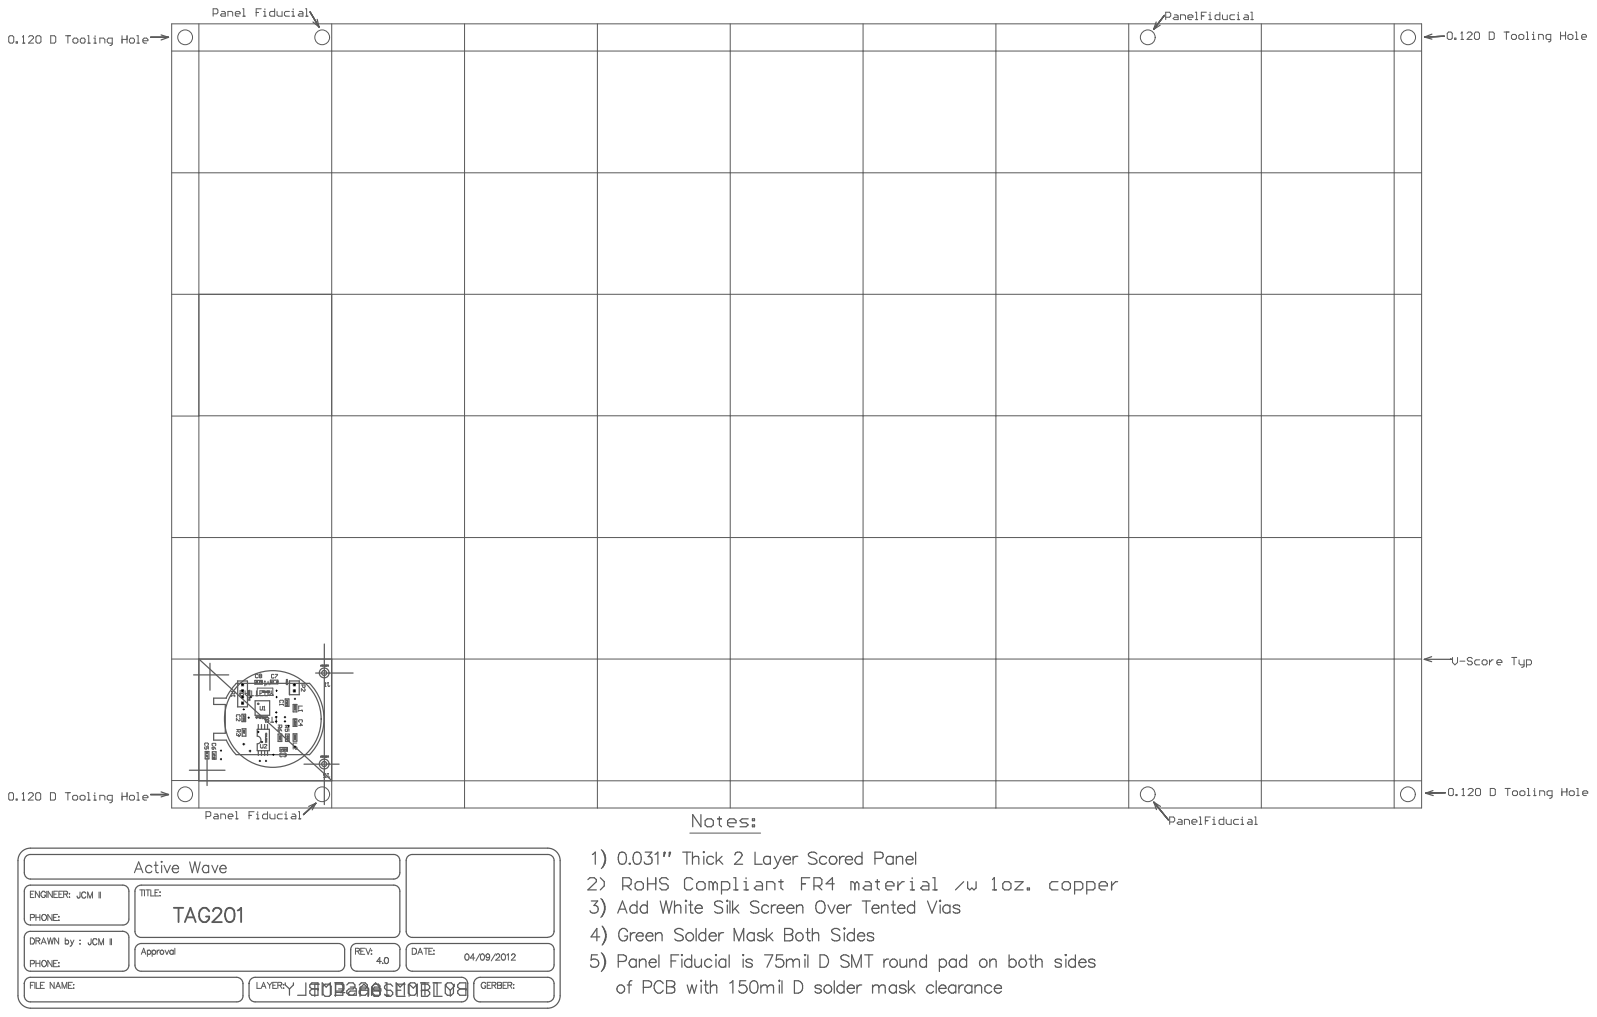
[picture p59: page 2]
