tourajghaffari/tigerfid/protel-files/reader/pcmcia-reader/pcmcia-card-with-level-shifter/latest/pdfs/Analog1 Schematic.pdf

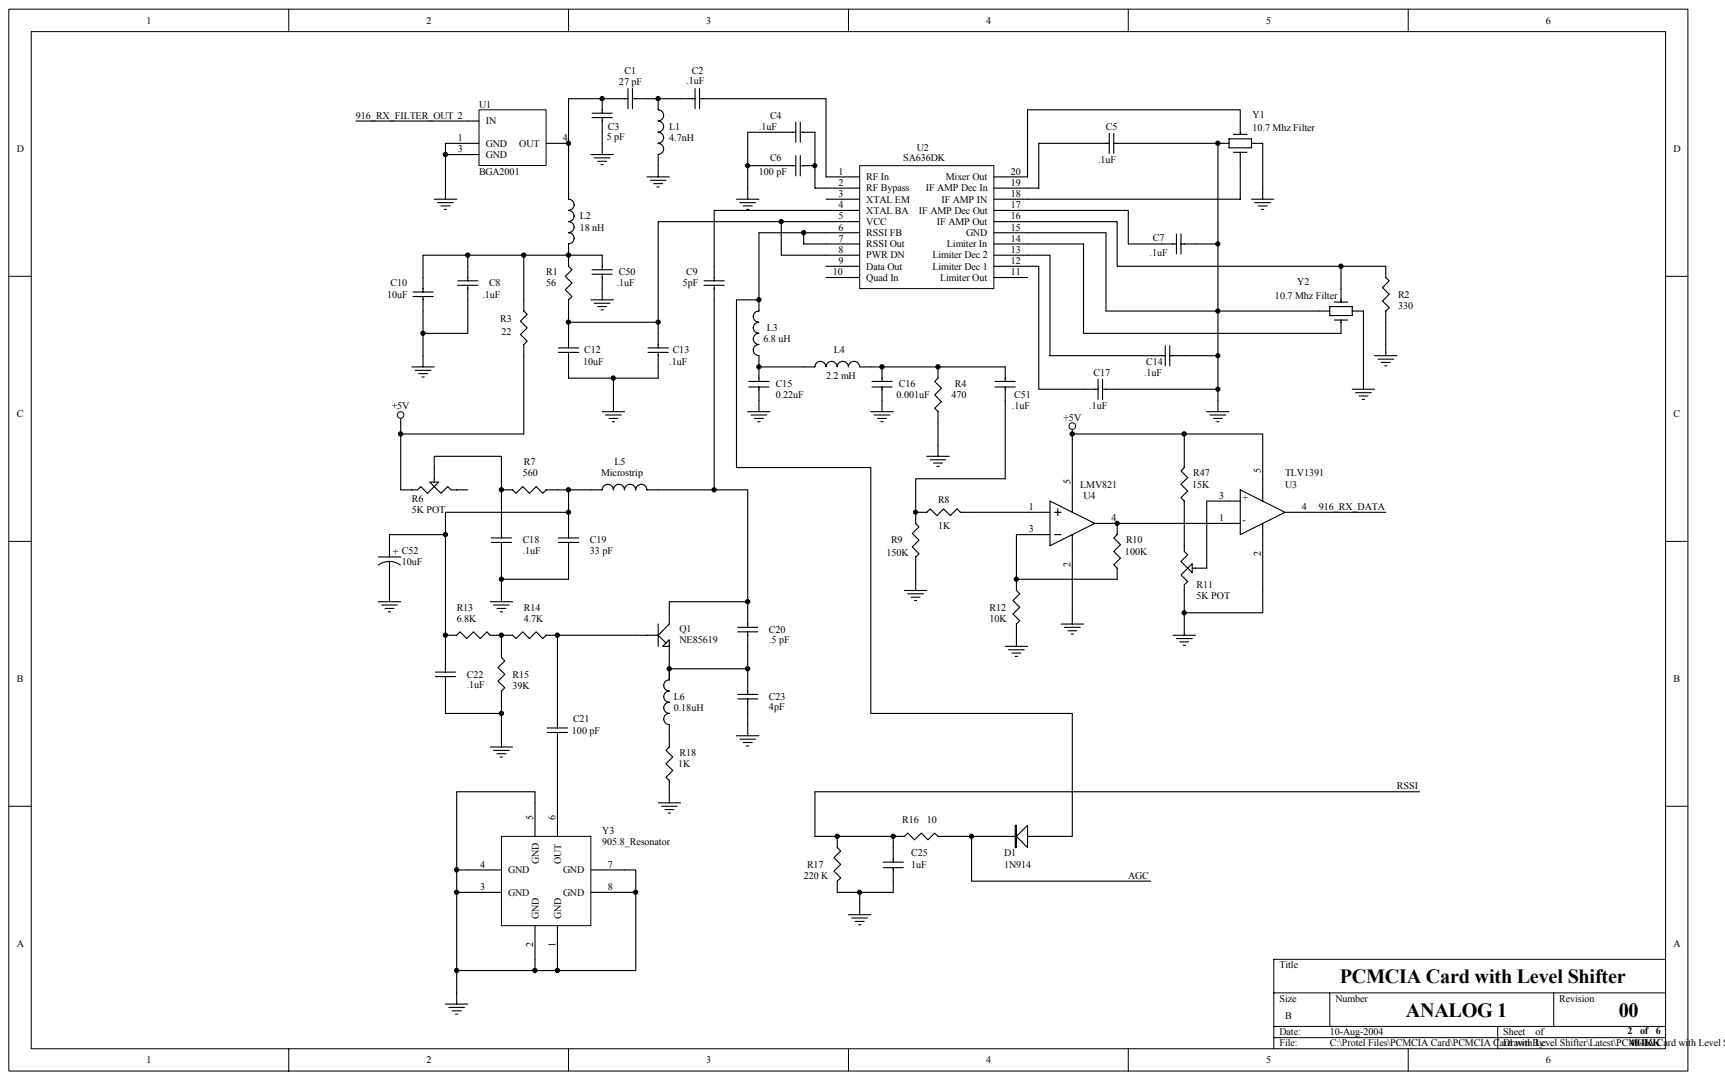
[picture p60: page 1]

RSSI FB 6
RSSI Out 7

Title
PCMCIA Card with Level Shifter

Size B | Number ANALOG 1 | Revision 00

Date: 10-Aug-2004 | Sheet of 2 of 6
