tourajghaffari/tigerfid/protel-files/reader/pcmcia-reader/pcmcia-card-with-level-shifter/latest/pdfs/Analog2 Schematic.pdf

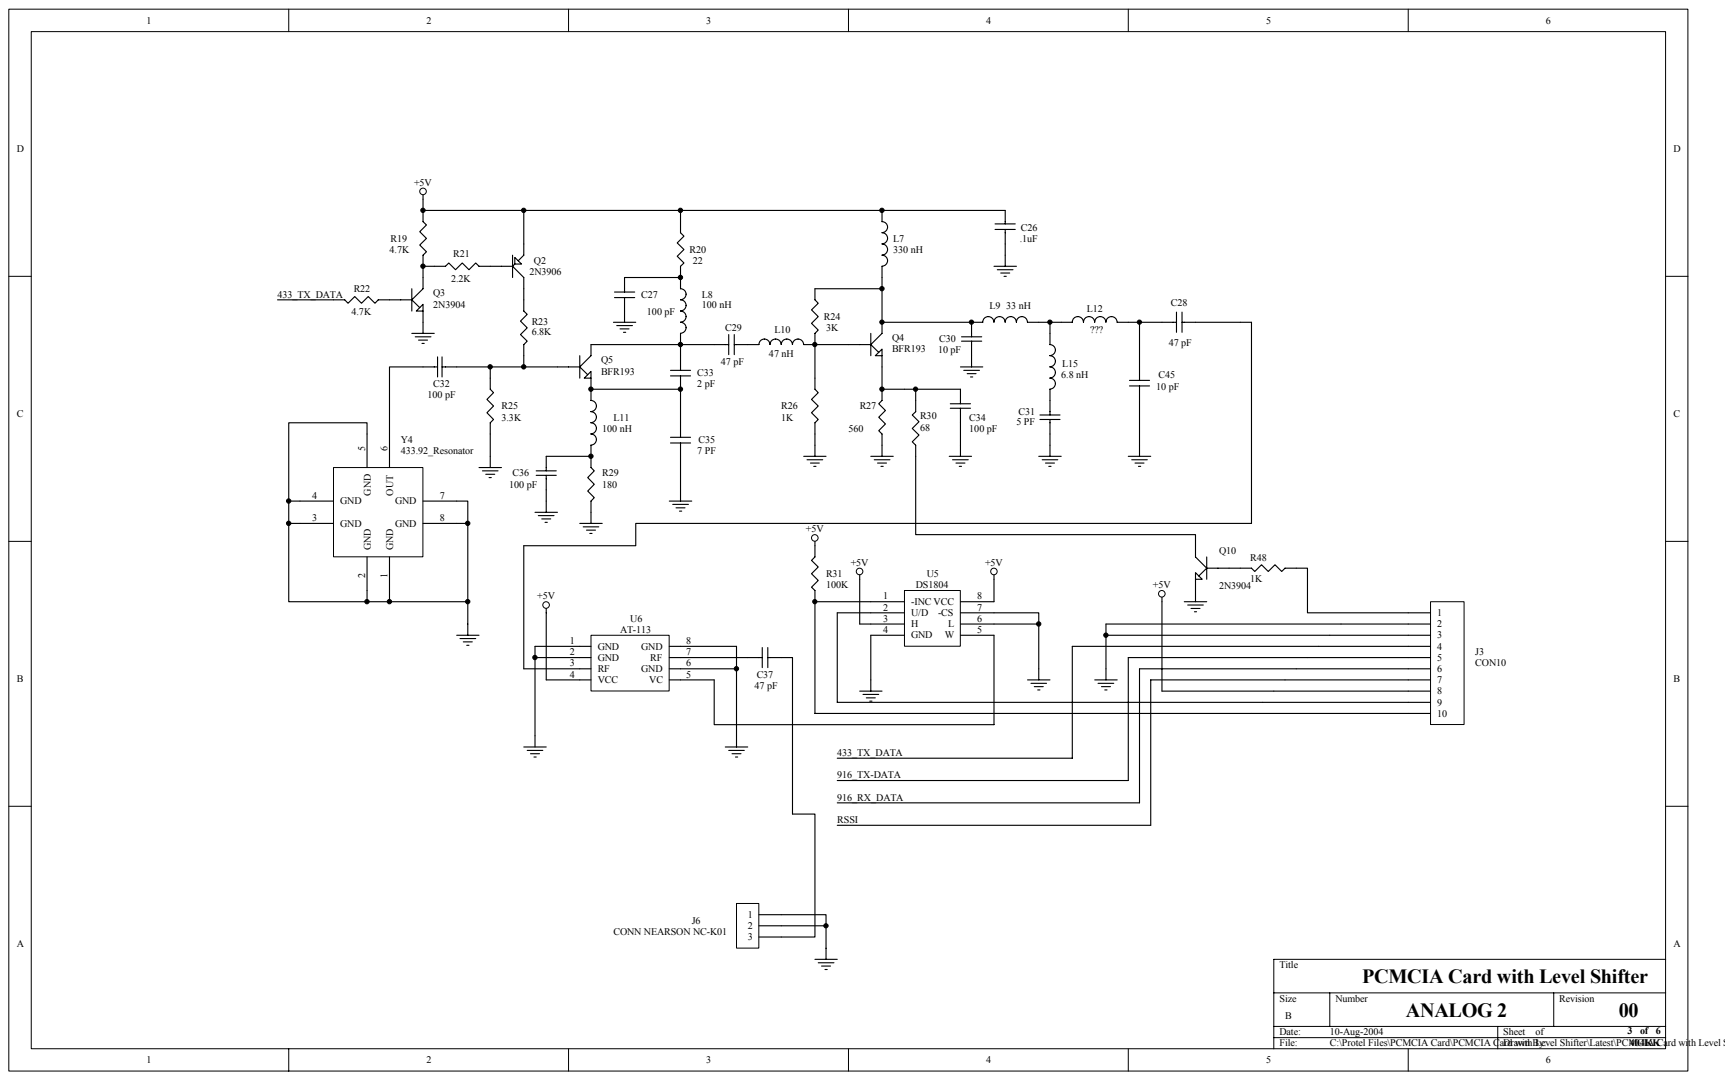
[picture p61: page 1]

PCMCIA Card with Level Shifter

Size B | Number ANALOG 2 | Revision 00

Date: 10-Aug-2004 | Sheet of 3 of 6
