tourajghaffari/tigerfid/protel-files/reader/pcmcia-reader/pcmcia-card-with-level-shifter/latest/pdfs/Analog3 Schematic.pdf

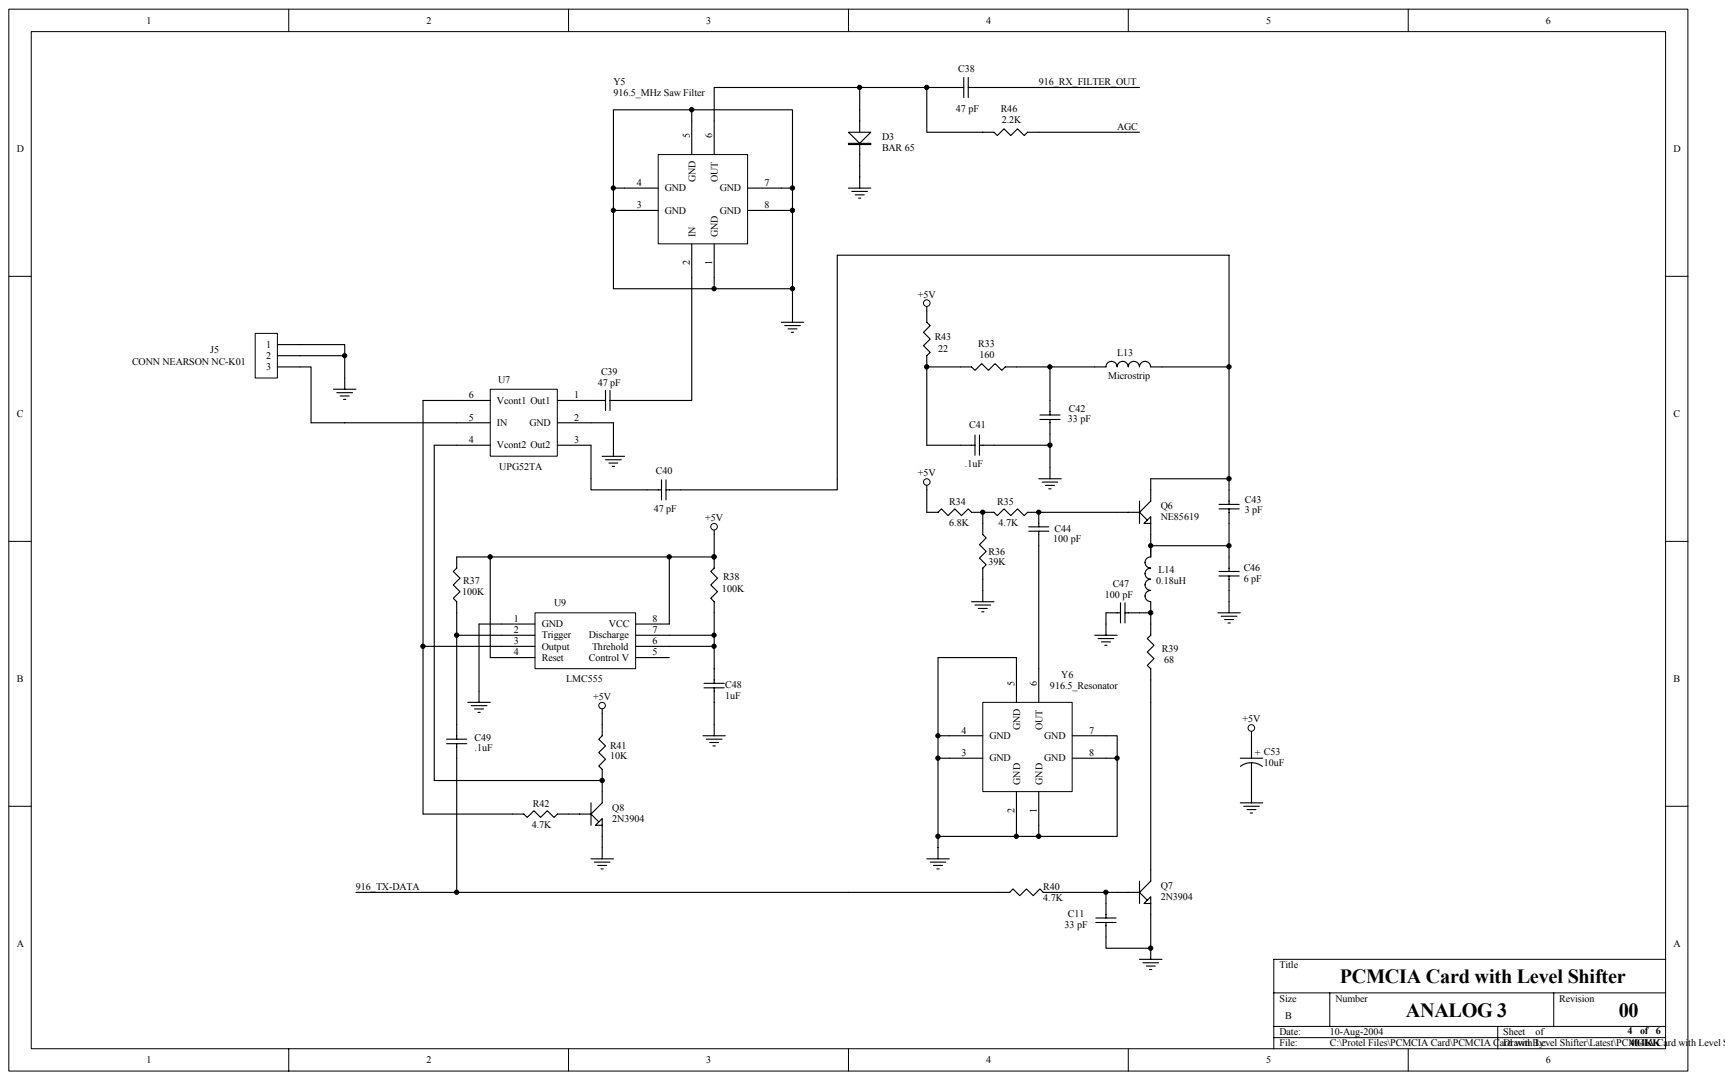
[picture p62: page 1]

Title
PCMCIA Card with Level Shifter

Size B | Number ANALOG 3 | Revision 00

Date: 10-Aug-2004 | Sheet of 4 of 6
