tourajghaffari/tigerfid/protel-files/reader/pcmcia-reader/pcmcia-card-with-level-shifter/latest/pdfs/Bottom Assembly 2.pdf

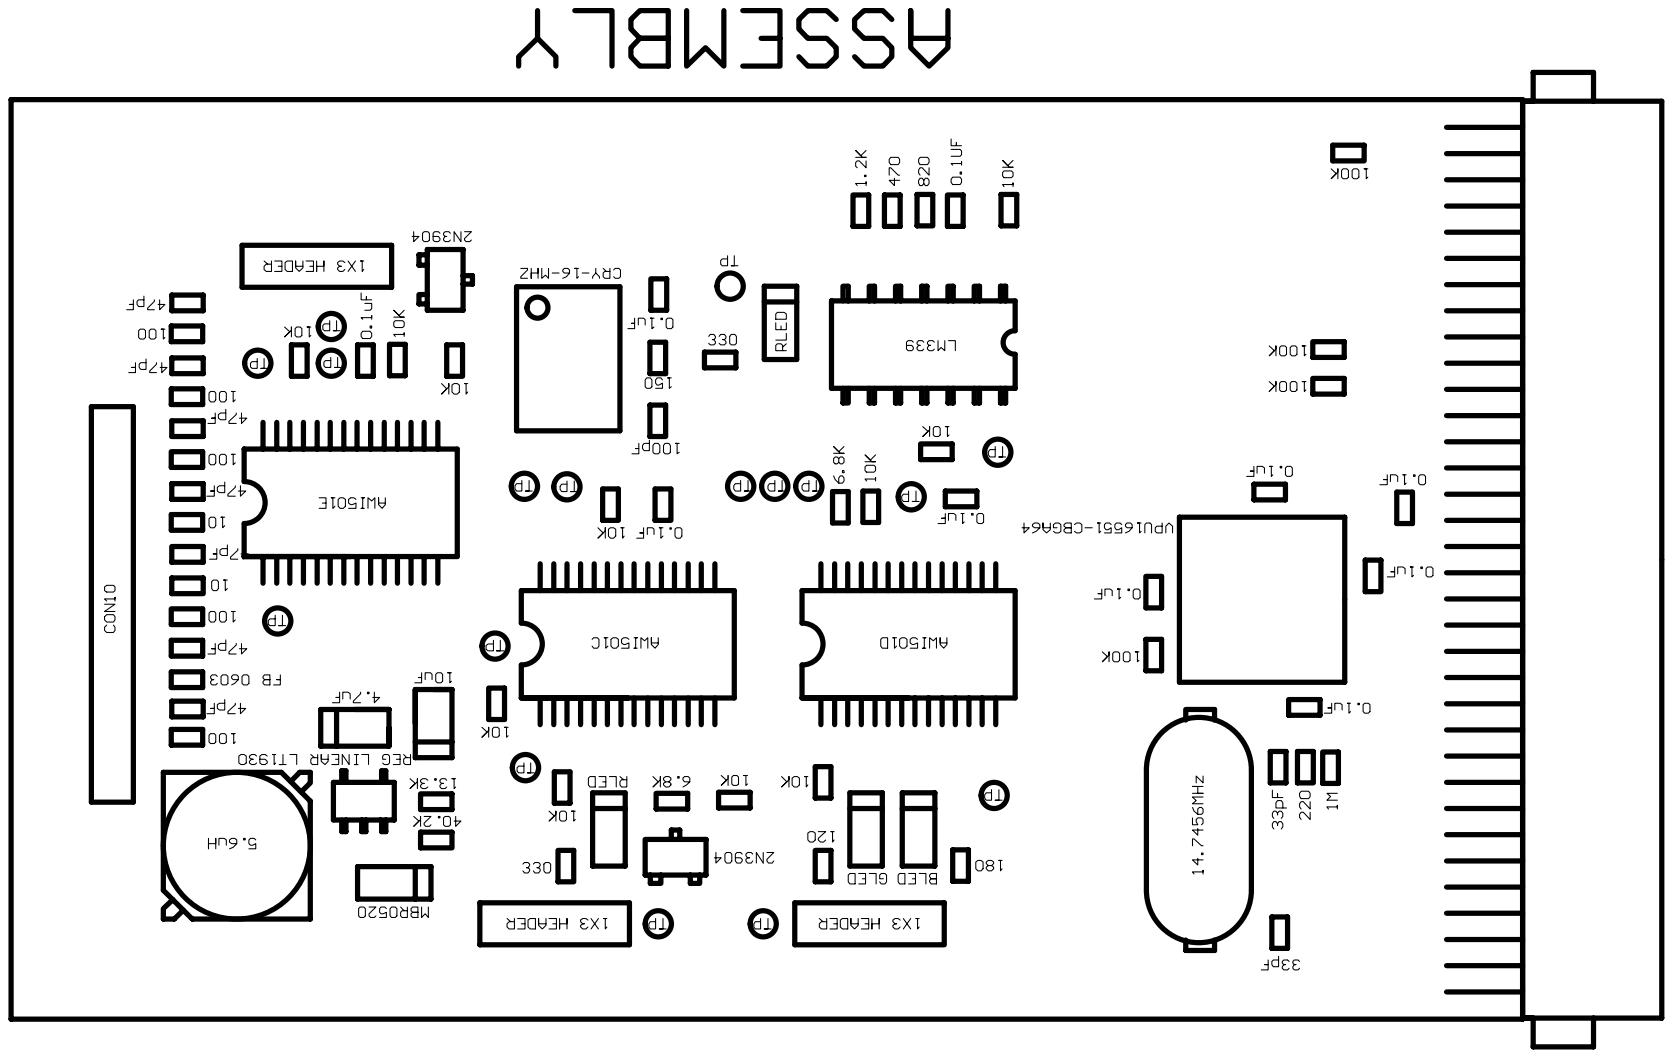
[picture p63: page 1]
