tourajghaffari/tigerfid/protel-files/reader/pcmcia-reader/pcmcia-card-with-level-shifter/latest/pdfs/Digital and PS Schematic.pdf

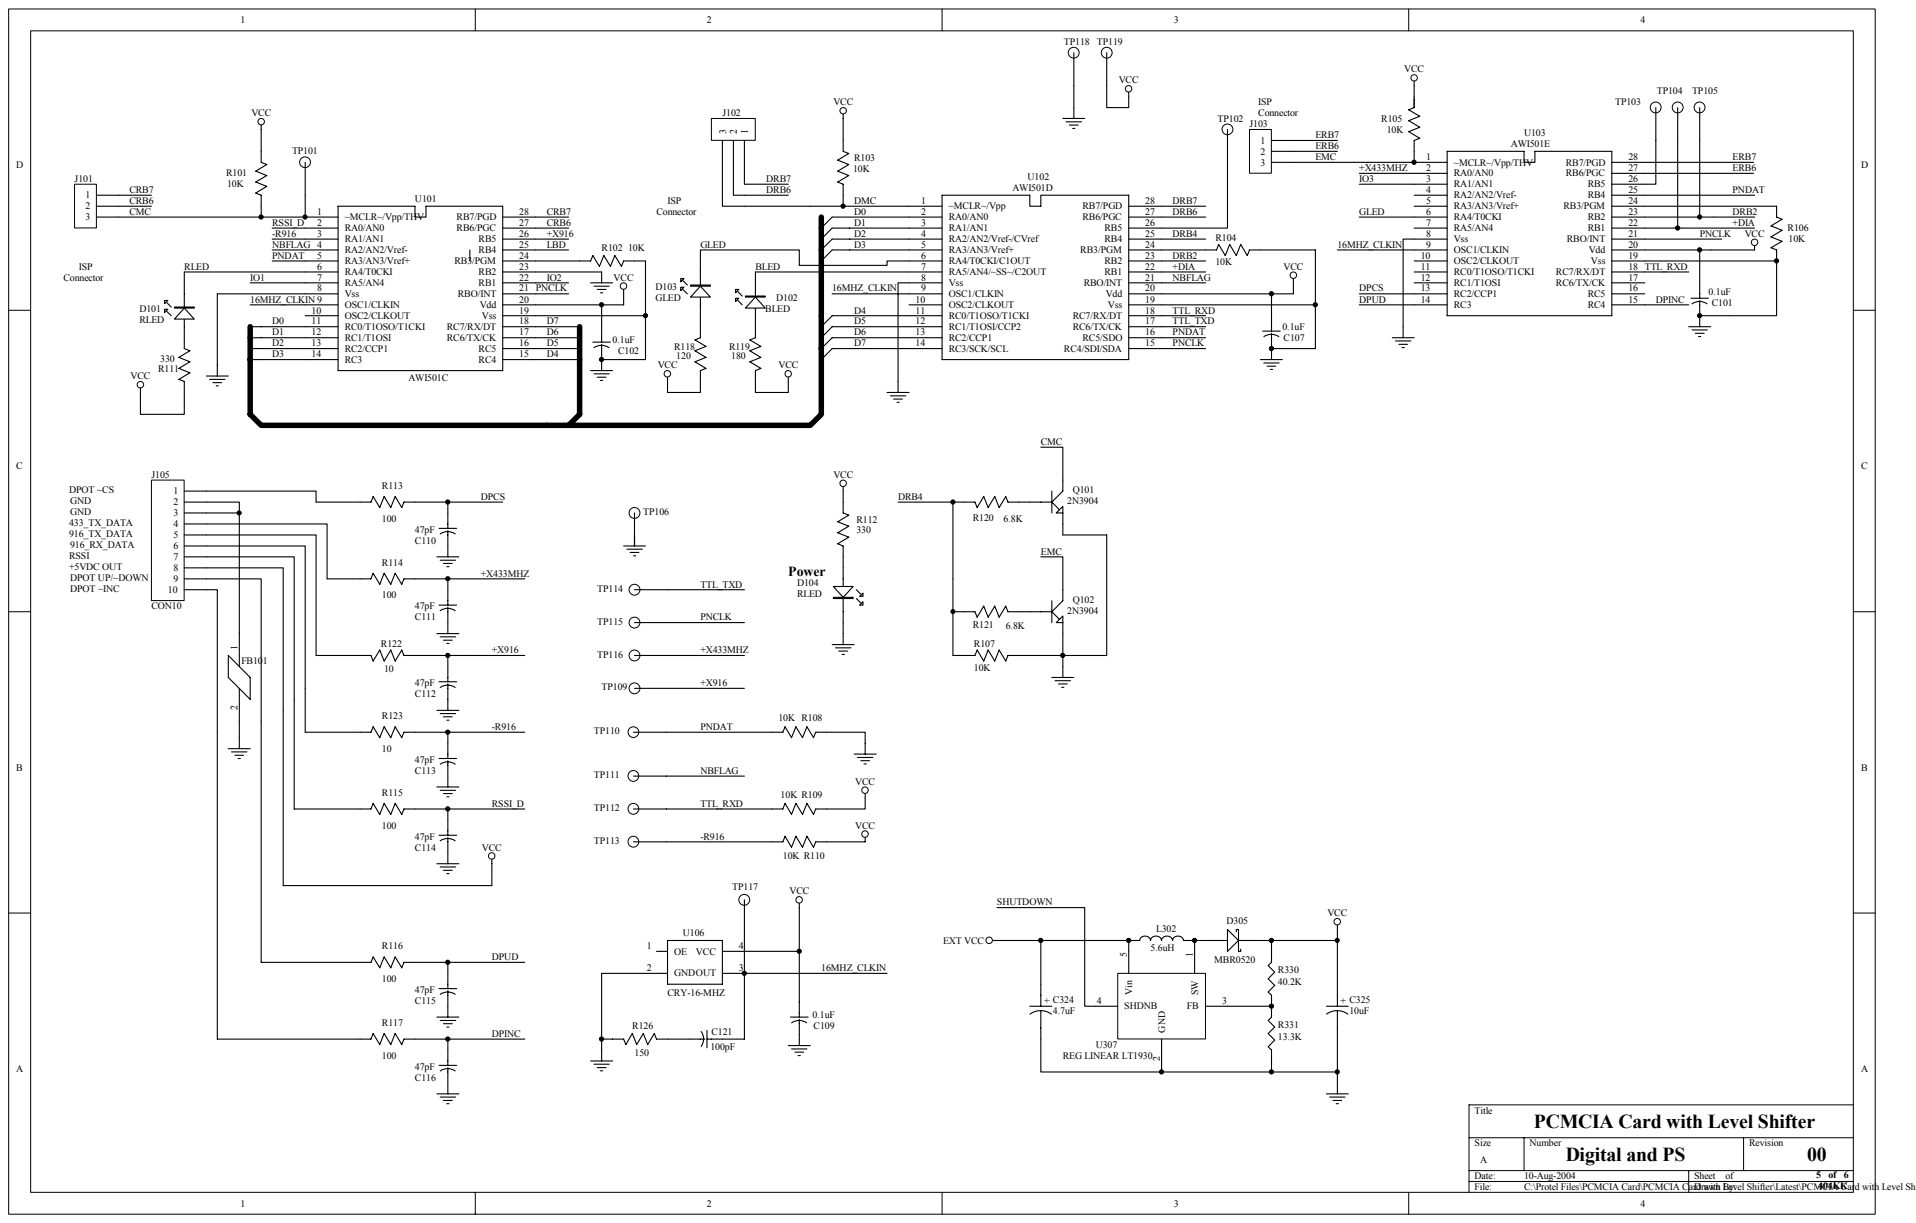
[picture p64: page 1]

Title
PCMCIA Card with Level Shifter

Size A | Number Digital and PS | Revision 00

Date: 10-Aug-2004 | Sheet of 5 of 6
