tourajghaffari/tigerfid/protel-files/small-handheld/Composite Drawing.pdf

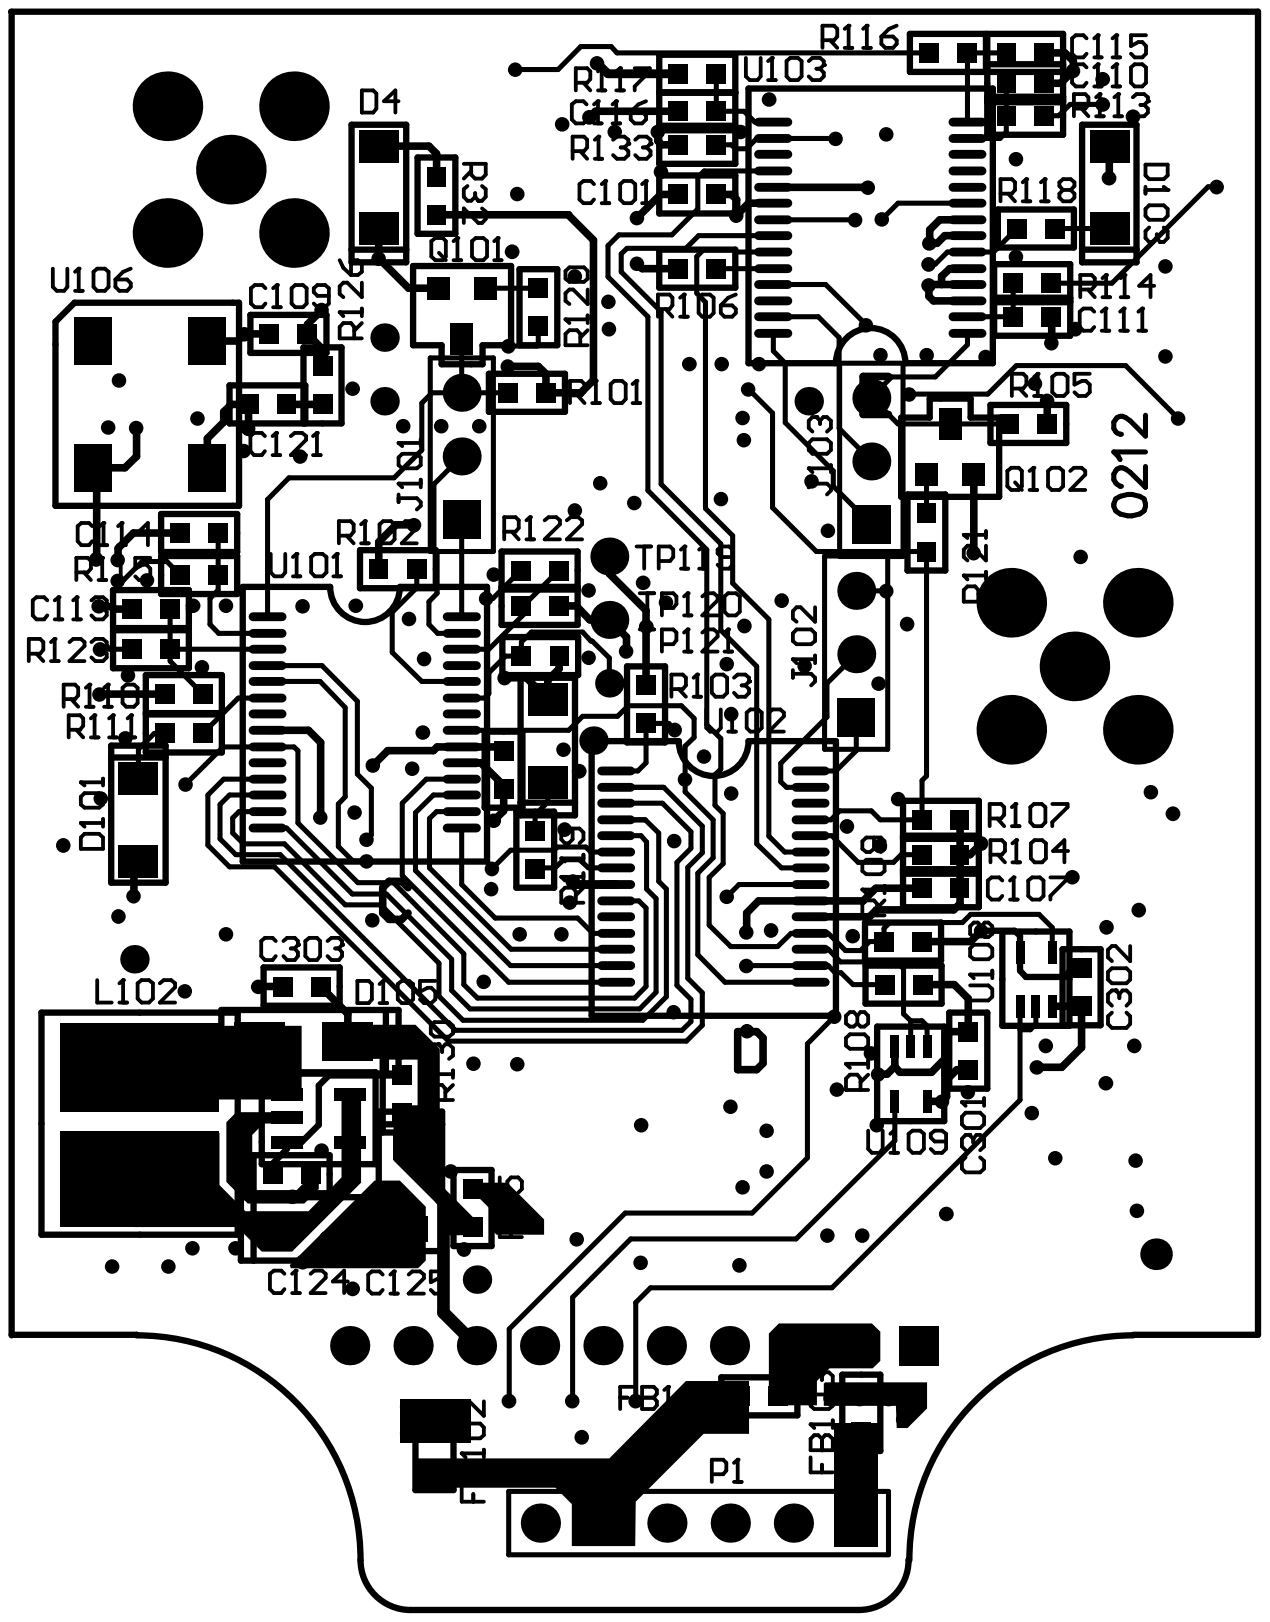
[picture p66: page 1]

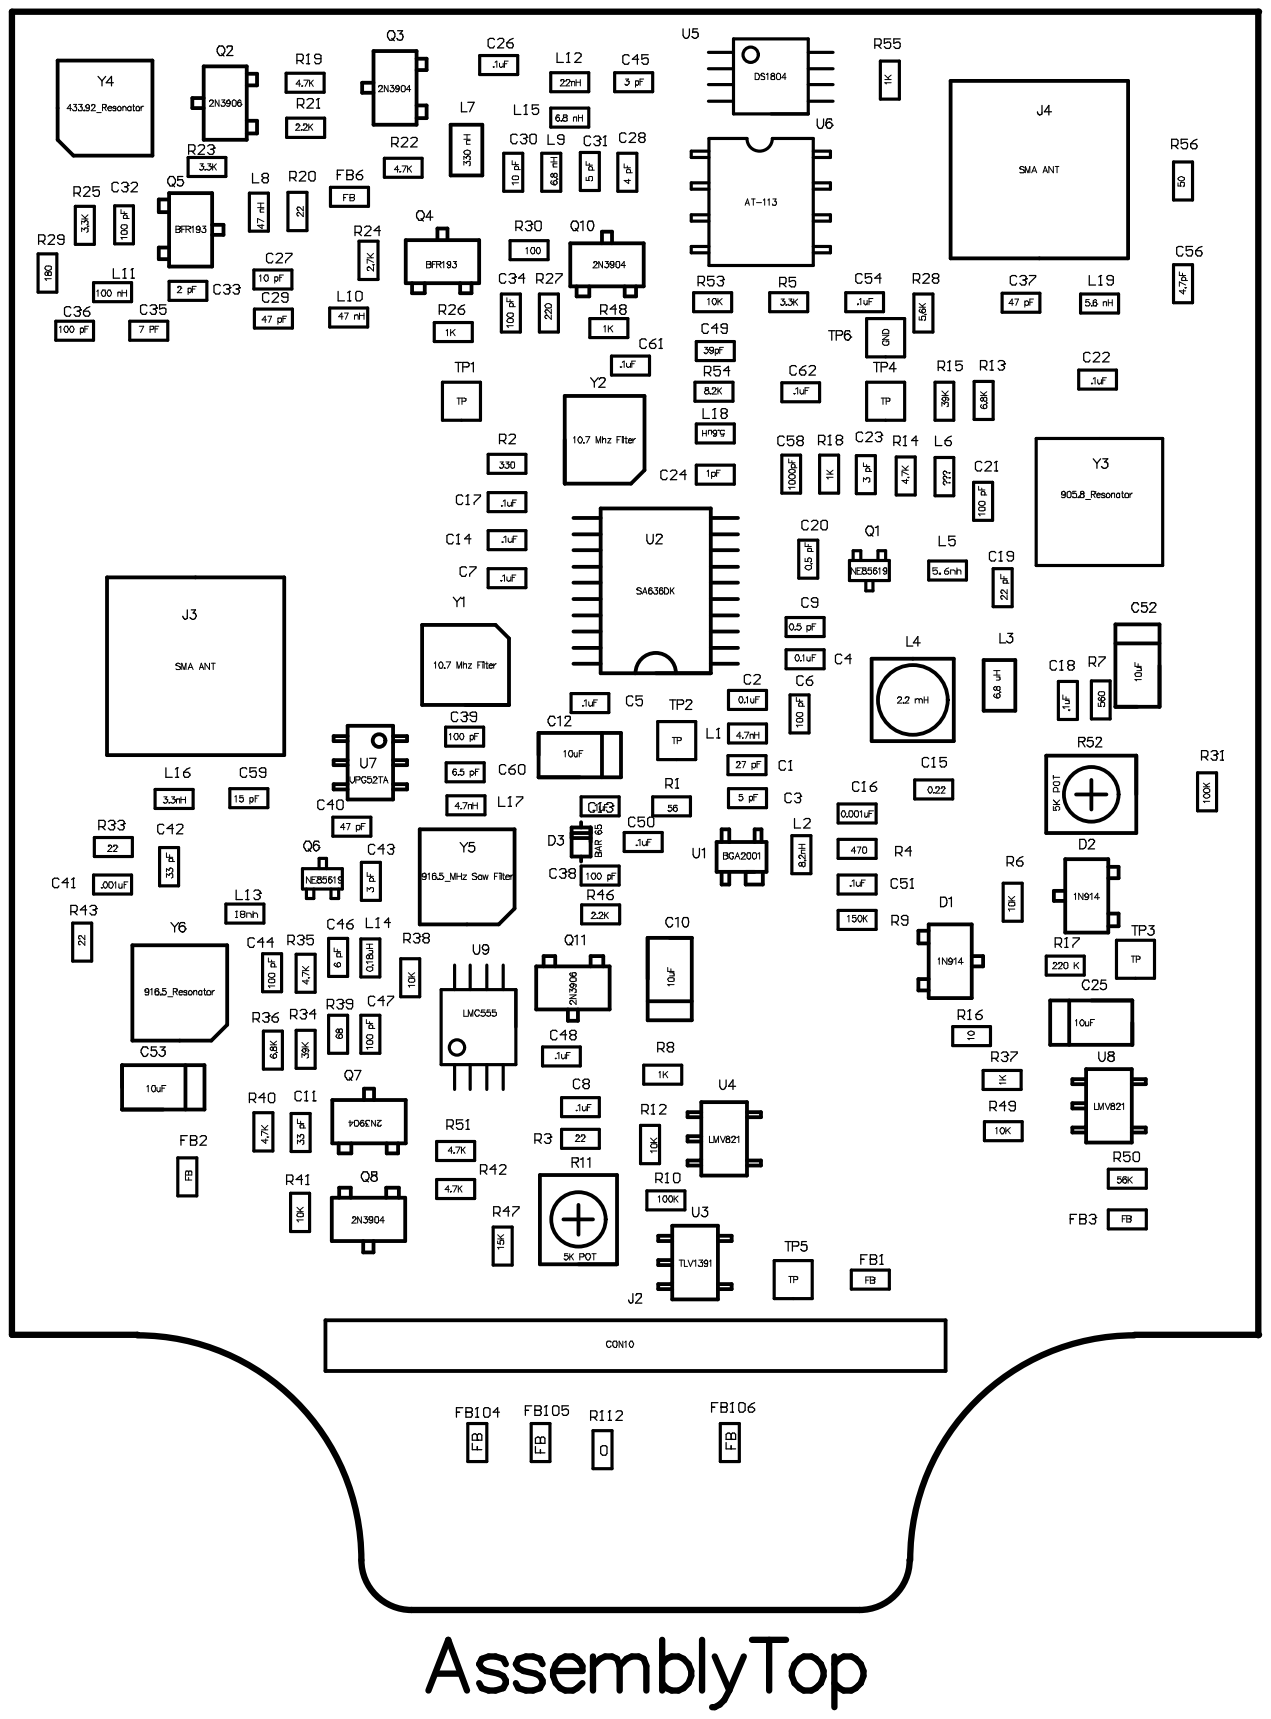
[picture p67: page 2]

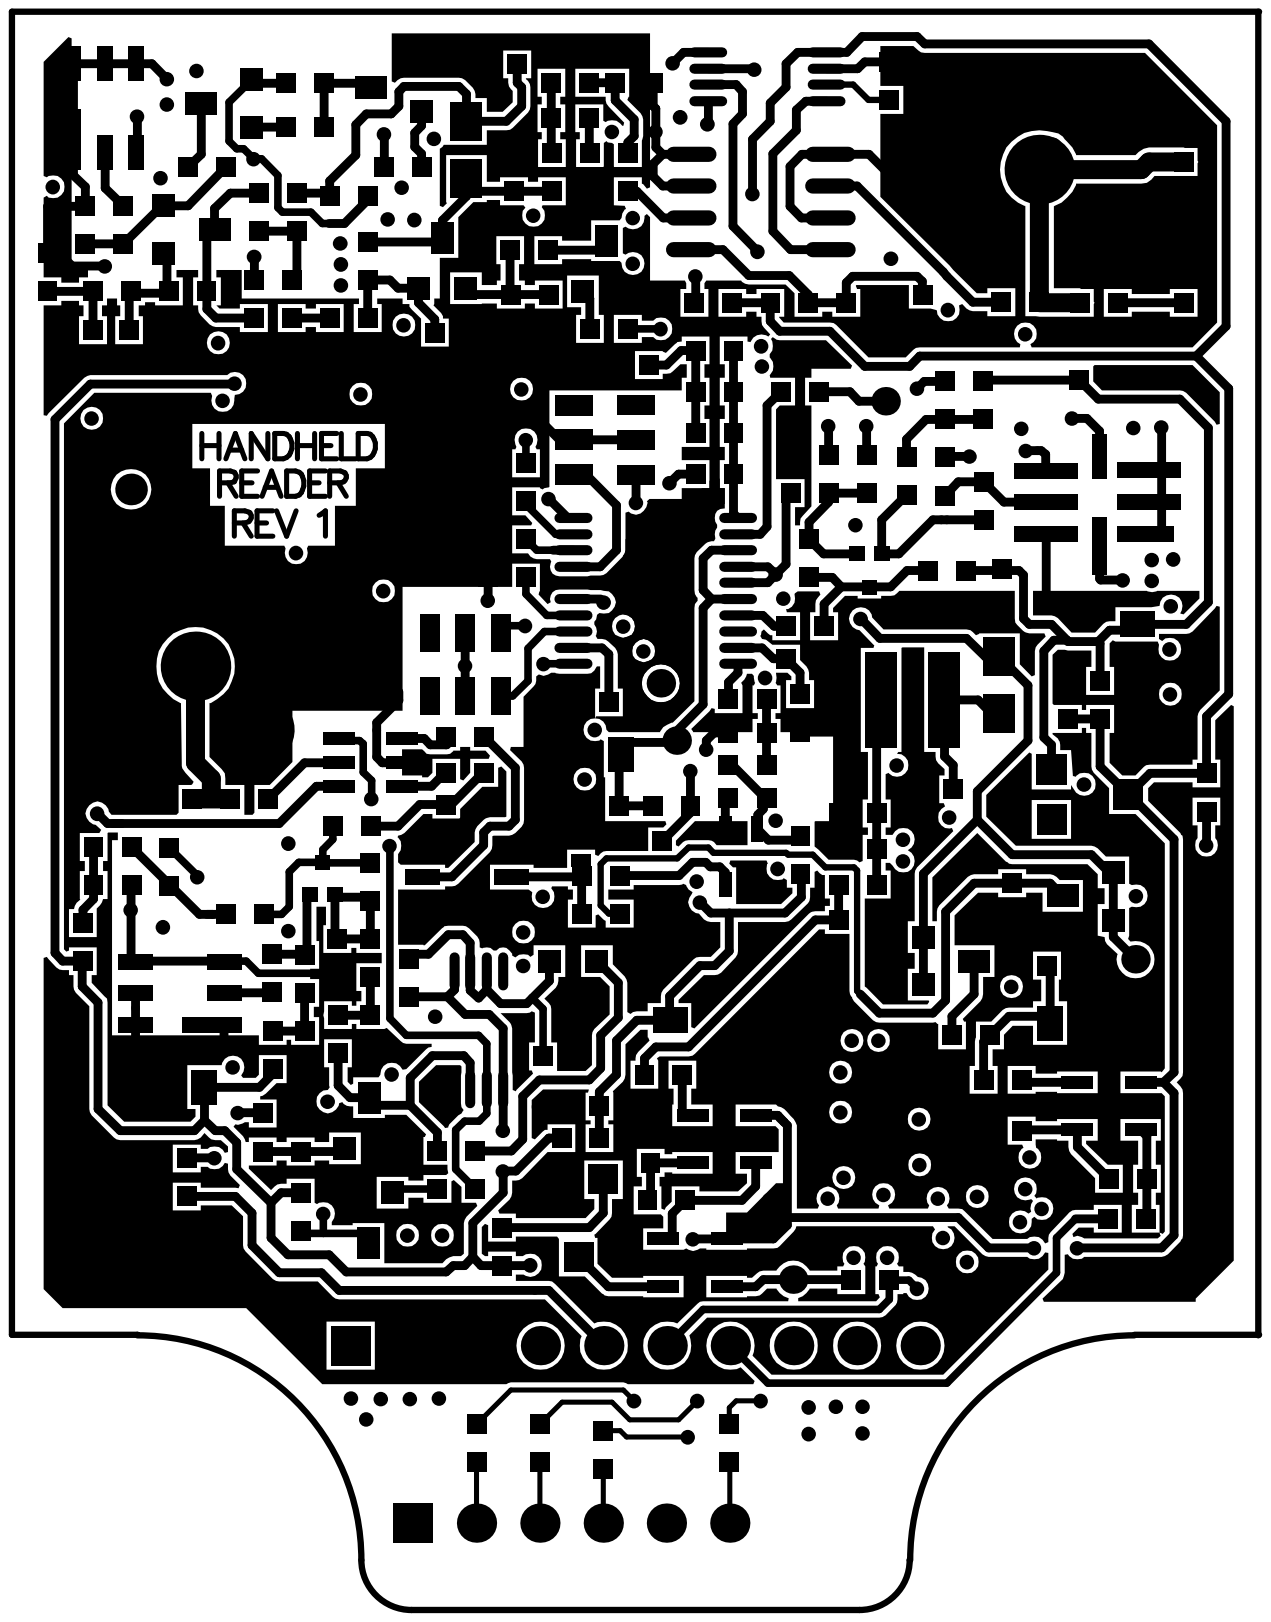
[picture p68: page 3]

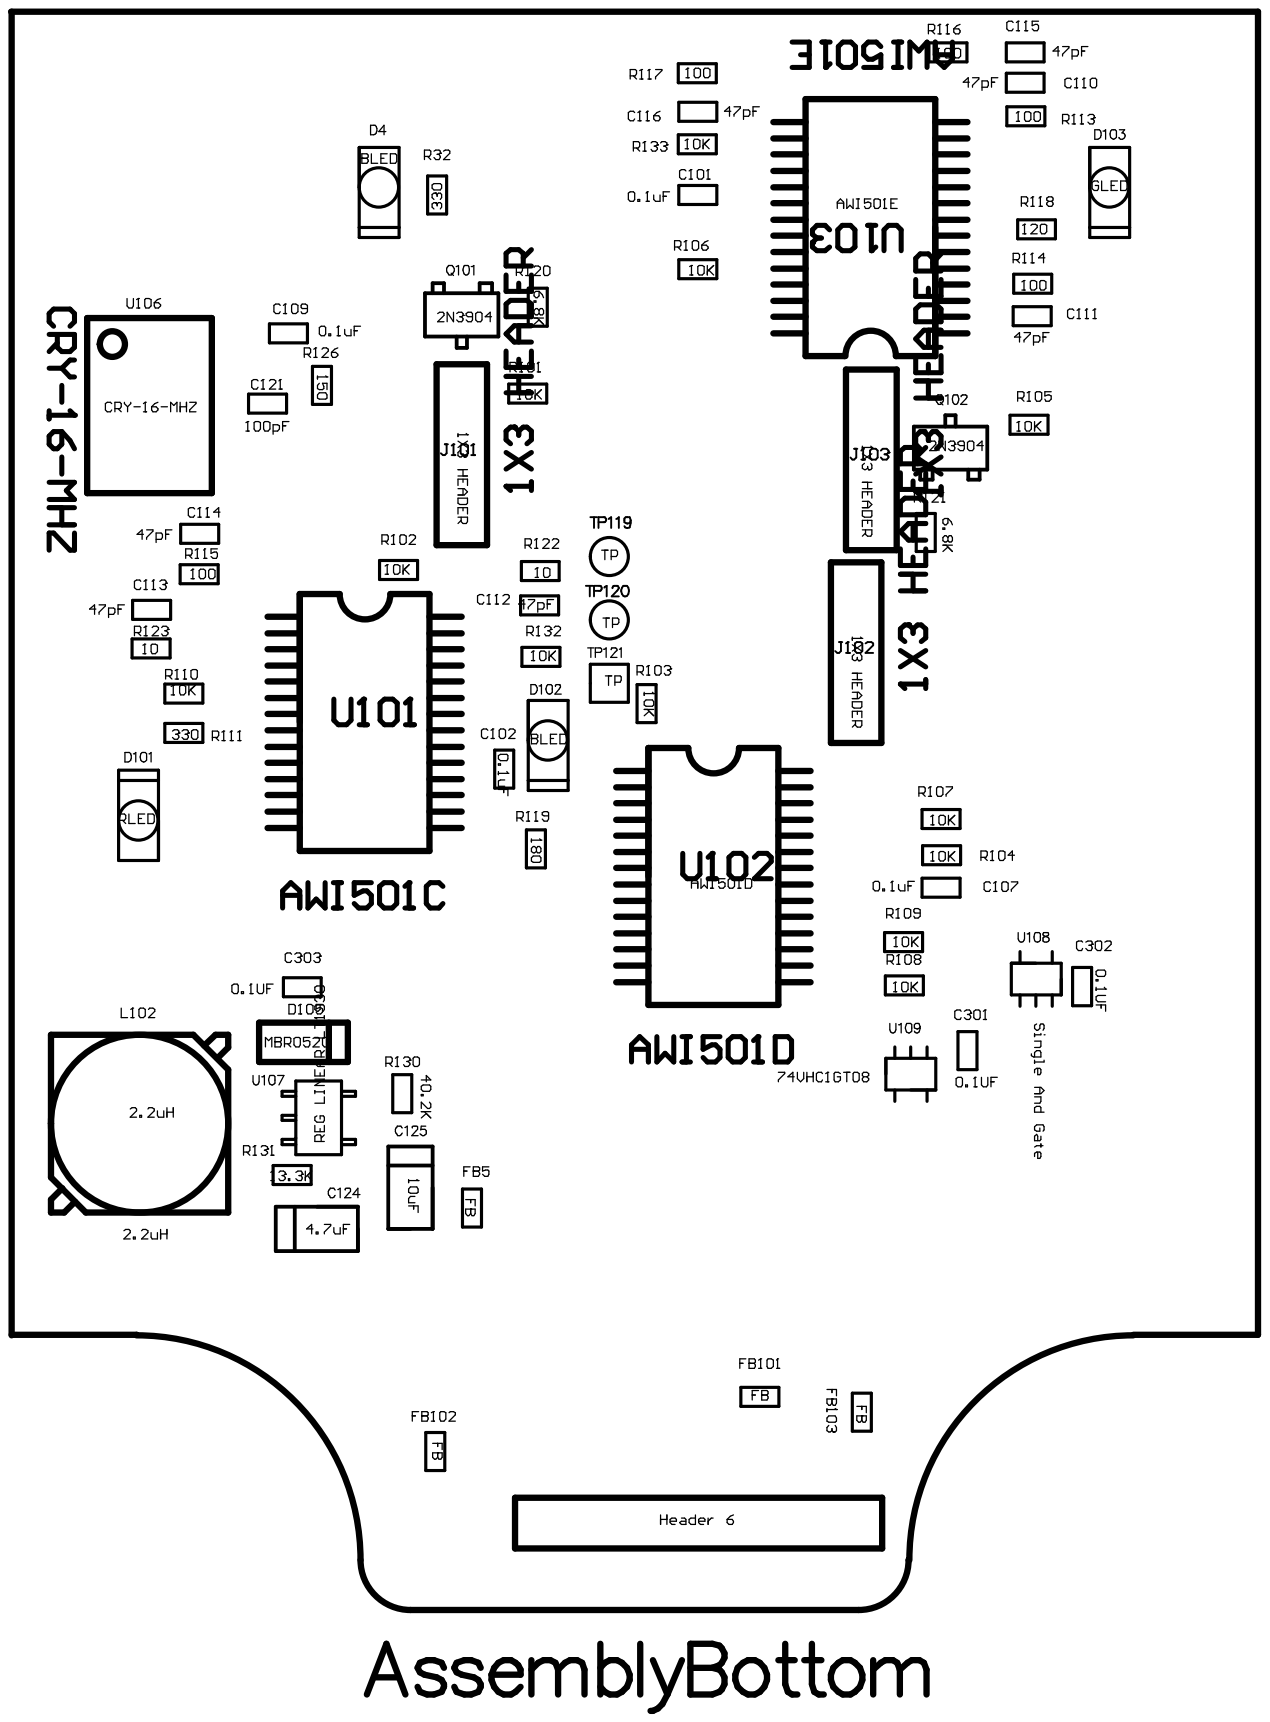
[picture p69: page 4]
