tourajghaffari/tigerfid/protel-files/wristband/rev2/Flex 1_1 Wristband wo Ant. Rev2.pdf

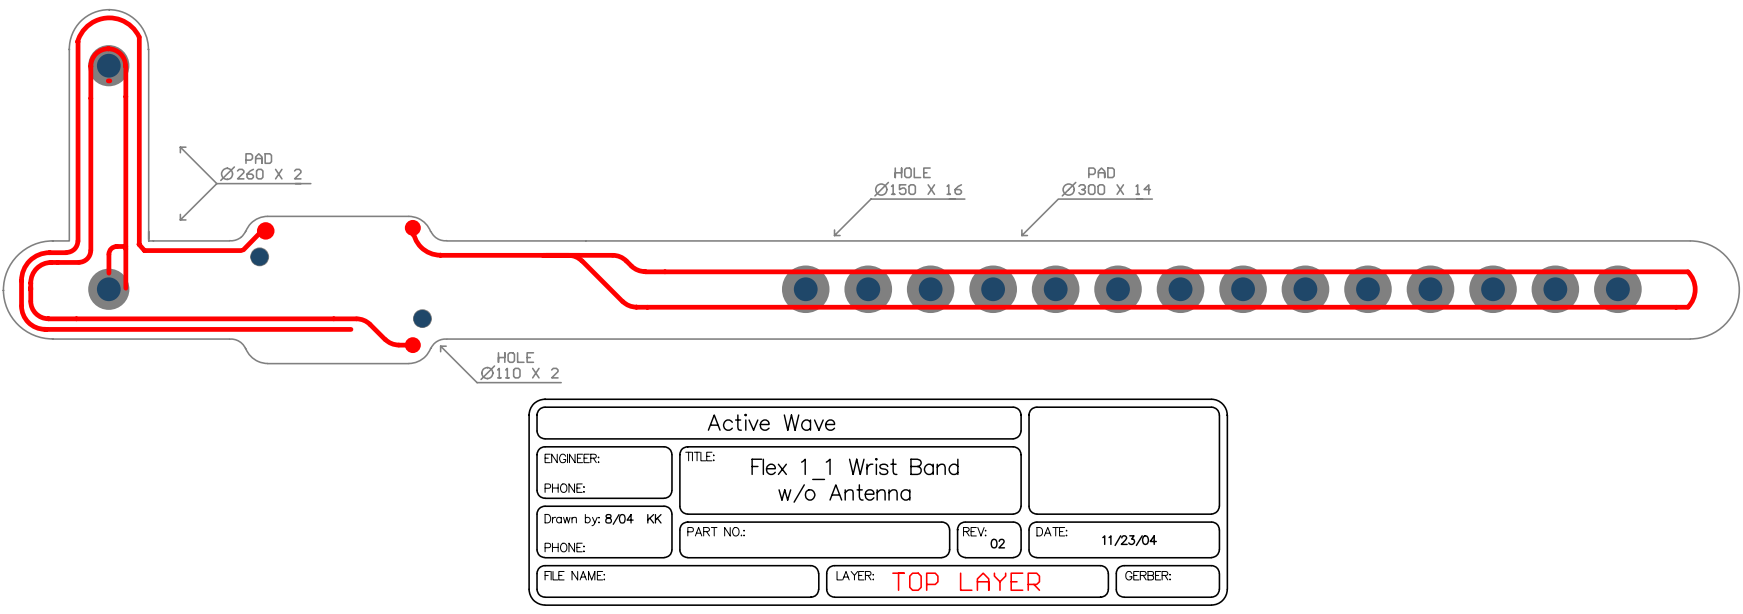
[picture p70: page 1]
