tourajghaffari/tigerfid/protel-files/field-generators/smart-fgen/rev7-new-case/Smart FG Antenna Hole Dimensions.pdf

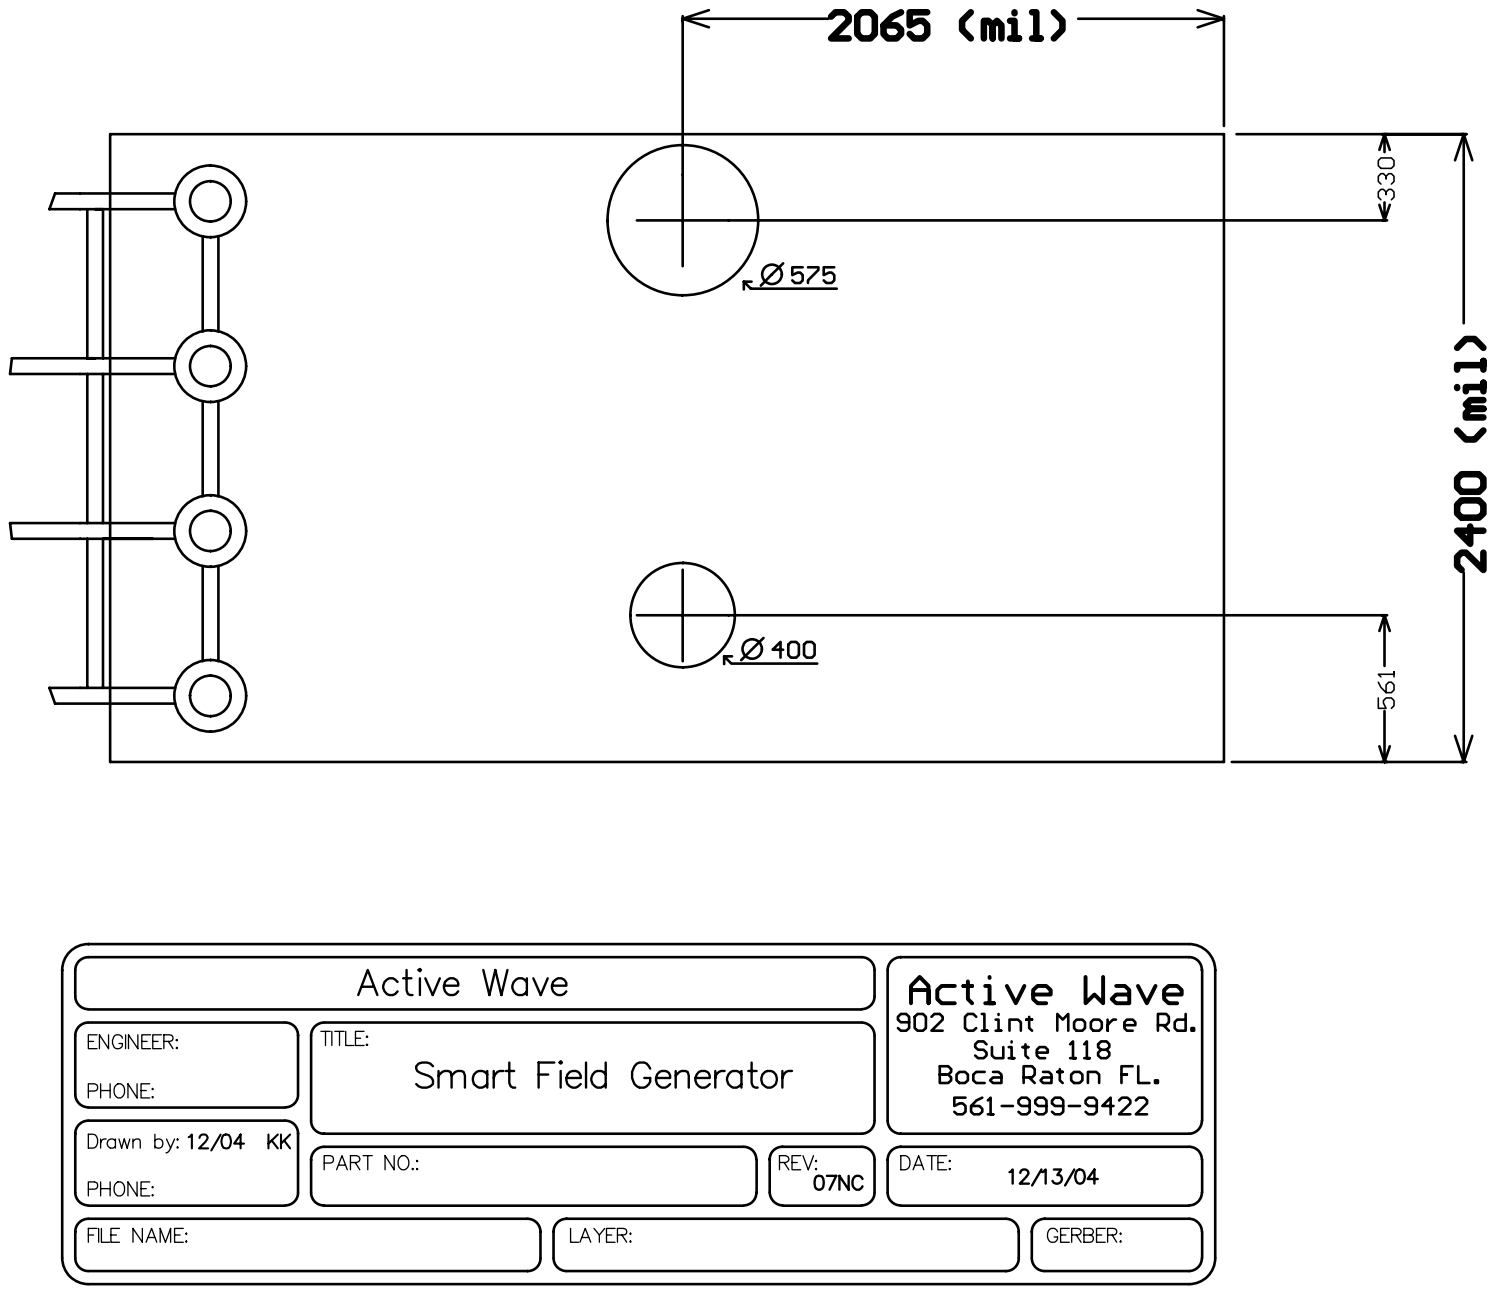
[picture p71: page 1]
