tourajghaffari/tigerfid/protel-files/tags/credit-card-tag-tag-with-battery-holder/org-rev20/mmbt3904.pdf

# APPROVED

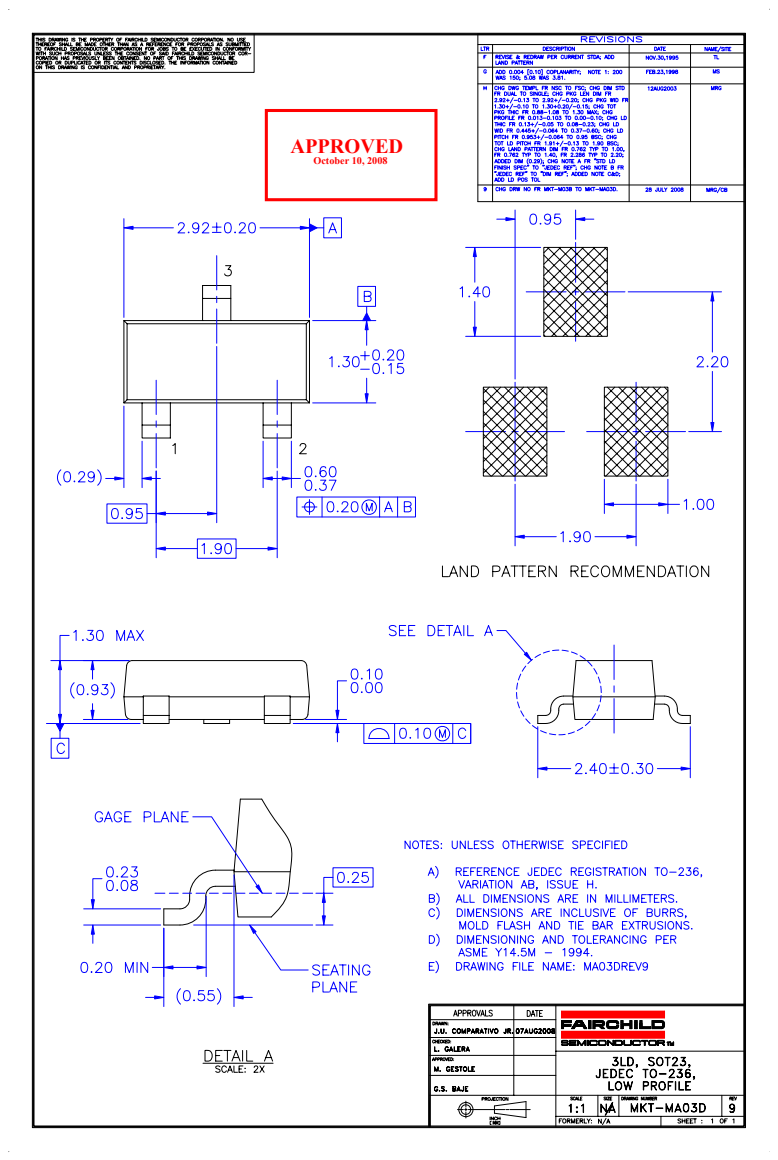
[picture p72: page 1]
October 10, 2008
