tourajghaffari/tigerfid/protel-files/tags/small-tag/dxf/ENGINEER - TENSION-SPRING.pdf

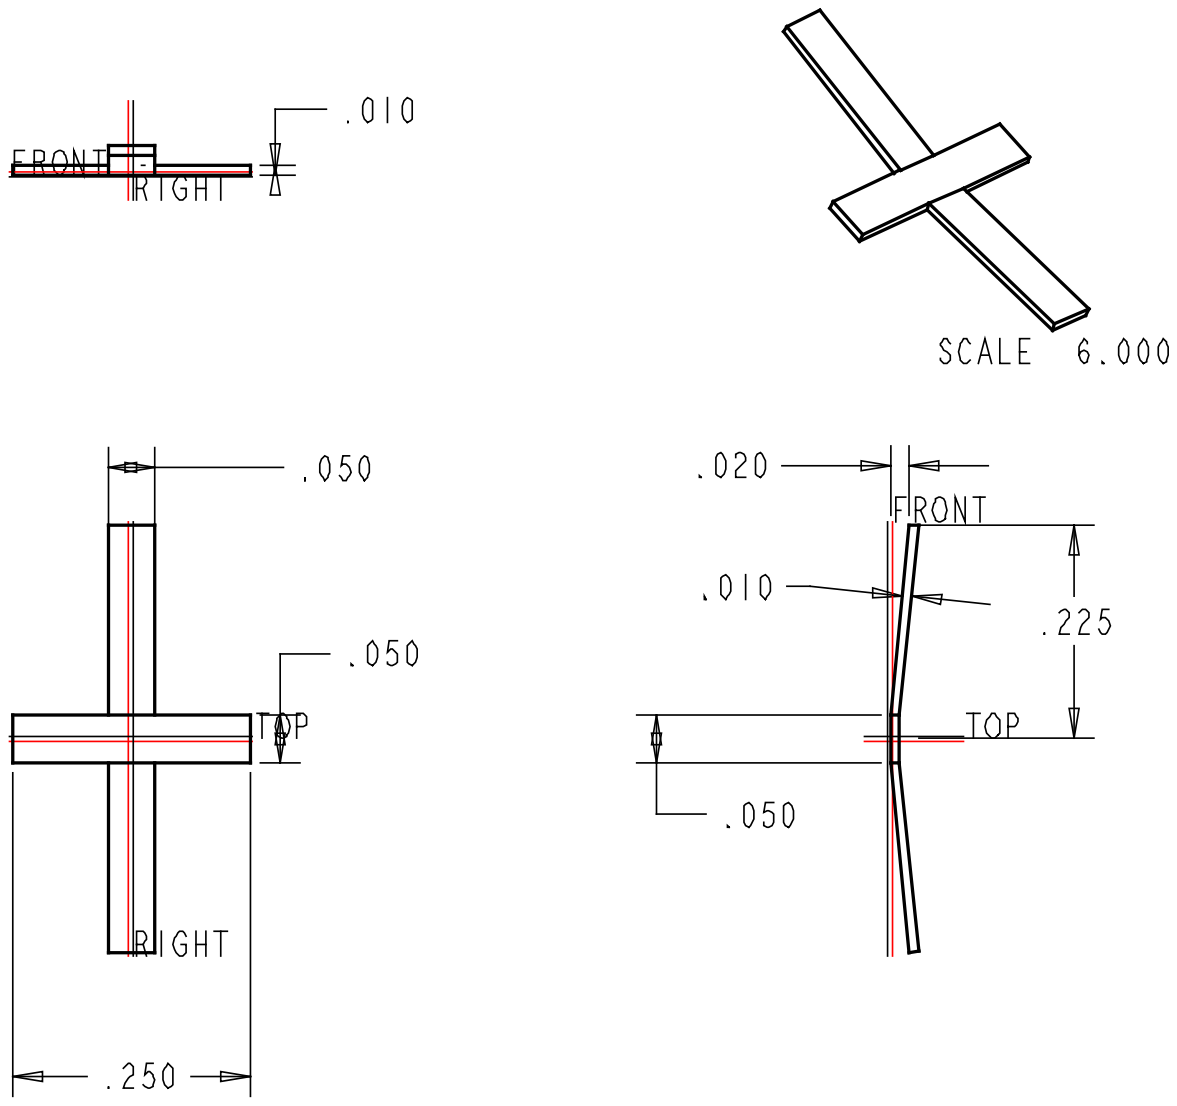
[picture p73: page 1]
