tourajghaffari/tigerfid/protel-files/transceiver/trx-rev19/reviews/TRX-101R17_PCBReview1.pdf

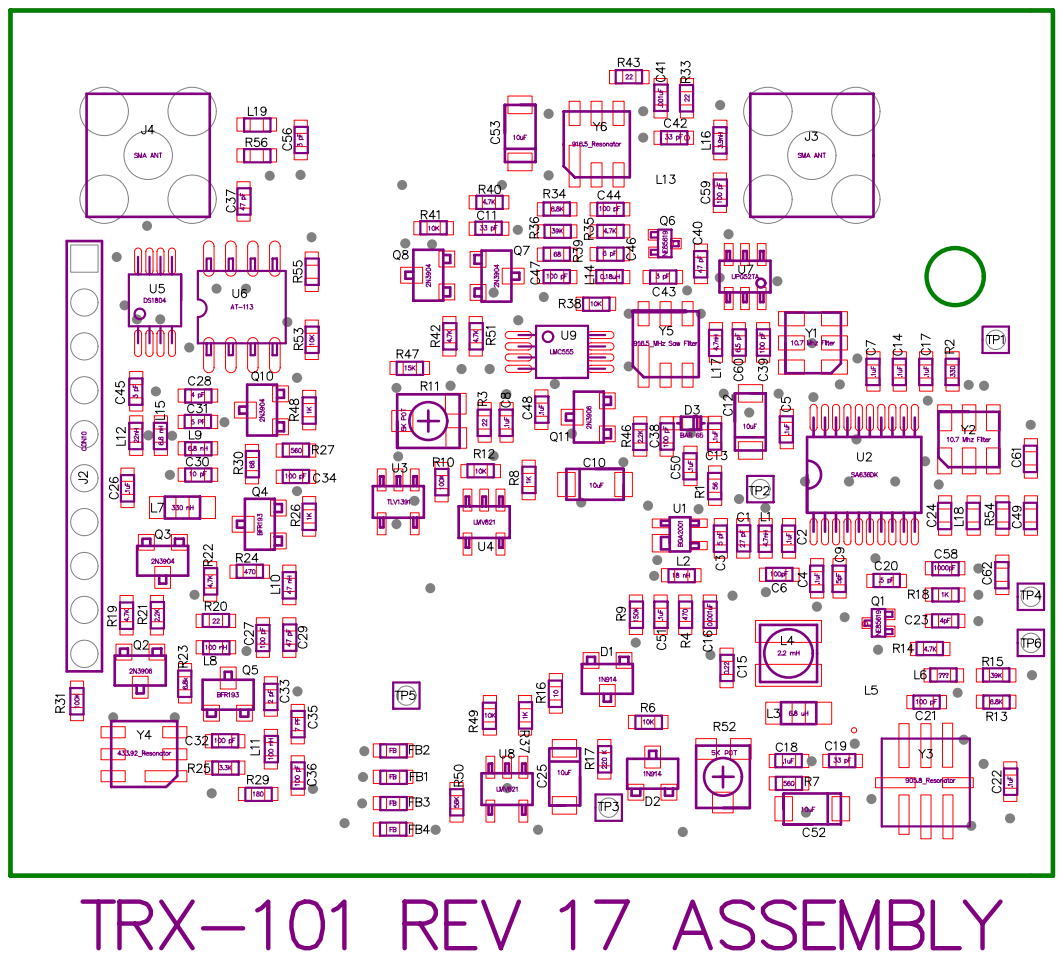
[picture p74: page 1]
