tourajghaffari/tigerfid/protel-files/wristband/flex1/latest/Flex1_1 Wristband.pdf

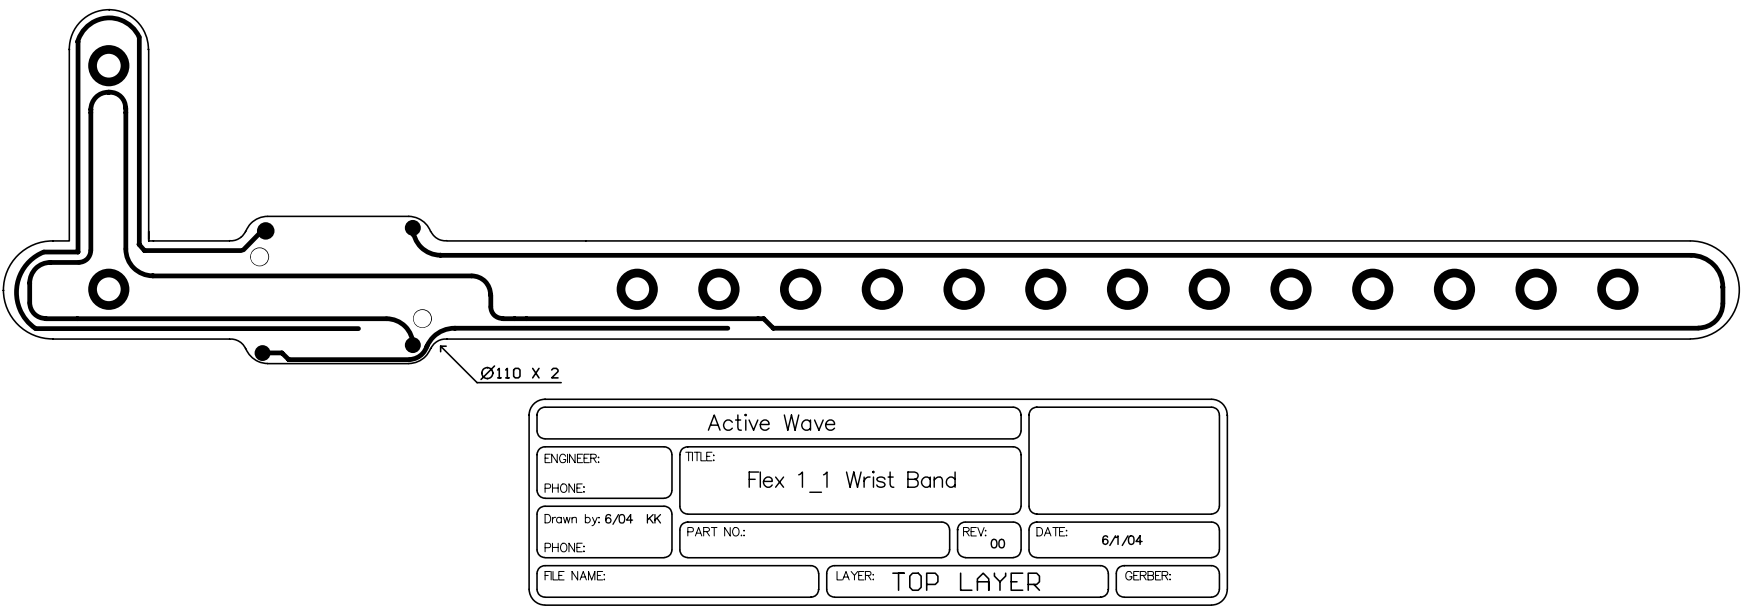
[picture p75: page 1]
