tourajghaffari/tigerfid/protel-files/wristband/flex1/latest/Flex2 Wristband.pdf

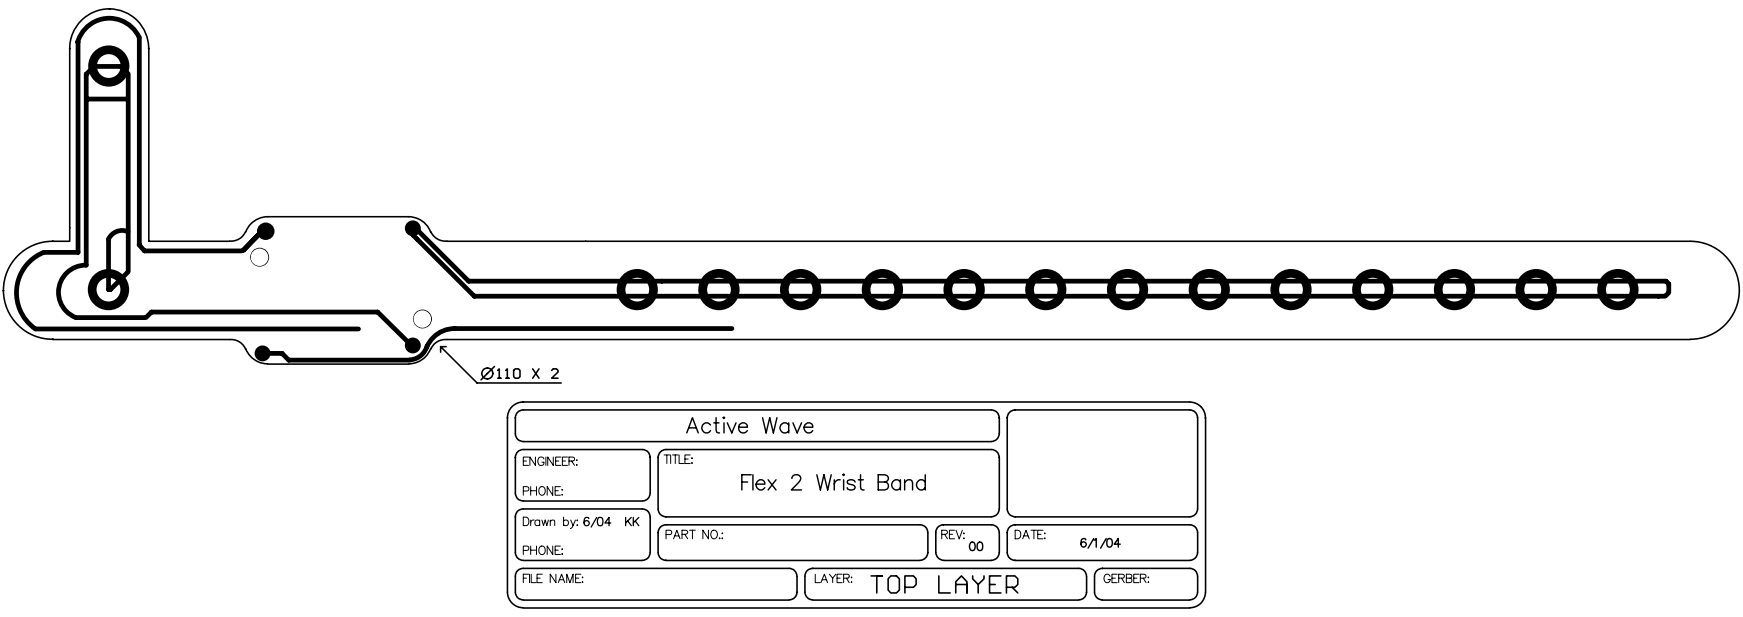
[picture p76: page 1]
