tourajghaffari/tigerfid/protel-files/reader/pcmcia-reader/pcmcia-card-with-level-shifter/pdfs/Amp SMA Connector 132220RP.pdf

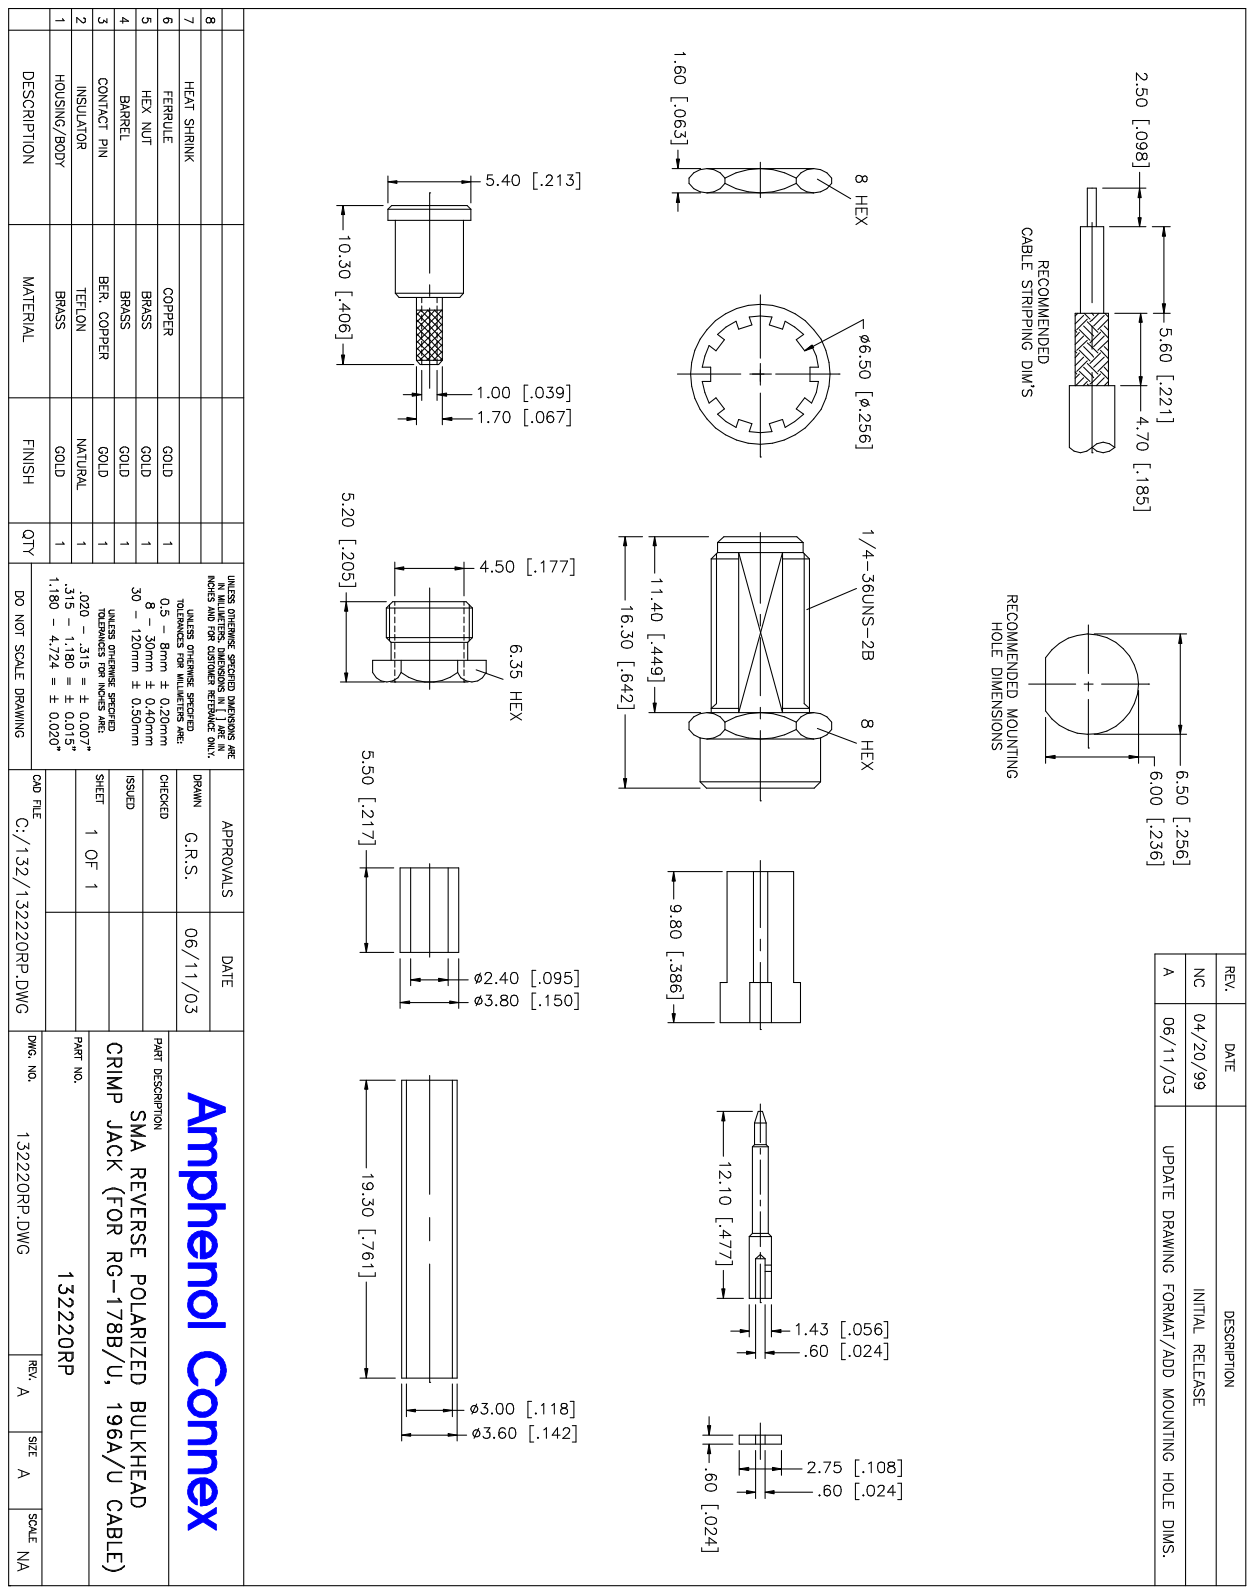
[picture p77: page 1]
