tourajghaffari/tigerfid/protel-files/reader/small-handheld/digital/rev4/Proposed Connector Location.pdf

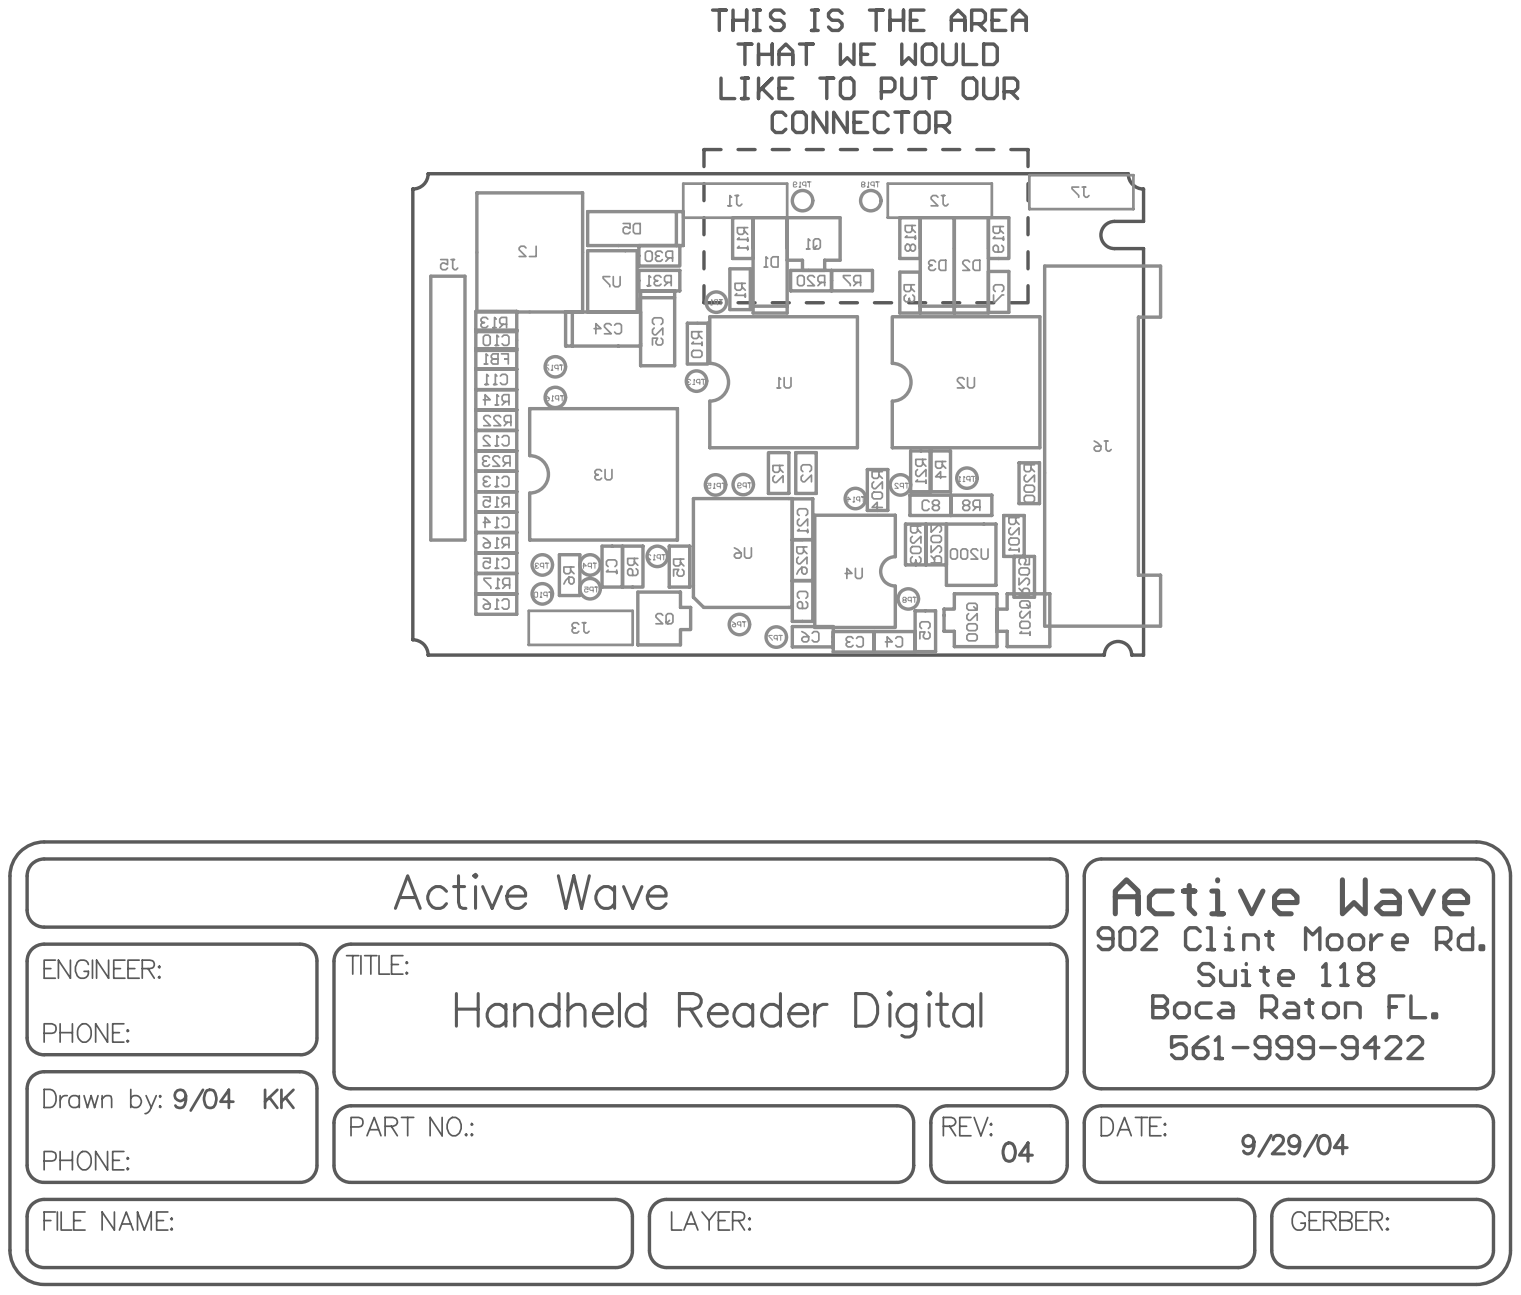
[picture p78: page 1]
