tourajghaffari/tigerfid/protel-files/tags/small-tag/103-rev21/103-rev21/Tag103-Rev21-Panel.pdf

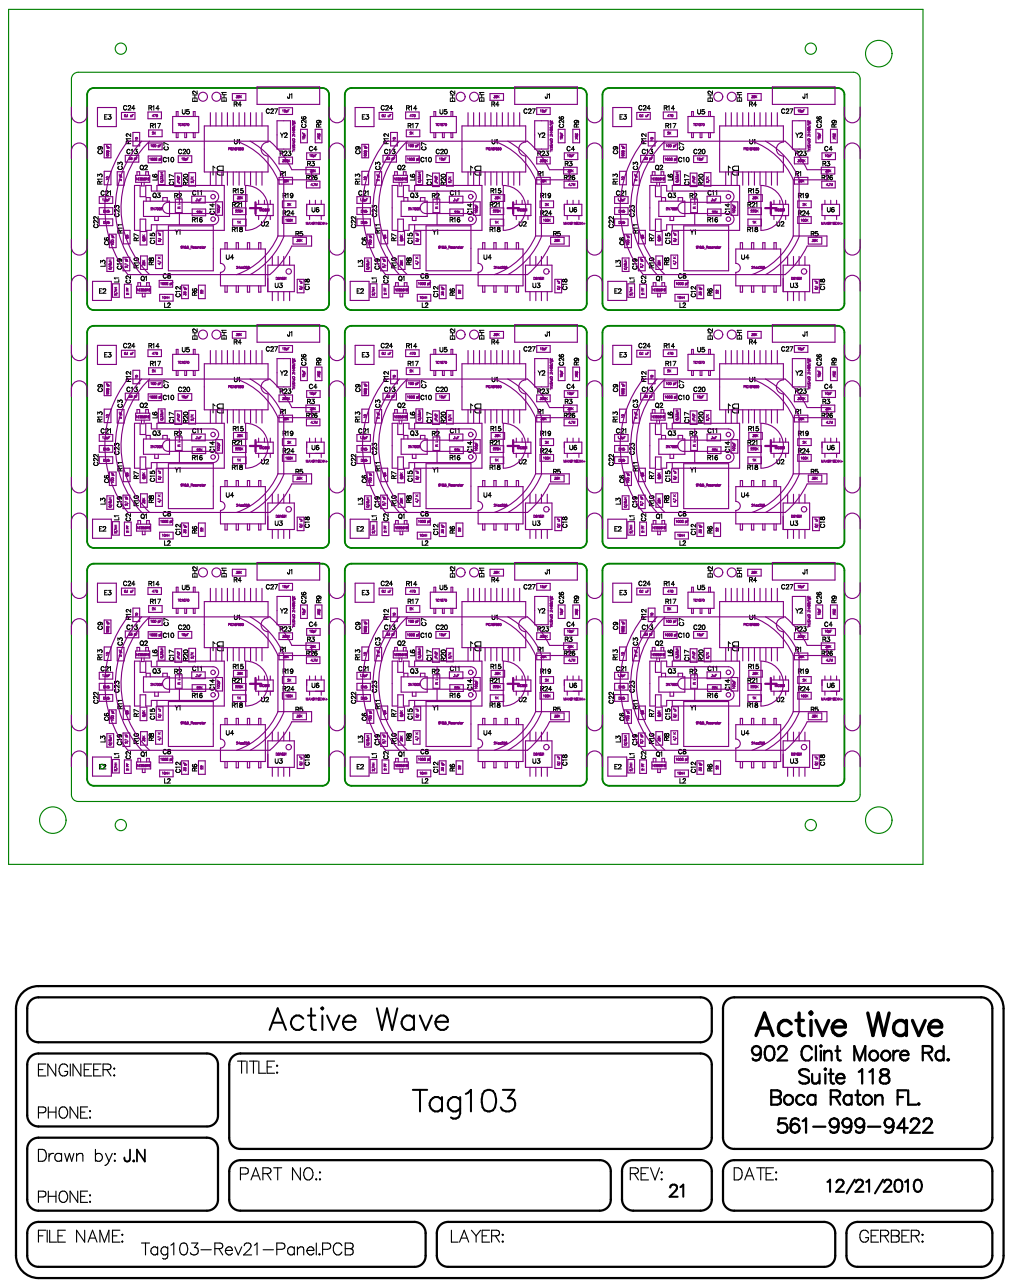
[picture p79: page 1]
