tourajghaffari/tigerfid/protel-files/reader/pcmcia-reader/pcmcia-card-with-level-shifter/latest/pdfs/Bottom Copper 1.pdf

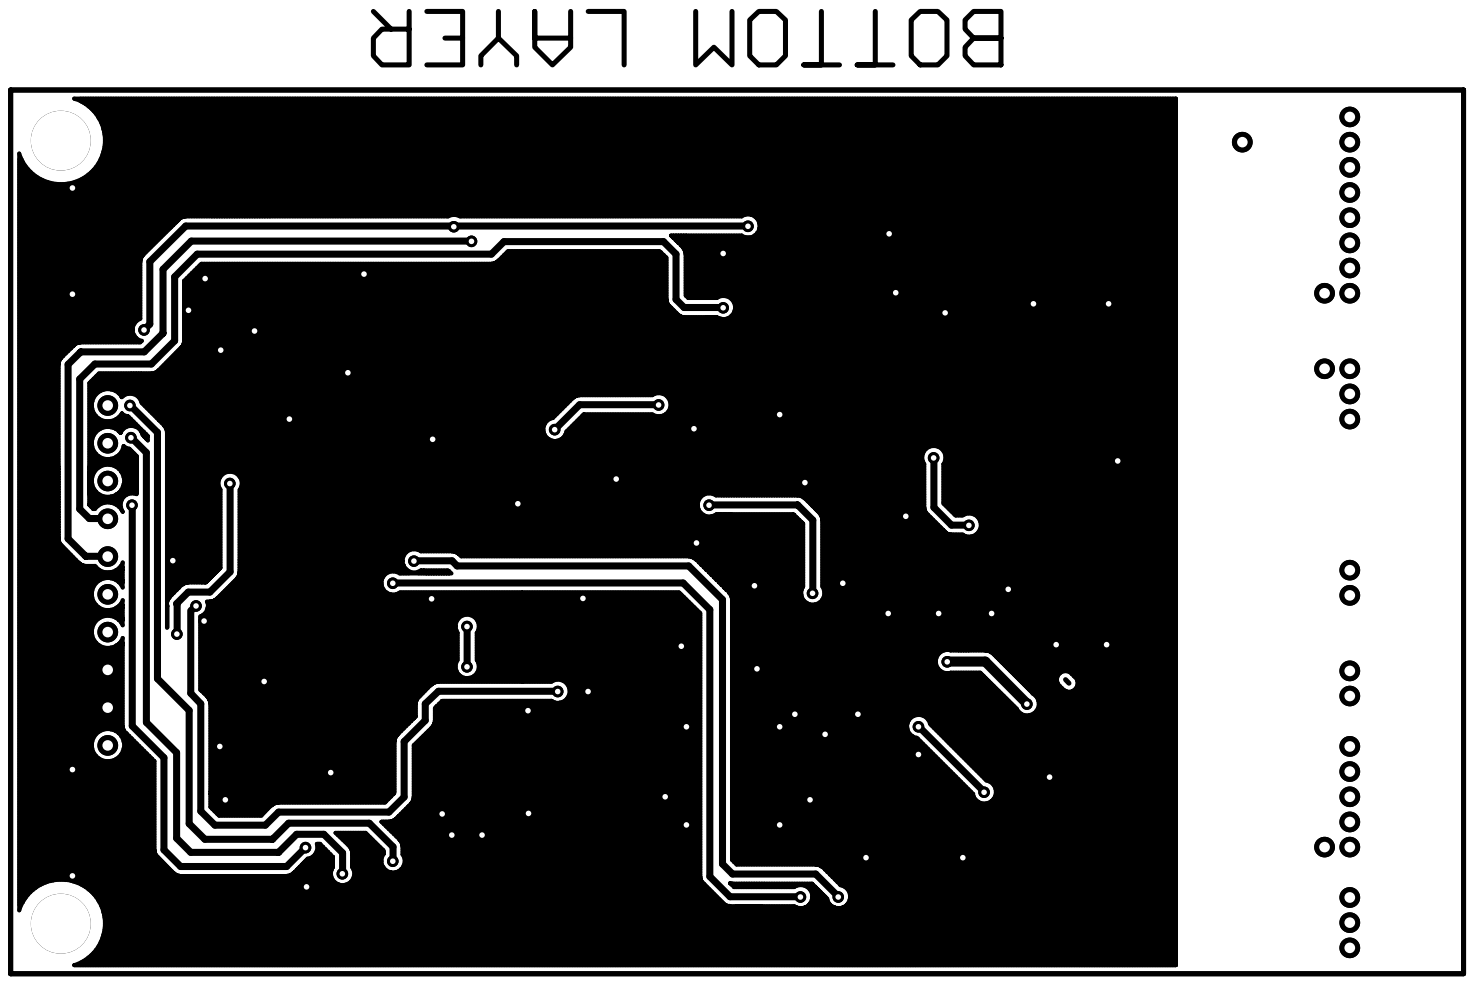
[picture p80: page 1]
