tourajghaffari/tigerfid/protel-files/reader/pcmcia-reader/pcmcia-card-with-level-shifter/latest/pdfs/Bottom Copper 2.pdf

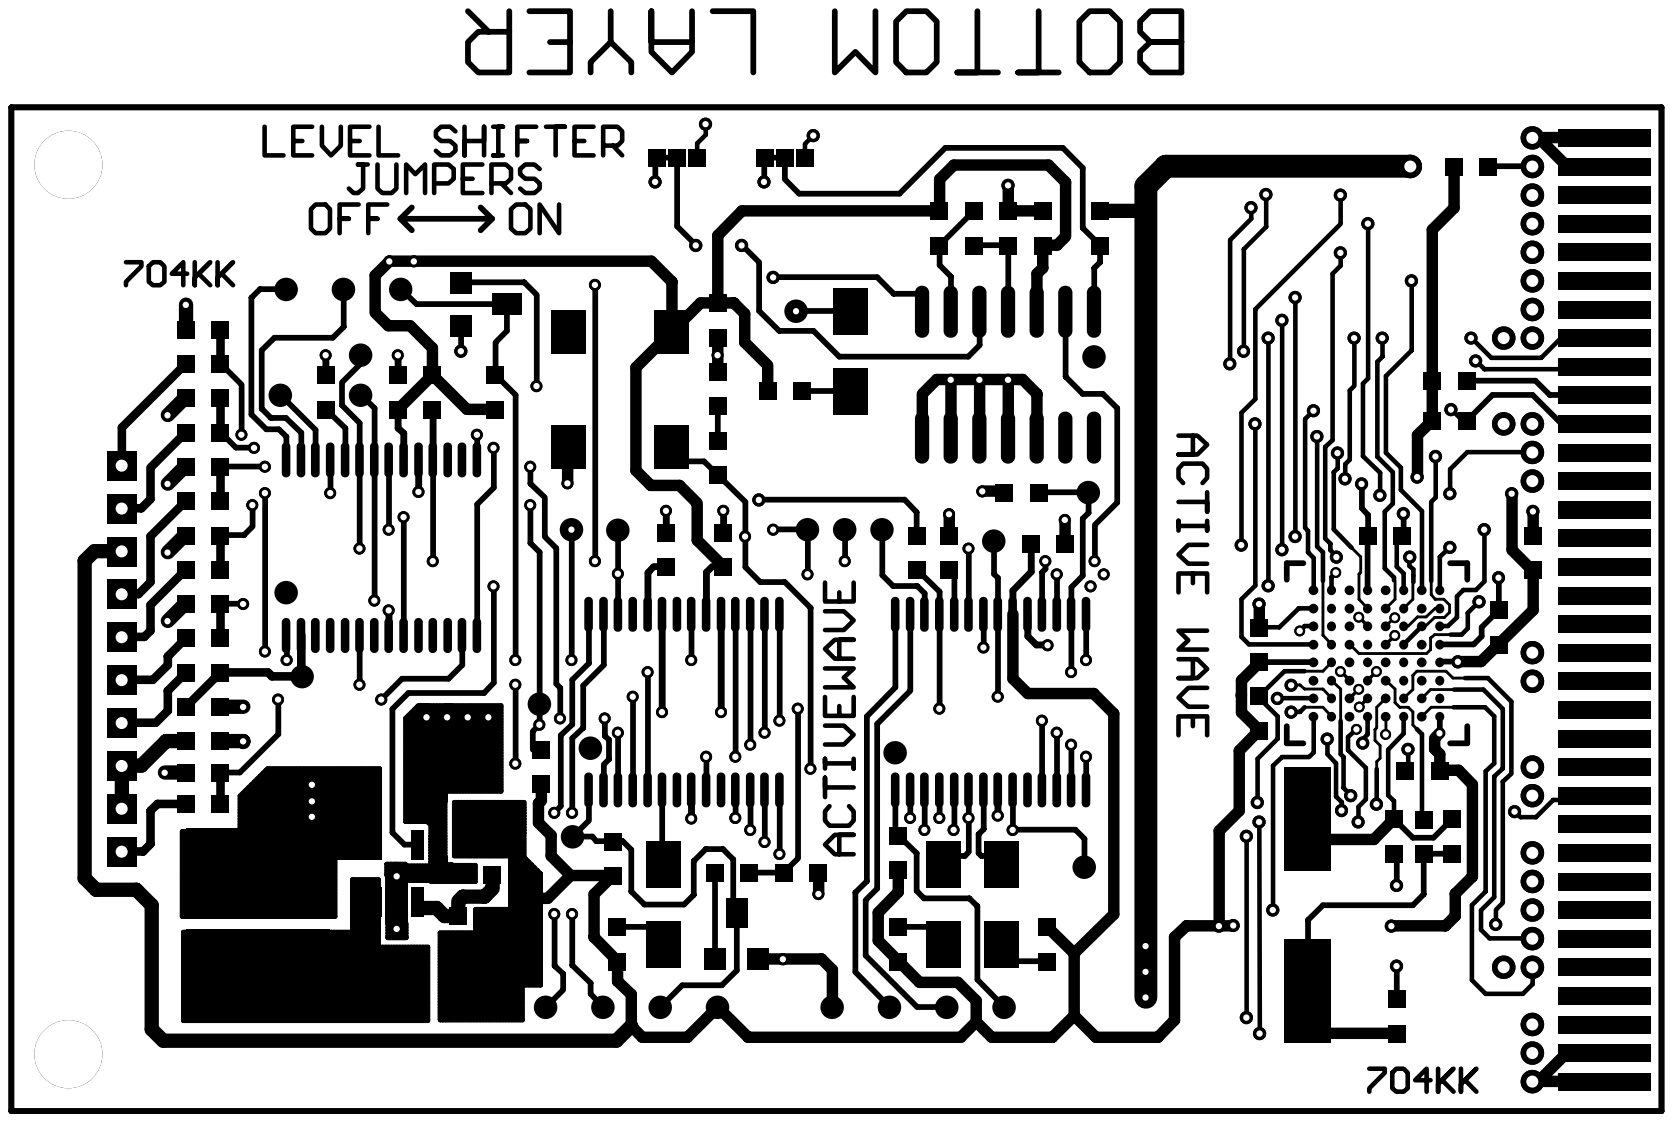
[picture p81: page 1]
