tourajghaffari/tigerfid/protel-files/reader/pcmcia-reader/pcmcia-card-with-level-shifter/latest/pdfs/Bottom Silk Screen 2.pdf

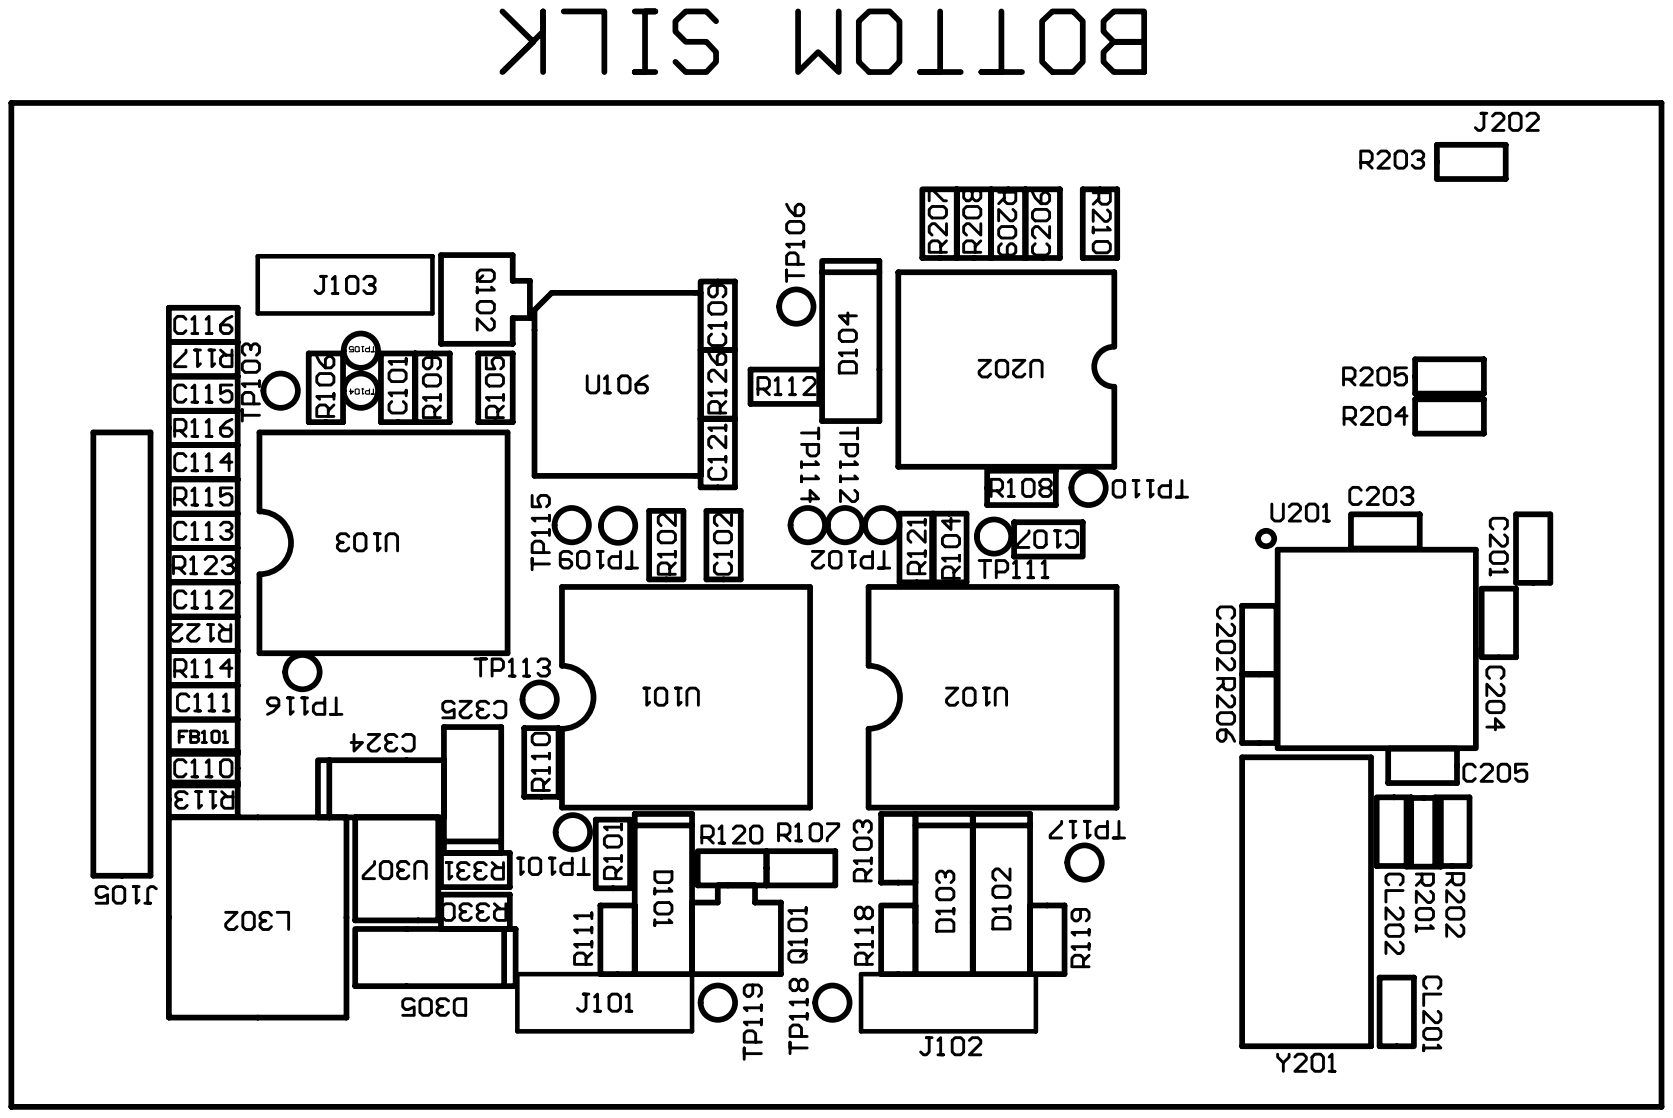
[picture p82: page 1]
