tourajghaffari/tigerfid/protel-files/reader/pcmcia-reader/pcmcia-card-with-level-shifter/latest/pdfs/Top Silk Screen 1.pdf

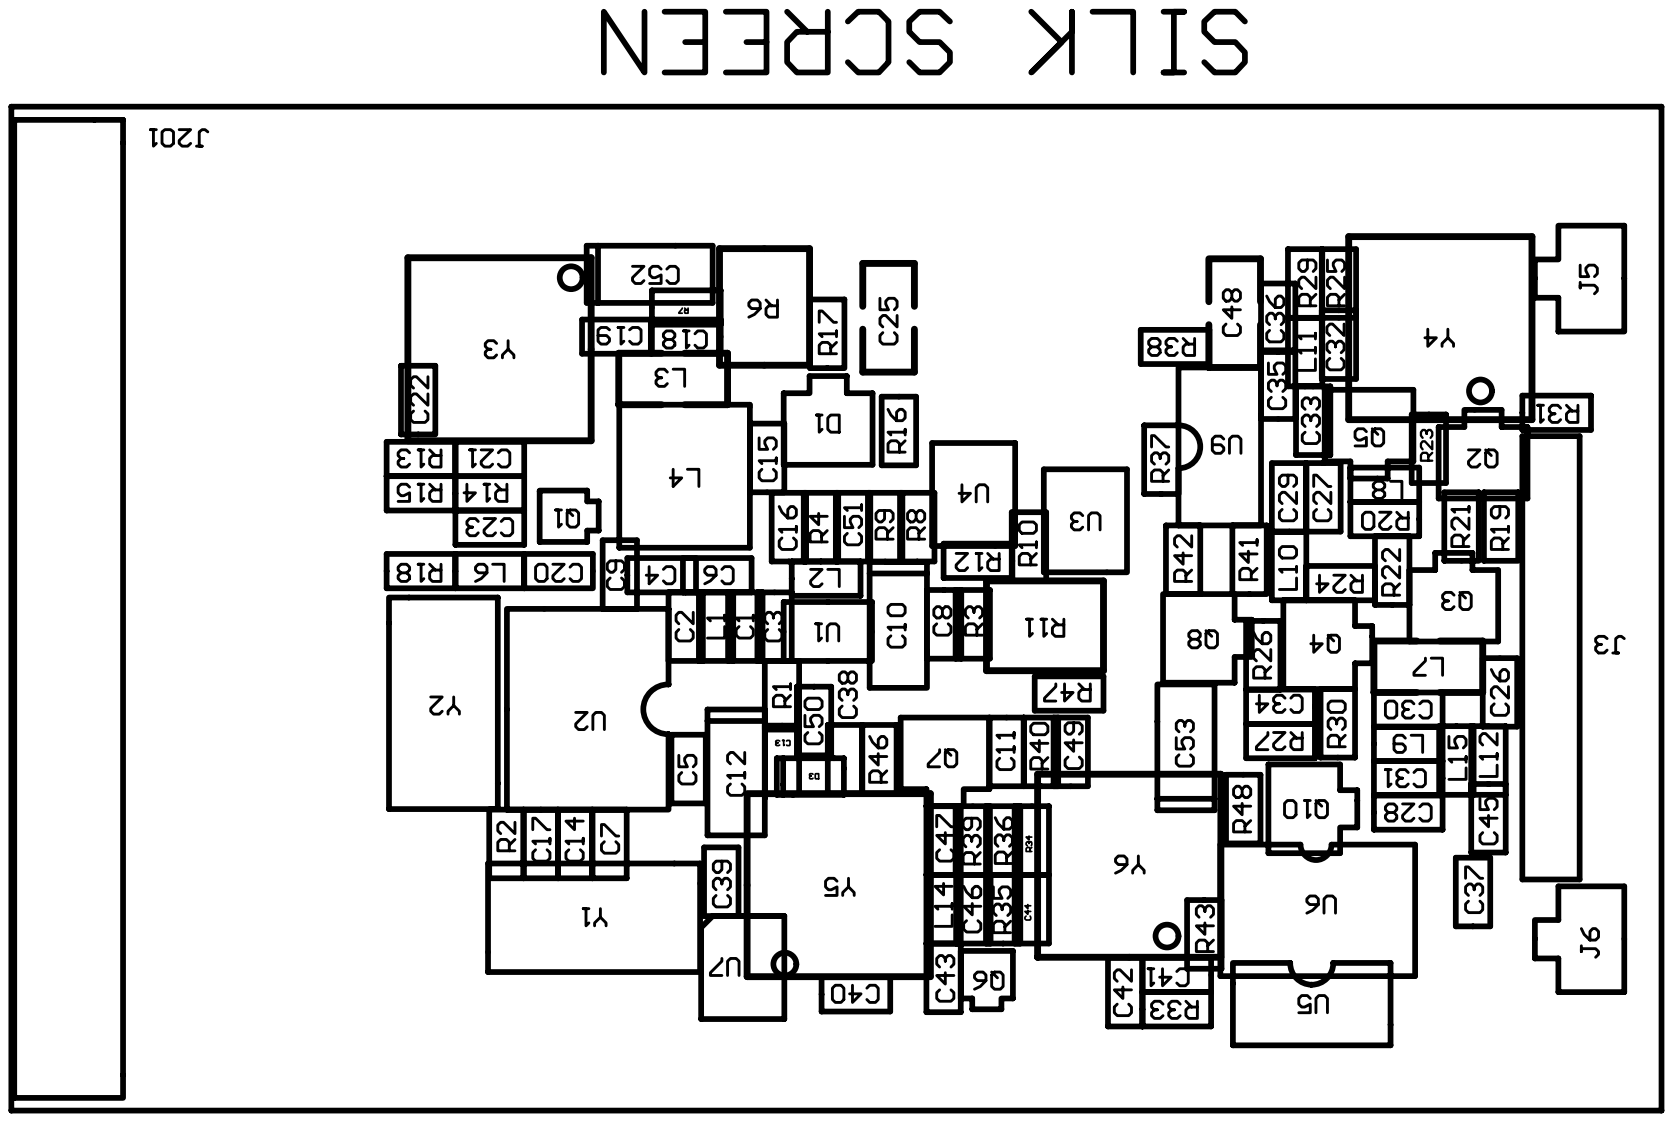
[picture p85: page 1]
