tourajghaffari/tigerfid/protel-files/transceiver/trx-rev19/project-outputs-for-101-rev18/TRX-101R18 Final Artwork Prints.pdf

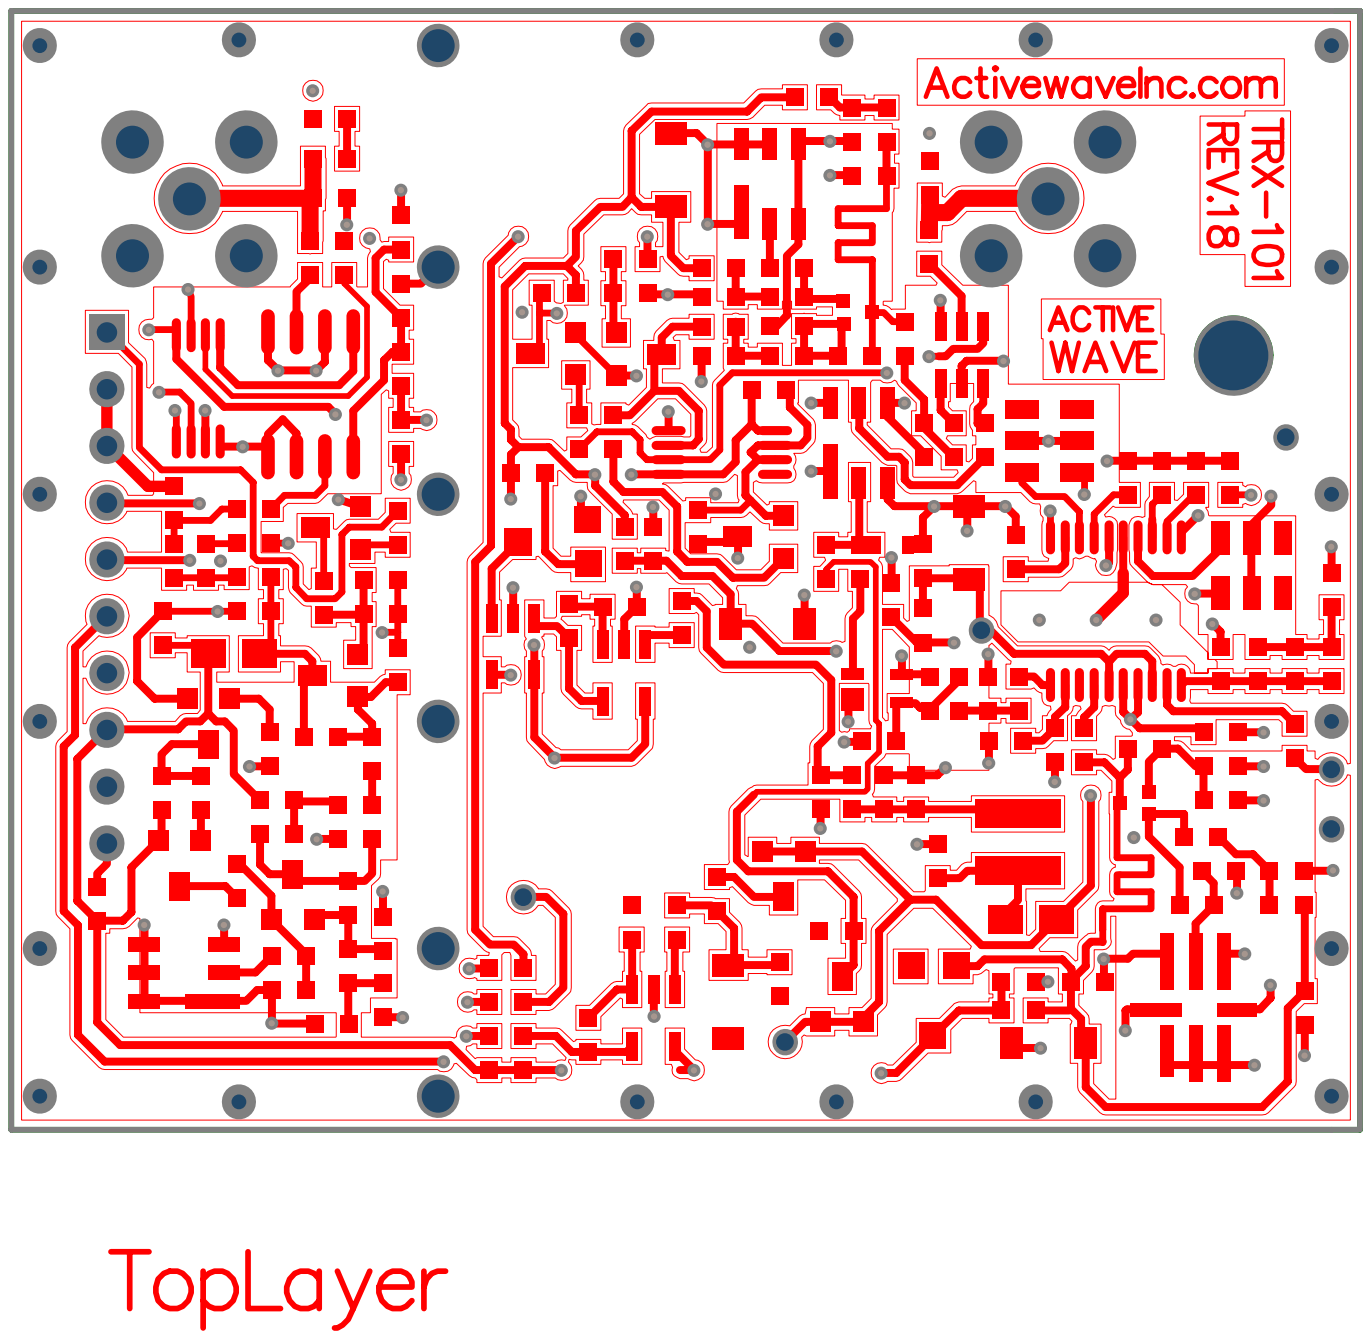
[picture p86: page 1]

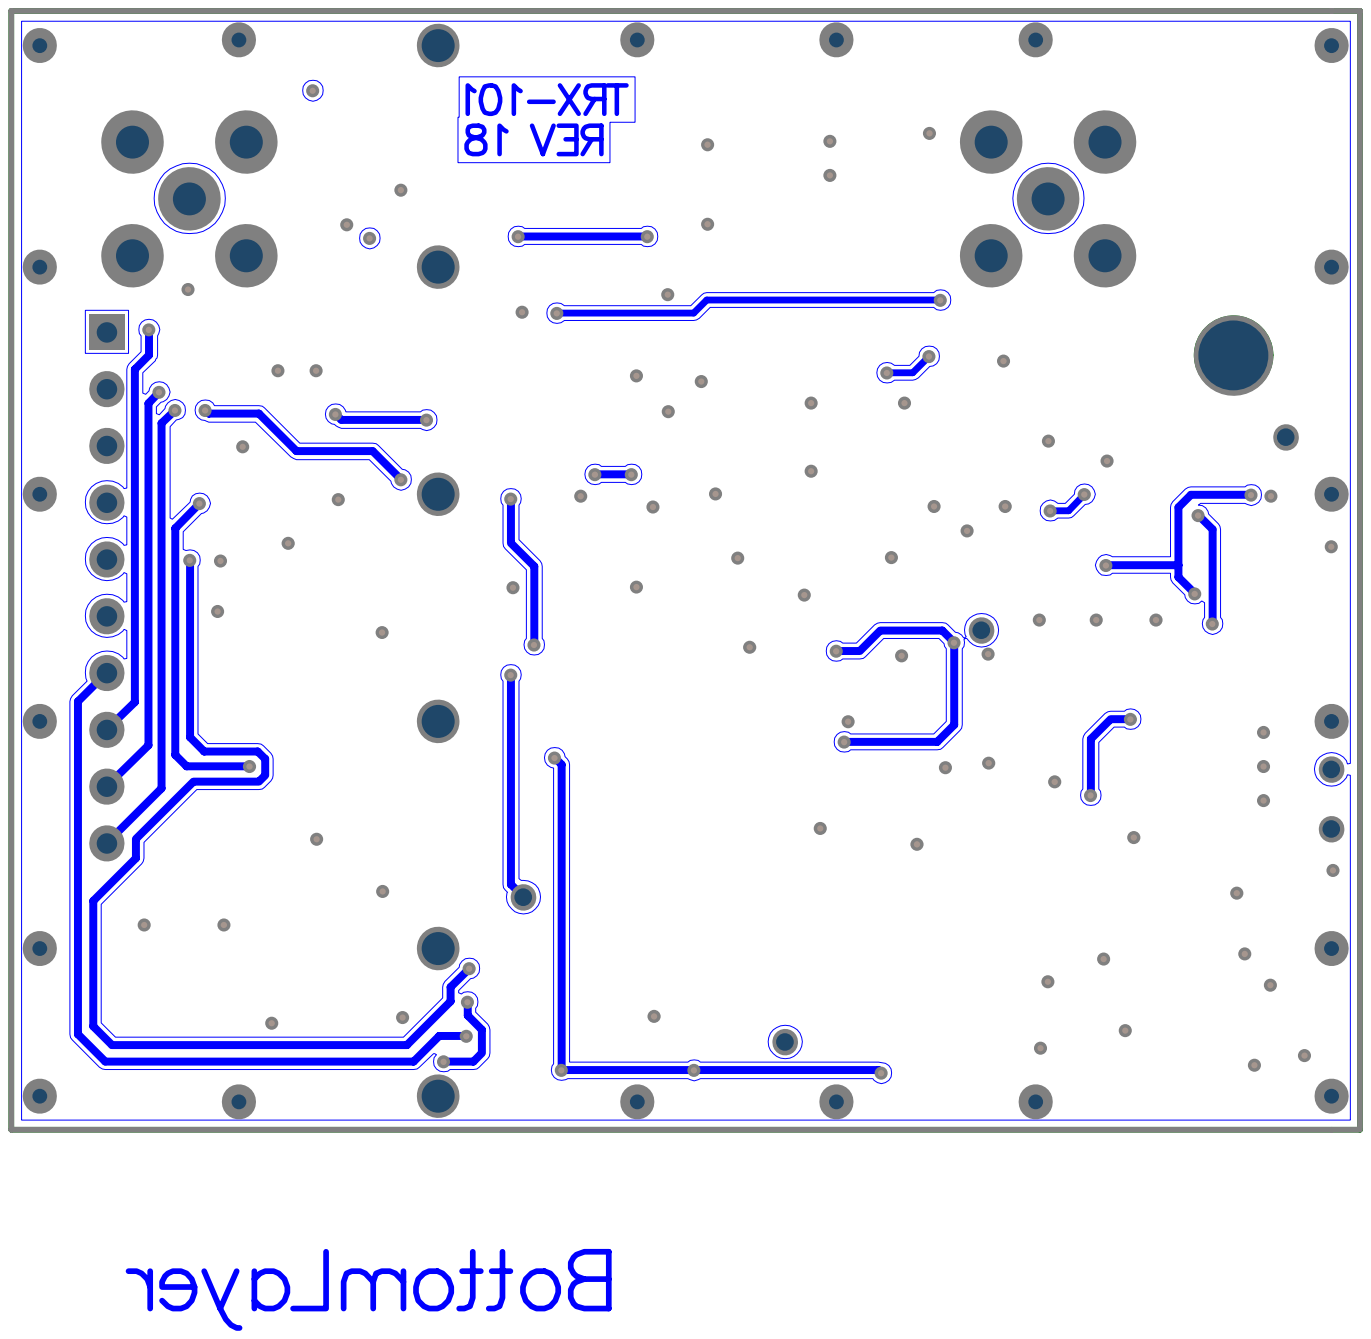
[picture p87: page 2]

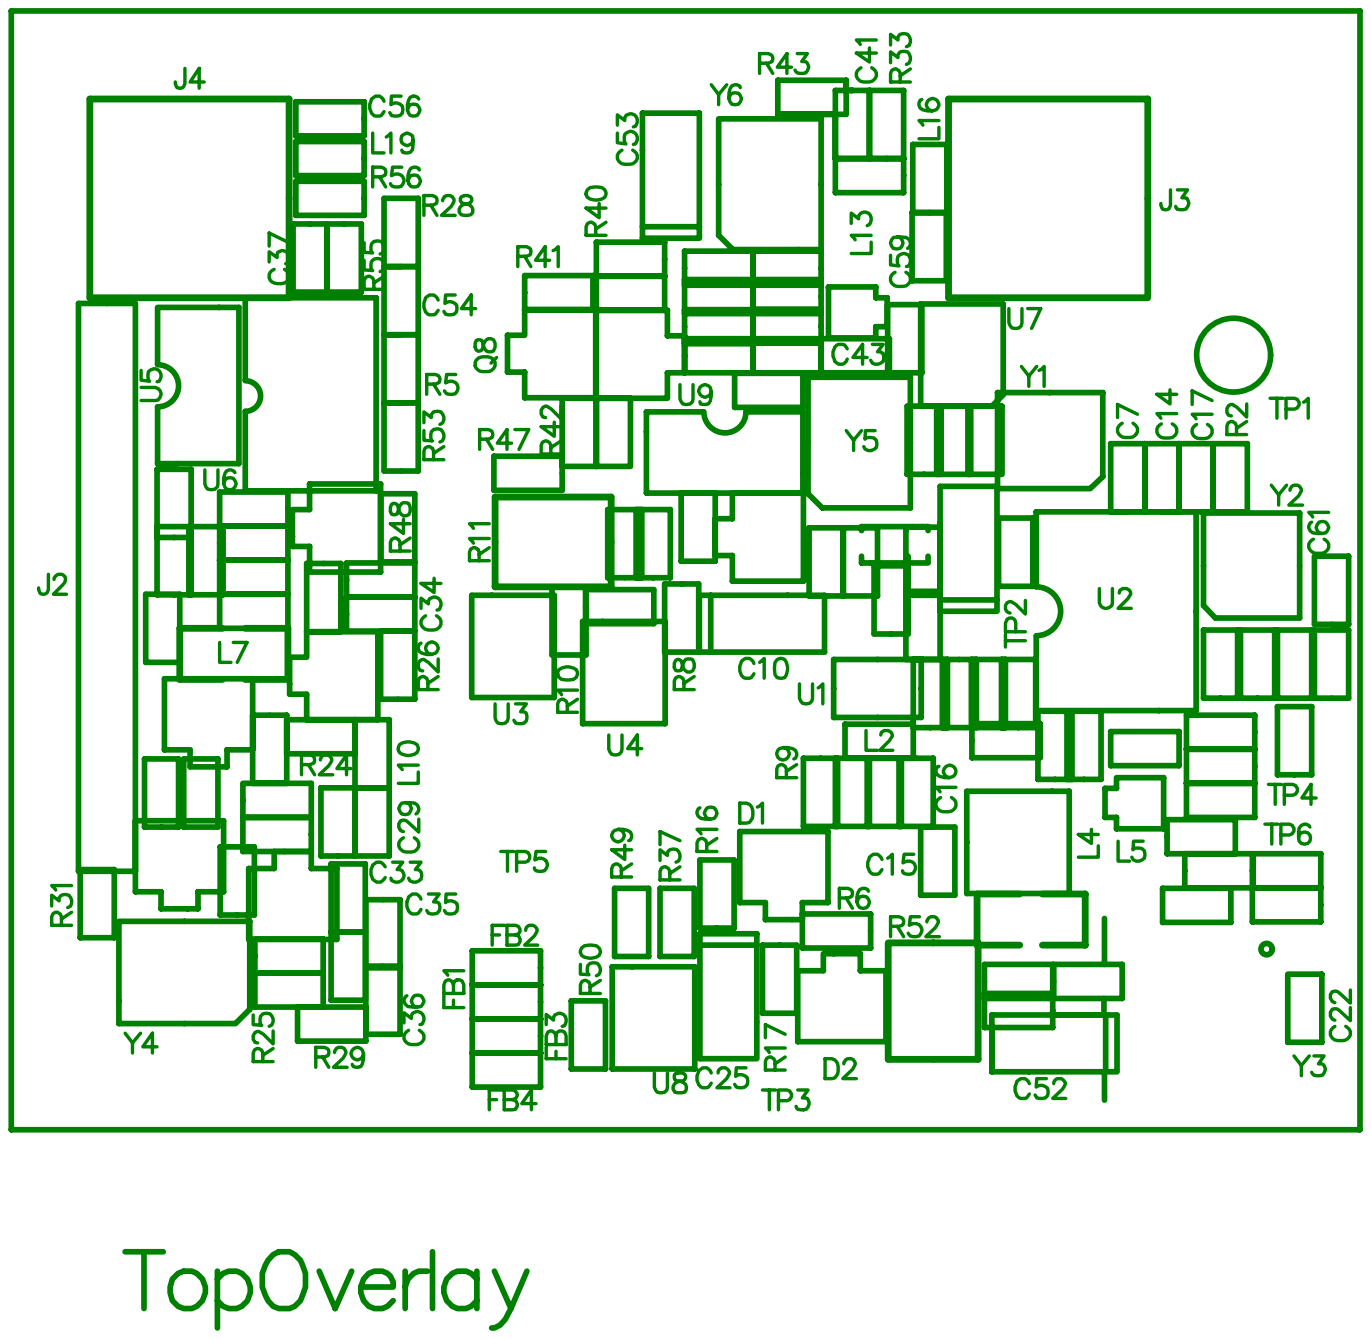
[picture p88: page 3]

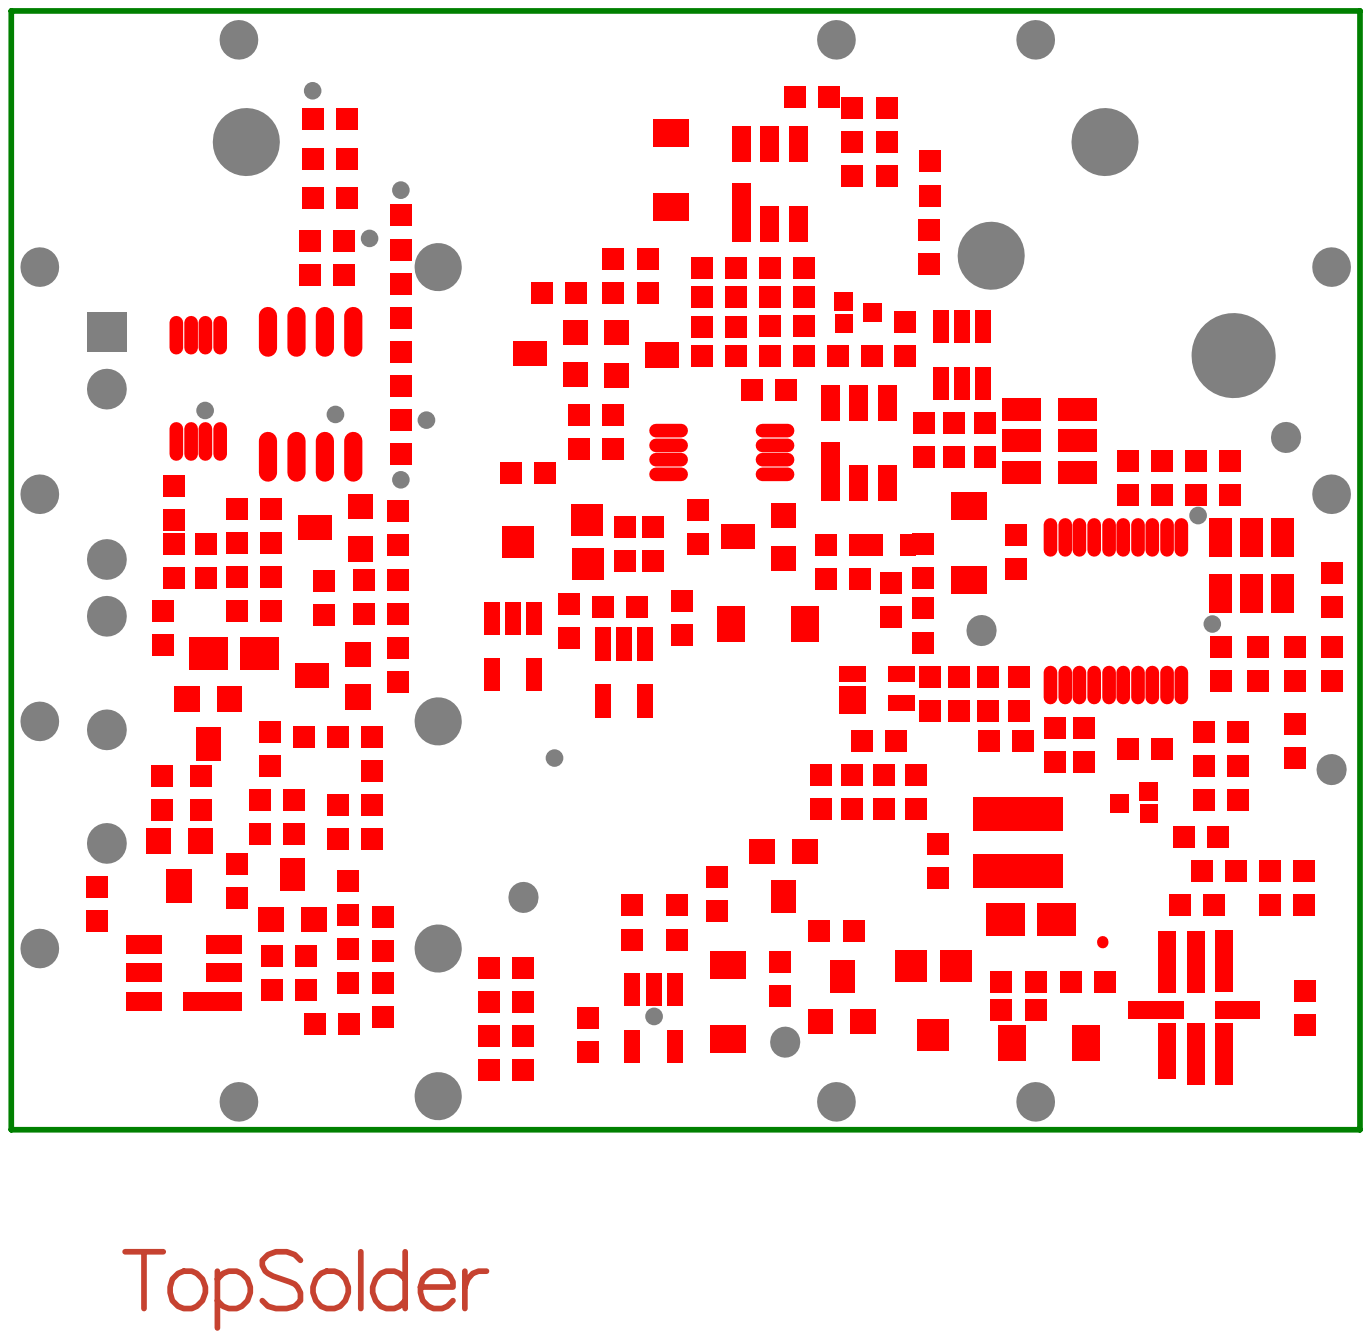
[picture p89: page 5]

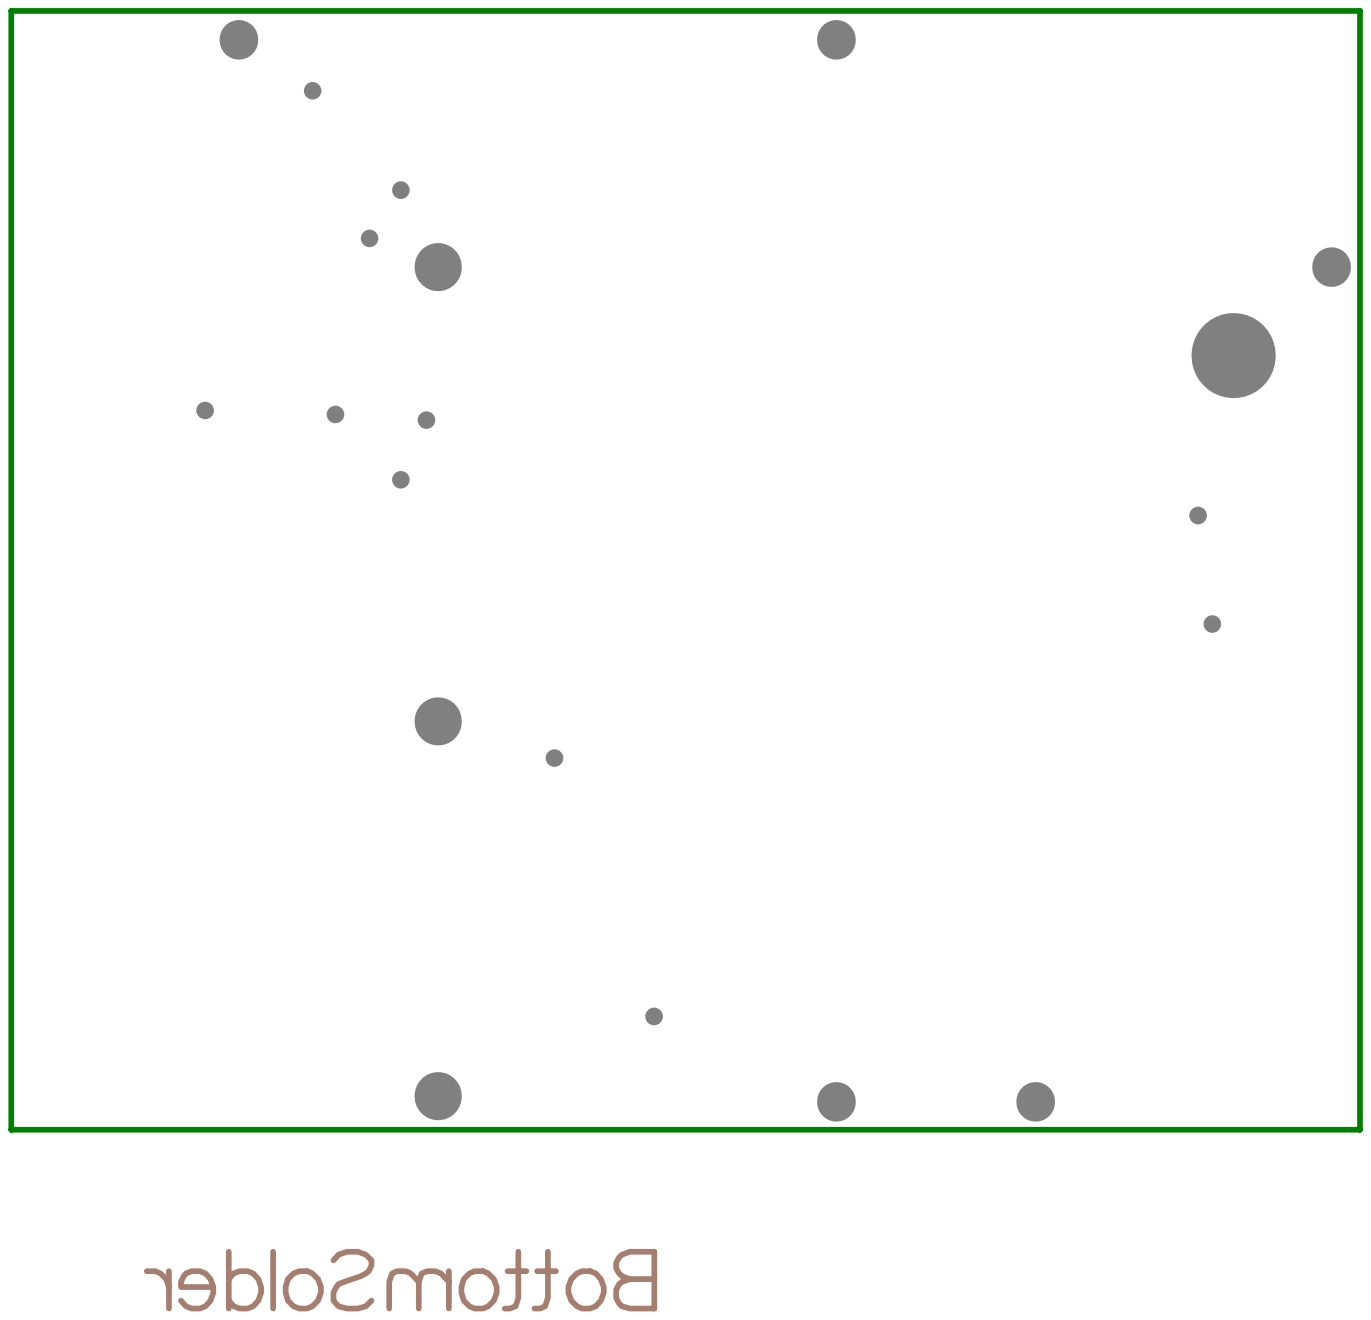
[picture p90: page 6]

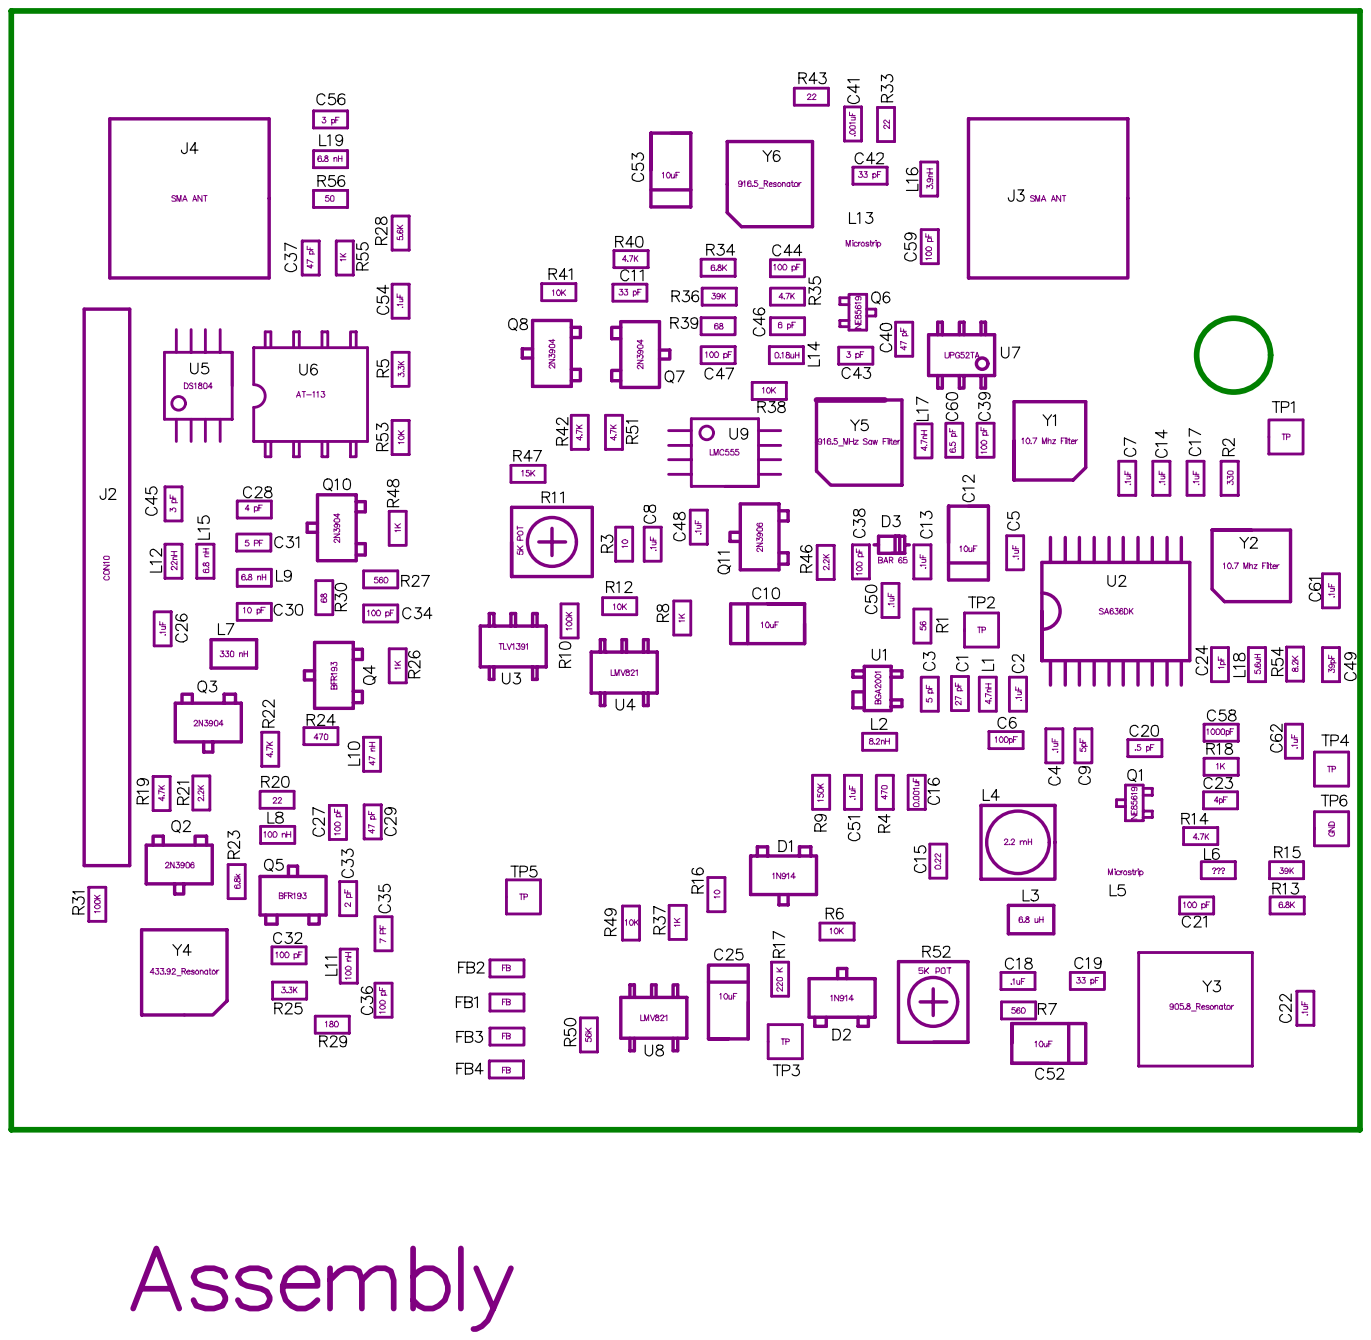
[picture p91: page 7]
