tourajghaffari/tigerfid/protel-files/tags/medium-tag/102-rev17/project-outputs-for-102-rev17/Tag102R17_Assembly Drawing.pdf

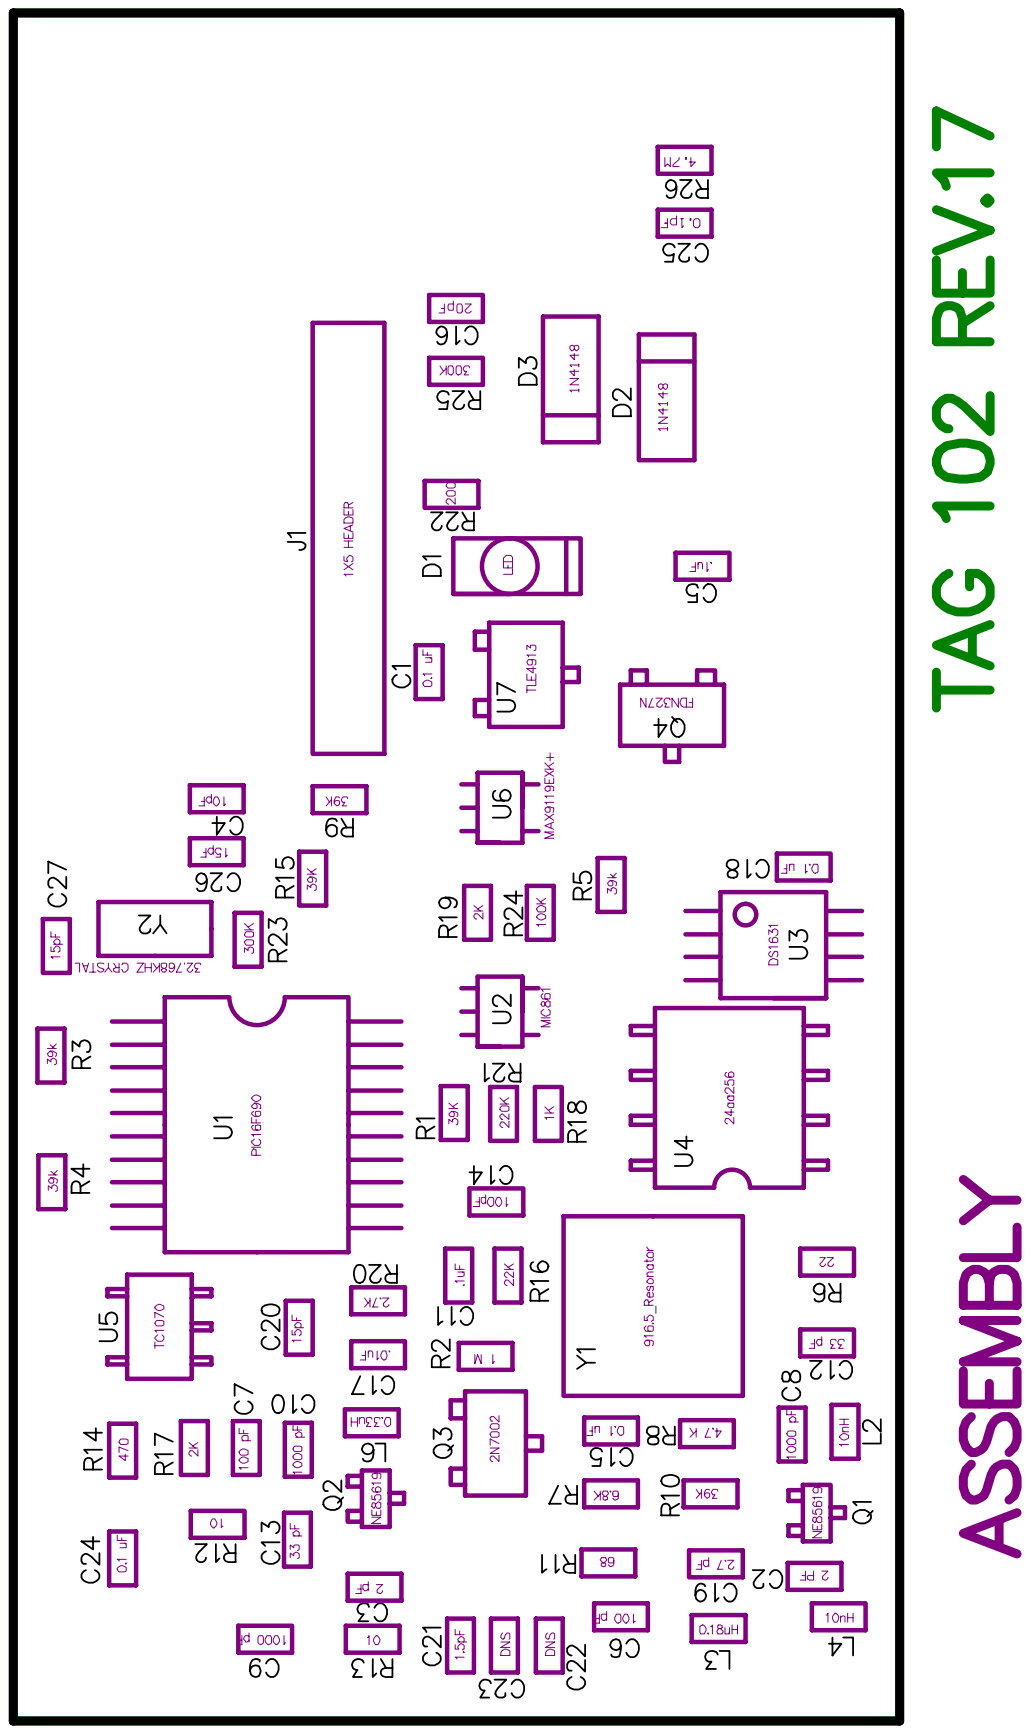
[picture p92: page 1]

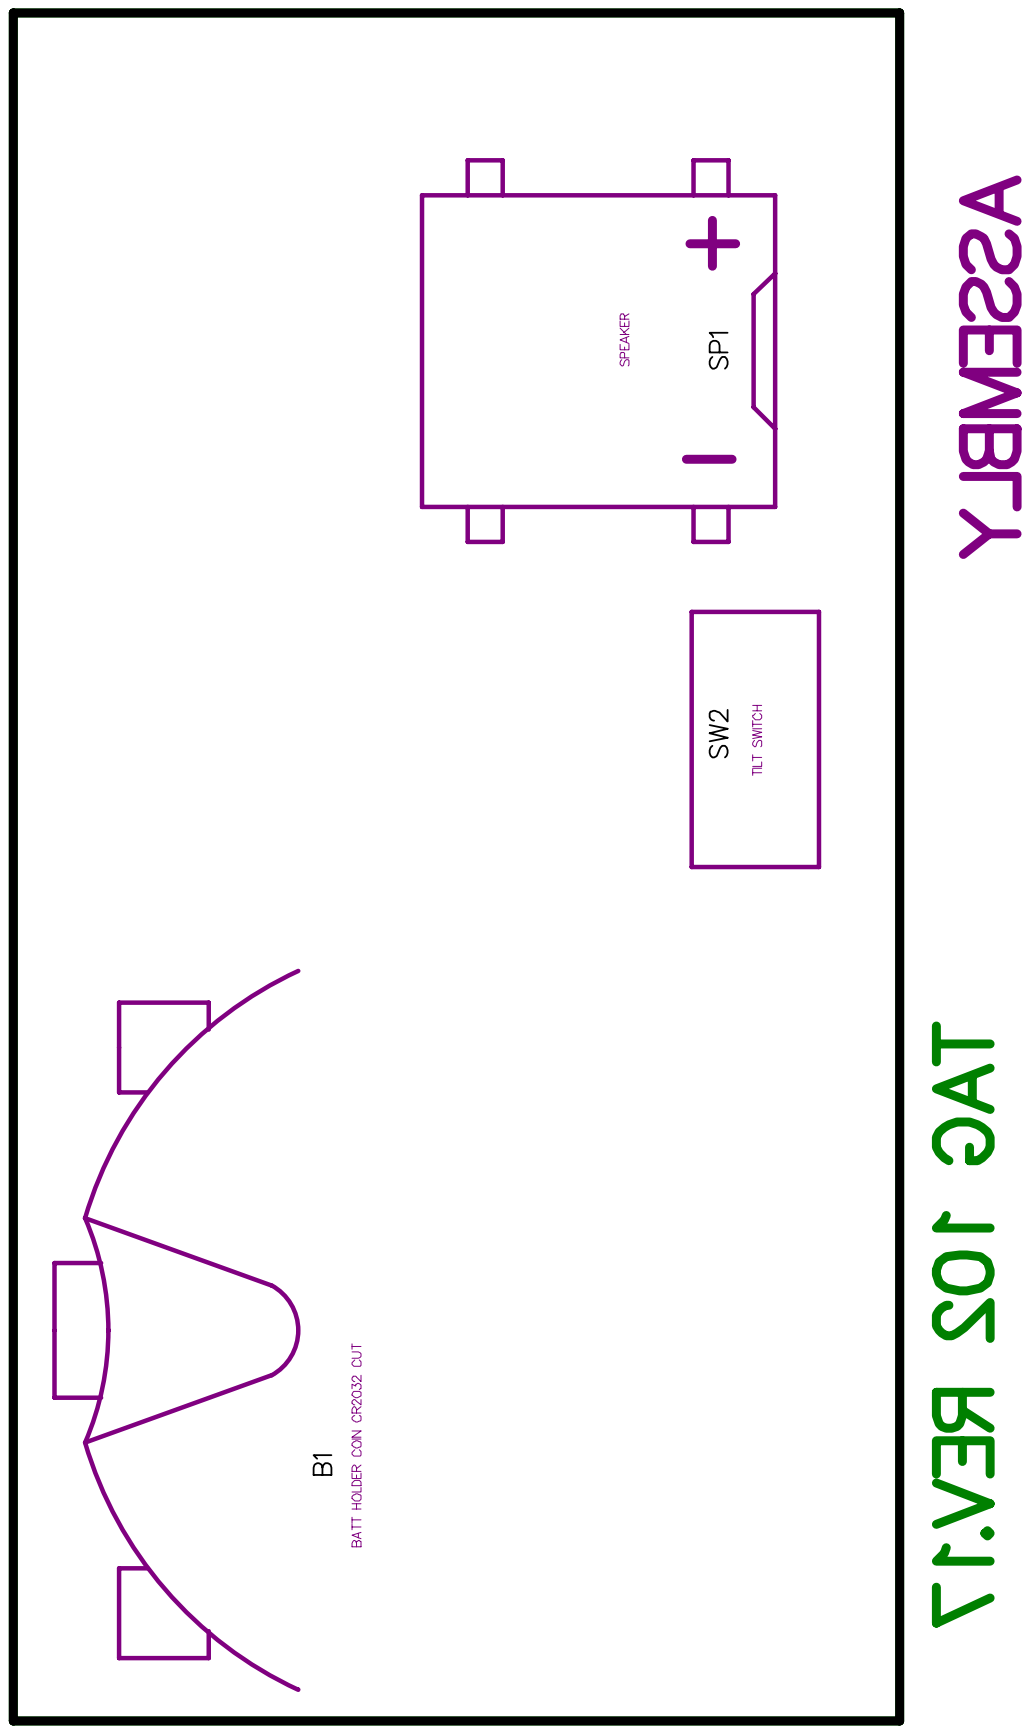
[picture p93: page 2]
