tourajghaffari/tigerfid/software/programming-station/Programing Station 191/Programming Station 191/Rijndael.cpp

//Rijndael.cpp

#include <cstring>
#include <exception>
#include "Rijndael.h"

const int CRijndael::sm_alog[256] =
{
	1, 3, 5, 15, 17, 51, 85, 255, 26, 46, 114, 150, 161, 248, 19, 53, 
	95, 225, 56, 72, 216, 115, 149, 164, 247, 2, 6, 10, 30, 34, 102, 170, 
	229, 52, 92, 228, 55, 89, 235, 38, 106, 190, 217, 112, 144, 171, 230, 49, 
	83, 245, 4, 12, 20, 60, 68, 204, 79, 209, 104, 184, 211, 110, 178, 205, 
	76, 212, 103, 169, 224, 59, 77, 215, 98, 166, 241, 8, 24, 40, 120, 136, 
	131, 158, 185, 208, 107, 189, 220, 127, 129, 152, 179, 206, 73, 219, 118, 154, 
	181, 196, 87, 249, 16, 48, 80, 240, 11, 29, 39, 105, 187, 214, 97, 163, 
	254, 25, 43, 125, 135, 146, 173, 236, 47, 113, 147, 174, 233, 32, 96, 160, 
	251, 22, 58, 78, 210, 109, 183, 194, 93, 231, 50, 86, 250, 21, 63, 65, 
	195, 94, 226, 61, 71, 201, 64, 192, 91, 237, 44, 116, 156, 191, 218, 117, 
	159, 186, 213, 100, 172, 239, 42, 126, 130, 157, 188, 223, 122, 142, 137, 128, 
	155, 182, 193, 88, 232, 35, 101, 175, 234, 37, 111, 177, 200, 67, 197, 84, 
	252, 31, 33, 99, 165, 244, 7, 9, 27, 45, 119, 153, 176, 203, 70, 202, 
	69, 207, 74, 222, 121, 139, 134, 145, 168, 227, 62, 66, 198, 81, 243, 14, 
	18, 54, 90, 238, 41, 123, 141, 140, 143, 138, 133, 148, 167, 242, 13, 23, 
	57, 75, 221, 124, 132, 151, 162, 253, 28, 36, 108, 180, 199, 82, 246, 1
};

const int CRijndael::sm_log[256] =
{
	0, 0, 25, 1, 50, 2, 26, 198, 75, 199, 27, 104, 51, 238, 223, 3, 
	100, 4, 224, 14, 52, 141, 129, 239, 76, 113, 8, 200, 248, 105, 28, 193, 
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
char const* CRijndael::sm_szErrorMsg2 = "Data not multiple of Block Size";

//Null chain
char const* CRijndael::sm_chain0 = "\0\0\0\0\0\0\0\0\0\0\0\0\0\0\0\0\0\0\0\0\0\0\0\0\0\0\0\0\0\0\0\0";

//CONSTRUCTOR
CRijndael::CRijndael() : m_bKeyInit(false)
{
}

//DESTRUCTOR
CRijndael::~CRijndael()
{
}

//Expand a user-supplied key material into a session key.
// key        - The 128/192/256-bit user-key to use.
// chain      - initial chain block for CBC and CFB modes.
// keylength  - 16, 24 or 32 bytes
// blockSize  - The block size in bytes of this Rijndael (16, 24 or 32 bytes).
void CRijndael::MakeKey(char const* key, char const* chain, int keylength, int blockSize)
{
	if(NULL == key)
		//throw exception("Empty key");
           throw ("Empty key");
	if(!(16==keylength || 24==keylength || 32==keylength))
		//throw exception("Incorrect key length");
           throw ("Incorrect key length");
	if(!(16==blockSize || 24==blockSize || 32==blockSize))
		//throw exception("Incorrect block length");
            throw ("Incorrect block length");
	m_keylength = keylength;
	m_blockSize = blockSize;
	//Initialize the chain
	memcpy(m_chain0, chain, m_blockSize);
	memcpy(m_chain, chain, m_blockSize);
	//Calculate Number of Rounds
	switch(m_keylength)
	{
		case 16:
			m_iROUNDS = (m_blockSize == 16) ? 10 : (m_blockSize == 24 ? 12 : 14);
			break;

		case 24:
			m_iROUNDS = (m_blockSize != 32) ? 12 : 14;
			break;

		default: // 32 bytes = 256 bits
			m_iROUNDS = 14;
	}
	int BC = m_blockSize / 4;
	int i, j;
	for(i=0; i<=m_iROUNDS; i++)
	{
		for(j=0; j<BC; j++)
			m_Ke[i][j] = 0;
	}
	for(i=0; i<=m_iROUNDS; i++)
	{
		for(j=0; j<BC; j++)
			m_Kd[i][j] = 0;
	}
	int ROUND_KEY_COUNT = (m_iROUNDS + 1) * BC;
	int KC = m_keylength/4;
	//Copy user material bytes into temporary ints
	int* pi = tk;
	char const* pc = key;
	for(i=0; i<KC; i++)
	{
		*pi = (unsigned char)*(pc++) << 24;
		*pi |= (unsigned char)*(pc++) << 16;
		*pi |= (unsigned char)*(pc++) << 8;
		*(pi++) |= (unsigned char)*(pc++);
	}
	//Copy values into round key arrays
	int t = 0;
	for(j=0; (j<KC)&&(t<ROUND_KEY_COUNT); j++,t++)
	{
		m_Ke[t/BC][t%BC] = tk[j];
		m_Kd[m_iROUNDS - (t/BC)][t%BC] = tk[j];
	}
	int tt, rconpointer = 0;
	while(t < ROUND_KEY_COUNT)
	{
		//Extrapolate using phi (the round key evolution function)
		tt = tk[KC-1];
		tk[0] ^= (sm_S[(tt >> 16) & 0xFF] & 0xFF) << 24 ^
			(sm_S[(tt >>  8) & 0xFF] & 0xFF) << 16 ^
			(sm_S[ tt & 0xFF] & 0xFF) <<  8 ^
			(sm_S[(tt >> 24) & 0xFF] & 0xFF) ^
			(sm_rcon[rconpointer++]  & 0xFF) << 24;
		if(KC != 8)
			for(i=1, j=0; i<KC;)
				tk[i++] ^= tk[j++];
		else
		{
			for(i=1, j=0; i<KC/2; )
				tk[i++] ^= tk[j++];
			tt = tk[KC/2-1];
			tk[KC/2] ^= (sm_S[ tt & 0xFF] & 0xFF) ^
				(sm_S[(tt >>  8) & 0xFF] & 0xFF) <<  8 ^
				(sm_S[(tt >> 16) & 0xFF] & 0xFF) << 16 ^
				(sm_S[(tt >> 24) & 0xFF] & 0xFF) << 24;
			for(j = KC/2, i=j+1; i<KC; )
				tk[i++] ^= tk[j++];
		}
		//Copy values into round key arrays
		for(j=0; (j<KC) && (t<ROUND_KEY_COUNT); j++, t++)
		{
			m_Ke[t/BC][t%BC] = tk[j];
			m_Kd[m_iROUNDS - (t/BC)][t%BC] = tk[j];
		}
	}
	//Inverse MixColumn where needed
	for(int r=1; r<m_iROUNDS; r++)
		for(j=0; j<BC; j++)
		{
			tt = m_Kd[r][j];
			m_Kd[r][j] = sm_U1[(tt >> 24) & 0xFF] ^
				sm_U2[(tt >> 16) & 0xFF] ^
				sm_U3[(tt >>  8) & 0xFF] ^
				sm_U4[tt & 0xFF];
		}
	m_bKeyInit = true;
}

//Convenience method to encrypt exactly one block of plaintext, assuming
//Rijndael's default block size (128-bit).
// in         - The plaintext
// result     - The ciphertext generated from a plaintext using the key
void CRijndael::DefEncryptBlock(char const* in, char* result)
{
	if(false==m_bKeyInit)
		// throw exception(sm_szErrorMsg1);
            throw (sm_szErrorMsg1);
	int* Ker = m_Ke[0];
	int t0 = ((unsigned char)*(in++) << 24);
	t0 |= ((unsigned char)*(in++) << 16);
	t0 |= ((unsigned char)*(in++) << 8);
	(t0 |= (unsigned char)*(in++)) ^= Ker[0];
	int t1 = ((unsigned char)*(in++) << 24);
	t1 |= ((unsigned char)*(in++) << 16);
	t1 |= ((unsigned char)*(in++) << 8);
	(t1 |= (unsigned char)*(in++)) ^= Ker[1];
	int t2 = ((unsigned char)*(in++) << 24);
	t2 |= ((unsigned char)*(in++) << 16);
	t2 |= ((unsigned char)*(in++) << 8);
	(t2 |= (unsigned char)*(in++)) ^= Ker[2];
	int t3 = ((unsigned char)*(in++) << 24);
	t3 |= ((unsigned char)*(in++) << 16);
	t3 |= ((unsigned char)*(in++) << 8);
	(t3 |= (unsigned char)*(in++)) ^= Ker[3];
	int a0, a1, a2, a3;
	//Apply Round Transforms
	for (int r = 1; r < m_iROUNDS; r++)
	{
		Ker = m_Ke[r];
		a0 = (sm_T1[(t0 >> 24) & 0xFF] ^
			sm_T2[(t1 >> 16) & 0xFF] ^
			sm_T3[(t2 >>  8) & 0xFF] ^
			sm_T4[t3 & 0xFF]) ^ Ker[0];
		a1 = (sm_T1[(t1 >> 24) & 0xFF] ^
			sm_T2[(t2 >> 16) & 0xFF] ^
			sm_T3[(t3 >>  8) & 0xFF] ^
			sm_T4[t0 & 0xFF]) ^ Ker[1];
		a2 = (sm_T1[(t2 >> 24) & 0xFF] ^
			sm_T2[(t3 >> 16) & 0xFF] ^
			sm_T3[(t0 >>  8) & 0xFF] ^
			sm_T4[t1 & 0xFF]) ^ Ker[2];
		a3 = (sm_T1[(t3 >> 24) & 0xFF] ^
			sm_T2[(t0 >> 16) & 0xFF] ^
			sm_T3[(t1 >>  8) & 0xFF] ^
			sm_T4[t2 & 0xFF]) ^ Ker[3];
		t0 = a0;
		t1 = a1;
		t2 = a2;
		t3 = a3;
	}
	//Last Round is special
	Ker = m_Ke[m_iROUNDS];
	int tt = Ker[0];
	result[0] = sm_S[(t0 >> 24) & 0xFF] ^ (tt >> 24);
	result[1] = sm_S[(t1 >> 16) & 0xFF] ^ (tt >> 16);
	result[2] = sm_S[(t2 >>  8) & 0xFF] ^ (tt >>  8);
	result[3] = sm_S[t3 & 0xFF] ^ tt;
	tt = Ker[1];
	result[4] = sm_S[(t1 >> 24) & 0xFF] ^ (tt >> 24);
	result[5] = sm_S[(t2 >> 16) & 0xFF] ^ (tt >> 16);
	result[6] = sm_S[(t3 >>  8) & 0xFF] ^ (tt >>  8);
	result[7] = sm_S[t0 & 0xFF] ^ tt;
	tt = Ker[2];
	result[8] = sm_S[(t2 >> 24) & 0xFF] ^ (tt >> 24);
	result[9] = sm_S[(t3 >> 16) & 0xFF] ^ (tt >> 16);
	result[10] = sm_S[(t0 >>  8) & 0xFF] ^ (tt >>  8);
	result[11] = sm_S[t1 & 0xFF] ^ tt;
	tt = Ker[3];
	result[12] = sm_S[(t3 >> 24) & 0xFF] ^ (tt >> 24);
	result[13] = sm_S[(t0 >> 16) & 0xFF] ^ (tt >> 16);
	result[14] = sm_S[(t1 >>  8) & 0xFF] ^ (tt >>  8);
	result[15] = sm_S[t2 & 0xFF] ^ tt;
}

//Convenience method to decrypt exactly one block of plaintext, assuming
//Rijndael's default block size (128-bit).
// in         - The ciphertext.
// result     - The plaintext generated from a ciphertext using the session key.
void CRijndael::DefDecryptBlock(char const* in, char* result)
{
	if(false==m_bKeyInit)
		//throw exception(sm_szErrorMsg1);
           throw (sm_szErrorMsg1);
	int* Kdr = m_Kd[0];
	int t0 = ((unsigned char)*(in++) << 24);
	t0 = t0 | ((unsigned char)*(in++) << 16);
	t0 |= ((unsigned char)*(in++) << 8);
	(t0 |= (unsigned char)*(in++)) ^= Kdr[0];
	int t1 = ((unsigned char)*(in++) << 24);
	t1 |= ((unsigned char)*(in++) << 16);
	t1 |= ((unsigned char)*(in++) << 8);
	(t1 |= (unsigned char)*(in++)) ^= Kdr[1];
	int t2 = ((unsigned char)*(in++) << 24);
	t2 |= ((unsigned char)*(in++) << 16);
	t2 |= ((unsigned char)*(in++) << 8);
	(t2 |= (unsigned char)*(in++)) ^= Kdr[2];
	int t3 = ((unsigned char)*(in++) << 24);
	t3 |= ((unsigned char)*(in++) << 16);
	t3 |= ((unsigned char)*(in++) << 8);
	(t3 |= (unsigned char)*(in++)) ^= Kdr[3];
	int a0, a1, a2, a3;
	for(int r = 1; r < m_iROUNDS; r++) // apply round transforms
	{
		Kdr = m_Kd[r];
		a0 = (sm_T5[(t0 >> 24) & 0xFF] ^
			sm_T6[(t3 >> 16) & 0xFF] ^
			sm_T7[(t2 >>  8) & 0xFF] ^
			sm_T8[ t1        & 0xFF] ) ^ Kdr[0];
		a1 = (sm_T5[(t1 >> 24) & 0xFF] ^
			sm_T6[(t0 >> 16) & 0xFF] ^
			sm_T7[(t3 >>  8) & 0xFF] ^
			sm_T8[ t2        & 0xFF] ) ^ Kdr[1];
		a2 = (sm_T5[(t2 >> 24) & 0xFF] ^
			sm_T6[(t1 >> 16) & 0xFF] ^
			sm_T7[(t0 >>  8) & 0xFF] ^
			sm_T8[ t3        & 0xFF] ) ^ Kdr[2];
		a3 = (sm_T5[(t3 >> 24) & 0xFF] ^
			sm_T6[(t2 >> 16) & 0xFF] ^
			sm_T7[(t1 >>  8) & 0xFF] ^
			sm_T8[ t0        & 0xFF] ) ^ Kdr[3];
		t0 = a0;
		t1 = a1;
		t2 = a2;
		t3 = a3;
	}
	//Last Round is special
	Kdr = m_Kd[m_iROUNDS];
	int tt = Kdr[0];
	result[ 0] = sm_Si[(t0 >> 24) & 0xFF] ^ (tt >> 24);
	result[ 1] = sm_Si[(t3 >> 16) & 0xFF] ^ (tt >> 16);
	result[ 2] = sm_Si[(t2 >>  8) & 0xFF] ^ (tt >>  8);
	result[ 3] = sm_Si[ t1 & 0xFF] ^ tt;
	tt = Kdr[1];
	result[ 4] = sm_Si[(t1 >> 24) & 0xFF] ^ (tt >> 24);
	result[ 5] = sm_Si[(t0 >> 16) & 0xFF] ^ (tt >> 16);
	result[ 6] = sm_Si[(t3 >>  8) & 0xFF] ^ (tt >>  8);
	result[ 7] = sm_Si[ t2 & 0xFF] ^ tt;
	tt = Kdr[2];
	result[ 8] = sm_Si[(t2 >> 24) & 0xFF] ^ (tt >> 24);
	result[ 9] = sm_Si[(t1 >> 16) & 0xFF] ^ (tt >> 16);
	result[10] = sm_Si[(t0 >>  8) & 0xFF] ^ (tt >>  8);
	result[11] = sm_Si[ t3 & 0xFF] ^ tt;
	tt = Kdr[3];
	result[12] = sm_Si[(t3 >> 24) & 0xFF] ^ (tt >> 24);
	result[13] = sm_Si[(t2 >> 16) & 0xFF] ^ (tt >> 16);
	result[14] = sm_Si[(t1 >>  8) & 0xFF] ^ (tt >>  8);
	result[15] = sm_Si[ t0 & 0xFF] ^ tt;
}

//Encrypt exactly one block of plaintext.
// in           - The plaintext.
// result       - The ciphertext generated from a plaintext using the key.
void CRijndael::EncryptBlock(char const* in, char* result)
{
	if(false==m_bKeyInit)
		//throw exception(sm_szErrorMsg1);
            throw (sm_szErrorMsg1);
    if(DEFAULT_BLOCK_SIZE == m_blockSize)
	{
		DefEncryptBlock(in, result);
		return;
	}
	int BC = m_blockSize / 4;
	int SC = (BC == 4) ? 0 : (BC == 6 ? 1 : 2);
	int s1 = sm_shifts[SC][1][0];
	int s2 = sm_shifts[SC][2][0];
	int s3 = sm_shifts[SC][3][0];
	//Temporary Work Arrays
	int i;
	int tt;
	int* pi = t;
	for(i=0; i<BC; i++)
	{
		*pi = ((unsigned char)*(in++) << 24);
		*pi |= ((unsigned char)*(in++) << 16);
		*pi |= ((unsigned char)*(in++) << 8);
		(*(pi++) |= (unsigned char)*(in++)) ^= m_Ke[0][i];
	}
	//Apply Round Transforms
	for(int r=1; r<m_iROUNDS; r++)
	{
		for(i=0; i<BC; i++)
			a[i] = (sm_T1[(t[i] >> 24) & 0xFF] ^
				sm_T2[(t[(i + s1) % BC] >> 16) & 0xFF] ^
				sm_T3[(t[(i + s2) % BC] >>  8) & 0xFF] ^
				sm_T4[ t[(i + s3) % BC] & 0xFF] ) ^ m_Ke[r][i];
		memcpy(t, a, 4*BC);
	}
	int j;
	//Last Round is Special
	for(i=0,j=0; i<BC; i++)
	{
		tt = m_Ke[m_iROUNDS][i];
		result[j++] = sm_S[(t[i] >> 24) & 0xFF] ^ (tt >> 24);
		result[j++] = sm_S[(t[(i + s1) % BC] >> 16) & 0xFF] ^ (tt >> 16);
		result[j++] = sm_S[(t[(i + s2) % BC] >>  8) & 0xFF] ^ (tt >>  8);
		result[j++] = sm_S[ t[(i + s3) % BC] & 0xFF] ^ tt;
	}
}

//Decrypt exactly one block of ciphertext.
// in         - The ciphertext.
// result     - The plaintext generated from a ciphertext using the session key.
void CRijndael::DecryptBlock(char const* in, char* result)
{
	if(false==m_bKeyInit)
		//throw exception(sm_szErrorMsg1);
            throw (sm_szErrorMsg1);
	if(DEFAULT_BLOCK_SIZE == m_blockSize)
	{
		DefDecryptBlock(in, result);
		return;
	}
	int BC = m_blockSize / 4;
	int SC = BC == 4 ? 0 : (BC == 6 ? 1 : 2);
	int s1 = sm_shifts[SC][1][1];
	int s2 = sm_shifts[SC][2][1];
	int s3 = sm_shifts[SC][3][1];
	//Temporary Work Arrays
	int i;
	int tt;
	int* pi = t;
	for(i=0; i<BC; i++)
	{
		*pi = ((unsigned char)*(in++) << 24);
		*pi |= ((unsigned char)*(in++) << 16);
		*pi |= ((unsigned char)*(in++) << 8);
		(*(pi++) |= (unsigned char)*(in++)) ^= m_Kd[0][i];
	}
	//Apply Round Transforms
	for(int r=1; r<m_iROUNDS; r++)
	{
		for(i=0; i<BC; i++)
			a[i] = (sm_T5[(t[i] >> 24) & 0xFF] ^
				sm_T6[(t[(i + s1) % BC] >> 16) & 0xFF] ^
				sm_T7[(t[(i + s2) % BC] >>  8) & 0xFF] ^
				sm_T8[ t[(i + s3) % BC] & 0xFF]) ^ m_Kd[r][i];
		memcpy(t, a, 4*BC);
	}
	int j;
	//Last Round is Special
	for(i=0,j=0; i<BC; i++)
	{
		tt = m_Kd[m_iROUNDS][i];
		result[j++] = sm_Si[(t[i] >> 24) & 0xFF] ^ (tt >> 24);
		result[j++] = sm_Si[(t[(i + s1) % BC] >> 16) & 0xFF] ^ (tt >> 16);
		result[j++] = sm_Si[(t[(i + s2) % BC] >>  8) & 0xFF] ^ (tt >>  8);
		result[j++] = sm_Si[ t[(i + s3) % BC] & 0xFF] ^ tt;
	}
}

void CRijndael::Encrypt(char const* in, char* result, size_t n, int iMode)
{
	if(false==m_bKeyInit)
		//throw exception(sm_szErrorMsg1);
            throw (sm_szErrorMsg1);
	//n should be > 0 and multiple of m_blockSize
	if(0==n || n%m_blockSize!=0)
		//throw exception(sm_szErrorMsg2);
            throw (sm_szErrorMsg2);
	int i;
	char const* pin;
	char* presult;
	if(CBC == iMode) //CBC mode, using the Chain
	{
		for(i=0,pin=in,presult=result; i<n/m_blockSize; i++)
		{
			Xor(m_chain, pin);
			EncryptBlock(m_chain, presult);
			memcpy(m_chain, presult, m_blockSize);
			pin += m_blockSize;
			presult += m_blockSize;
		}
	}
	else if(CFB == iMode) //CFB mode, using the Chain
	{
		for(i=0,pin=in,presult=result; i<n/m_blockSize; i++)
		{
			EncryptBlock(m_chain, presult);
			Xor(presult, pin);
			memcpy(m_chain, presult, m_blockSize);
			pin += m_blockSize;
			presult += m_blockSize;
		}
	}
	else //ECB mode, not using the Chain
	{
		for(i=0,pin=in,presult=result; i<n/m_blockSize; i++)
		{
			EncryptBlock(pin, presult);
			pin += m_blockSize;
			presult += m_blockSize;
		}
	}
}

void CRijndael::Decrypt(char const* in, char* result, size_t n, int iMode)
{
	if(false==m_bKeyInit)
		//throw exception(sm_szErrorMsg1);
            throw (sm_szErrorMsg1);
	//n should be > 0 and multiple of m_blockSize
	if(0==n || n%m_blockSize!=0)
		//throw exception(sm_szErrorMsg2);
            throw (sm_szErrorMsg2);
	int i;
	char const* pin;
	char* presult;
	if(CBC == iMode) //CBC mode, using the Chain
	{
		for(i=0,pin=in,presult=result; i<n/m_blockSize; i++)
		{
			DecryptBlock(pin, presult);
			Xor(presult, m_chain);
			memcpy(m_chain, pin, m_blockSize);				
			pin += m_blockSize;
			presult += m_blockSize;
		}
	}
	else if(CFB == iMode) //CFB mode, using the Chain, not using Decrypt()
	{
		for(i=0,pin=in,presult=result; i<n/m_blockSize; i++)
		{
			EncryptBlock(m_chain, presult);
			//memcpy(presult, pin, m_blockSize);
			Xor(presult, pin);
			memcpy(m_chain, pin, m_blockSize);
			pin += m_blockSize;
			presult += m_blockSize;
		}
	}
	else //ECB mode, not using the Chain
	{
		for(i=0,pin=in,presult=result; i<n/m_blockSize; i++)
		{
			DecryptBlock(pin, presult);
			pin += m_blockSize;
			presult += m_blockSize;
		}
	}
}
